jeffmhopkins/Woody/docs/research/2026-09-26-finger-spacing/README.md

# Finger-key spacing — research, 2026-09-26

> **Historical record** (CLAUDE.md §6): what was found on this date, with its
> sources. Not corrected later. The layout it fed is `layout.lh_gaps` /
> `rh_gaps` in `config/body.yaml`.

**Question:** the 11 top keys run in one straight line (LH 5 upper, RH 6
lower), played with the finger pads. The provisional pitch was 24 mm; the
owner says they need to be closer. What do real instruments and hands say?

**Answer:** pad-played instruments put adjacent holes **~20–23 mm** apart
(soprano recorder), adults play down to **16–17 mm** (sopranino), and finger
pad widths put touching fingers **~15–22 mm** apart centre to centre (P5 woman
to P95 man). 24 mm is at the wide end; **19–21 mm** within a hand is the
evidence-backed target, tighter toward ring/little, with the widest gap
between the hands.

## Instrument hole centre spacings (mm)

Recorder numbering: L1–L3 left index/middle/ring, R1–R4 right index/middle/ring/little.
Differences computed from published positions `[calc]`.

| Instrument | L1–L2 | L2–L3 | L3–R1 | R1–R2 | R2–R3 | R3–R4 | Source |
|---|---|---|---|---|---|---|---|
| Sopranino recorder, Haka | 15.7 | 16.8 | 16.7 | 16.5 | 17.0 | 16.8 | [1] |
| Soprano recorder, Wijne (Morgan drawing) | 21.0 | 22.3 | 23.6 | 20.8 | 20.1 | 18.0 | [1] |
| Soprano, Wijne copy a-415 | 21.0 | 23.0 | 22.5 | 22.0 | 20.0 | — | [1] |
| Alto recorder, Bressan "a-" | 28.8 | 34.7 | 39.8 | 31.2 | 30.0 | — | [2] |
| Tin whistle D (Gonzato) | 20 | 20 | 27 | 18 | 26 | — | [3] |
| Whistle C (Gonzato) | 22 | 26 | 24 | 19 | 26 | — | [3] |
| Alto whistle G (Gonzato) | 26 | 30 | 39 | 24 | 36 | — | [3] |
| Boehm flute RH F#–F–E | — | — | — | 28.2 | 29.9 | — | [4] |

Not found: clarinet, alto sax, bagpipe chanter tables; any EWI / Aerophone /
Sylphyo / Travel Sax key pitch (Roland's AE-20/AE-30 spacing article [8] was
403 to the tools — the one real source; open it in a browser). Overall
lengths only: EWI 5000 676 mm [5], EWI USB ~587 mm [6], AE-10 574 mm [7],
Travel Sax 2 230 mm [9].

## Finger breadth (mm), Greiner 1991 US Army [12]

P5/P95 computed as mean ± 1.645 SD `[calc]`. DIP ≈ at the pad.

| | Women P5 / P50 / P95 | Men P5 / P50 / P95 |
|---|---|---|
| Index PIP | 17.8 / 19.9 / 22.0 | 20.4 / 23.0 / 25.6 |
| Index DIP | 15.3 / 17.3 / 19.3 | 17.6 / 20.1 / 22.6 |
| Middle DIP | 15.3 / 17.1 / 18.9 | 17.5 / 19.8 / 22.1 |
| Ring DIP | 14.0 / 15.8 / 17.6 | 16.2 / 18.5 / 20.8 |
| Little DIP | 12.9 / 14.7 / 16.5 | 15.3 / 17.4 / 19.5 |

Cross-check: FAA index PIP breadth men 19/21/23, women 16/18/21 [13]; hand
breadth men 84/90/98, women 73/79/86 [14]. Touching pads, centre to centre =
(w1 + w2)/2 `[calc]`: index–middle 15.3 (P5 F) … 22.4 (P95 M); ring–little
13.5 … 20.2. **Relaxed, curved fingertip spacing is unmeasured** in anything
found (Garrett AMRL-TR-69-42 may have it; DTIC 403).

## Makers' guidance

- Yamaha: holes are "not at regular intervals… the space between holes covered by the middle finger and the ring finger is also minimized" [15].
- Von Huene ergonomic recorders add keys to reduce the first-to-last spread and the right index–middle spacing [16].
- The gap between the hands is usually the largest; the right hand's little-finger hole is usually the tightest, and makers offset little/ring holes sideways rather than stretch them — which a single straight line cannot do, so there the pitch must shrink instead.

## Sources

1. Bouterse, FoMRHI Comm. 2115 — https://www.fomrhi.org/uploads/bulletins/Fomrhi-146/Comm%202115.pdf
2. Bouterse, FoMRHI Comm. 1929 Table 3 — https://www.fomrhi.org/uploads/bulletins/Fomrhi-118/Comm%201929.pdf
3. Gonzato, The Low-Tech Whistle pp. 11–13 — https://www.flutopedia.com/refs/Gonzato_2015_LowTechWhistle.pdf
4. Boehm scale — https://www.rwdobson.com/scales/boehm.html
5. https://www.thomannmusic.com/akai_professional_ewi_5000.htm
6. https://www.manualslib.com/manual/207345/Akai-Ewi-Usb.html?page=29 (search summary only)
7. https://www.roland.com/us/products/aerophone_ae-10/specifications/
8. https://support.roland.com/hc/en-us/articles/4414507338139 (403)
9. https://odiseimusic.com/en-us/pages/travel-sax
10. https://downloads.aodyo.com/sylphyo/sylphyo-userguide-en.pdf
11. http://www.mjbauer.biz/Build_the_REMI_mk2.htm
12. Greiner 1991 — https://archive.org/details/DTIC_ADA244533
13. FAA HFDS App. B — https://hf.tc.faa.gov/hfds/download-hfds/hfds_pdfs/App_B_Tech_Ops_Anthropometrics.pdf
14. FAA HFDS Ch. 14 — https://hf.tc.faa.gov/hfds/download-hfds/hfds_pdfs/Ch14_Anthropometry_and_biomechanics_Oct2009.pdf
15. https://www.yamaha.com/en/musical_instrument_guide/recorder/mechanism/mechanism002.html
16. https://www.vonhuene.com/c-49-ergonomic-or-comfort.aspx
17. https://recorderforum.com/forum/topic/distance-between-holes-plastic-altos/

Gathered by a research agent; figures are as reported with the URL beside
them and were not re-fetched by hand.
