jeffmhopkins/Woody/hardware/cluster/key-switch-network/notes.md

# Key switch network — decision history

**Past tense only.** Every live value lives in `key-switch-network.md`,
[`../cluster-boards.md`](../cluster-boards.md) or `hardware/bom.csv`. If a
number here is still true, it is in the wrong file.

This is the circuit's superseded shelf, on the convention
[`../../module/pitch-stage/notes.md`](../../module/pitch-stage/notes.md) sets.
Nothing is deleted from it: a deleted superseded value stops warning the next
person.

---

## Why `R-KEY-PU` became 2.2 kΩ — moved from the BOM row, 2026-09-26

*Moved out of the `R-KEY-PU` notes cell under CLAUDE.md's cut line: a BOM
cell tells a builder what to do, and this is what someone used to think.*
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
