jeffmhopkins/Woody/branding/export/png/scs-mark-black.png

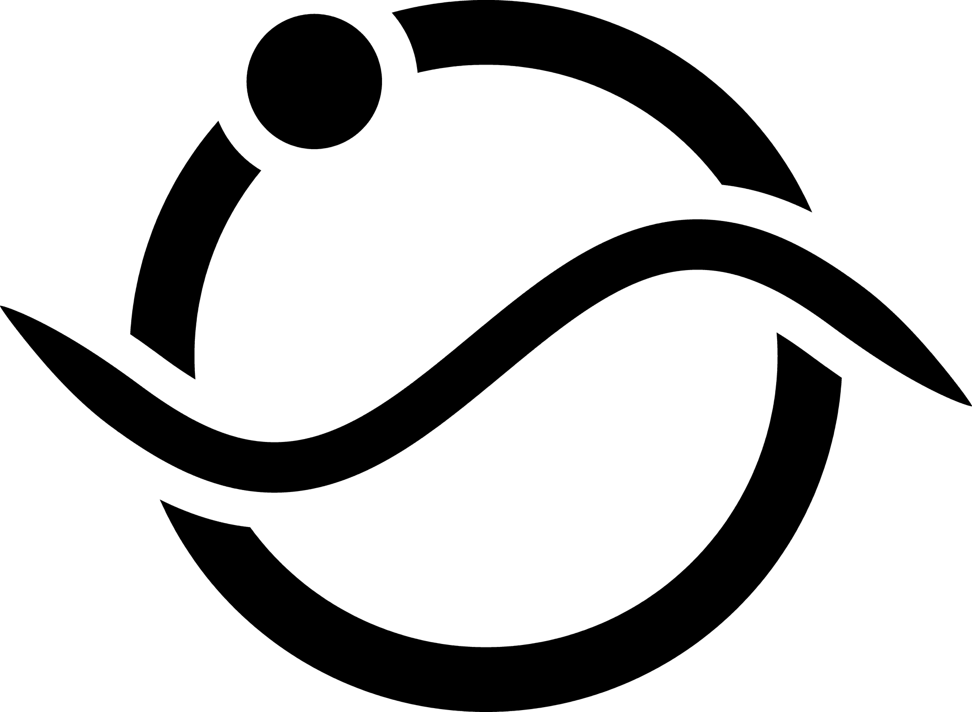
branding/export/png/scs-mark-black.png
