jeffmhopkins/Woody/branding/export/png/scs-mark-white.png

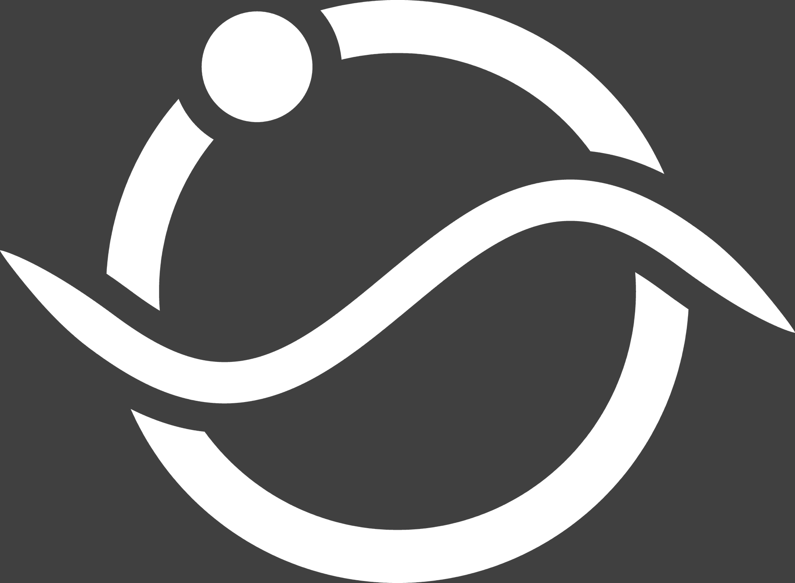
branding/export/png/scs-mark-white.png
