jeffmhopkins/Woody/branding/export/renders/scs-mark-epoxy-on-dark-oak.png

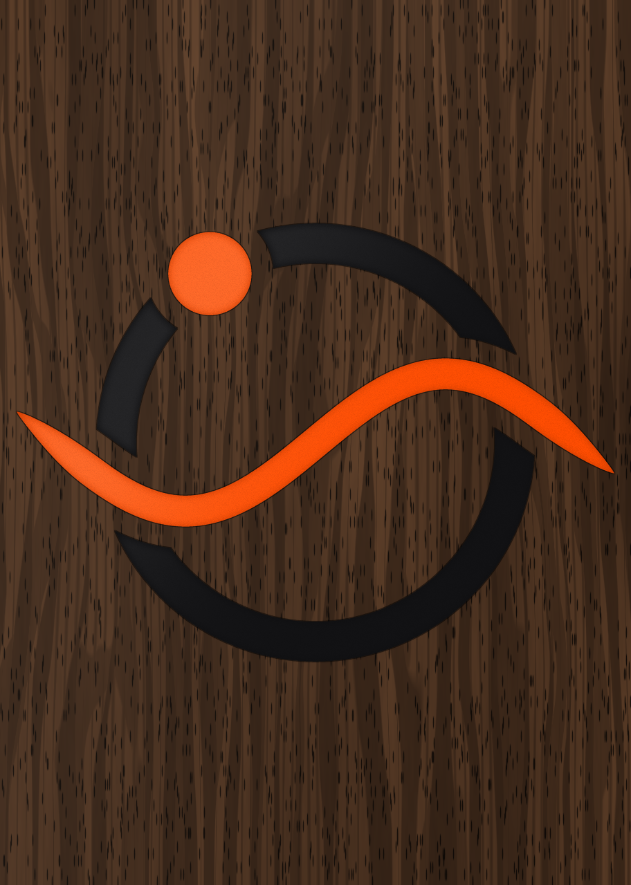
branding/export/renders/scs-mark-epoxy-on-dark-oak.png
