jeffmhopkins/Woody/branding/export/renders/scs-mark-epoxy-on-dark-walnut.png

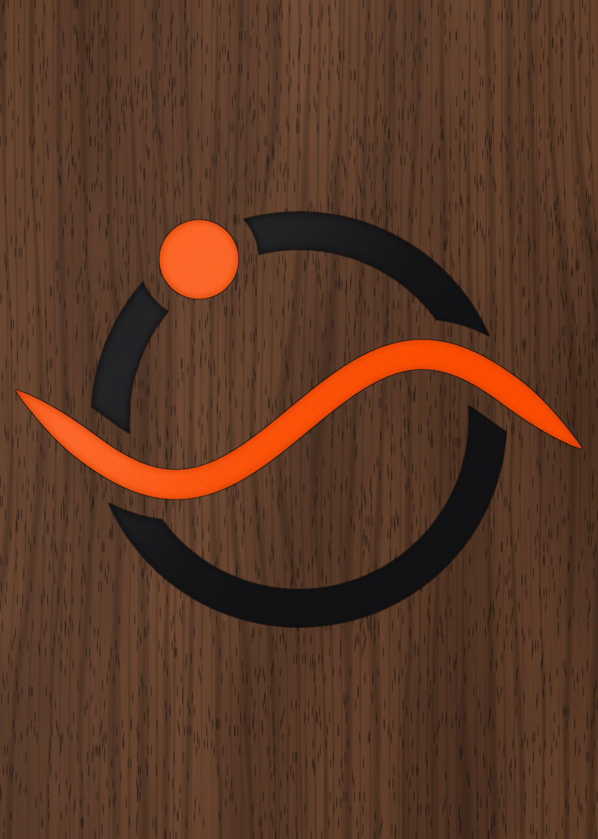
branding/export/renders/scs-mark-epoxy-on-dark-walnut.png
