jeffmhopkins/Woody/branding/export/renders/scs-mark-on-bocote.png

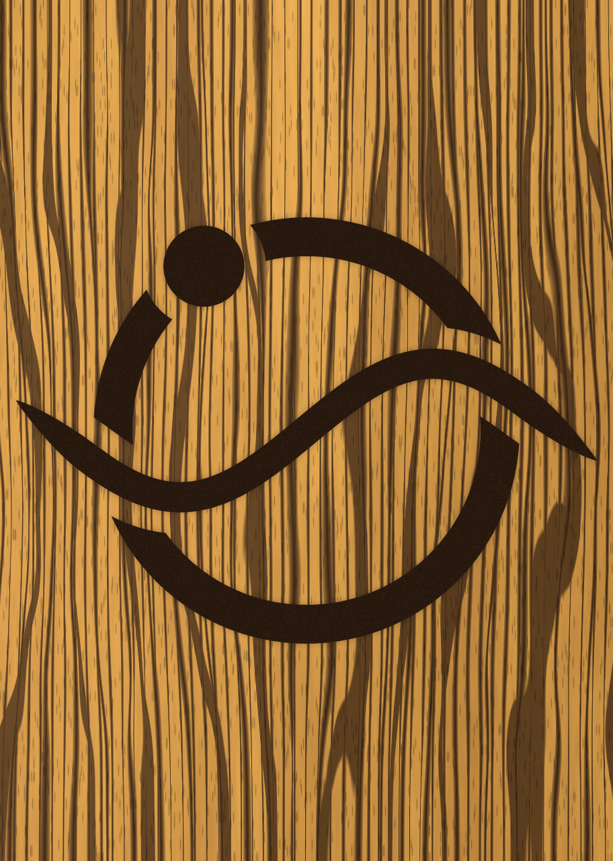
branding/export/renders/scs-mark-on-bocote.png
