jeffmhopkins/Woody/branding/export/renders/scs-mark-on-dark-walnut.png

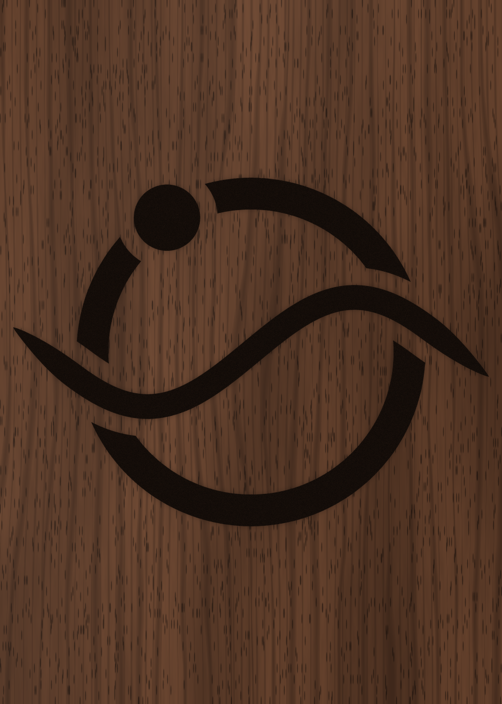
branding/export/renders/scs-mark-on-dark-walnut.png
