jeffmhopkins/Woody/datasheets/mechanical/BEEKEEB-MT165-THCS-UNDERSIDE-COMPARISON.jpg

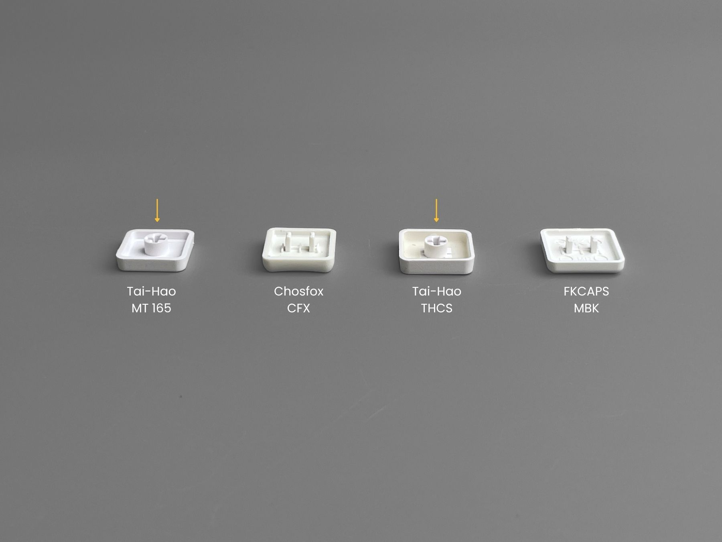
datasheets/mechanical/BEEKEEB-MT165-THCS-UNDERSIDE-COMPARISON.jpg
