jeffmhopkins/Woody/datasheets/mechanical/DOEPFER-A100-BUS-CONNECTORS-a100b_e.gif

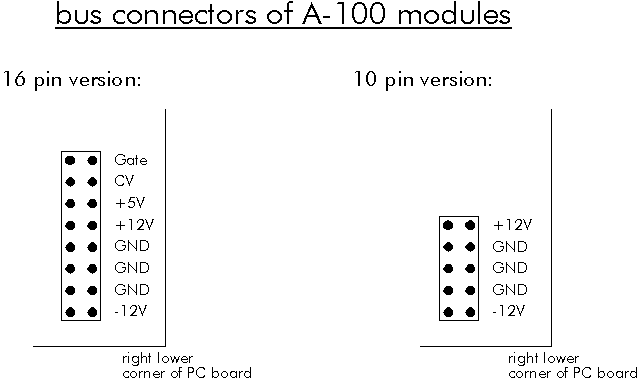
datasheets/mechanical/DOEPFER-A100-BUS-CONNECTORS-a100b_e.gif
