jeffmhopkins/Woody/datasheets/mechanical/DOEPFER-A100-FRONT-PANEL-HOLE-SKETCH-A100FP.gif

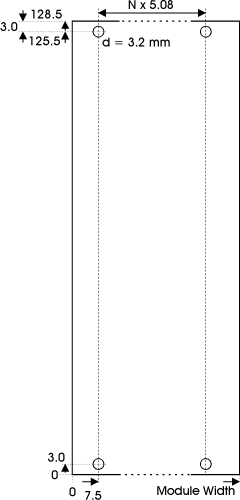
datasheets/mechanical/DOEPFER-A100-FRONT-PANEL-HOLE-SKETCH-A100FP.gif
