jeffmhopkins/Woody/datasheets/mechanical/ETTINGER-005.52.033-DRAWING.jpg

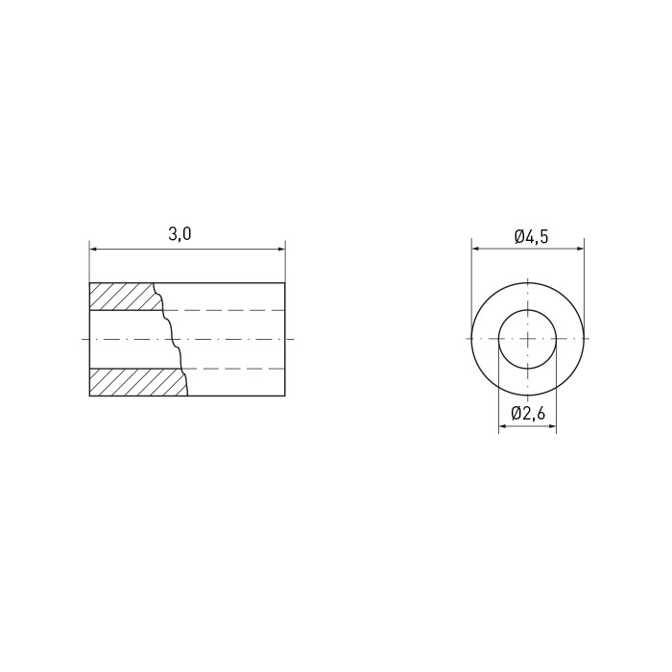
datasheets/mechanical/ETTINGER-005.52.033-DRAWING.jpg
