jeffmhopkins/Woody/datasheets/mechanical/ETTINGER-005.52.033-PHOTO-GENERIC.png

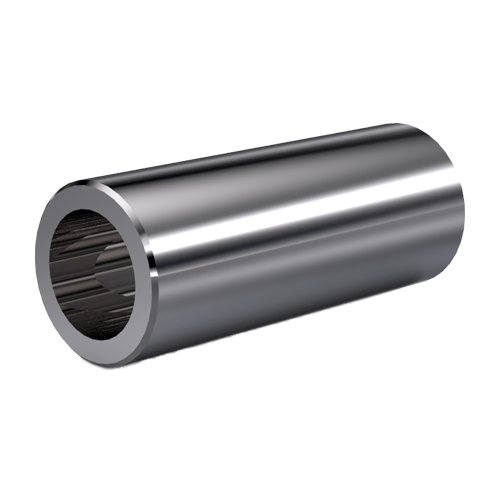
datasheets/mechanical/ETTINGER-005.52.033-PHOTO-GENERIC.png
