jeffmhopkins/Woody/datasheets/mechanical/TAIHAO-MT165-MX-STEM-SPEC-CARD.jpg

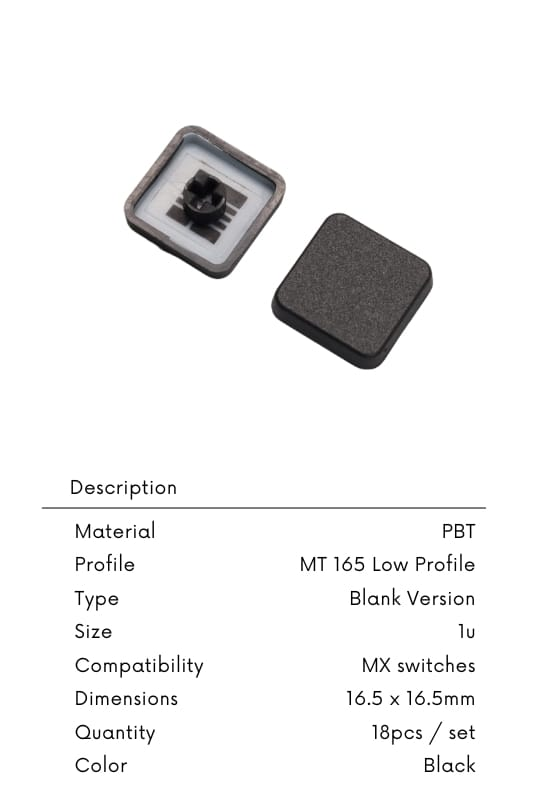
datasheets/mechanical/TAIHAO-MT165-MX-STEM-SPEC-CARD.jpg
