jeffmhopkins/Woody/datasheets/mechanical/WAVESHARE-ESP32-S3-MATRIX-dimensions.jpg

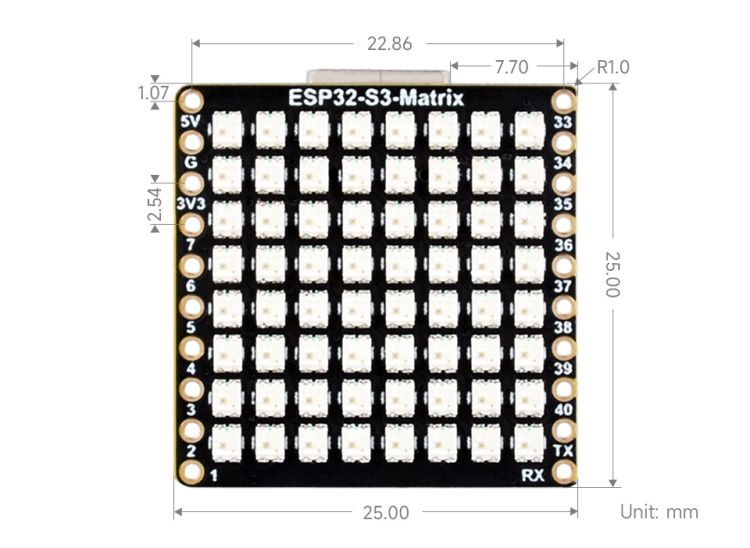
datasheets/mechanical/WAVESHARE-ESP32-S3-MATRIX-dimensions.jpg
