jeffmhopkins/Woody/datasheets/mechanical/WAVESHARE-ESP32-S3-MATRIX-function-block.png

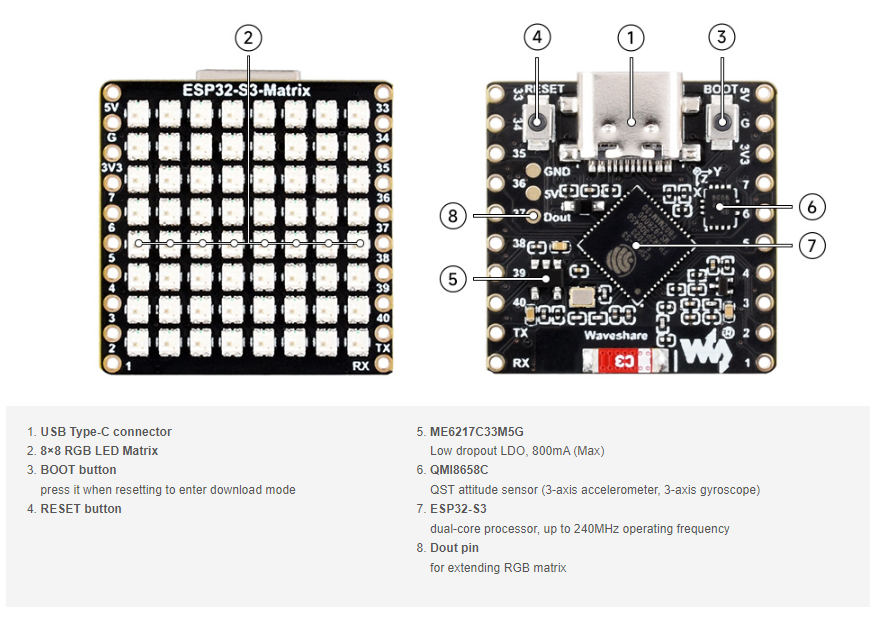
datasheets/mechanical/WAVESHARE-ESP32-S3-MATRIX-function-block.png
