jeffmhopkins/Woody/hardware/boards/key-board-lh/key-board-lh.p2.sch.png

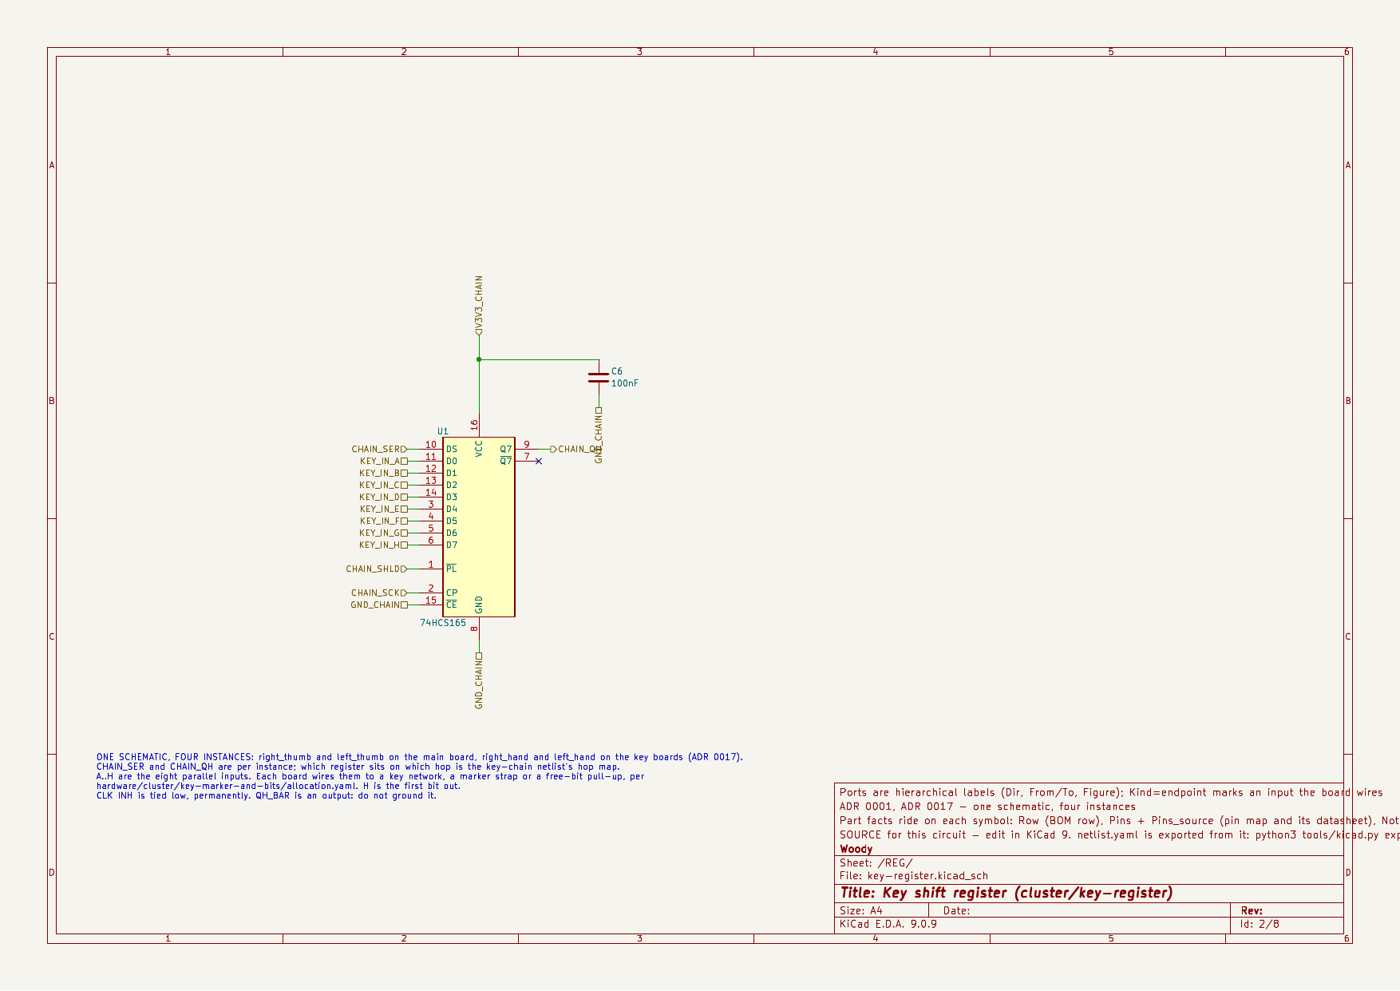
hardware/boards/key-board-lh/key-board-lh.p2.sch.png
