jeffmhopkins/Woody/hardware/boards/key-board-lh/key-board-lh.p3.sch.png

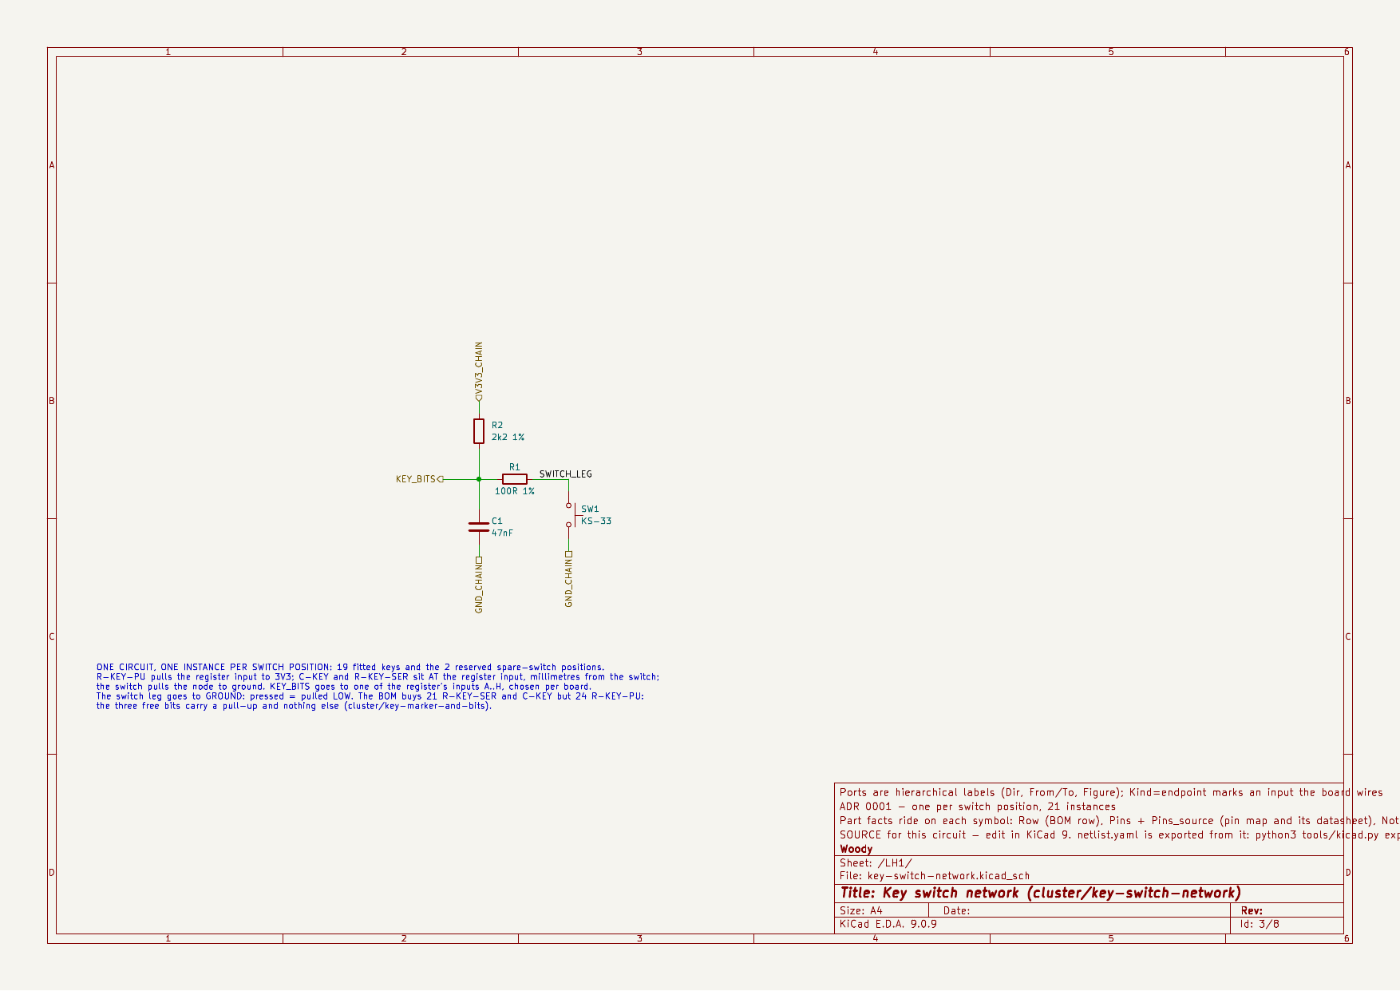
hardware/boards/key-board-lh/key-board-lh.p3.sch.png
