jeffmhopkins/Woody/hardware/boards/key-board-lh/key-board-lh.p8.sch.png

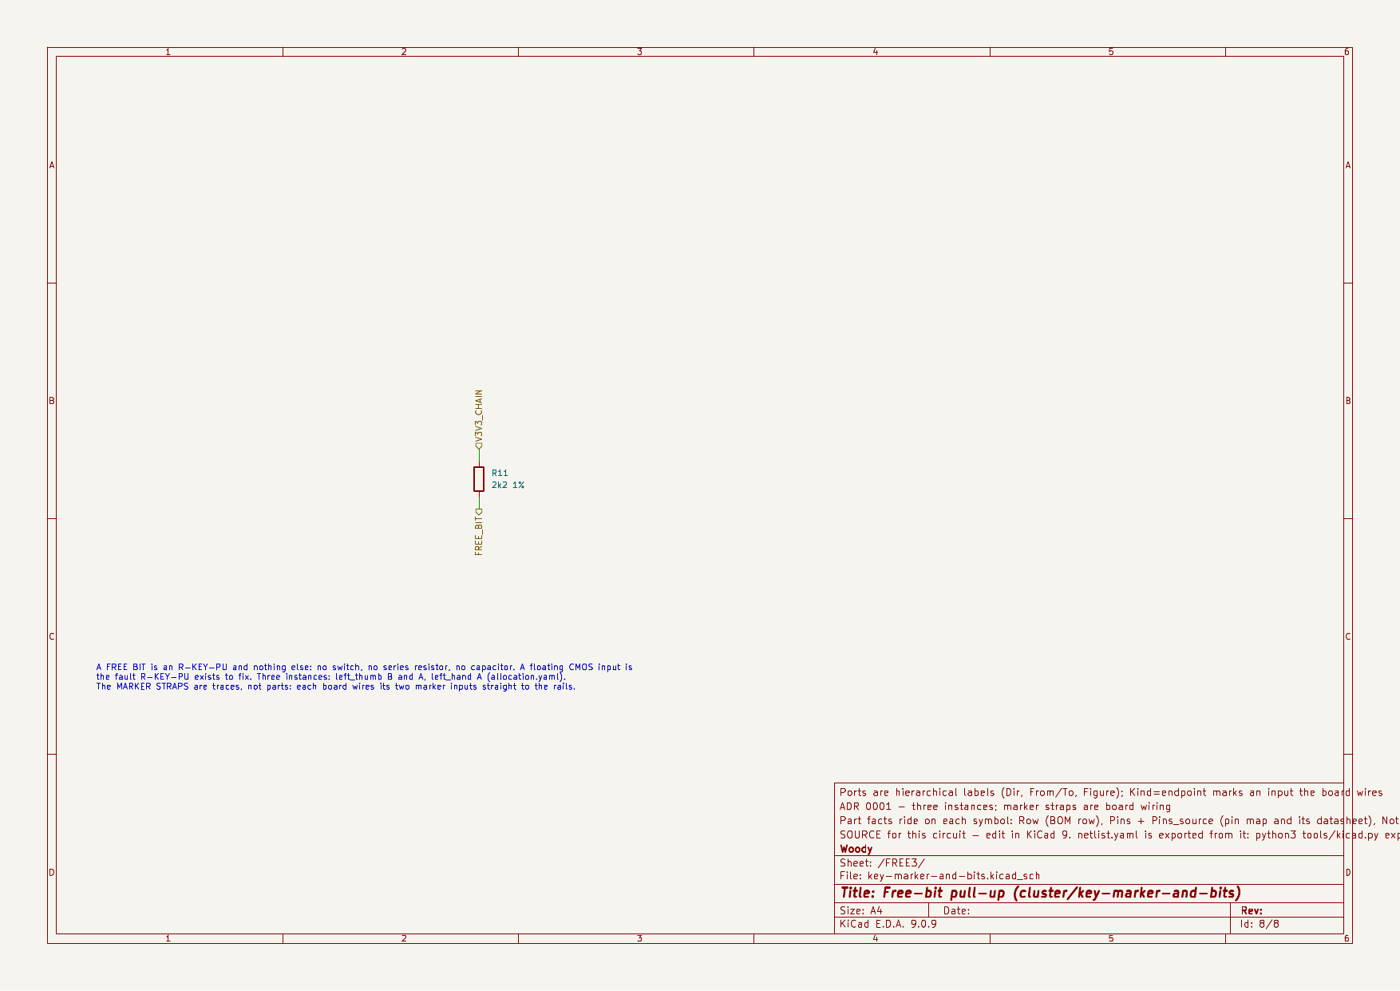
hardware/boards/key-board-lh/key-board-lh.p8.sch.png
