jeffmhopkins/Woody/hardware/boards/key-board-lh/key-board-lh.pcb-3d-bottom.png

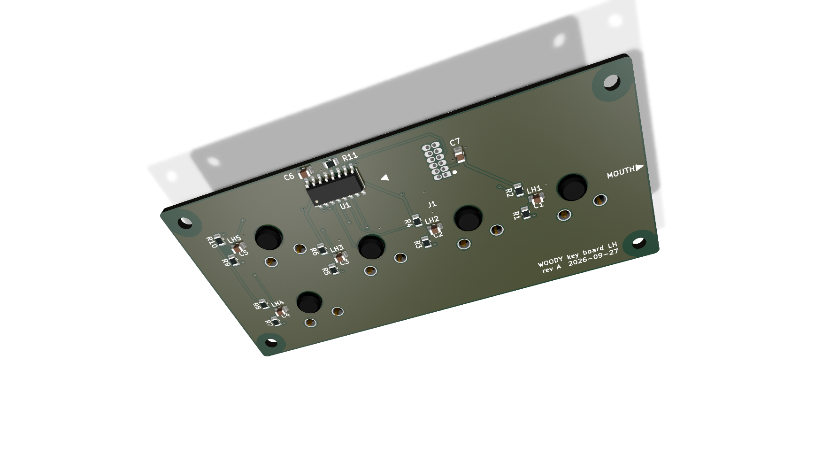
hardware/boards/key-board-lh/key-board-lh.pcb-3d-bottom.png
