jeffmhopkins/Woody/hardware/boards/key-board-lh/key-board-lh.pcb-3d-top.png

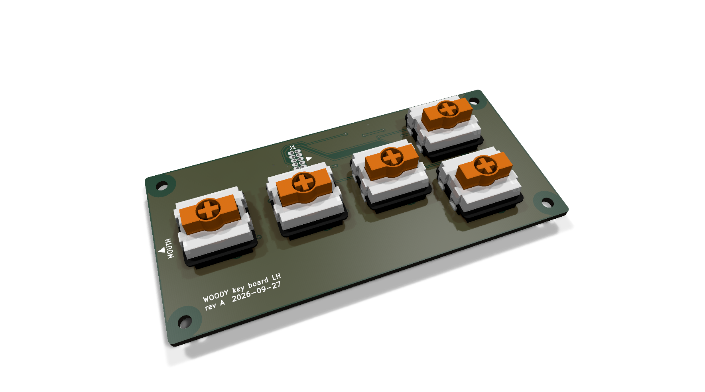
hardware/boards/key-board-lh/key-board-lh.pcb-3d-top.png
