jeffmhopkins/Woody/hardware/boards/key-board-lh/key-board-lh.pcb-copper-bottom.png

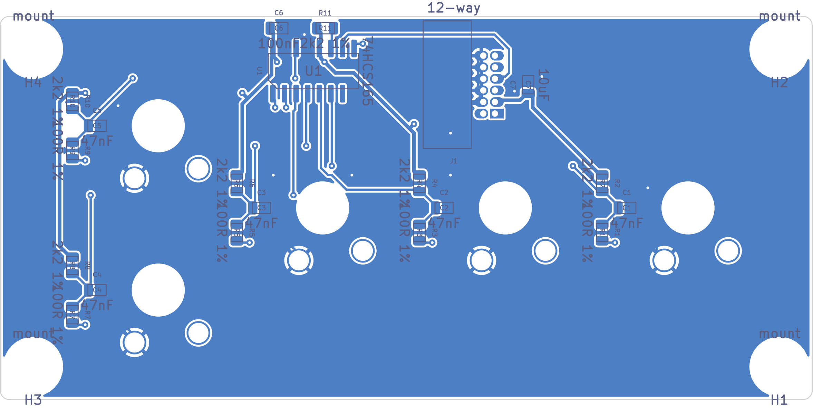
hardware/boards/key-board-lh/key-board-lh.pcb-copper-bottom.png
