jeffmhopkins/Woody/hardware/boards/key-board-lh/key-board-lh.pcb-copper-top.png

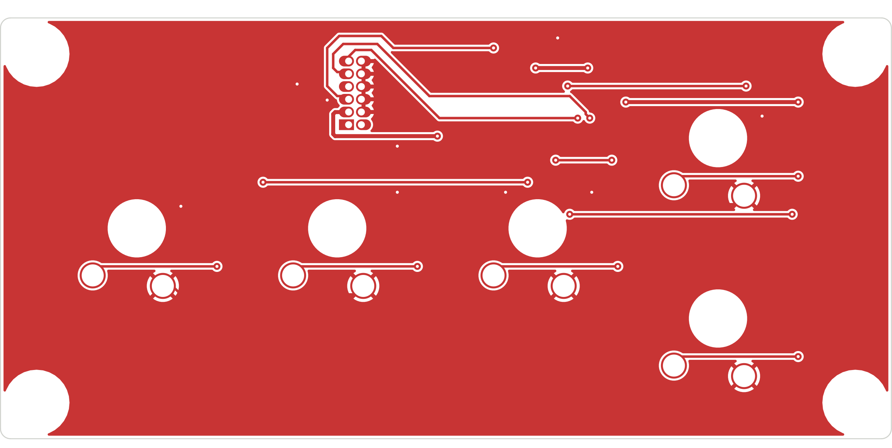
hardware/boards/key-board-lh/key-board-lh.pcb-copper-top.png
