jeffmhopkins/Woody/hardware/boards/key-board-lh/key-board-lh.pcb-plan-bottom.png

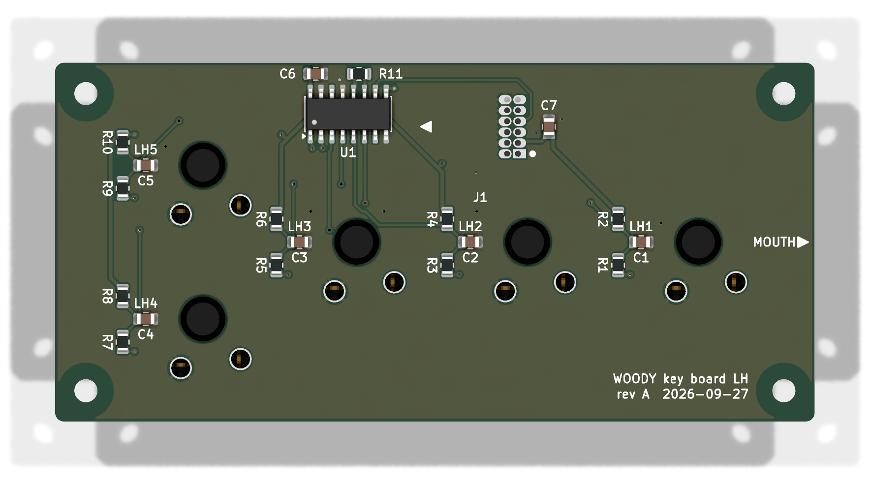
hardware/boards/key-board-lh/key-board-lh.pcb-plan-bottom.png
