jeffmhopkins/Woody/hardware/boards/key-board-lh/key-board-lh.pcb-plan-top.png

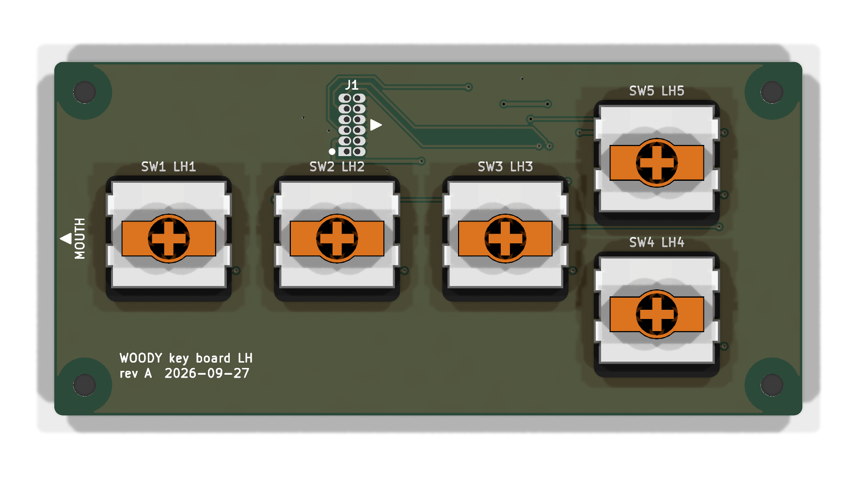
hardware/boards/key-board-lh/key-board-lh.pcb-plan-top.png
