jeffmhopkins/Woody/hardware/boards/key-board-lh/key-board-lh.sch.png

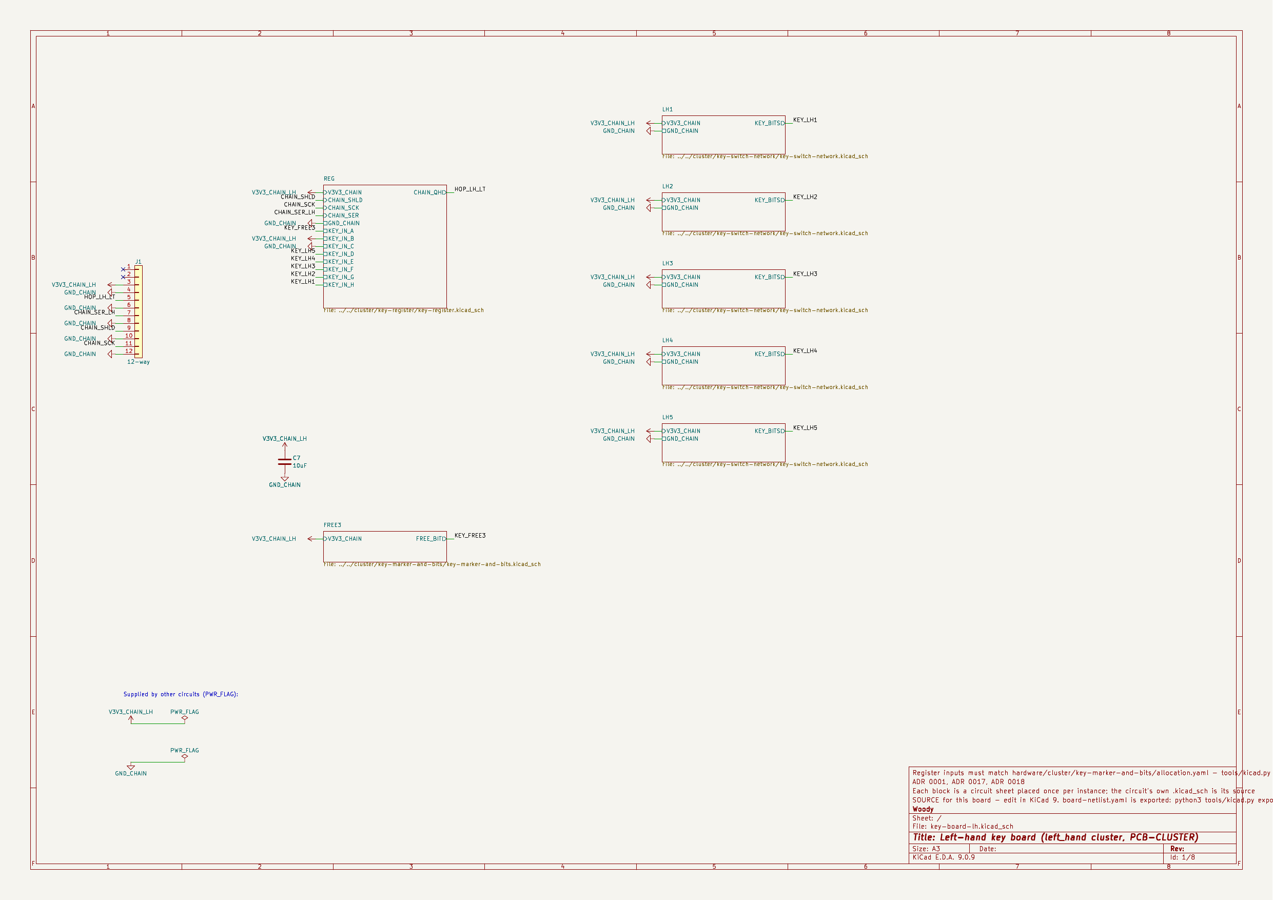
hardware/boards/key-board-lh/key-board-lh.sch.png
