jeffmhopkins/Woody/hardware/boards/key-board-rh/key-board-rh.pcb-3d-top.png

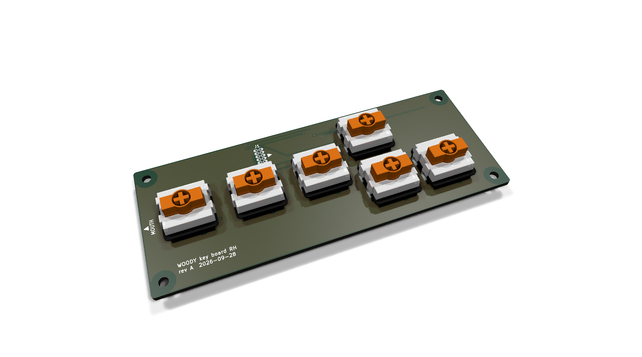
hardware/boards/key-board-rh/key-board-rh.pcb-3d-top.png
