jeffmhopkins/Woody/hardware/boards/key-board-rh/key-board-rh.pcb-copper-bottom.png

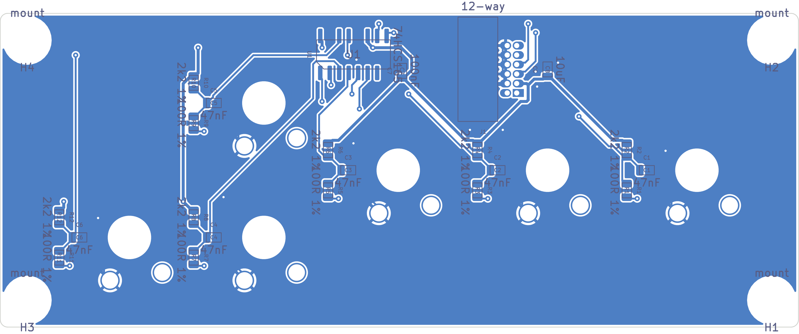
hardware/boards/key-board-rh/key-board-rh.pcb-copper-bottom.png
