jeffmhopkins/Woody/hardware/boards/key-board-rh/key-board-rh.pcb-copper-top.png

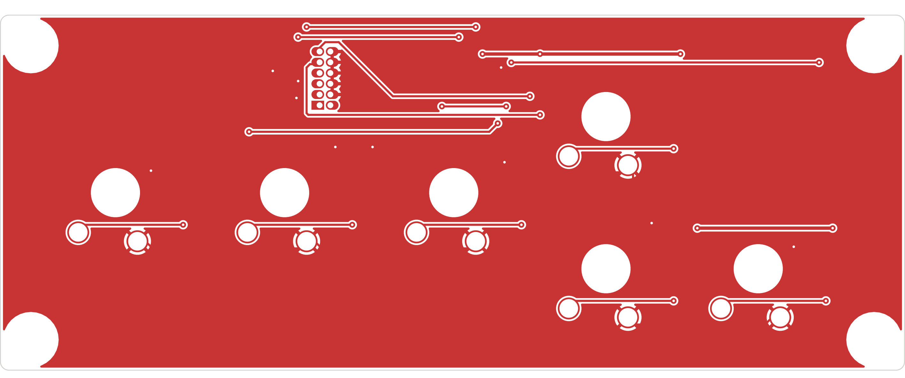
hardware/boards/key-board-rh/key-board-rh.pcb-copper-top.png
