jeffmhopkins/Woody/hardware/boards/key-board-rh/key-board-rh.pcb-plan-bottom.png

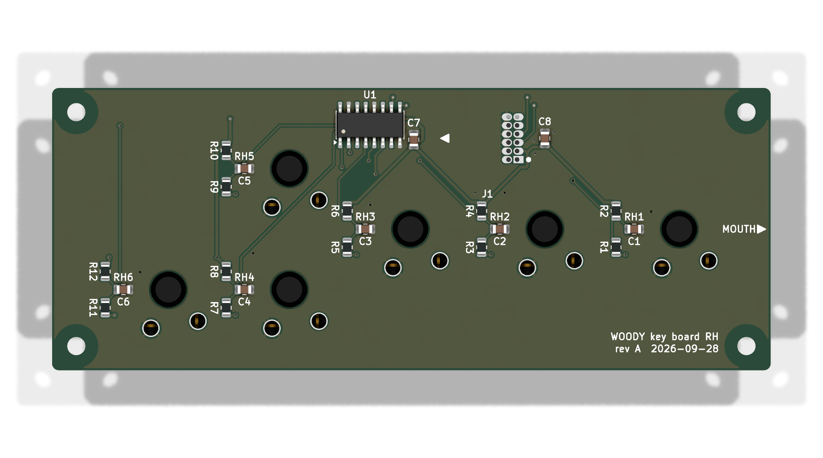
hardware/boards/key-board-rh/key-board-rh.pcb-plan-bottom.png
