jeffmhopkins/Woody/hardware/boards/key-board-rh/key-board-rh.pcb-plan-top.png

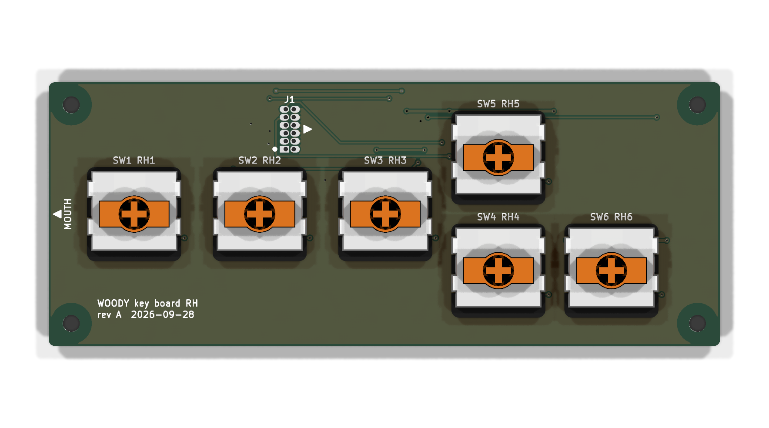
hardware/boards/key-board-rh/key-board-rh.pcb-plan-top.png
