jeffmhopkins/Woody/hardware/boards/main-board/main-board.p2.sch.png

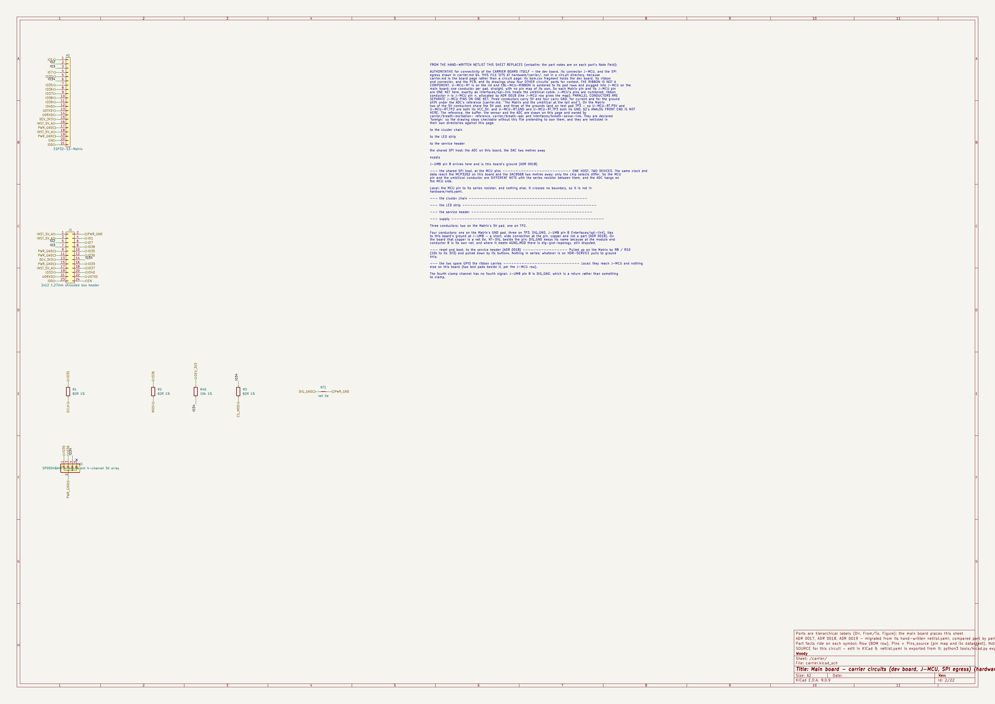
hardware/boards/main-board/main-board.p2.sch.png
