jeffmhopkins/Woody/hardware/boards/main-board/main-board.p3.sch.png

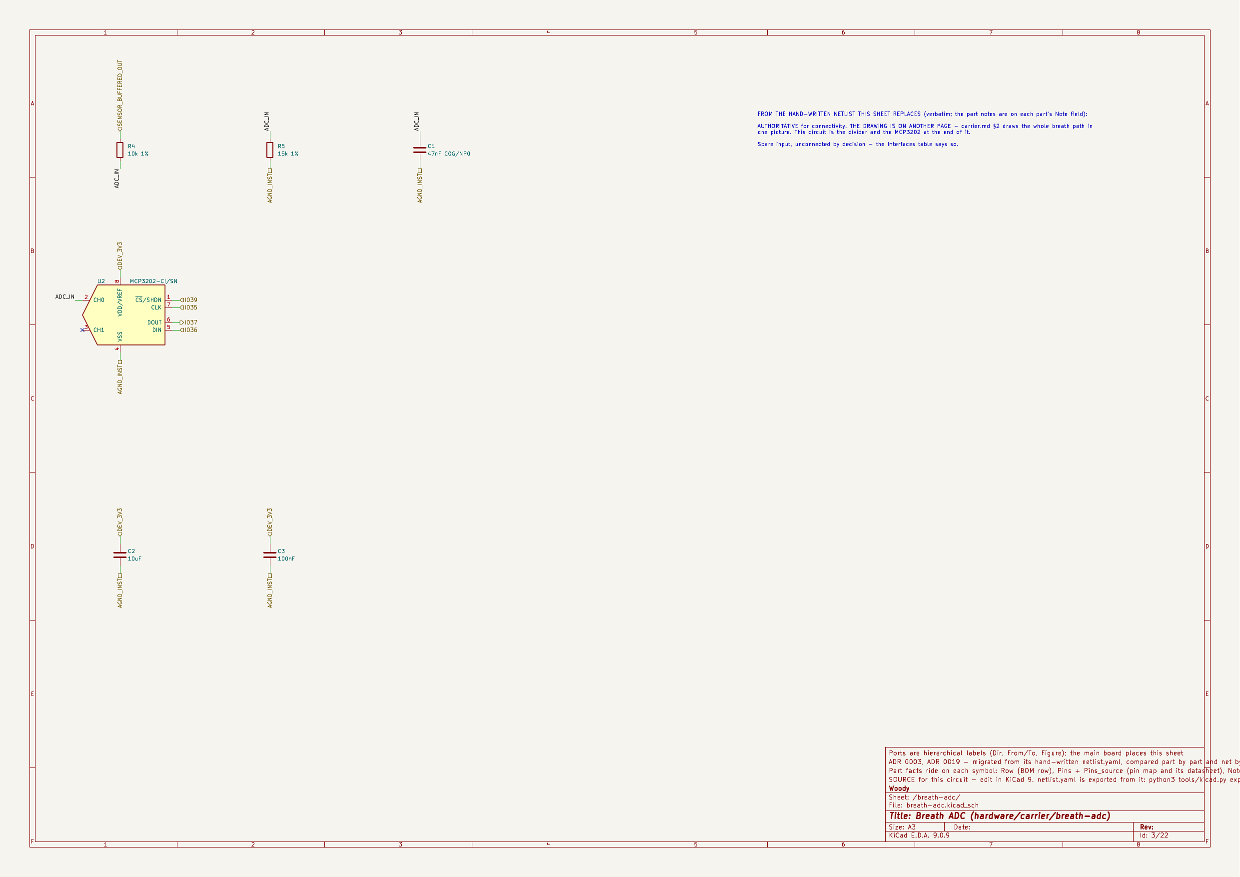
hardware/boards/main-board/main-board.p3.sch.png
