jeffmhopkins/Woody/hardware/boards/main-board/main-board.p4.sch.png

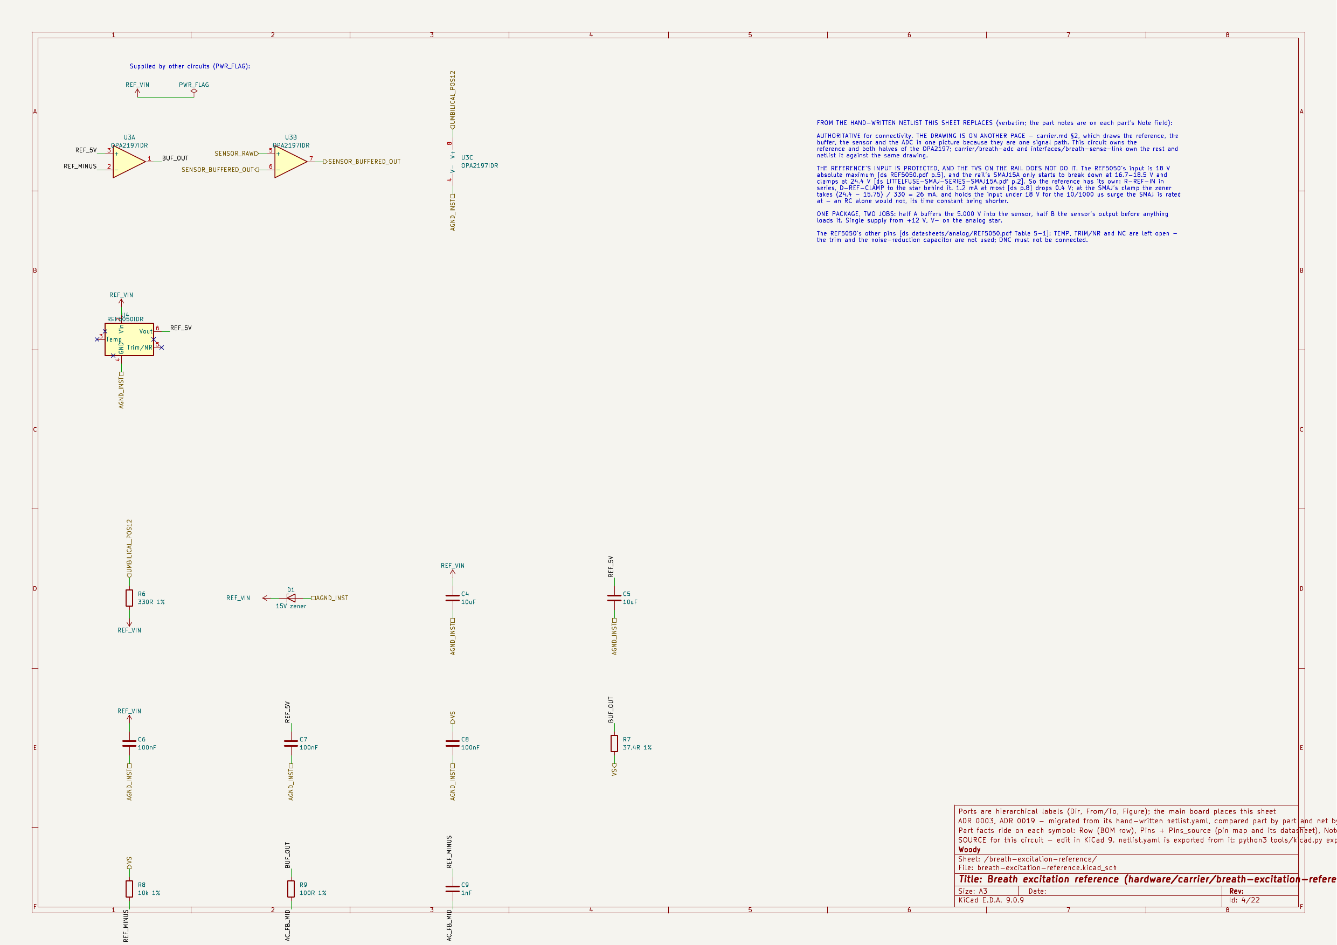
hardware/boards/main-board/main-board.p4.sch.png
