jeffmhopkins/Woody/hardware/boards/main-board/main-board.p5.sch.png

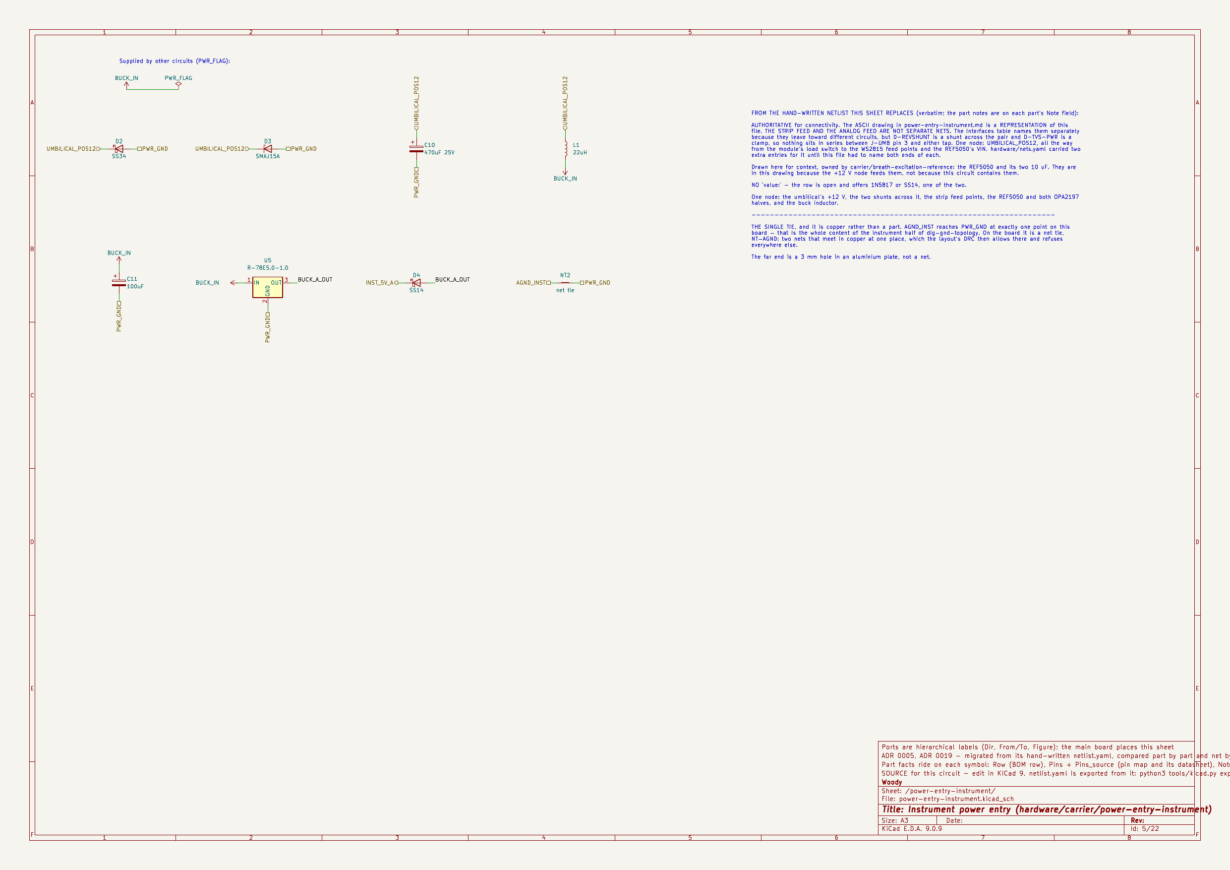
hardware/boards/main-board/main-board.p5.sch.png
