jeffmhopkins/Woody/hardware/boards/main-board/main-board.p6.sch.png

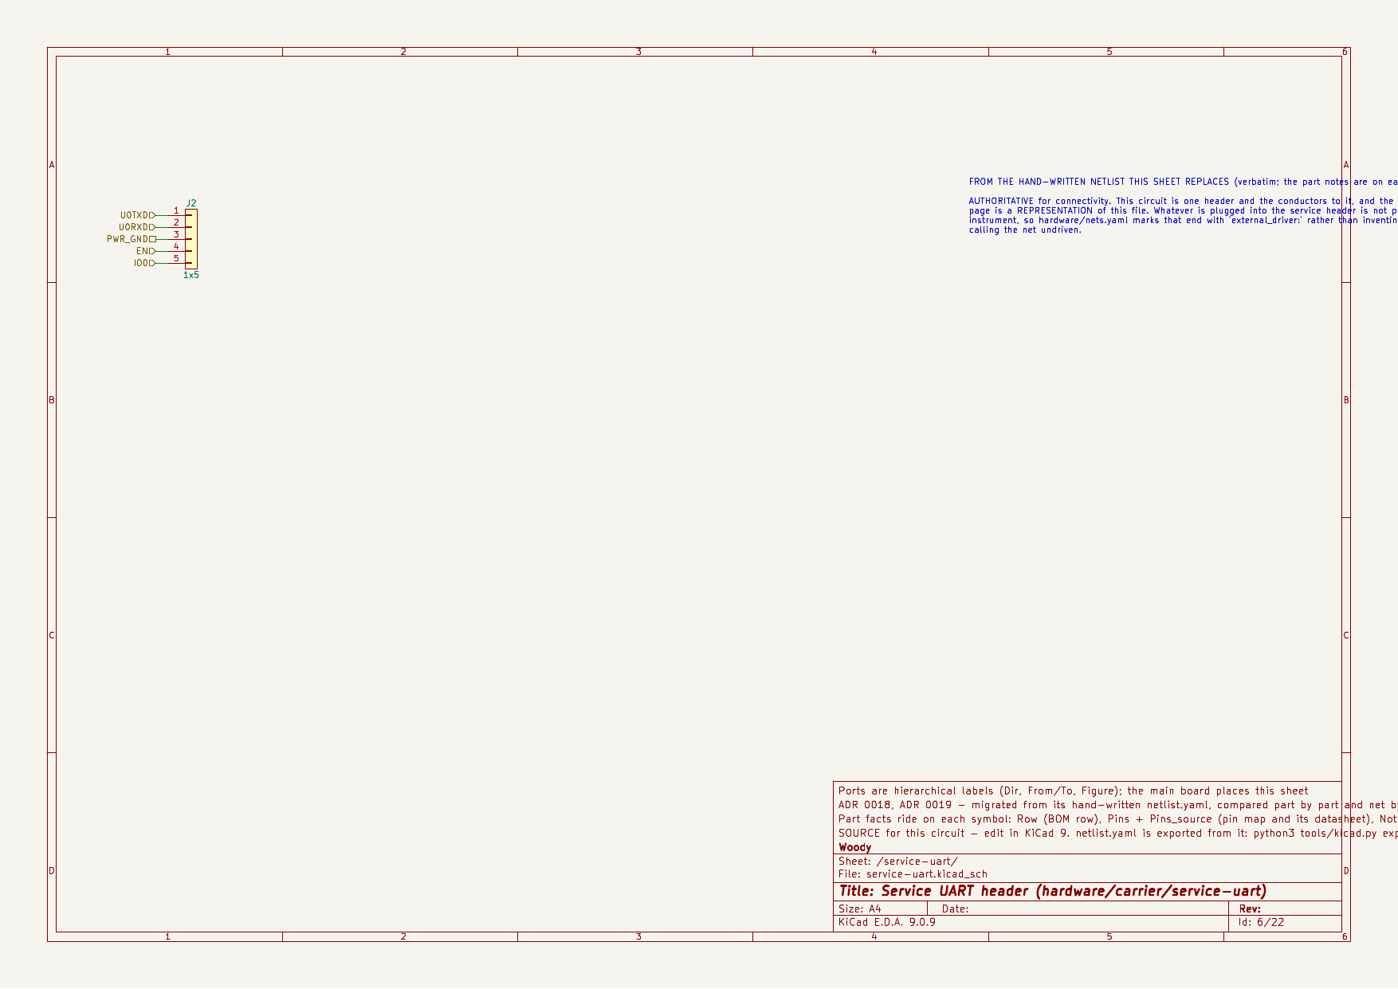
hardware/boards/main-board/main-board.p6.sch.png
