jeffmhopkins/Woody/hardware/boards/main-board/main-board.p7.sch.png

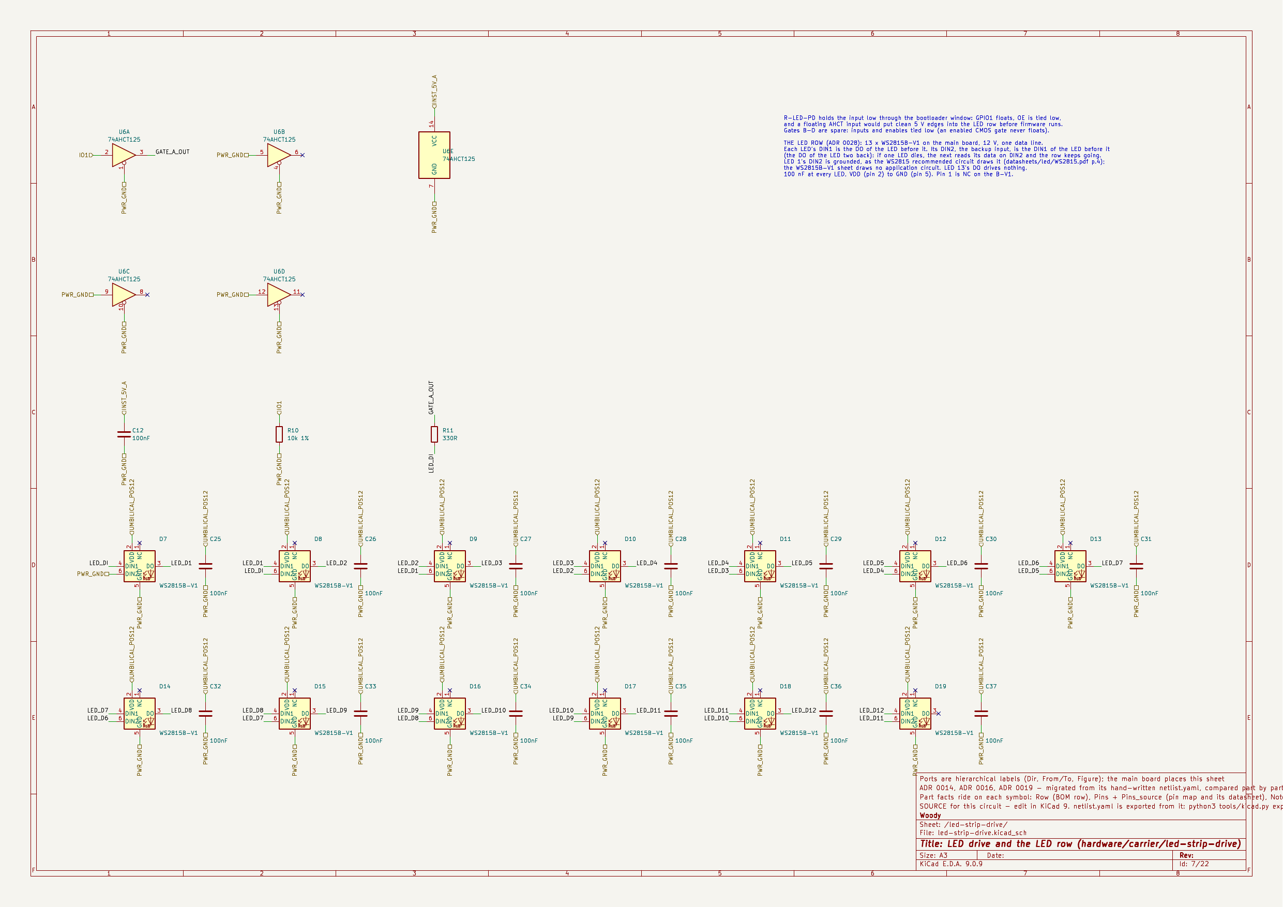
hardware/boards/main-board/main-board.p7.sch.png
