jeffmhopkins/Woody/hardware/boards/main-board/main-board.p22.sch.png

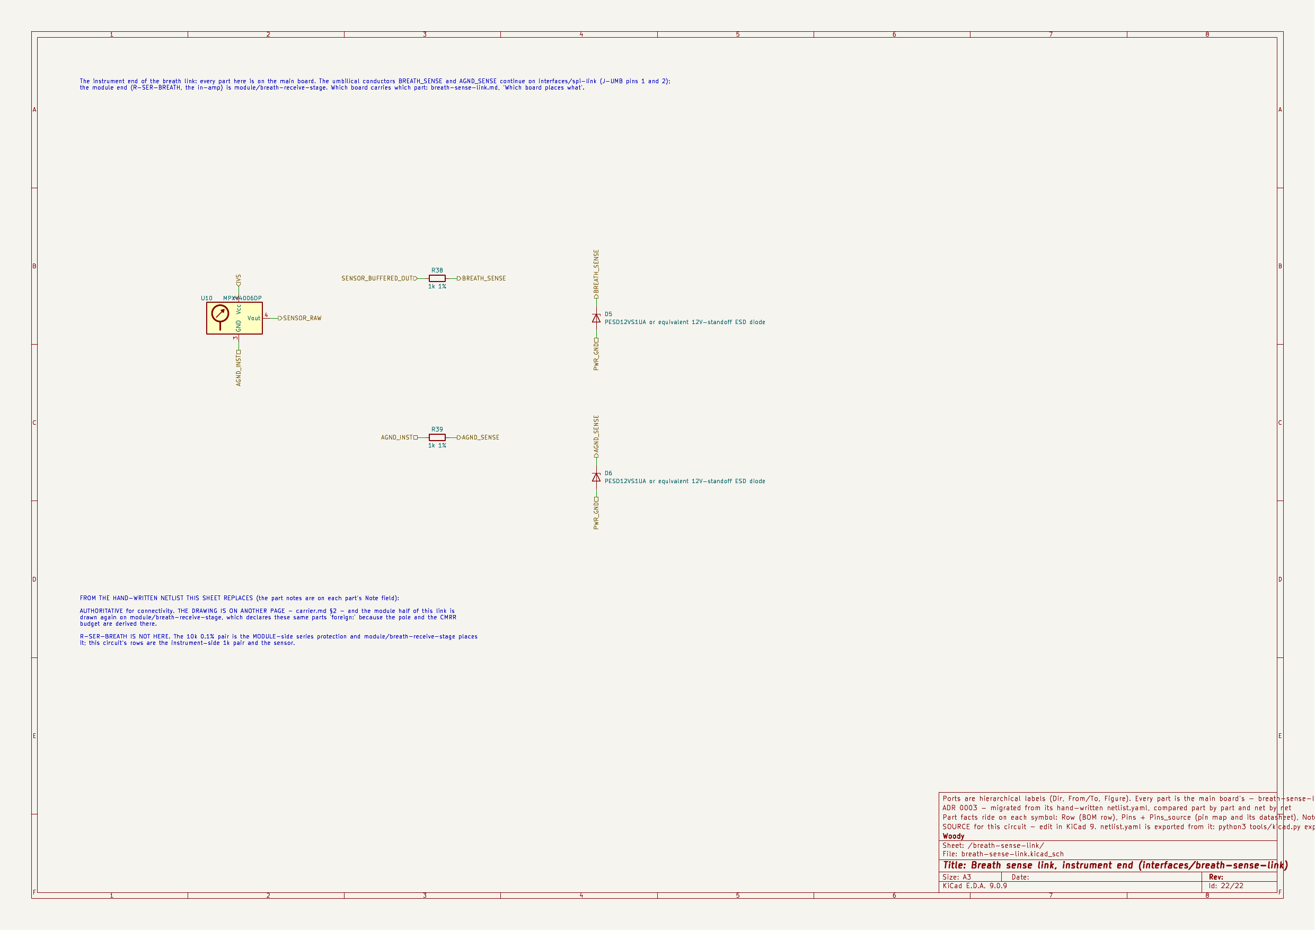
hardware/boards/main-board/main-board.p22.sch.png
