jeffmhopkins/Woody/hardware/boards/main-board/main-board.sch.png

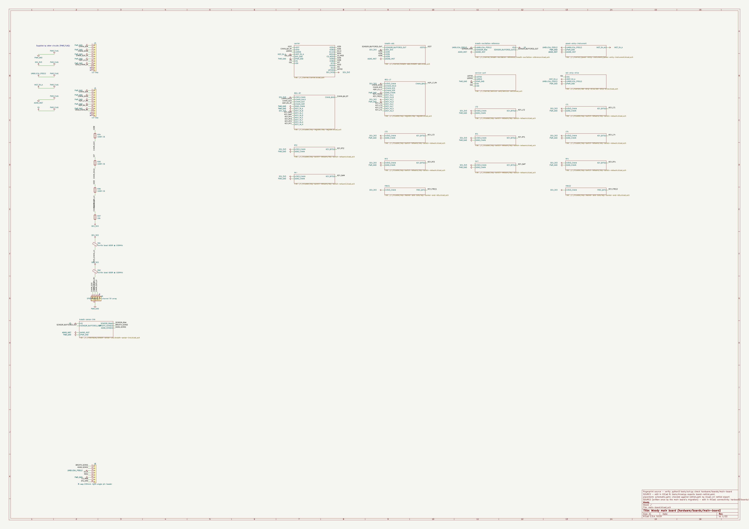
hardware/boards/main-board/main-board.sch.png
