jeffmhopkins/Woody/hardware/boards/module-jack/module-jack.p2.sch.png

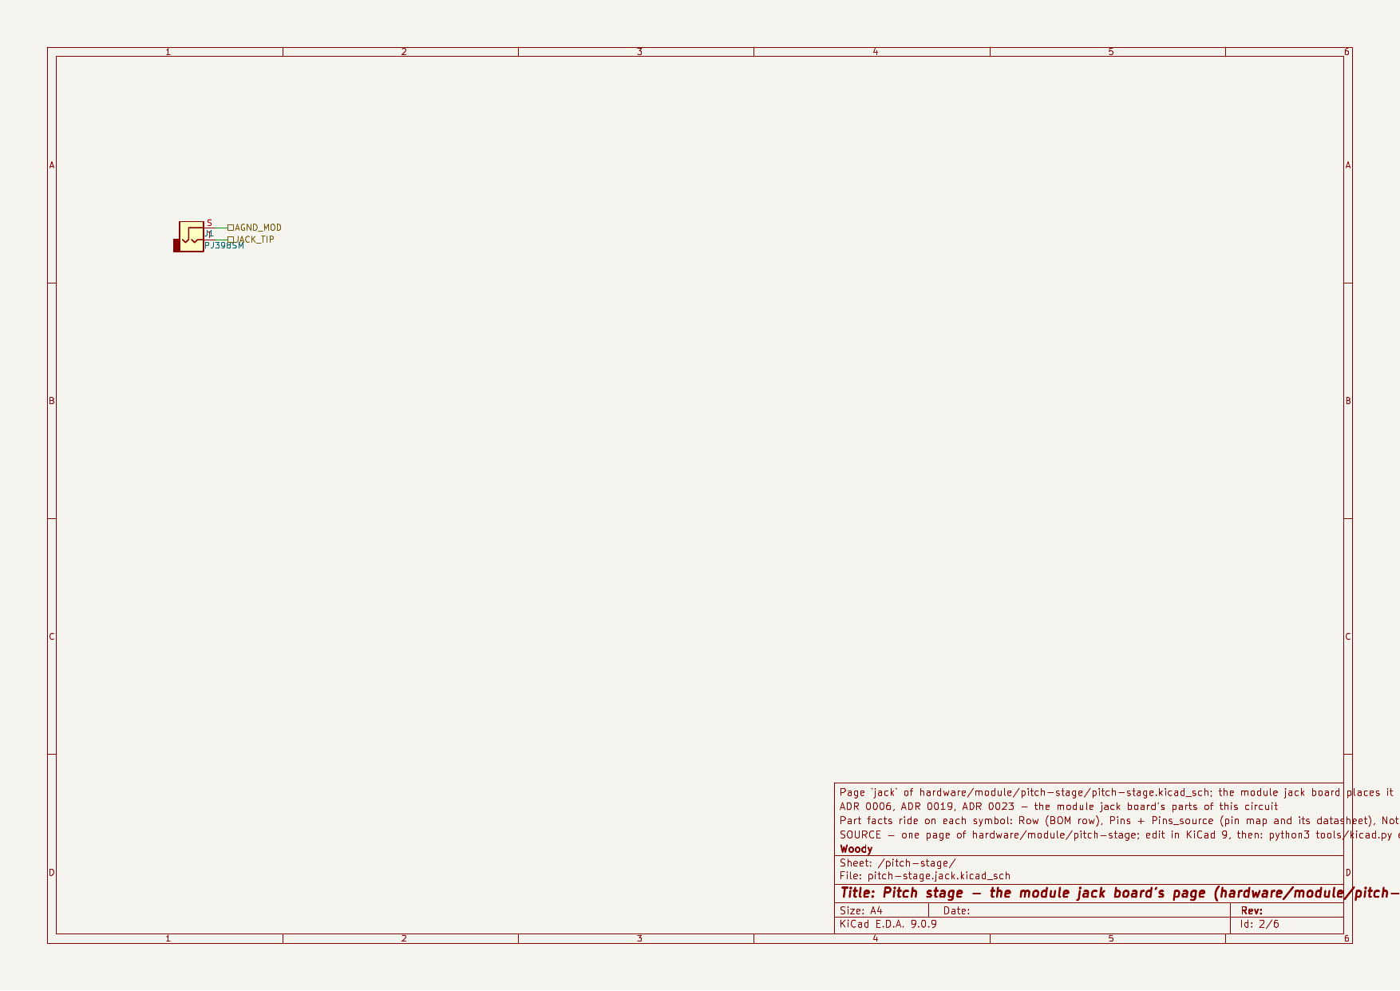
hardware/boards/module-jack/module-jack.p2.sch.png
