jeffmhopkins/Woody/hardware/boards/module-jack/module-jack.p3.sch.png

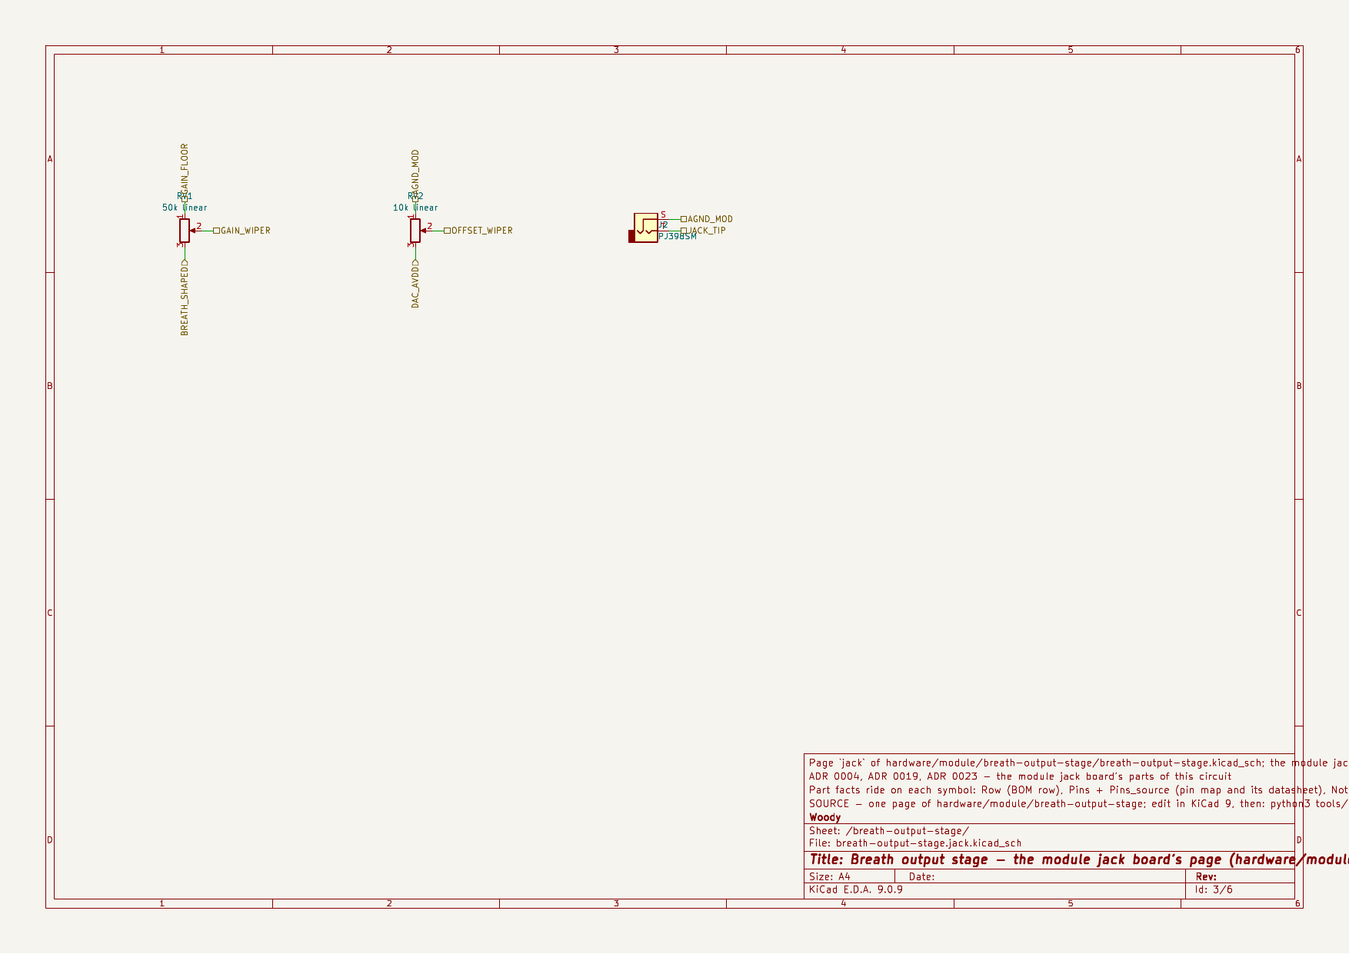
hardware/boards/module-jack/module-jack.p3.sch.png
