jeffmhopkins/Woody/hardware/boards/module-jack/module-jack.p5.sch.png

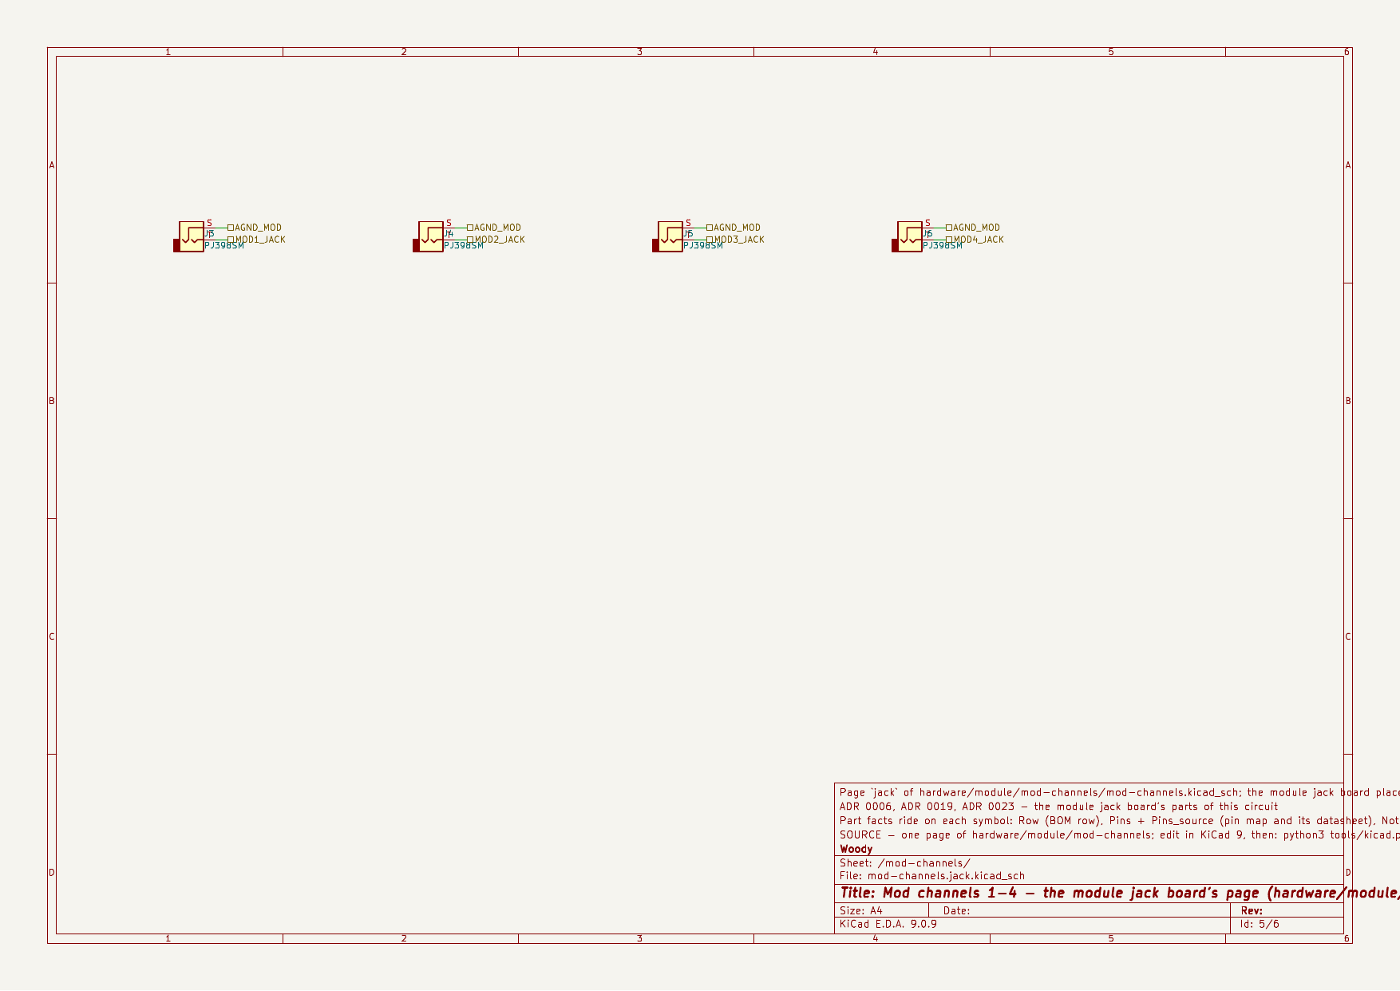
hardware/boards/module-jack/module-jack.p5.sch.png
