jeffmhopkins/Woody/hardware/boards/module-jack/module-jack.p6.sch.png

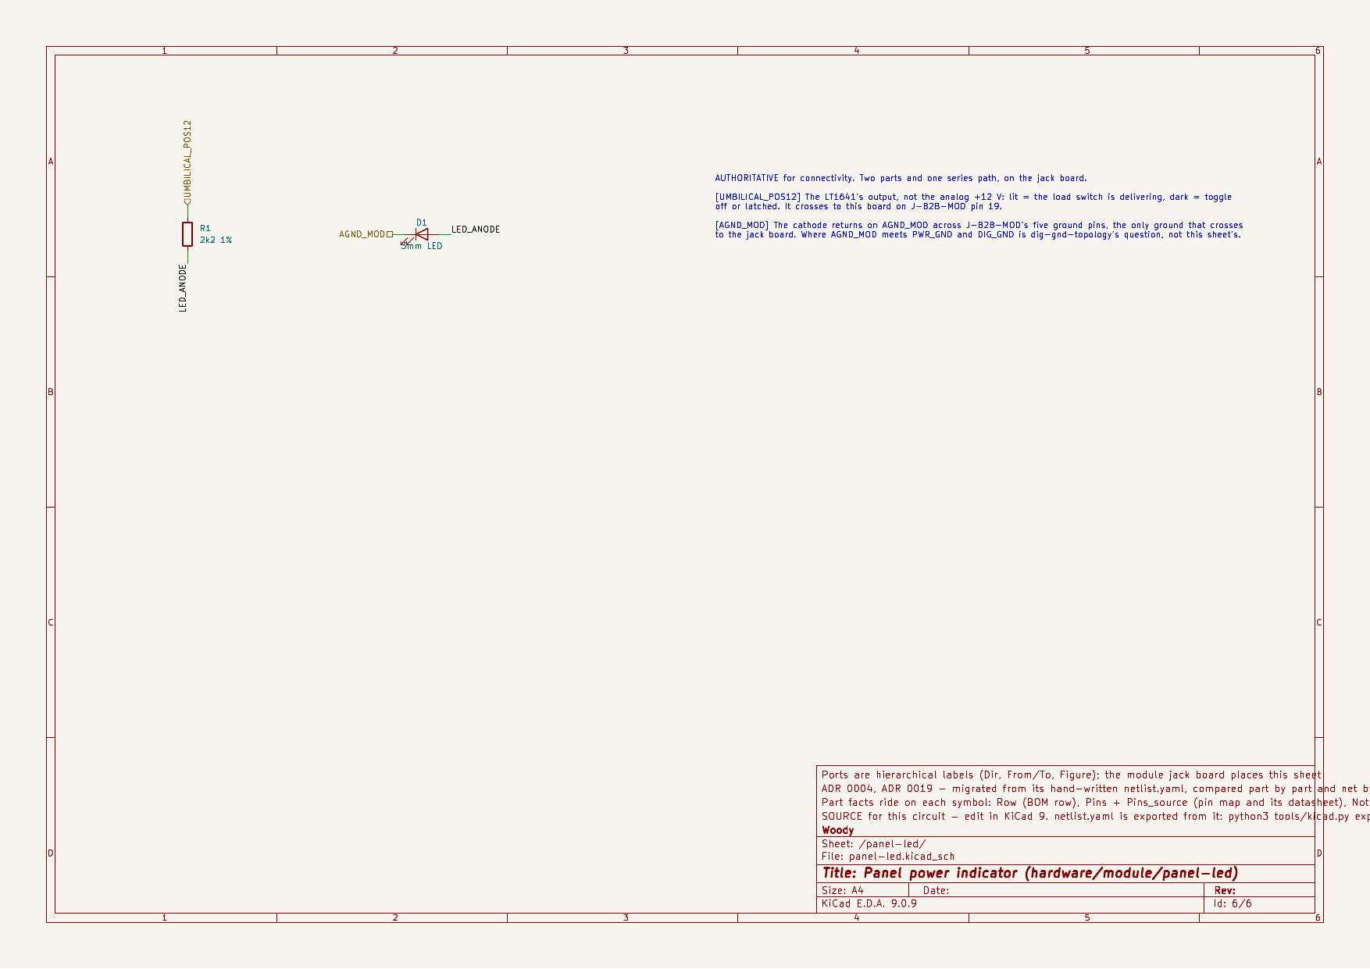
hardware/boards/module-jack/module-jack.p6.sch.png
