jeffmhopkins/Woody/hardware/boards/module-jack/module-jack.sch.png

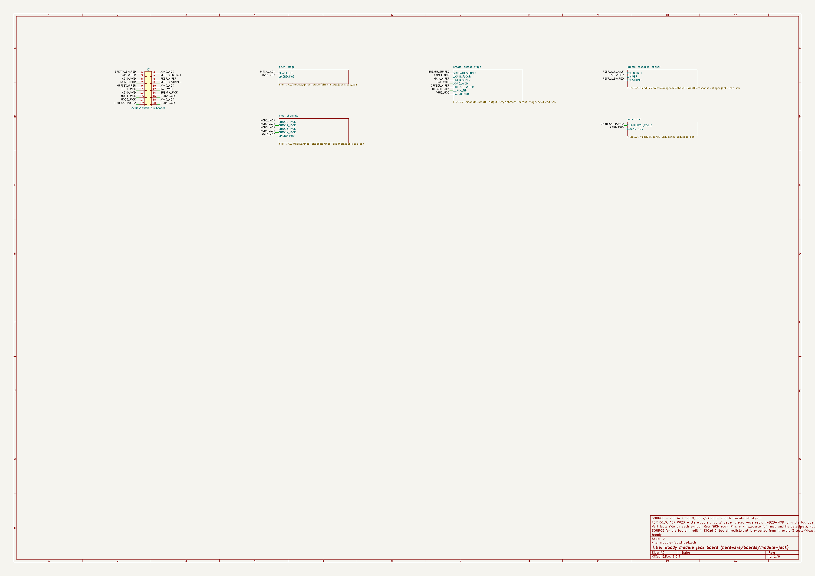
hardware/boards/module-jack/module-jack.sch.png
