jeffmhopkins/Woody/hardware/boards/module-main/module-main.p2.sch.png

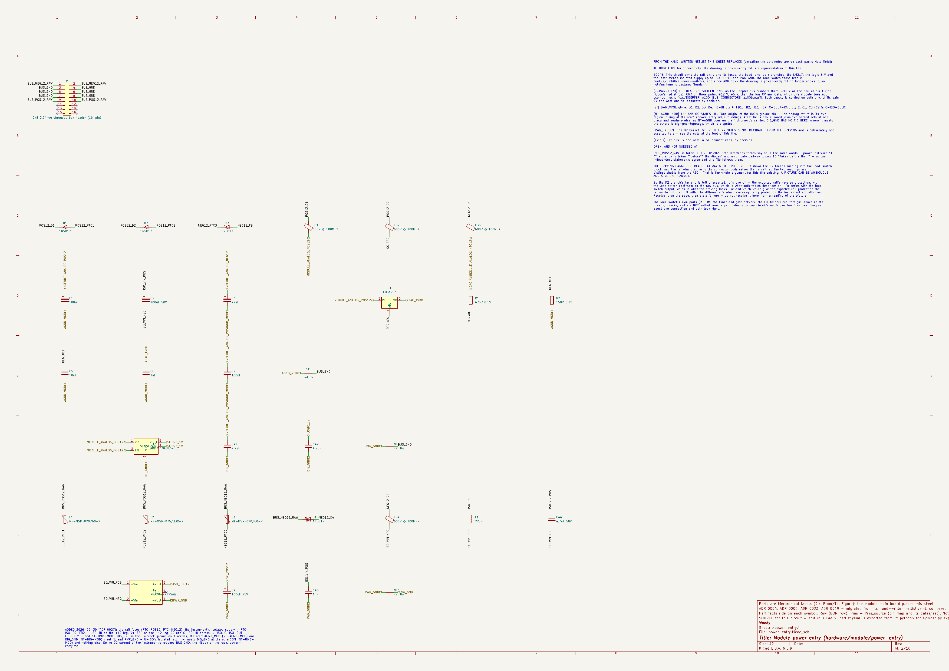
hardware/boards/module-main/module-main.p2.sch.png
