jeffmhopkins/Woody/hardware/boards/module-main/module-main.p3.sch.png

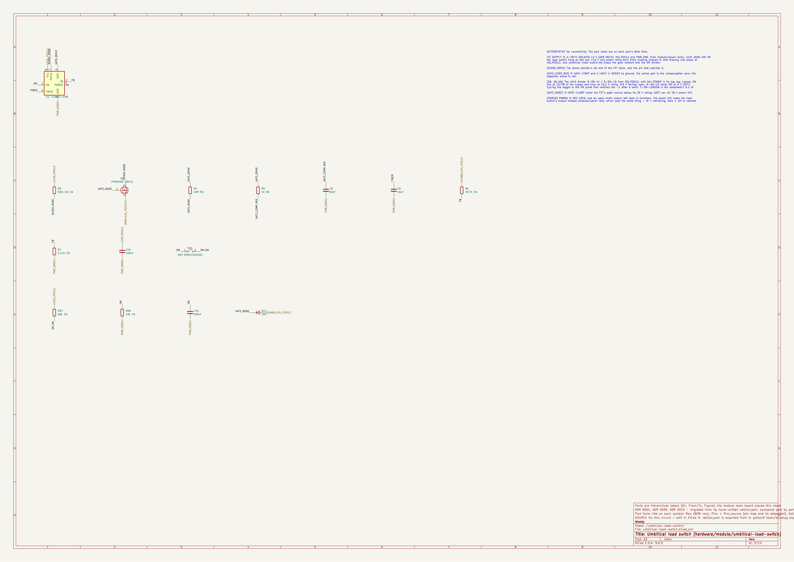
hardware/boards/module-main/module-main.p3.sch.png
