jeffmhopkins/Woody/hardware/boards/module-main/module-main.p4.sch.png

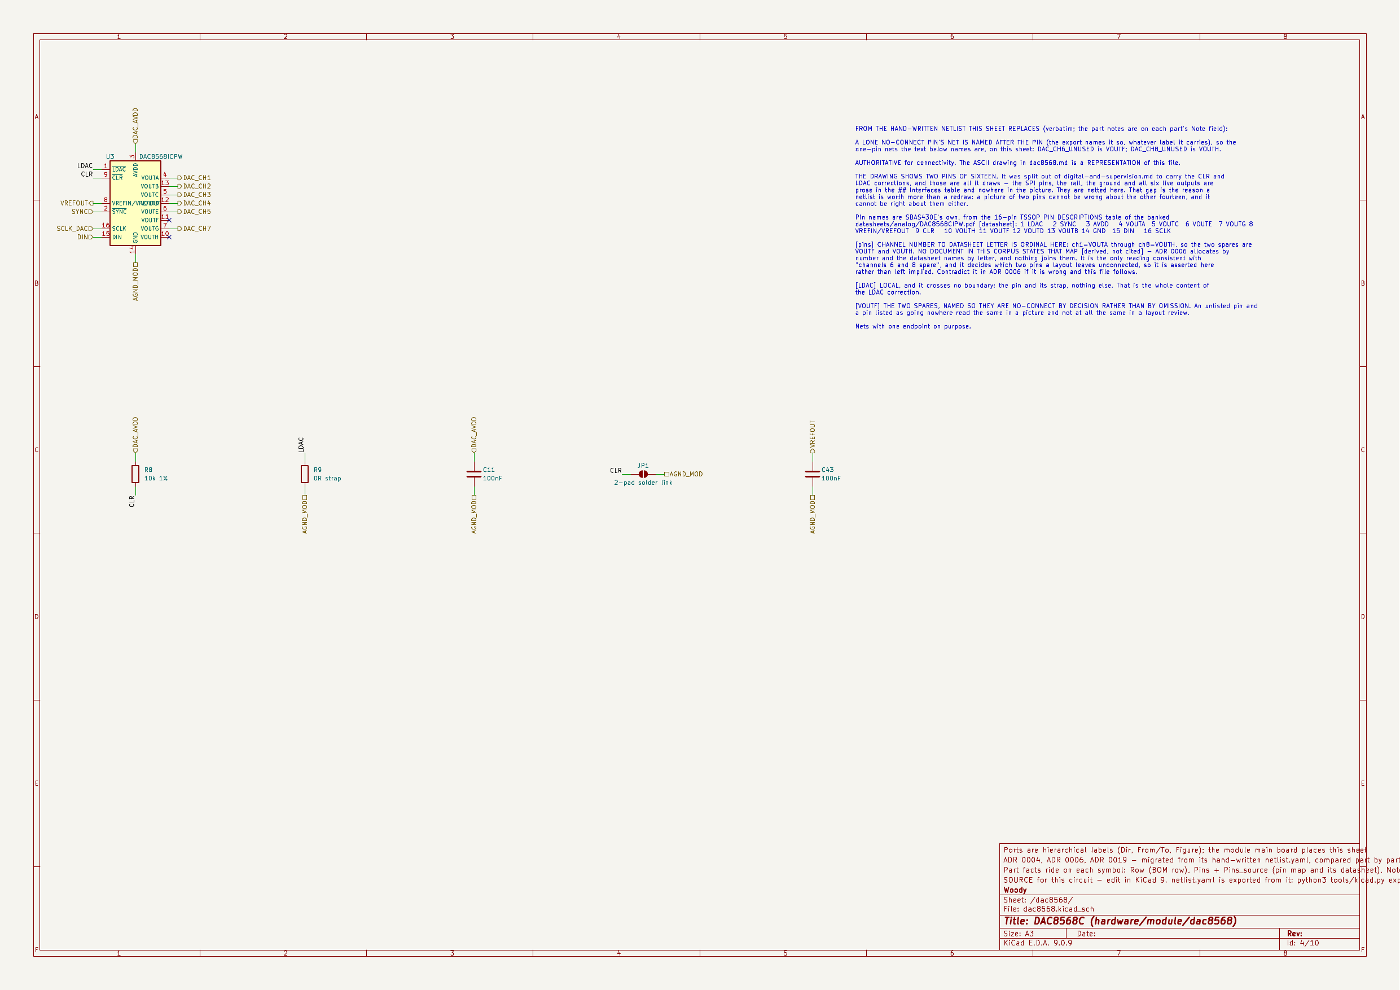
hardware/boards/module-main/module-main.p4.sch.png
