jeffmhopkins/Woody/hardware/boards/module-main/module-main.p5.sch.png

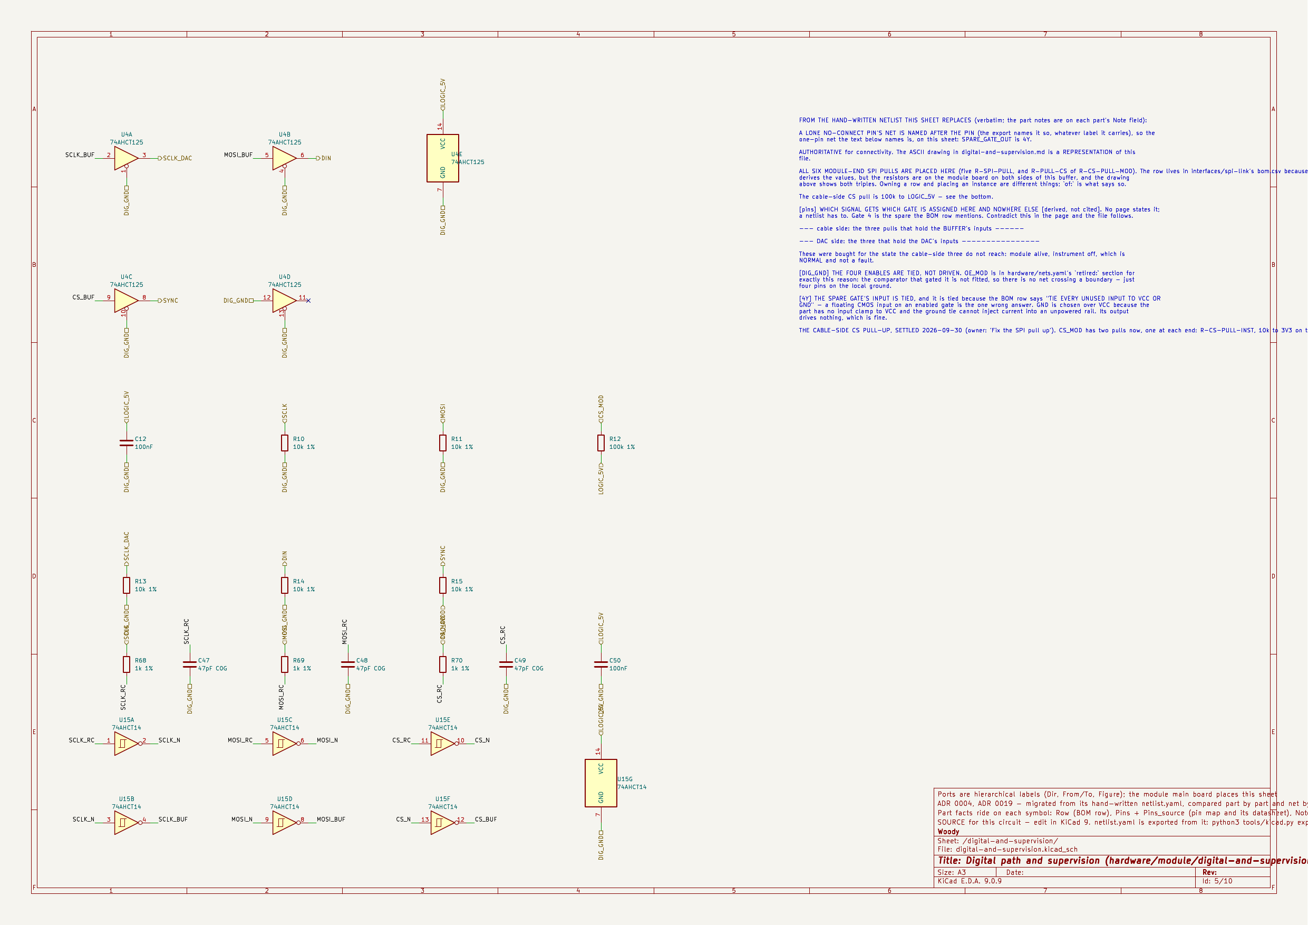
hardware/boards/module-main/module-main.p5.sch.png
