jeffmhopkins/Woody/hardware/boards/module-main/module-main.p6.sch.png

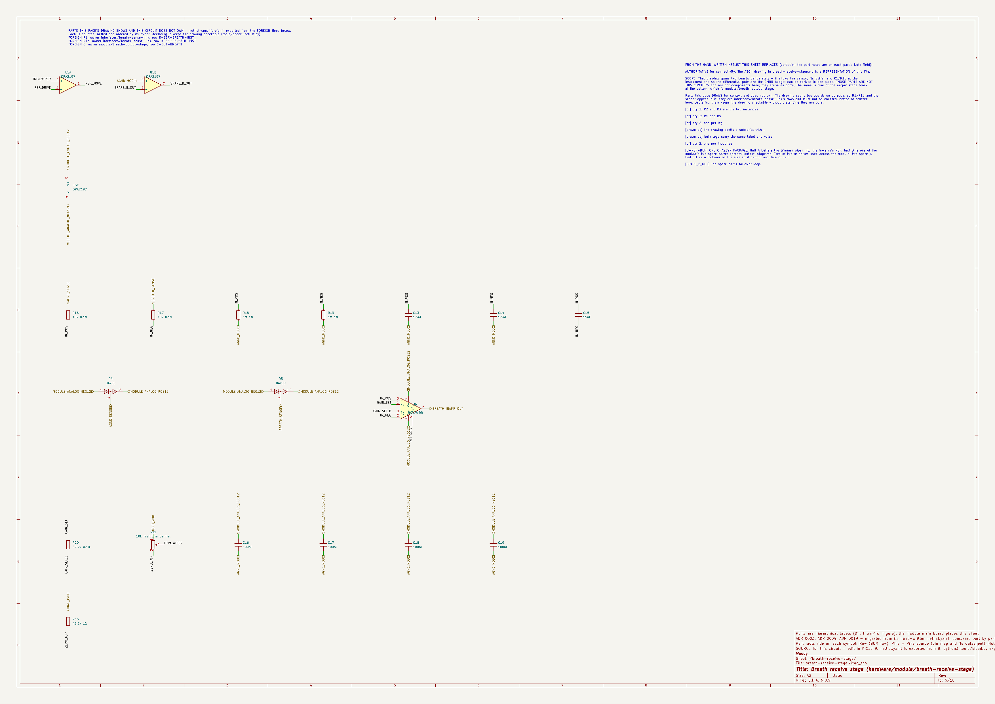
hardware/boards/module-main/module-main.p6.sch.png
