jeffmhopkins/Woody/hardware/boards/module-main/module-main.p7.sch.png

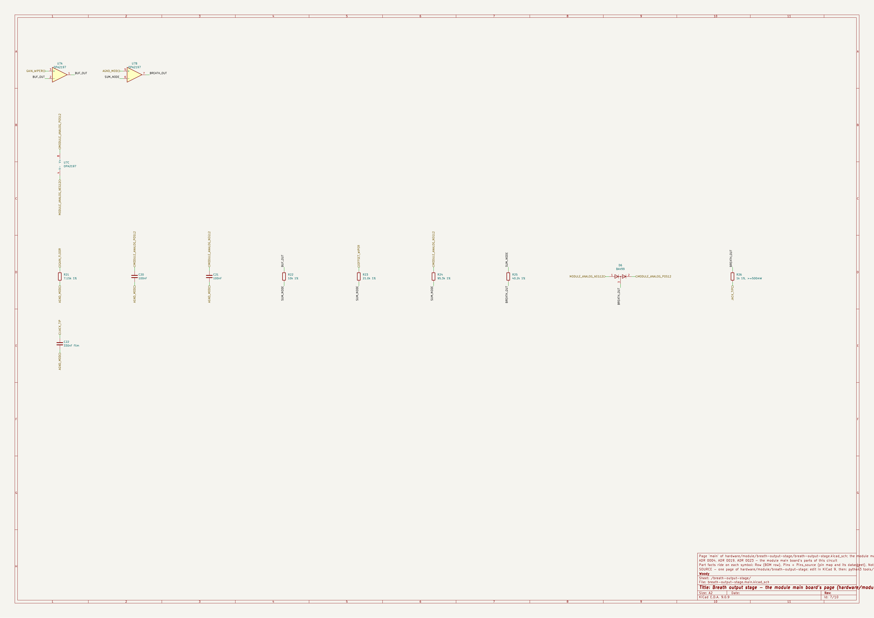
hardware/boards/module-main/module-main.p7.sch.png
