jeffmhopkins/Woody/hardware/boards/module-main/module-main.p9.sch.png

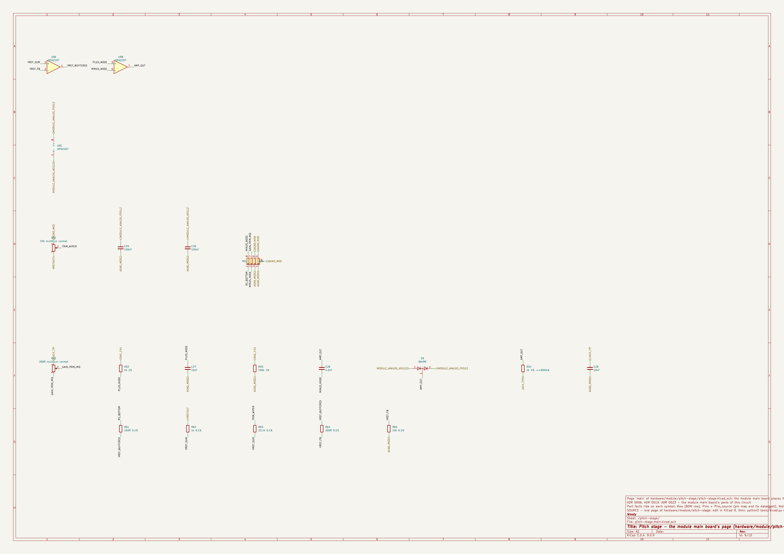
hardware/boards/module-main/module-main.p9.sch.png
