jeffmhopkins/Woody/hardware/boards/module-main/module-main.p10.sch.png

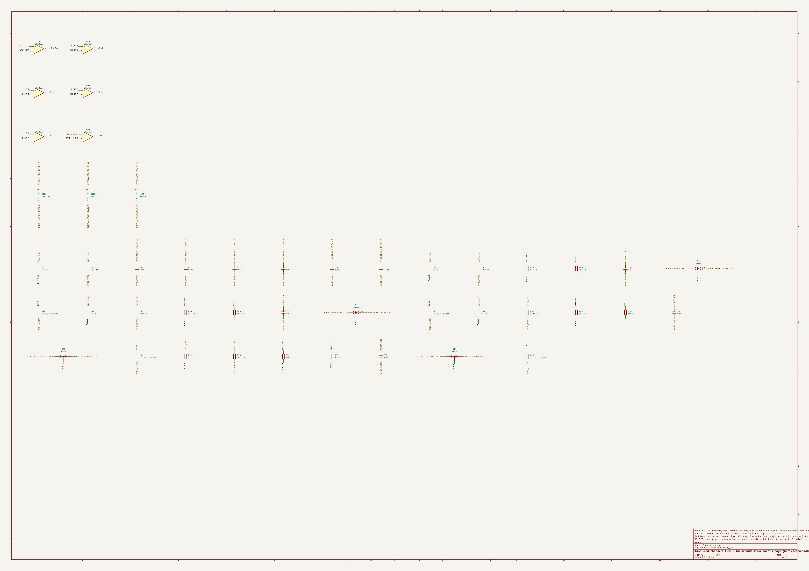
hardware/boards/module-main/module-main.p10.sch.png
