jeffmhopkins/Woody/hardware/boards/module-main/module-main.sch.png

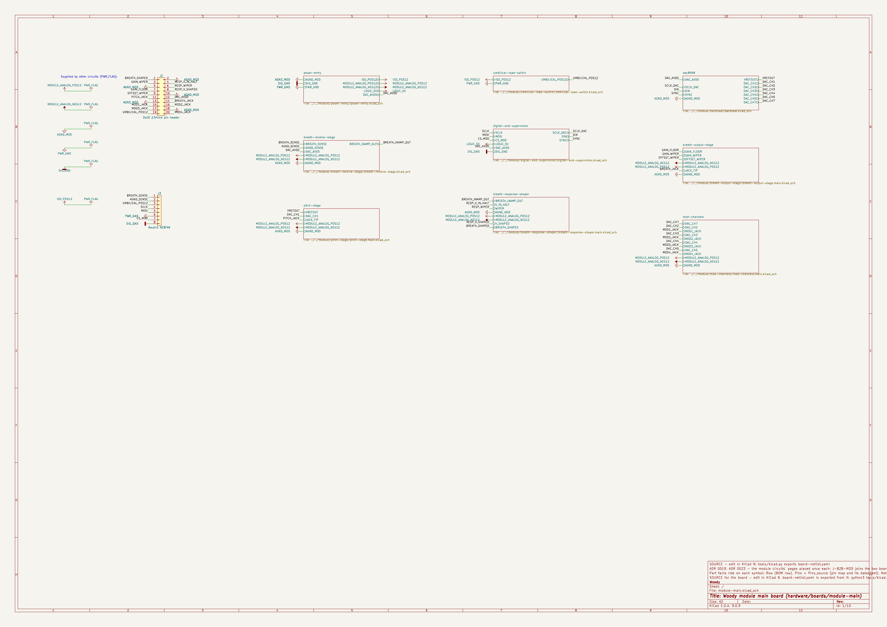
hardware/boards/module-main/module-main.sch.png
