jeffmhopkins/Woody/hardware/boards/umb-adapter/umb-adapter.sch.png

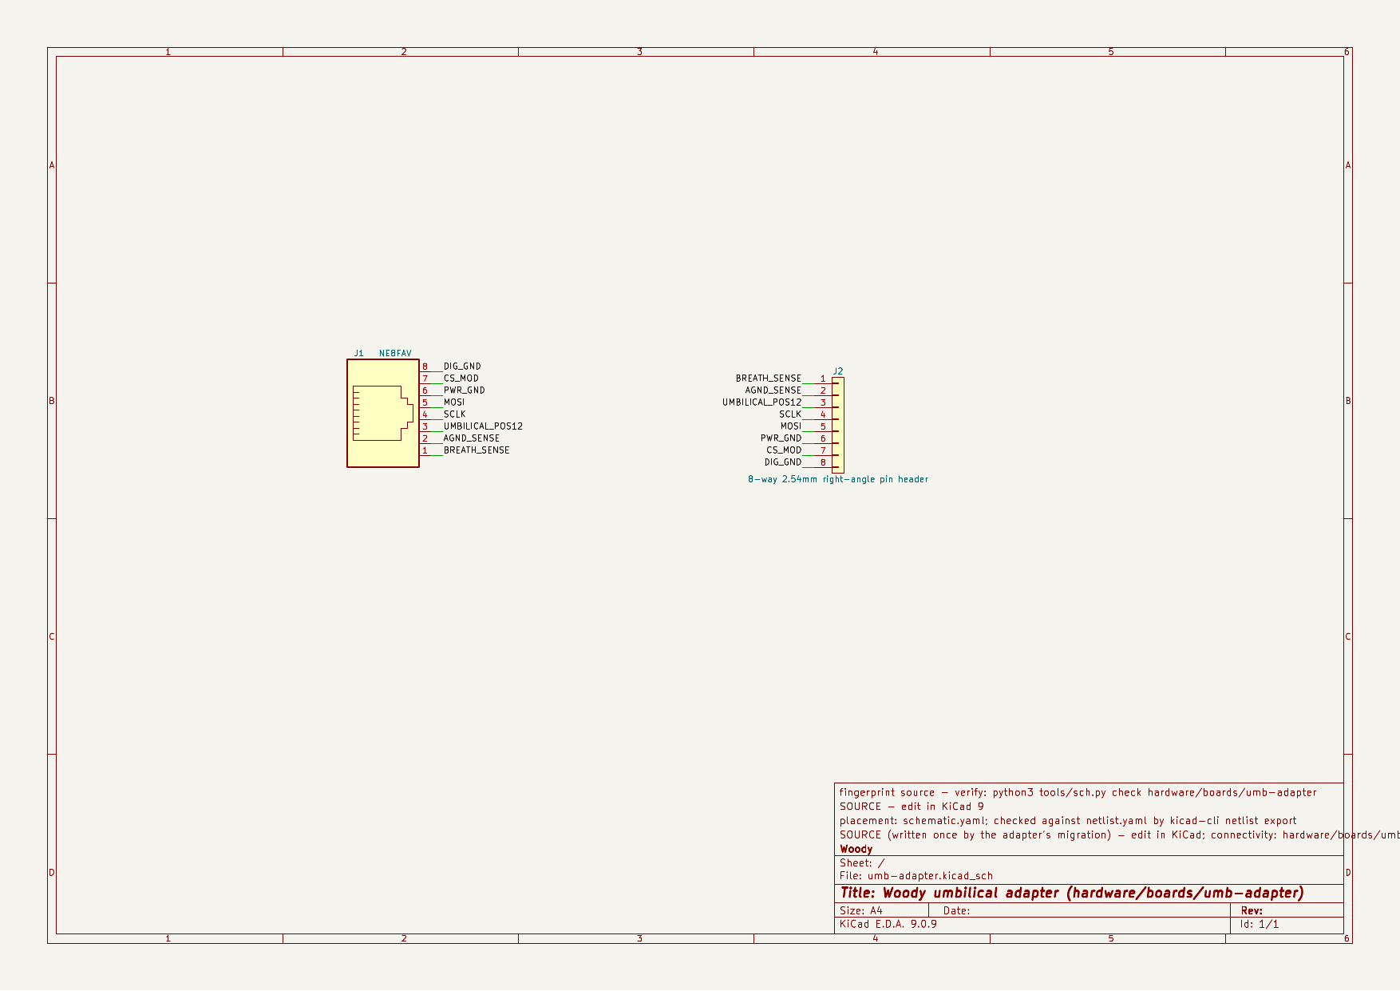
hardware/boards/umb-adapter/umb-adapter.sch.png
