jeffmhopkins/Woody/hardware/interfaces/key-chain-loom/key-chain-loom.sch.png

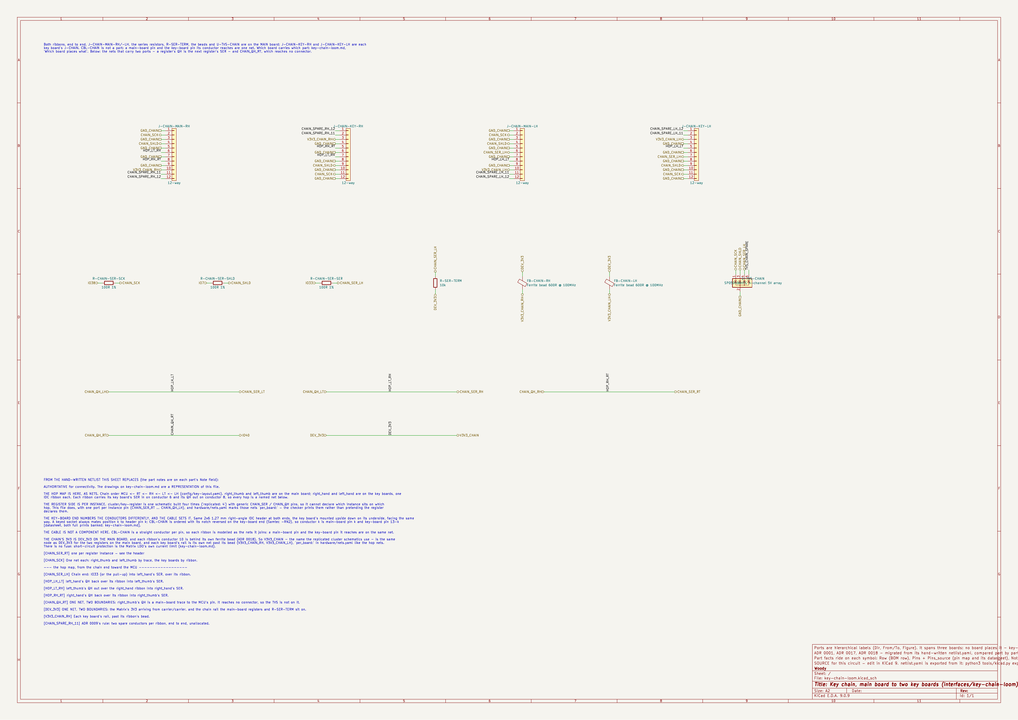
hardware/interfaces/key-chain-loom/key-chain-loom.sch.png
