jeffmhopkins/Woody/hardware/interfaces/spi-link/spi-link.sch.png

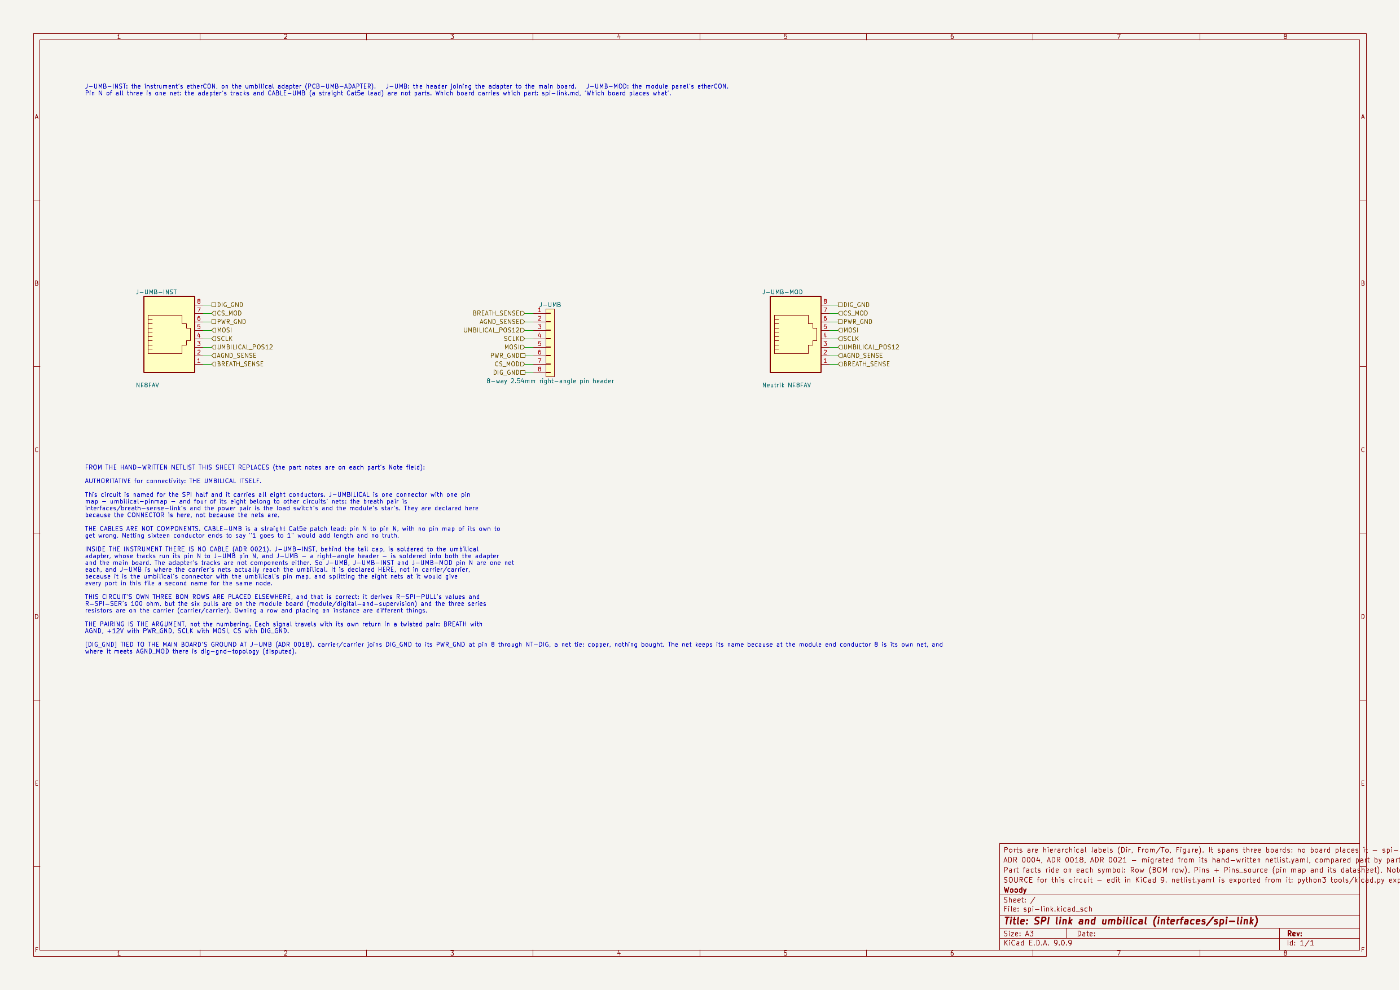
hardware/interfaces/spi-link/spi-link.sch.png
