jeffmhopkins/Woody/hardware/module/breath-output-stage/breath-output-stage.sch.png

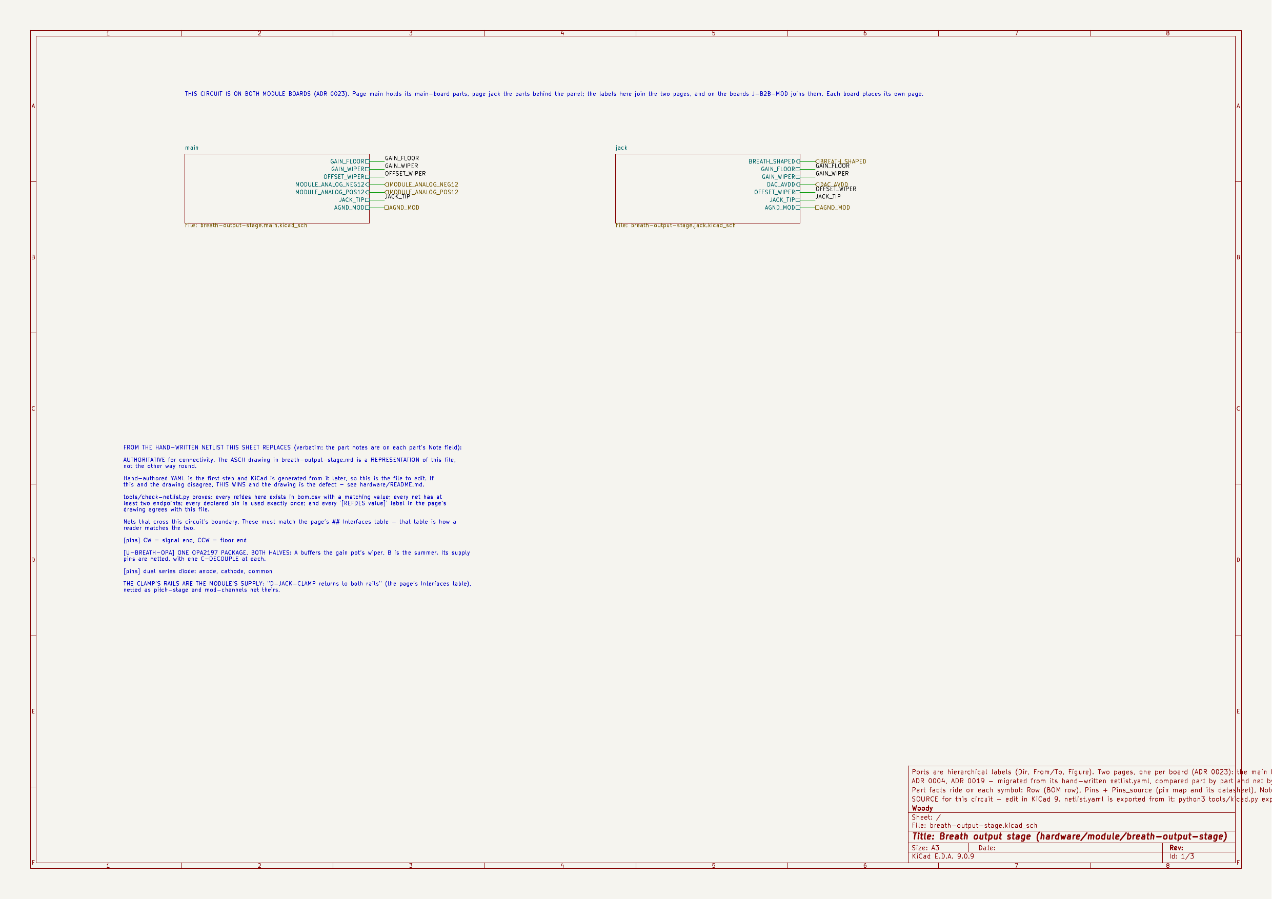
hardware/module/breath-output-stage/breath-output-stage.sch.png
