jeffmhopkins/Woody/hardware/module/breath-response-shaper/breath-response-shaper.p2.sch.png

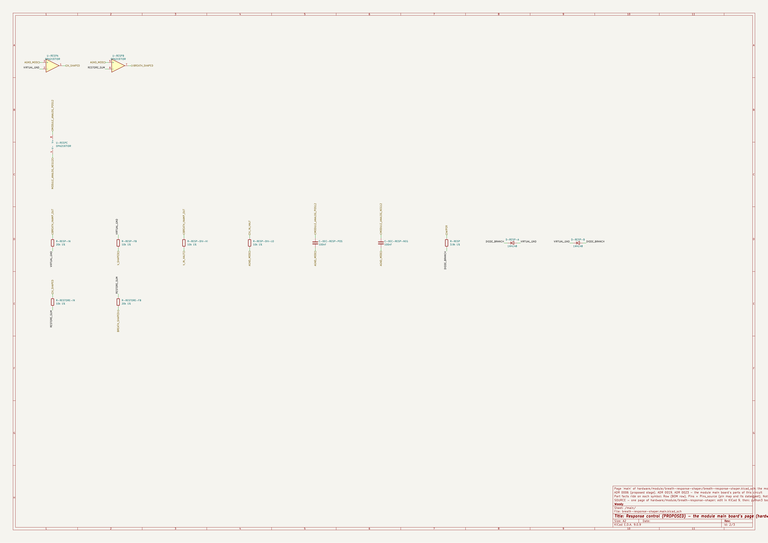
hardware/module/breath-response-shaper/breath-response-shaper.p2.sch.png
