jeffmhopkins/Woody/hardware/module/breath-response-shaper/breath-response-shaper.sch.png

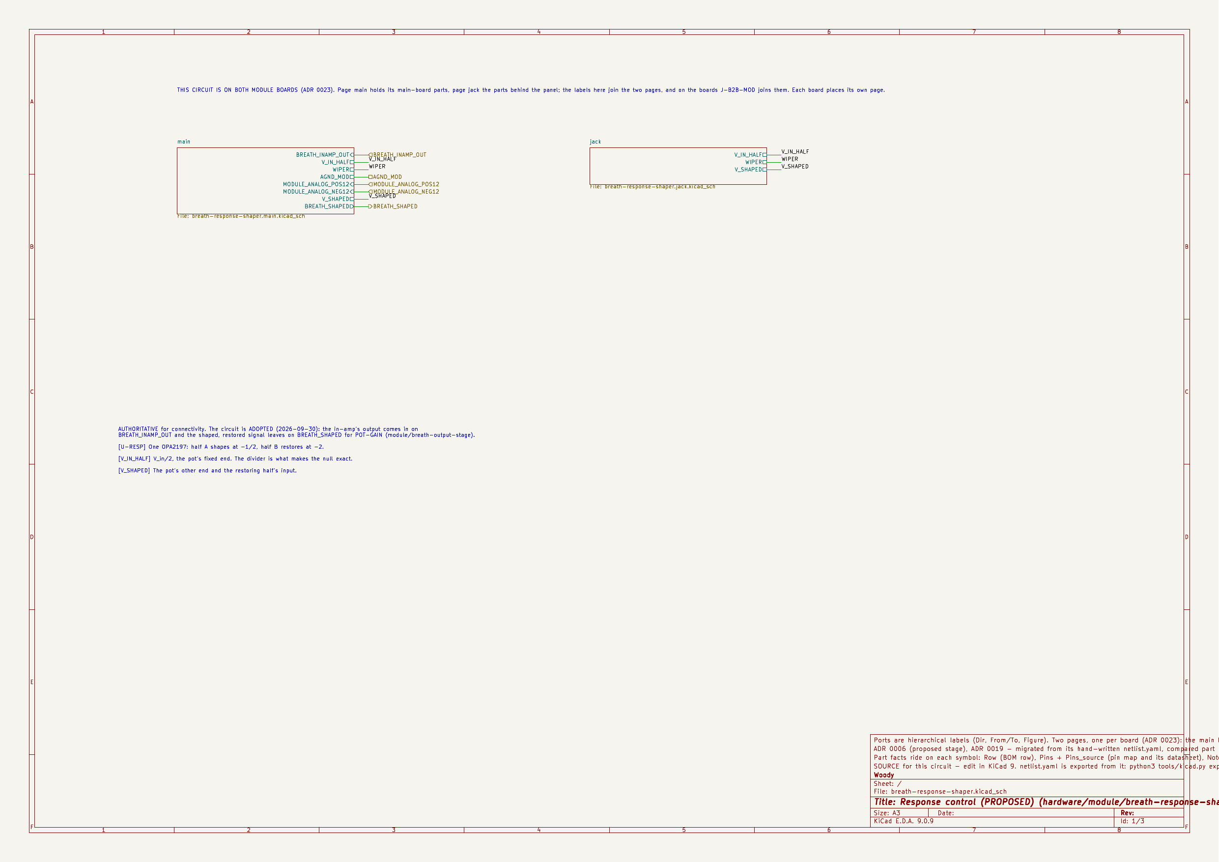
hardware/module/breath-response-shaper/breath-response-shaper.sch.png
