jeffmhopkins/Woody/hardware/module/mod-channels/mod-channels.p2.sch.png

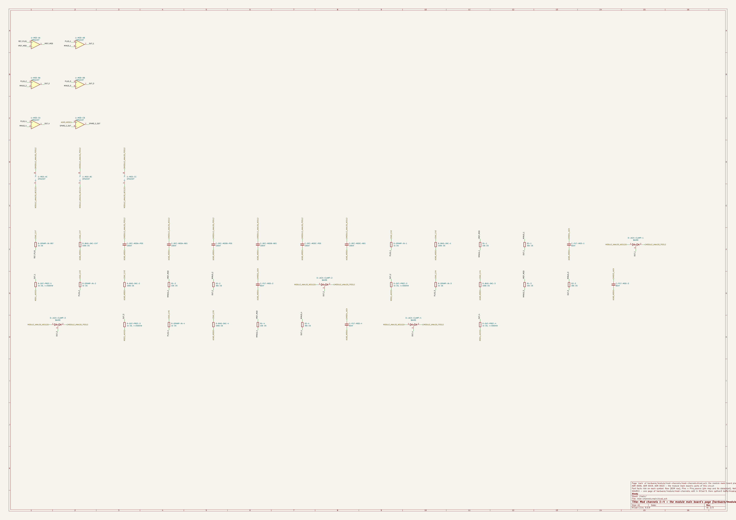
hardware/module/mod-channels/mod-channels.p2.sch.png
