jeffmhopkins/Woody/hardware/module/mod-channels/mod-channels.sch.png

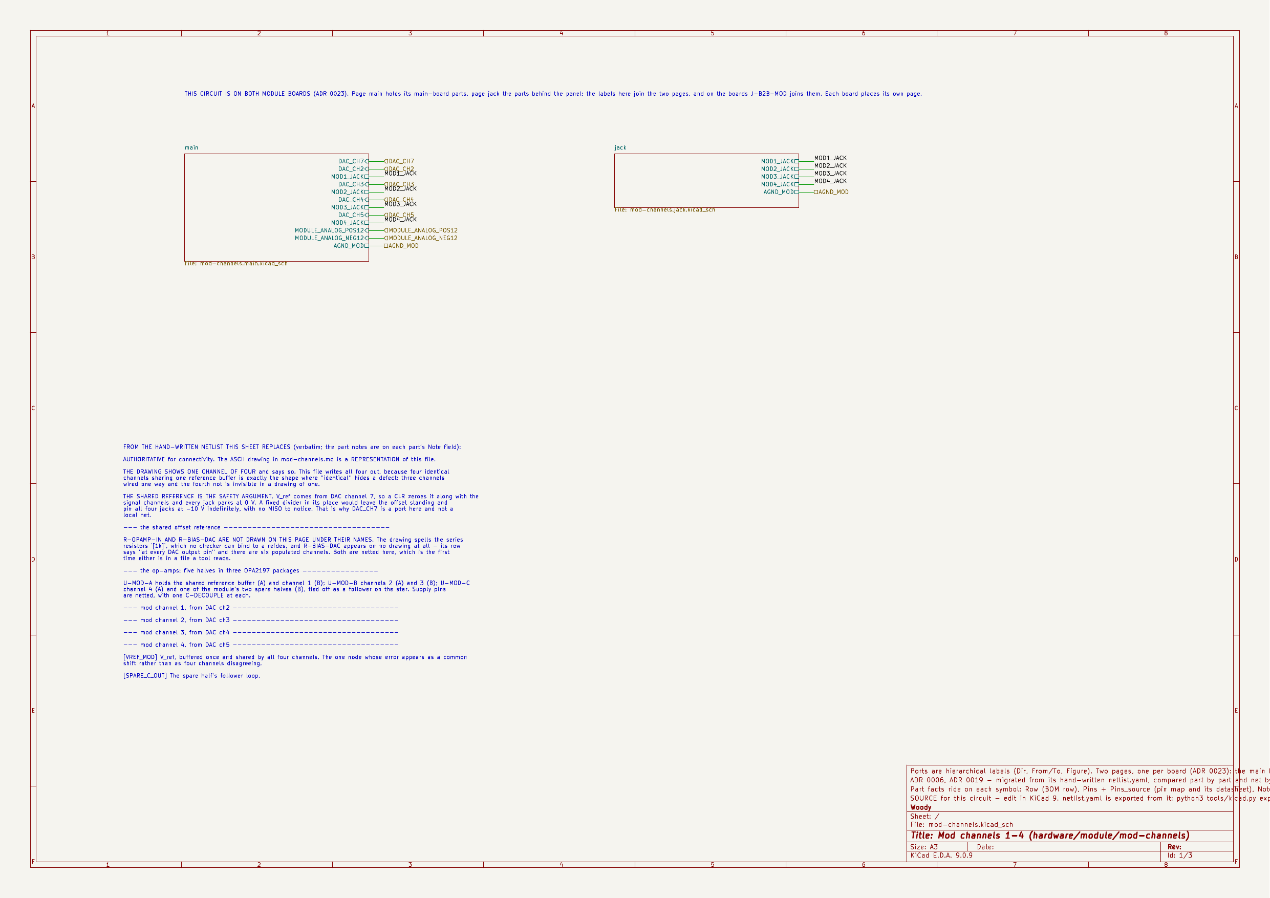
hardware/module/mod-channels/mod-channels.sch.png
