jeffmhopkins/Woody/hardware/module/power-entry/power-entry.sch.png

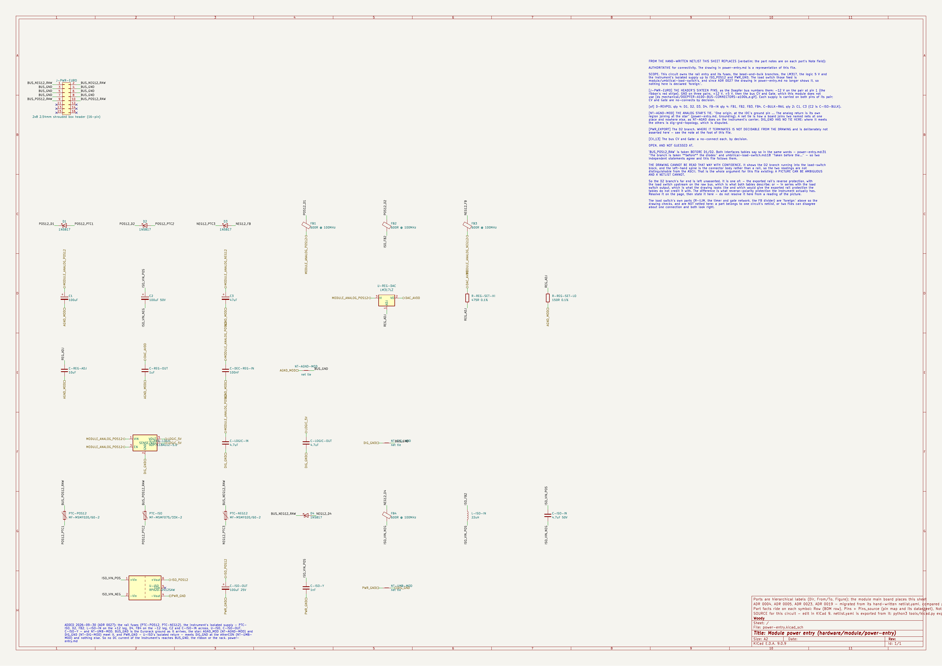
hardware/module/power-entry/power-entry.sch.png
