jeffmhopkins/Woody/hardware/module/umbilical-load-switch/umbilical-load-switch.sch.png

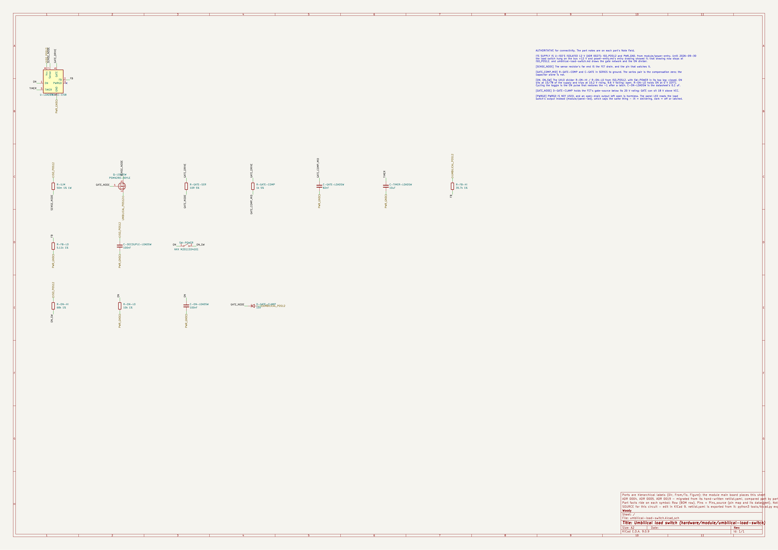
hardware/module/umbilical-load-switch/umbilical-load-switch.sch.png
