jeffmhopkins/Woody/mechanical/module/art/tex-height.png

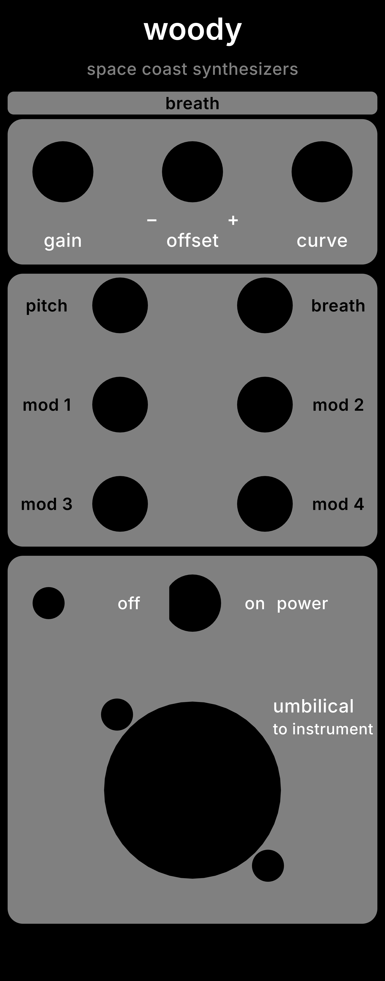
mechanical/module/art/tex-height.png
