jeffmhopkins/Woody/mechanical/module/art/tex-roughness.png

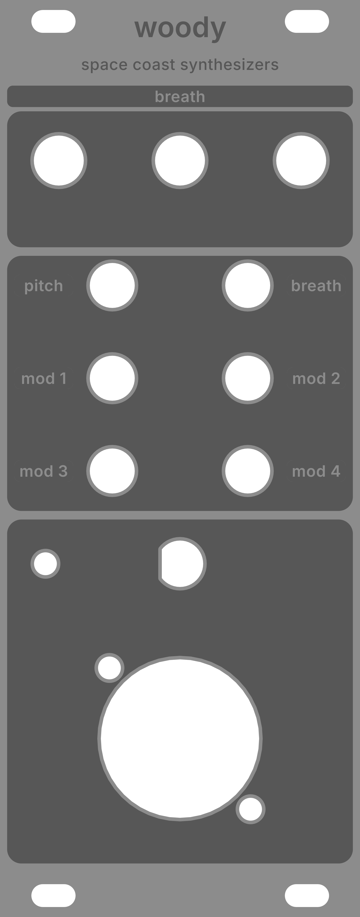
mechanical/module/art/tex-roughness.png
