jeffmhopkins/Woody/mechanical/module/export/jack-board.dxf

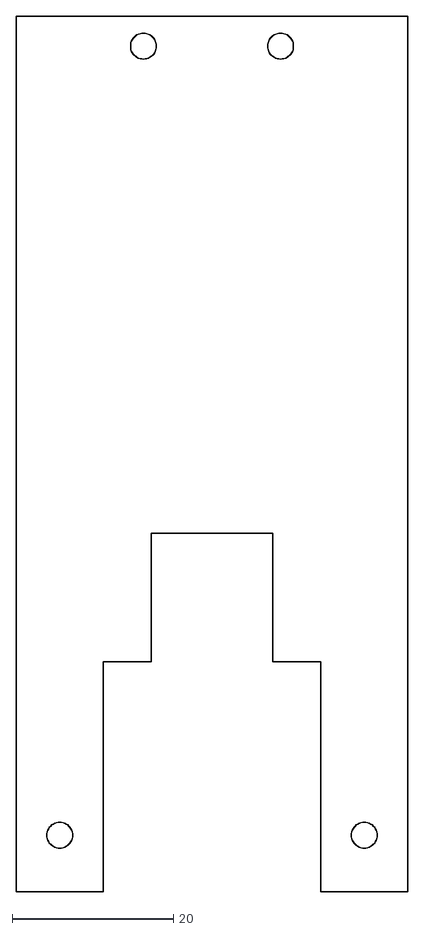
[picture p118: CAD file, 2026-09-30]
mechanical/module/export/jack-board.dxf
48.5 x 108.5
