jeffmhopkins/Woody/datasheets/analog/KICAD-TSSOP-16_4.4x5mm_P0.65mm-3D.step

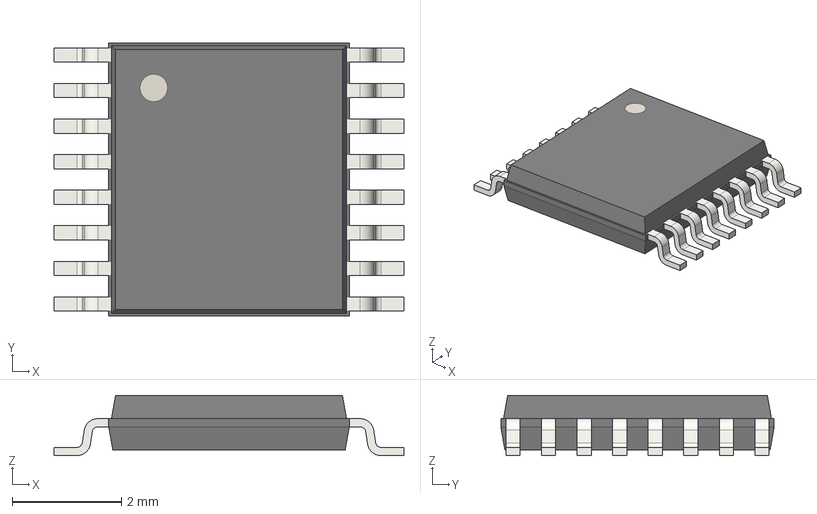
[picture p119: CAD file, 2026-09-30]
datasheets/analog/KICAD-TSSOP-16_4.4x5mm_P0.65mm-3D.step
6.40 x 5.00 x 1.10 mm
