jeffmhopkins/Woody/datasheets/connectors/SAMTEC-SHF-106-01-L-D-TH-3D.step

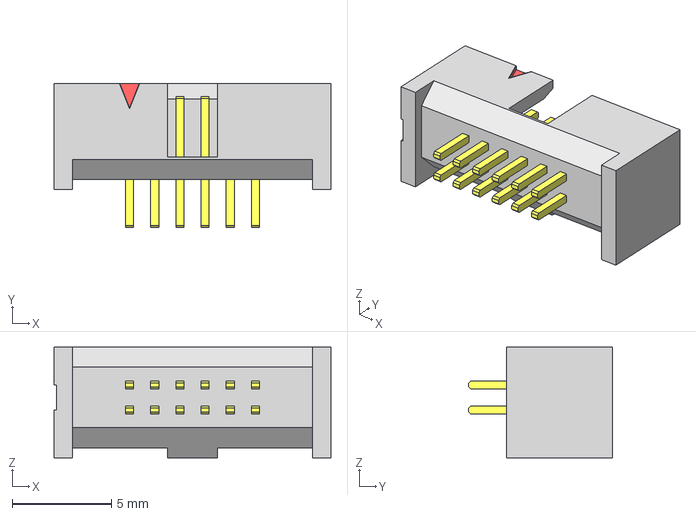
[picture p120: CAD file, 2026-09-30]
datasheets/connectors/SAMTEC-SHF-106-01-L-D-TH-3D.step
14.0 x 7.24 x 5.59 mm
