jeffmhopkins/Woody/datasheets/discrete-and-power/KICAD-L_1206_3216Metric-3D.step

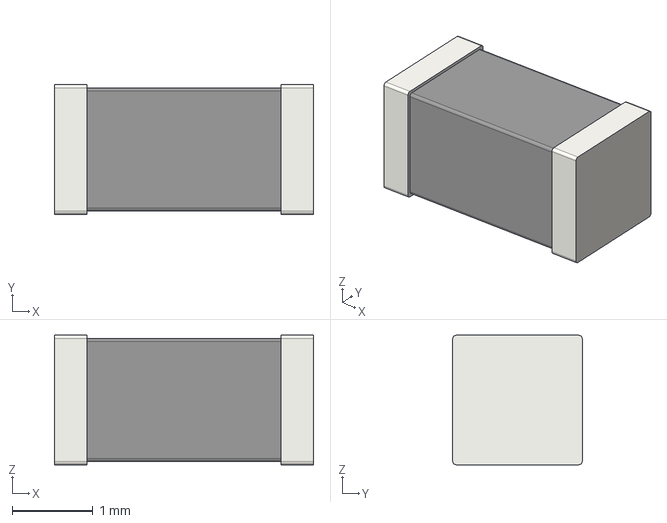
[picture p121: CAD file, 2026-09-30]
datasheets/discrete-and-power/KICAD-L_1206_3216Metric-3D.step
3.20 x 1.60 x 1.60 mm
