jeffmhopkins/Woody/datasheets/led/WS2812B-5050-PLCC4-KICAD-3D.step

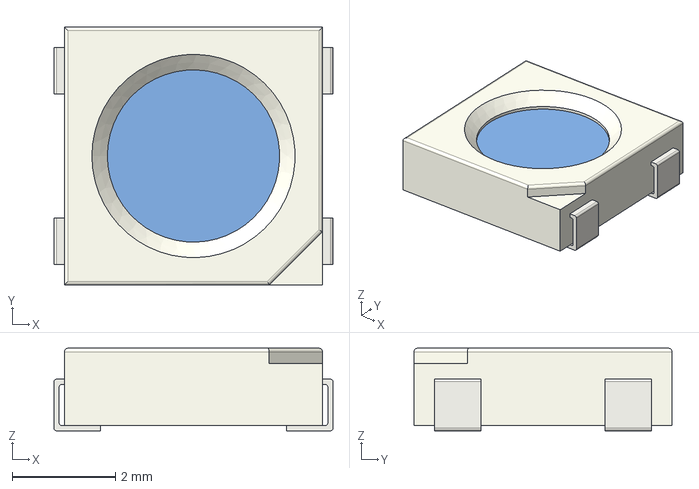
[picture p122: CAD file, 2026-09-30]
datasheets/led/WS2812B-5050-PLCC4-KICAD-3D.step
5.40 x 5.00 x 1.60 mm
