jeffmhopkins/Woody/datasheets/mechanical/WAVESHARE-ESP32-S3-MATRIX-3D.stp

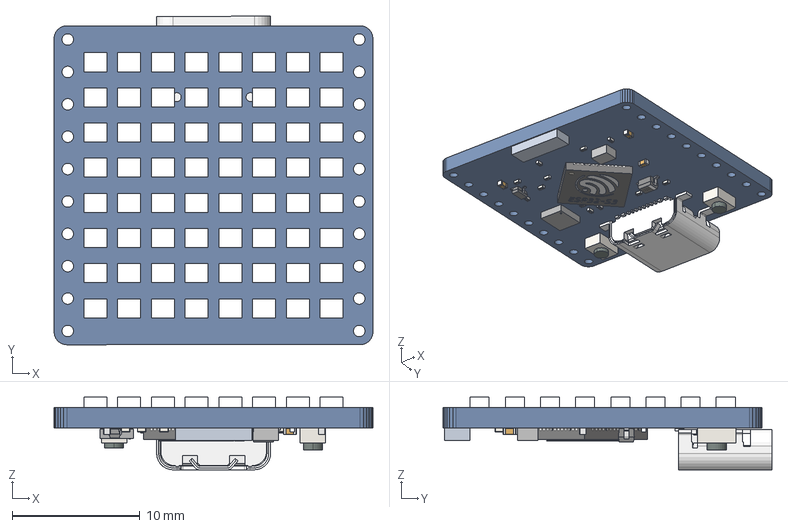
[picture p123: CAD file, 2026-09-30]
datasheets/mechanical/WAVESHARE-ESP32-S3-MATRIX-3D.stp
25.0 x 25.8 x 5.70 mm
BOARD
EXTRUDED-13553 x 64
USER_LIBRARY-RES_0603-0201_1 x 12
USER_LIBRARY-RES_0603-0201_2 x 12
USER_LIBRARY-RES_0603-0201_3 x 12
USER_LIBRARY-RES_0603-0201_4 x 12
EXTRUDED-12834 x 2
2_A x 15
3_1_A x 3
SOD323
USER_LIBRARY-SOT-523
USER_LIBRARY-ESP32-S3-SOC_1
USER_LIBRARY-ESP32-S3-SOC_2
USER_LIBRARY-ESP32-S3-SOC_3
USER_LIBRARY-ESP32-S3-SOC_4
USER_LIBRARY-ESP32-S3-SOC_5
USER_LIBRARY-ESP32-S3-SOC_6
USER_LIBRARY-ESP32-S3-SOC_7
USER_LIBRARY-ESP32-S3-SOC_8
USER_LIBRARY-ESP32-S3-SOC_9
USER_LIBRARY-ESP32-S3-SOC_10
USER_LIBRARY-ESP32-S3-SOC_11
USER_LIBRARY-ESP32-S3-SOC_12
USER_LIBRARY-ESP32-S3-SOC_13
USER_LIBRARY-ESP32-S3-SOC_14
EXTRUDED-163023
EXTRUDED-163568
TYPE-C_SMT-9X3X7_3
C3
