jeffmhopkins/Woody/mechanical/export/side.dxf

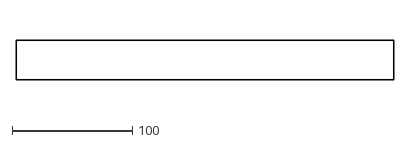
[picture p124: CAD file, 2026-09-30]
mechanical/export/side.dxf
313.8 x 33.0
