jeffmhopkins/Woody/mechanical/module/export/panel.dxf

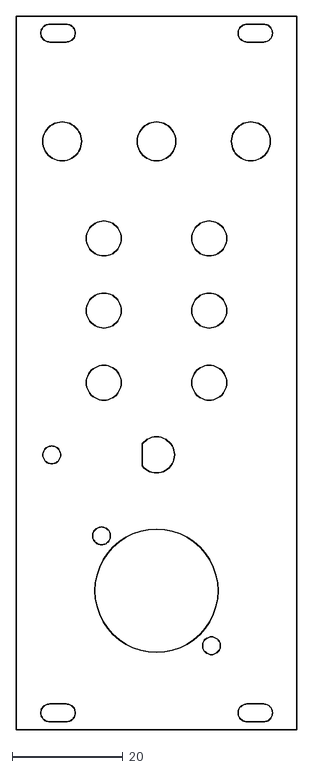
[picture p125: CAD file, 2026-09-30]
mechanical/module/export/panel.dxf
50.5 x 128.5
