jeffmhopkins/Woody/datasheets/analog/MPXV7007-CASE-1351-01-HAXO-3D.step

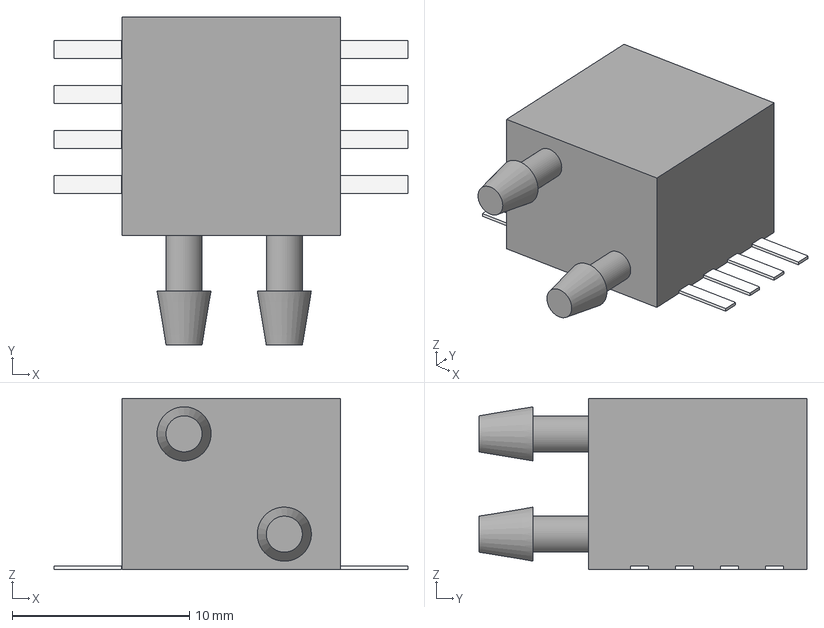
[picture p126: CAD file, 2026-09-30]
datasheets/analog/MPXV7007-CASE-1351-01-HAXO-3D.step
19.9 x 18.5 x 9.65 mm
Pads
