jeffmhopkins/Woody/datasheets/connectors/NEUTRIK-NE8FDY-C6-3D.stp

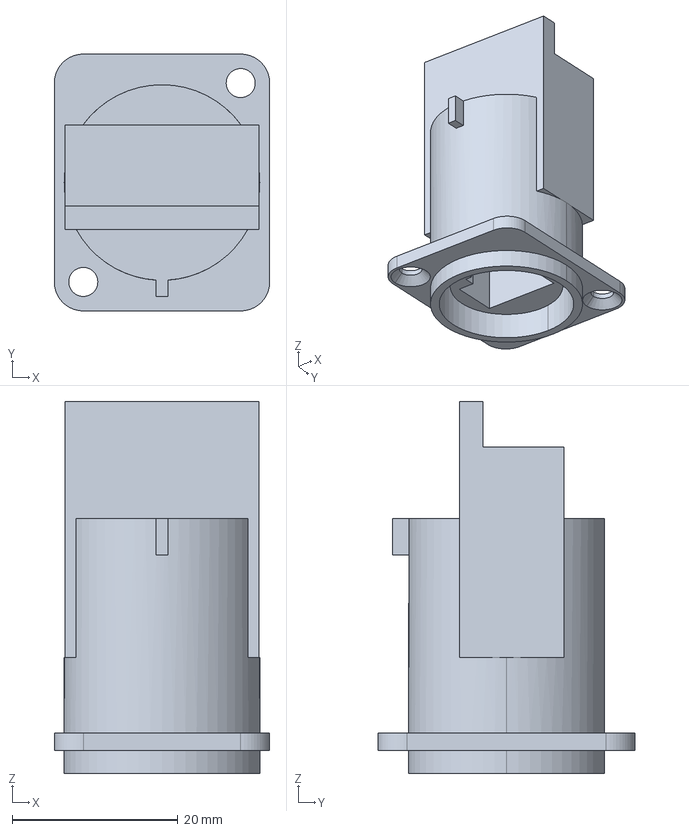
[picture p127: CAD file, 2026-09-30]
datasheets/connectors/NEUTRIK-NE8FDY-C6-3D.stp
26.0 x 31.0 x 44.9 mm
