jeffmhopkins/Woody/datasheets/discrete-and-power/KICAD-C_0805_2012Metric-3D.step

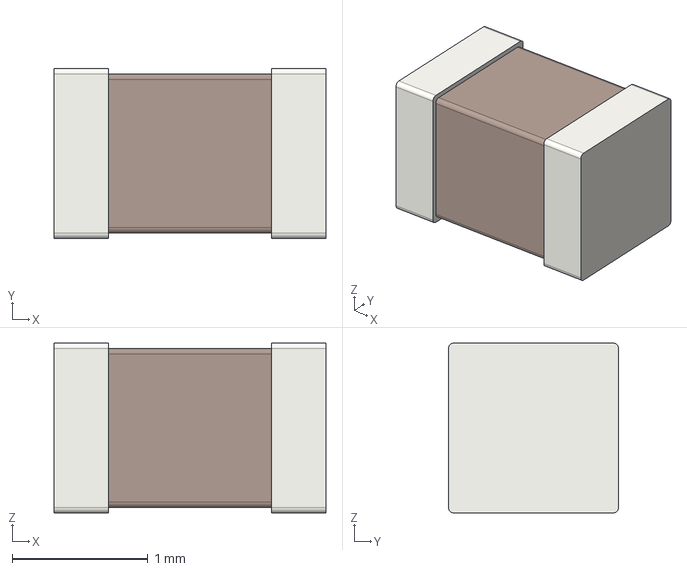
[picture p128: CAD file, 2026-09-30]
datasheets/discrete-and-power/KICAD-C_0805_2012Metric-3D.step
2.00 x 1.25 x 1.25 mm
