jeffmhopkins/Woody/mechanical/export/oak-top.dxf

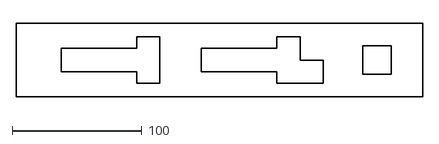
[picture p129: CAD file, 2026-09-30]
mechanical/export/oak-top.dxf
313.8 x 57.0
