jeffmhopkins/Woody/datasheets/analog/KICAD-MSOP-8-1EP_3x3mm_P0.65mm_EP1.68x1.88mm-3D.step

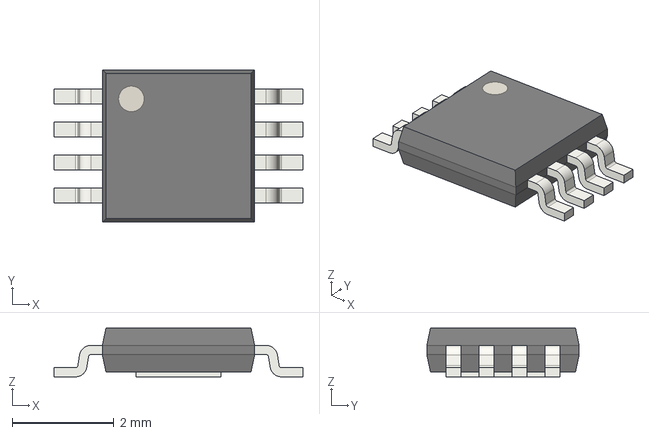
[picture p130: CAD file, 2026-09-30]
datasheets/analog/KICAD-MSOP-8-1EP_3x3mm_P0.65mm_EP1.68x1.88mm-3D.step
4.90 x 3.00 x 0.96 mm
