jeffmhopkins/Woody/datasheets/connectors/NEUTRIK-NE8FAH-3D.stp

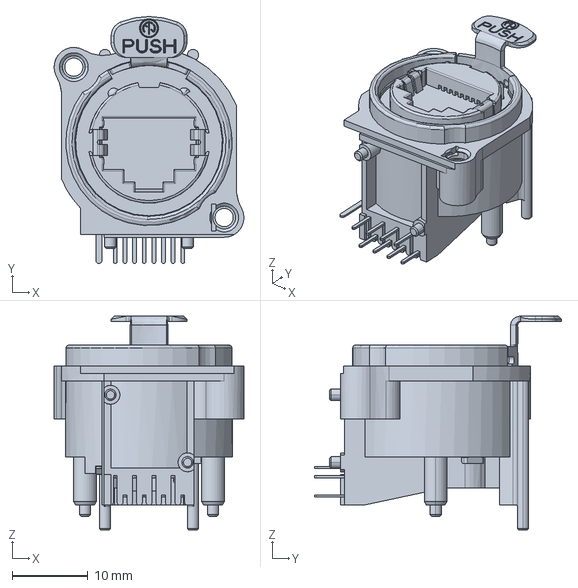
[picture p131: CAD file, 2026-09-30]
datasheets/connectors/NEUTRIK-NE8FAH-3D.stp
25.0 x 32.5 x 28.2 mm
