jeffmhopkins/Woody/datasheets/discrete-and-power/KICAD-R_1206_3216Metric-3D.step

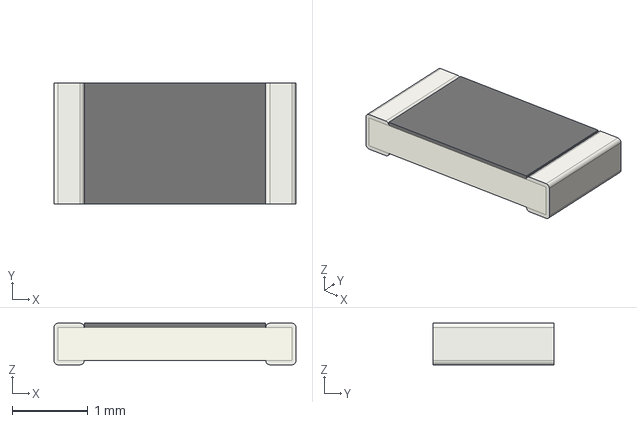
[picture p132: CAD file, 2026-09-30]
datasheets/discrete-and-power/KICAD-R_1206_3216Metric-3D.step
3.20 x 1.60 x 0.55 mm
