jeffmhopkins/Woody/datasheets/mechanical/GATERON-KS-33-3D.step

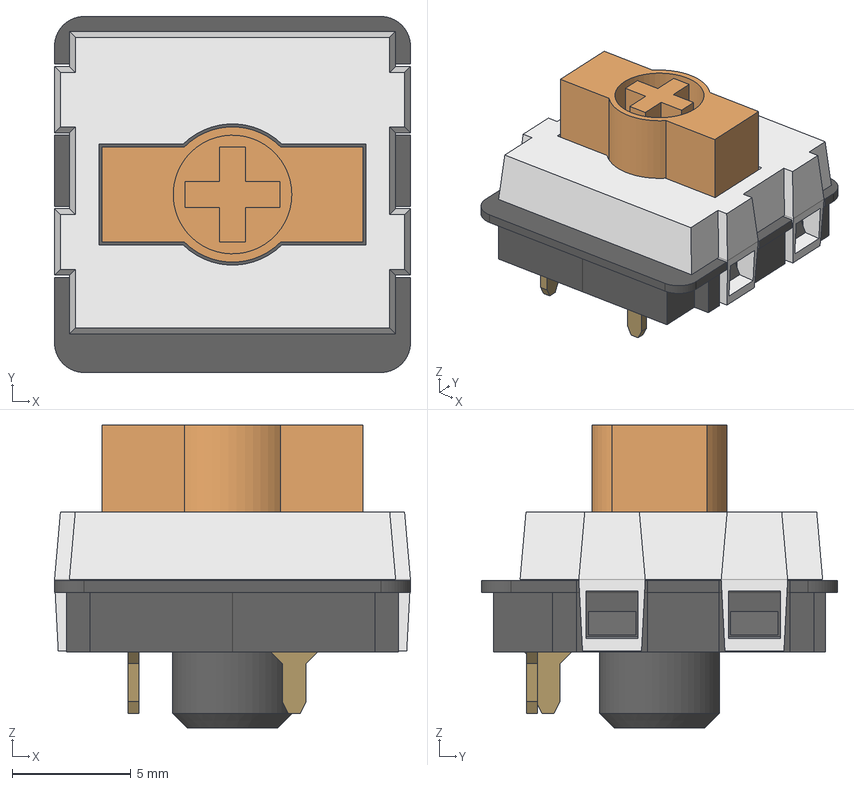
[picture p133: CAD file, 2026-09-21]
datasheets/mechanical/GATERON-KS-33-3D.step
15.0 x 15.0 x 12.8 mm
Base
Stem
Cap
PinA
PinB
