jeffmhopkins/Woody/mechanical/export/key-board-lh.dxf

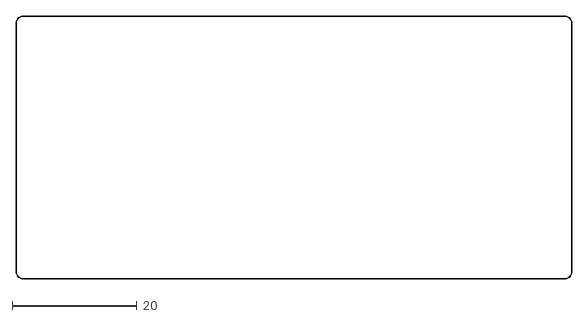
[picture p134: CAD file, 2026-09-30]
mechanical/export/key-board-lh.dxf
88.9 x 42.0
