jeffmhopkins/Woody/datasheets/connectors/NEUTRIK-NE8FDX-Y6-3D.stp

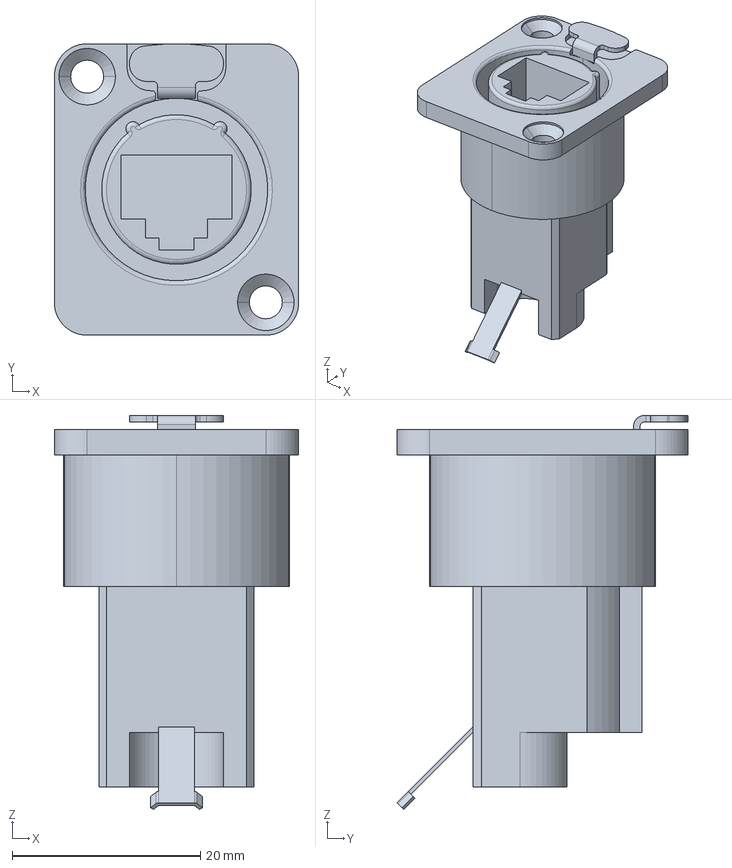
[picture p135: CAD file, 2026-09-30]
datasheets/connectors/NEUTRIK-NE8FDX-Y6-3D.stp
26.0 x 31.0 x 41.9 mm
