jeffmhopkins/Woody/datasheets/discrete-and-power/KICAD-TO-252-2-3D.step

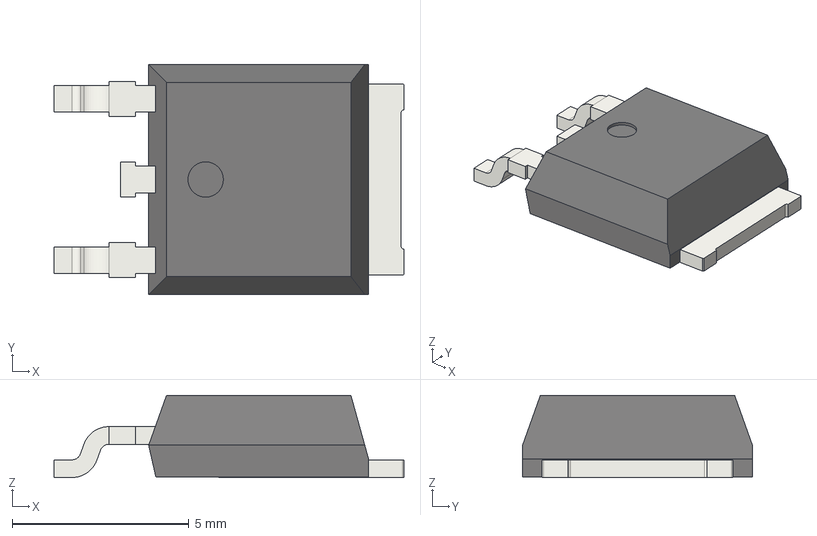
[picture p136: CAD file, 2026-09-30]
datasheets/discrete-and-power/KICAD-TO-252-2-3D.step
9.90 x 6.50 x 2.32 mm
932d09b3-9c39-11ed-93f0-dde97e994e83_part
932d09b4-9c39-11ed-93f0-dde97e994e83_part
932d09b5-9c39-11ed-93f0-dde97e994e83_part
