jeffmhopkins/Woody/datasheets/mechanical/LILYGO-T-DISPLAY-S3-AMOLED-OUTLINE.dxf

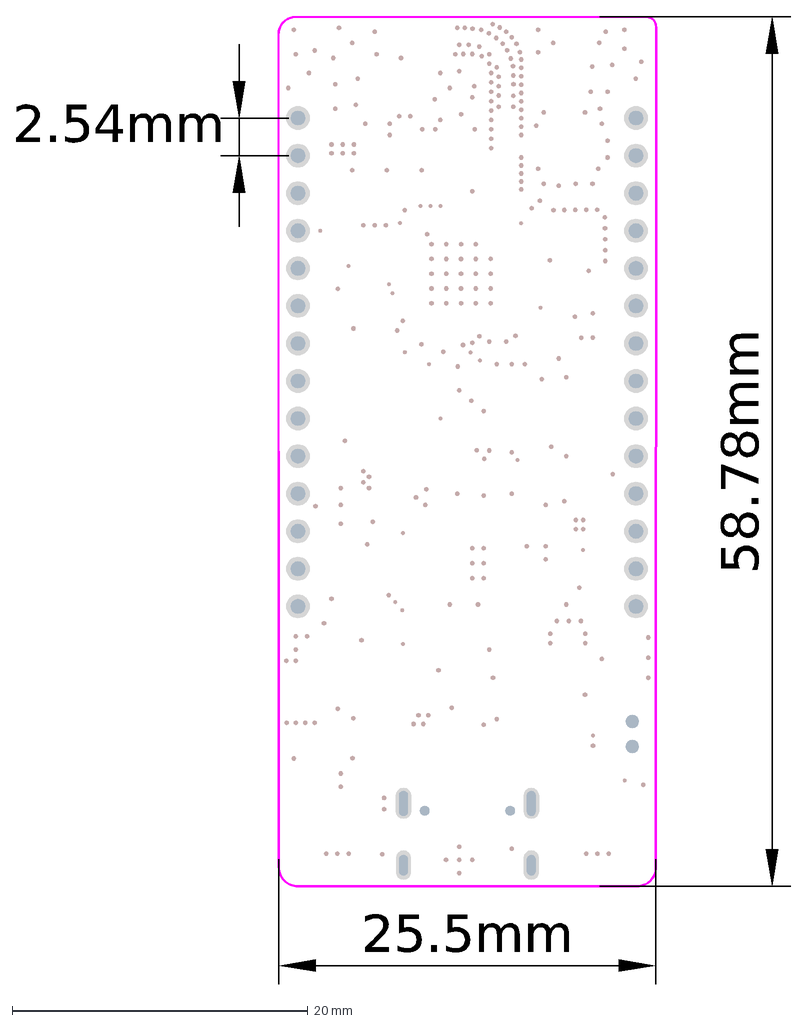
[picture p137: CAD file, 2026-09-21]
datasheets/mechanical/LILYGO-T-DISPLAY-S3-AMOLED-OUTLINE.dxf
25.5mm
58.78mm
2.54mm
