jeffmhopkins/Woody/mechanical/export/oak-pockets.dxf

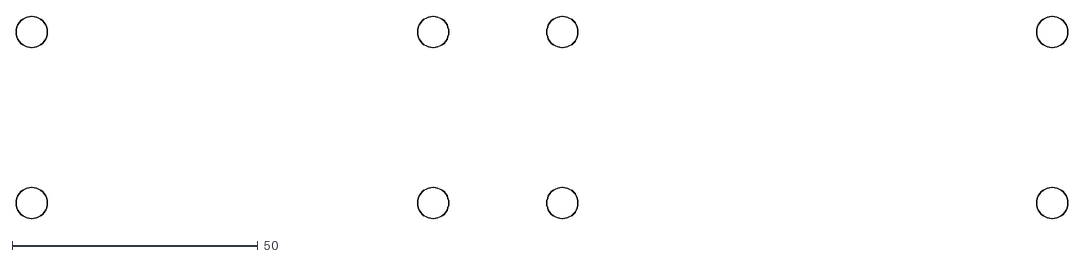
[picture p138: CAD file, 2026-09-30]
mechanical/export/oak-pockets.dxf
214.1 x 41.2
