jeffmhopkins/Woody/datasheets/connectors/KICAD-PinHeader_2x10_P2.54mm_Vertical-3D.step

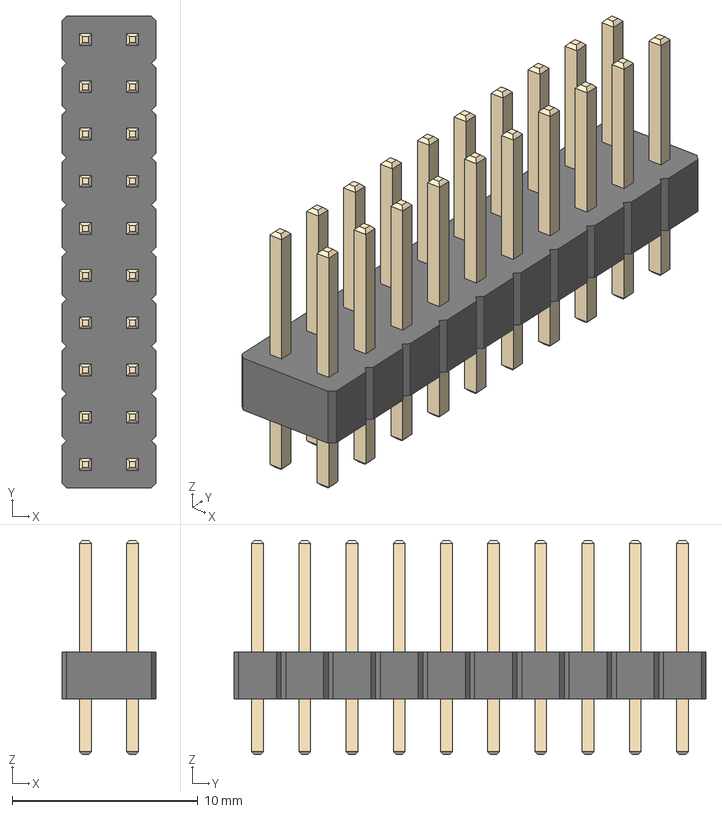
[picture p139: CAD file, 2026-09-30]
datasheets/connectors/KICAD-PinHeader_2x10_P2.54mm_Vertical-3D.step
5.08 x 25.4 x 11.5 mm
