jeffmhopkins/Woody/datasheets/discrete-and-power/KICAD-R_0805_2012Metric-3D.step

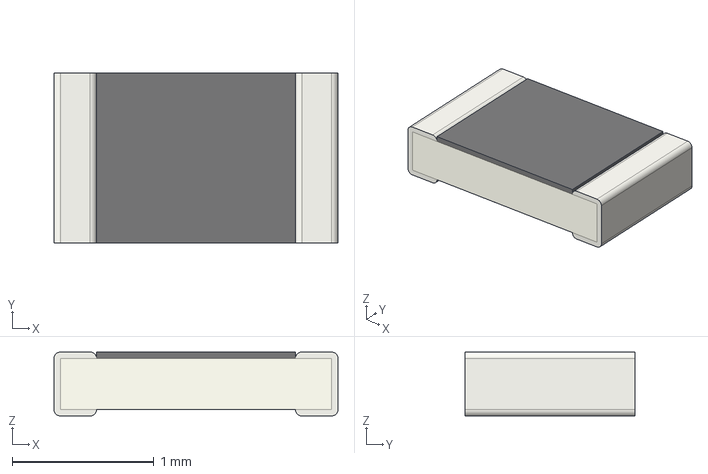
[picture p140: CAD file, 2026-09-30]
datasheets/discrete-and-power/KICAD-R_0805_2012Metric-3D.step
2.00 x 1.20 x 0.45 mm
