jeffmhopkins/Woody/datasheets/mechanical/LILYGO-T-DISPLAY-S3-AMOLED-3D.stp

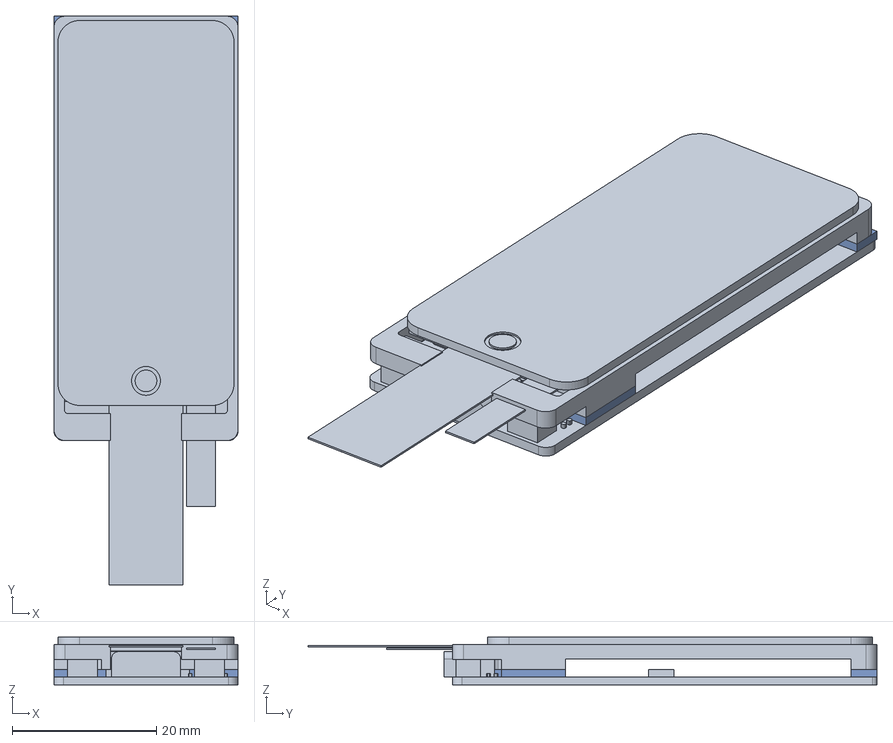
[picture p141: CAD file, 2026-09-21]
datasheets/mechanical/LILYGO-T-DISPLAY-S3-AMOLED-3D.stp
25.5 x 78.8 x 6.60 mm
0-PCB
0-TP
PRT0002
