jeffmhopkins/Woody/mechanical/export/oak-grooves.dxf

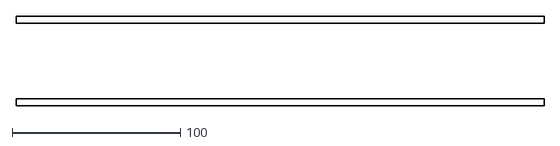
[picture p142: CAD file, 2026-09-30]
mechanical/export/oak-grooves.dxf
313.8 x 53.4
