jeffmhopkins/Woody/datasheets/connectors/HANXIA-HX-PZ2.54-1x5P-ZZ-3D.step

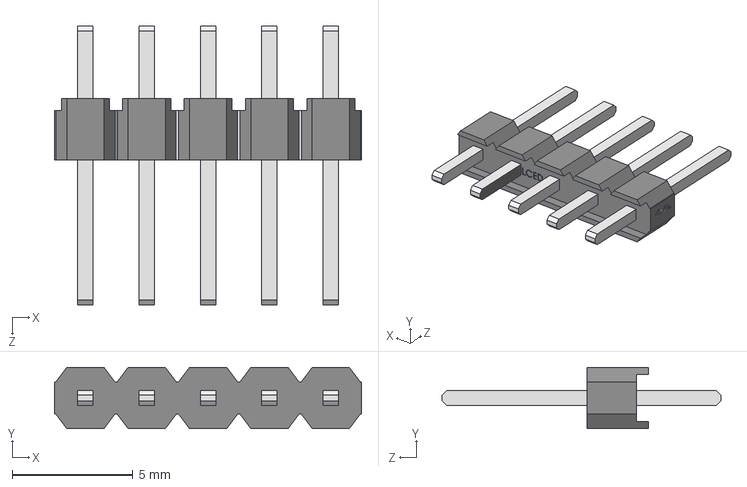
[picture p143: CAD file, 2026-09-30]
datasheets/connectors/HANXIA-HX-PZ2.54-1x5P-ZZ-3D.step
12.7 x 2.54 x 11.5 mm
