jeffmhopkins/Woody/datasheets/discrete-and-power/KICAD-C_1210_3225Metric-3D.step

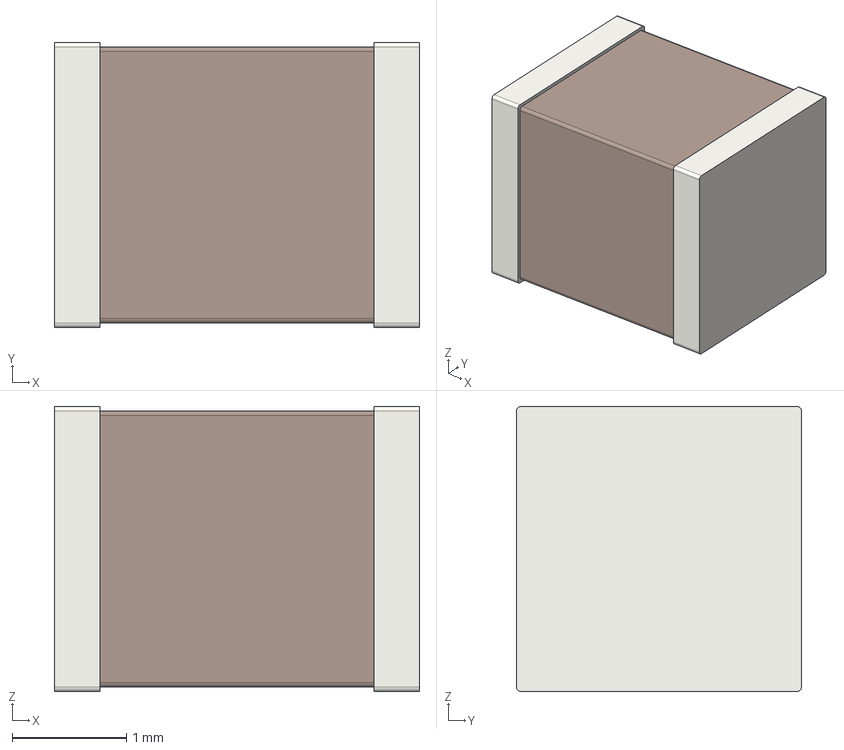
[picture p144: CAD file, 2026-09-30]
datasheets/discrete-and-power/KICAD-C_1210_3225Metric-3D.step
3.20 x 2.50 x 2.50 mm
