jeffmhopkins/Woody/mechanical/export/oak-bottom.dxf

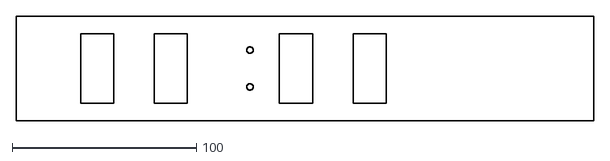
[picture p145: CAD file, 2026-09-30]
mechanical/export/oak-bottom.dxf
313.8 x 57.0
