jeffmhopkins/Woody/datasheets/connectors/NEUTRIK-NE8FDP-3D.stp

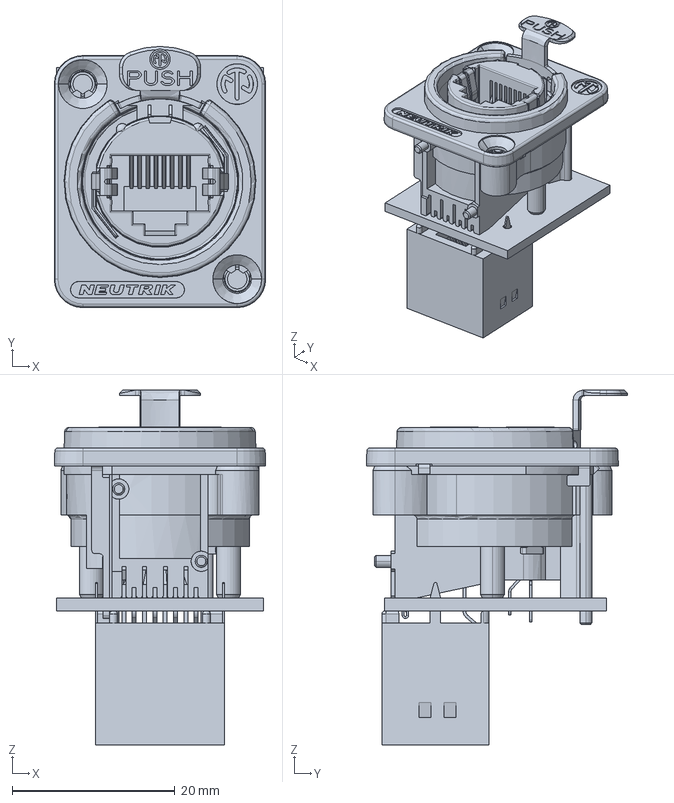
[picture p146: CAD file, 2026-09-30]
datasheets/connectors/NEUTRIK-NE8FDP-3D.stp
26.0 x 32.1 x 43.7 mm
