jeffmhopkins/Woody/datasheets/discrete-and-power/RECOM-R-78E-1.0-SIP3-3D.step

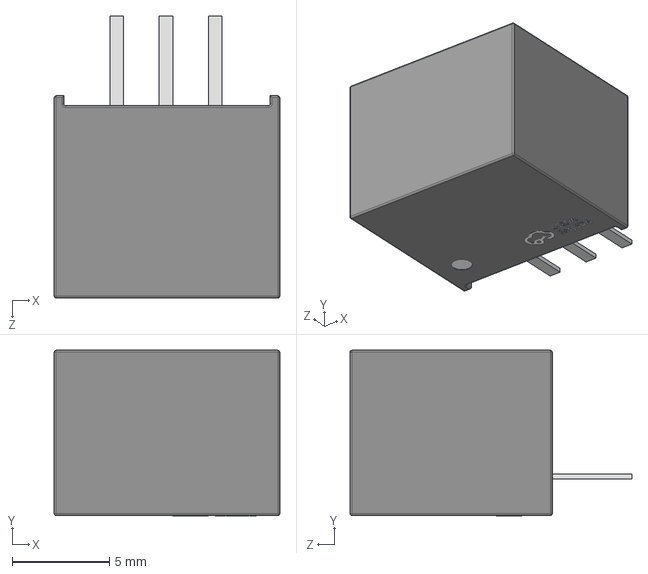
[picture p147: CAD file, 2026-09-30]
datasheets/discrete-and-power/RECOM-R-78E-1.0-SIP3-3D.step
11.6 x 8.51 x 14.5 mm
