jeffmhopkins/Woody/mechanical/export/plate-bottom.dxf

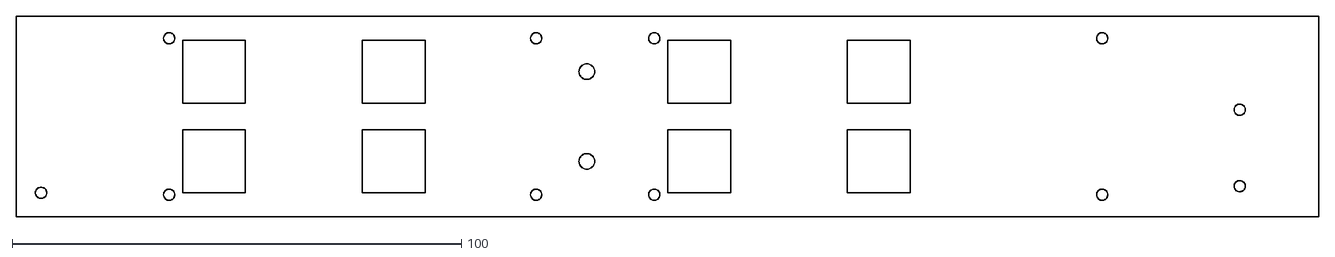
[picture p148: CAD file, 2026-09-30]
mechanical/export/plate-bottom.dxf
289.9 x 44.6
