jeffmhopkins/Woody/datasheets/connectors/NEUTRIK-NE8FAH-DRAWING.dxf

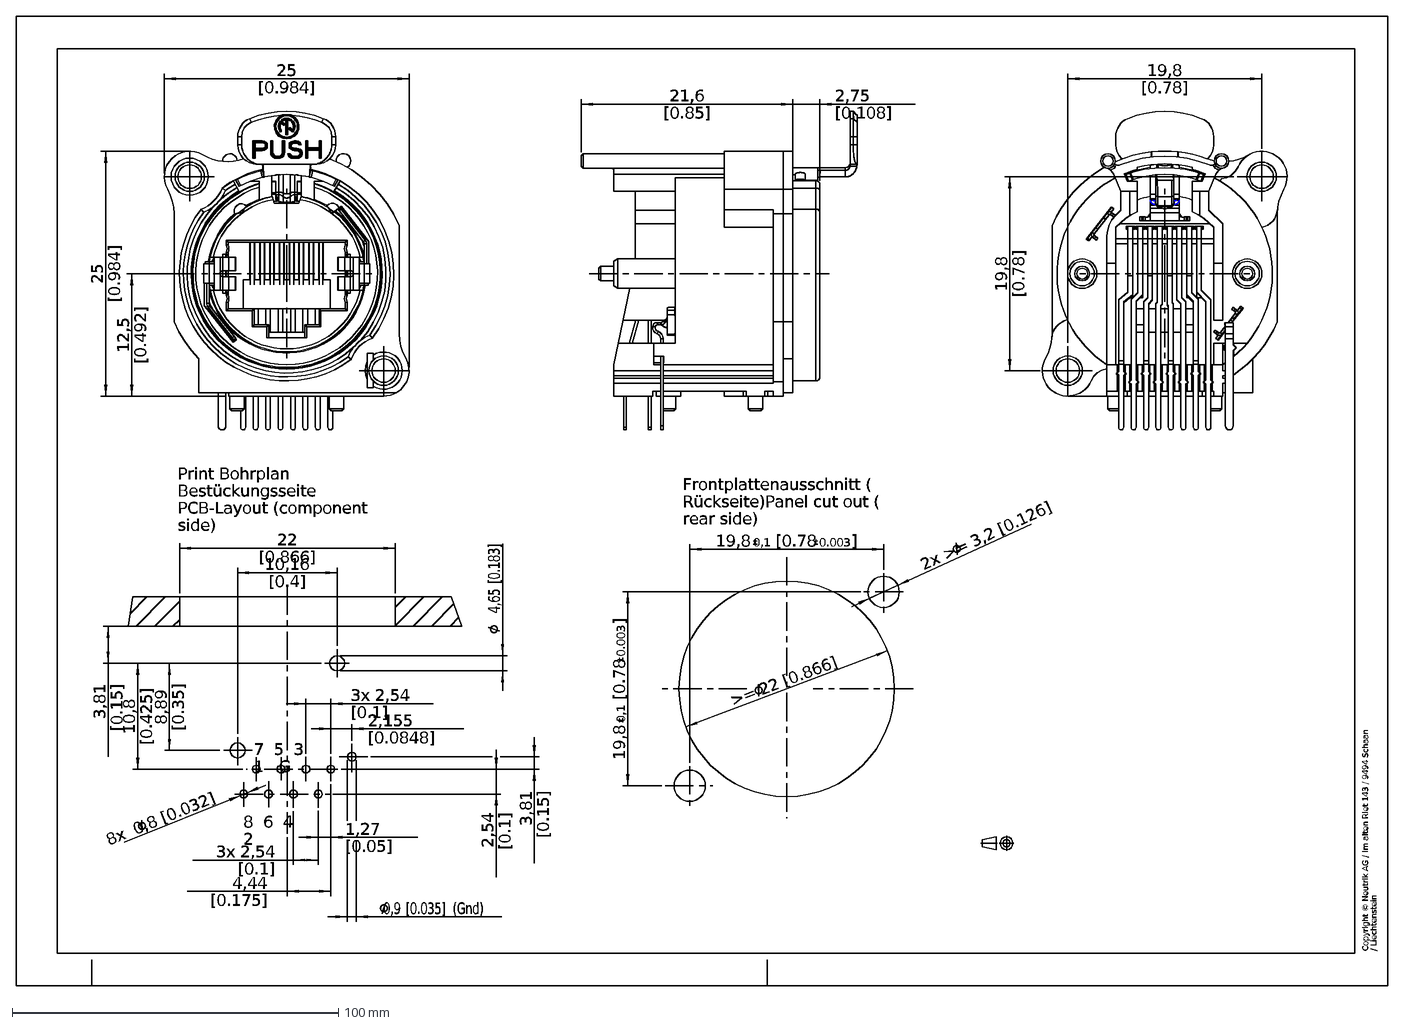
[picture p149: CAD file, 2026-09-30]
datasheets/connectors/NEUTRIK-NE8FAH-DRAWING.dxf
Copyright © Neutrik AG / Im alten Riet 143 / 9494 Schaan / Liechtenstein
12,5 [0.492]
25 [0.984]
21,6 [0.85]
2,75 [0.108]
19,8 [0.78]
3,81 [0.15]
8,89 [0.35]
10,8 [0.425]
22 [0.866]
10,16 [0.4]
2,155 [0.0848]
3x 2,54 [0.1]
8x [0.032]
4,44 [0.175]
1,27 [0.05]
2,54 [0.1]
>= [0.866]
19,8 0,1 [0.78 0.003 ]
2x >= [0.126]
Print Bohrplan Bestückungsseite PCB-Layout (component side)
Frontplattenausschnitt ( Rückseite) Panel cut out ( rear side)
7 5 3 1 G
8 6 4 2
