jeffmhopkins/Woody/datasheets/discrete-and-power/KICAD-CP_Radial_D5.0mm_P2.00mm-3D.step

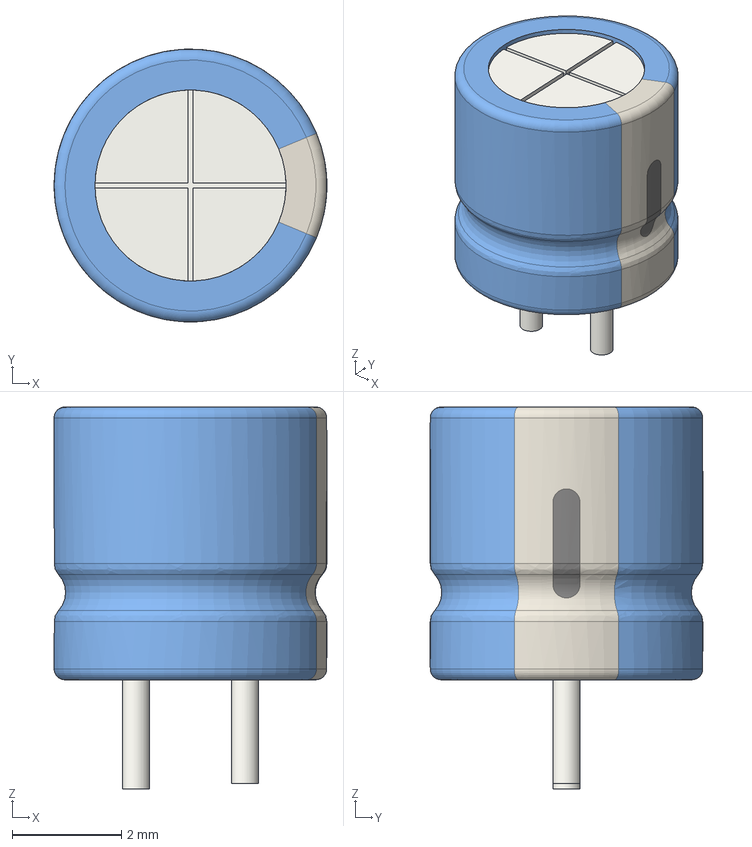
[picture p150: CAD file, 2026-09-30]
datasheets/discrete-and-power/KICAD-CP_Radial_D5.0mm_P2.00mm-3D.step
5.00 x 5.00 x 7.00 mm
