jeffmhopkins/Woody/datasheets/connectors/JST-B4B-XH-A-3D.step

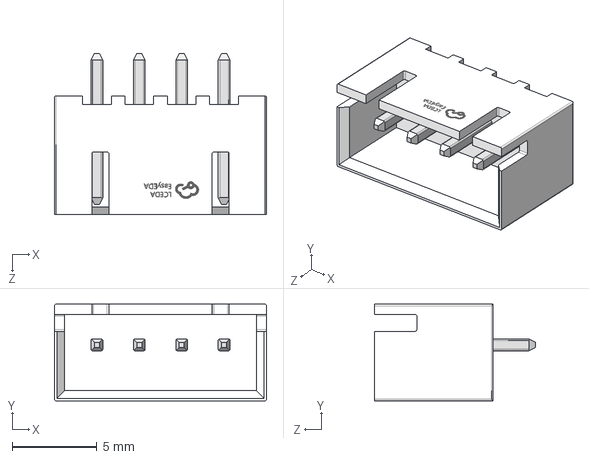
[picture p151: CAD file, 2026-09-30]
datasheets/connectors/JST-B4B-XH-A-3D.step
12.5 x 5.70 x 9.50 mm
