jeffmhopkins/Woody/datasheets/discrete-and-power/KICAD-D_SOD-323-3D.step

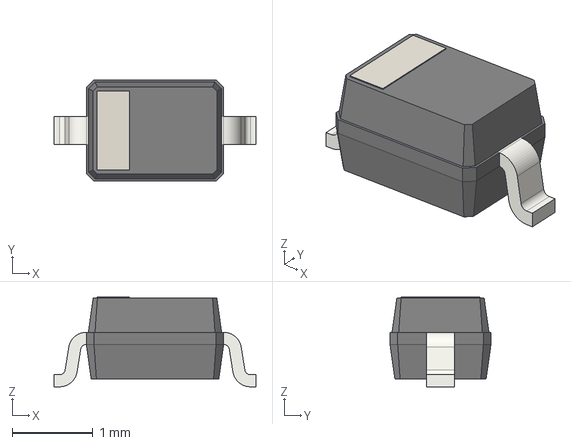
[picture p152: CAD file, 2026-09-30]
datasheets/discrete-and-power/KICAD-D_SOD-323-3D.step
2.50 x 1.25 x 1.11 mm
