jeffmhopkins/Woody/mechanical/export/oak-rebates.dxf

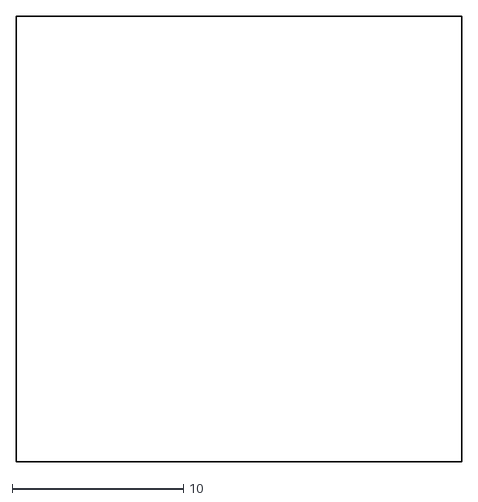
[picture p153: CAD file, 2026-09-30]
mechanical/export/oak-rebates.dxf
26.0 x 26.0
