jeffmhopkins/Woody/datasheets/connectors/NEUTRIK-NE8FAV-3D.stp

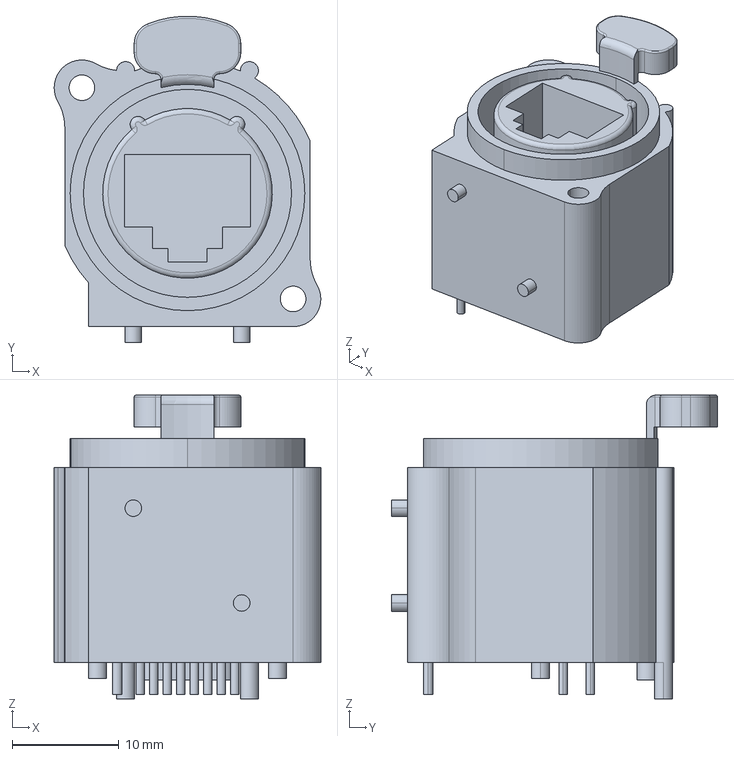
[picture p154: CAD file, 2026-09-30]
datasheets/connectors/NEUTRIK-NE8FAV-3D.stp
25.0 x 30.6 x 28.5 mm
