jeffmhopkins/Woody/datasheets/discrete-and-power/SMA-DO-214AC-GENERIC-3D.step

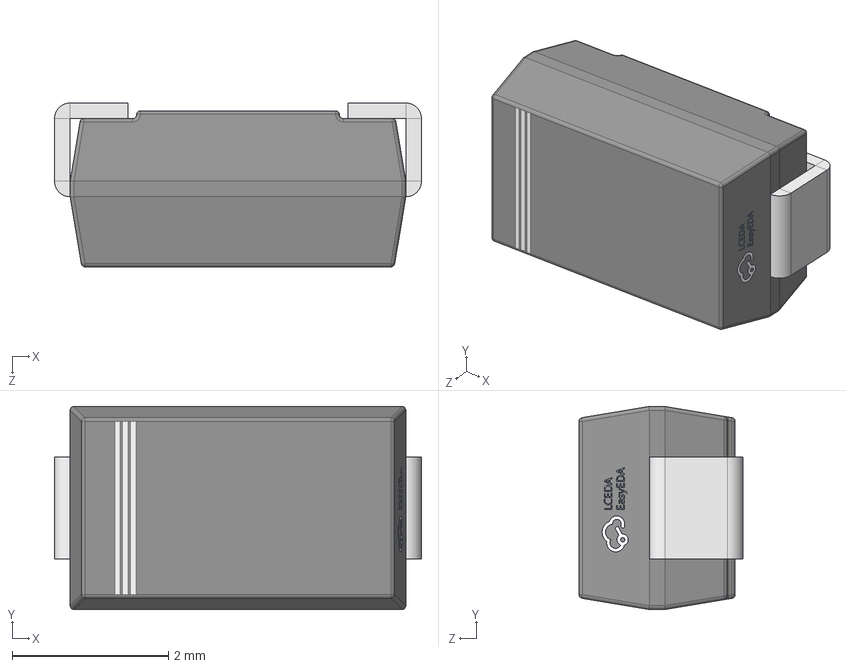
[picture p155: CAD file, 2026-09-30]
datasheets/discrete-and-power/SMA-DO-214AC-GENERIC-3D.step
4.70 x 2.60 x 2.10 mm
