jeffmhopkins/Woody/mechanical/export/plate-top.dxf

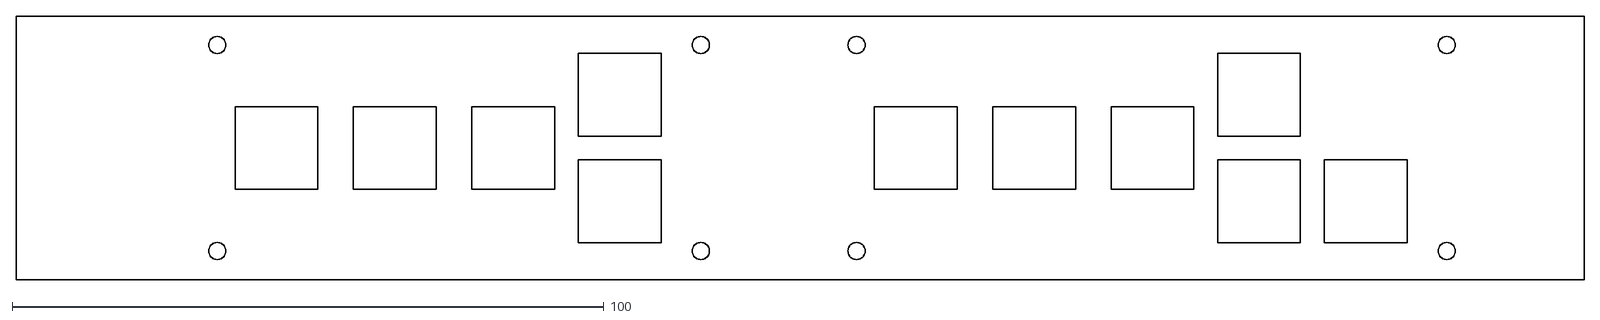
[picture p156: CAD file, 2026-09-30]
mechanical/export/plate-top.dxf
264.9 x 44.6
