jeffmhopkins/Woody/datasheets/connectors/GENERIC-RJ45-8P8C-PLUG-3D.step

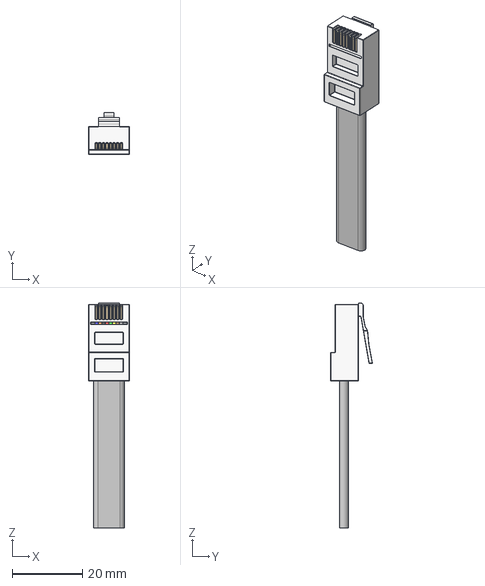
[picture p157: CAD file, 2026-09-30]
datasheets/connectors/GENERIC-RJ45-8P8C-PLUG-3D.step
11.7 x 11.9 x 64.0 mm
