jeffmhopkins/Woody/datasheets/discrete-and-power/KICAD-D_DO-41_SOD81_P10.16mm_Horizontal-3D.step

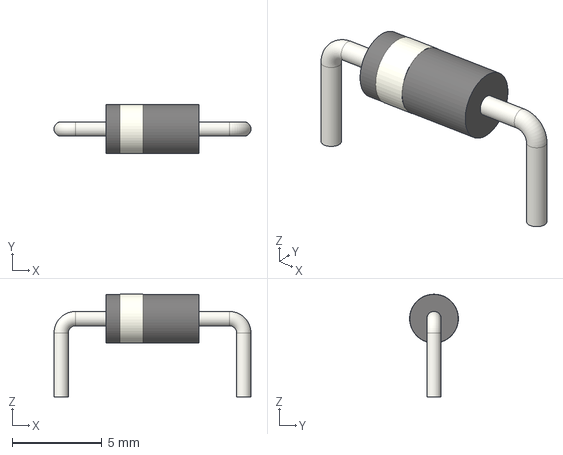
[picture p158: CAD file, 2026-09-30]
datasheets/discrete-and-power/KICAD-D_DO-41_SOD81_P10.16mm_Horizontal-3D.step
11.0 x 2.72 x 5.71 mm
