jeffmhopkins/Woody/mechanical/export/key-board-rh.dxf

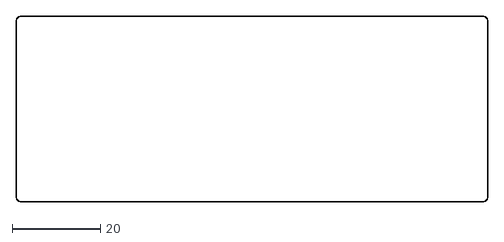
[picture p159: CAD file, 2026-09-30]
mechanical/export/key-board-rh.dxf
106.9 x 42.0
