jeffmhopkins/Woody/datasheets/connectors/KICAD-IDC-Header_2x08_P2.54mm_Vertical-3D.step

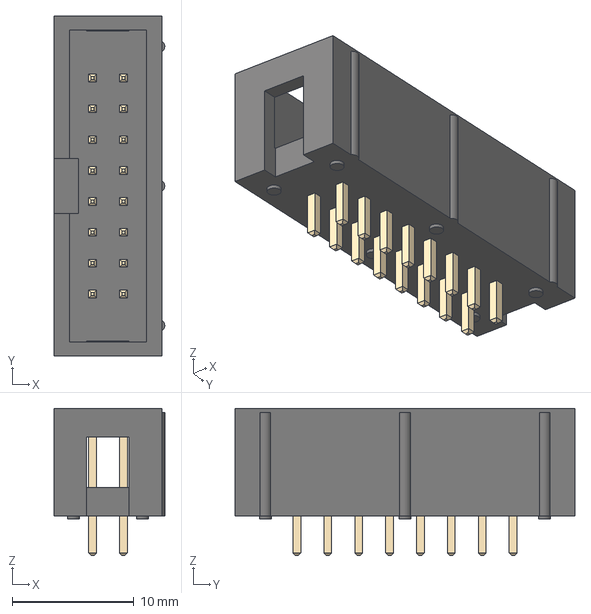
[picture p160: CAD file, 2026-09-30]
datasheets/connectors/KICAD-IDC-Header_2x08_P2.54mm_Vertical-3D.step
9.10 x 28.0 x 12.1 mm
