jeffmhopkins/Woody/mechanical/export/mouth-cap.dxf

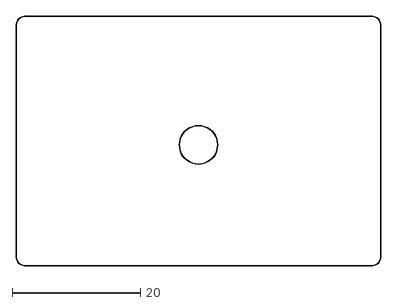
[picture p161: CAD file, 2026-09-30]
mechanical/export/mouth-cap.dxf
57.0 x 39.0
