jeffmhopkins/Woody/datasheets/connectors/HANXIA-HX-JN1.27-2x6-WZ-H4.9-3D.step

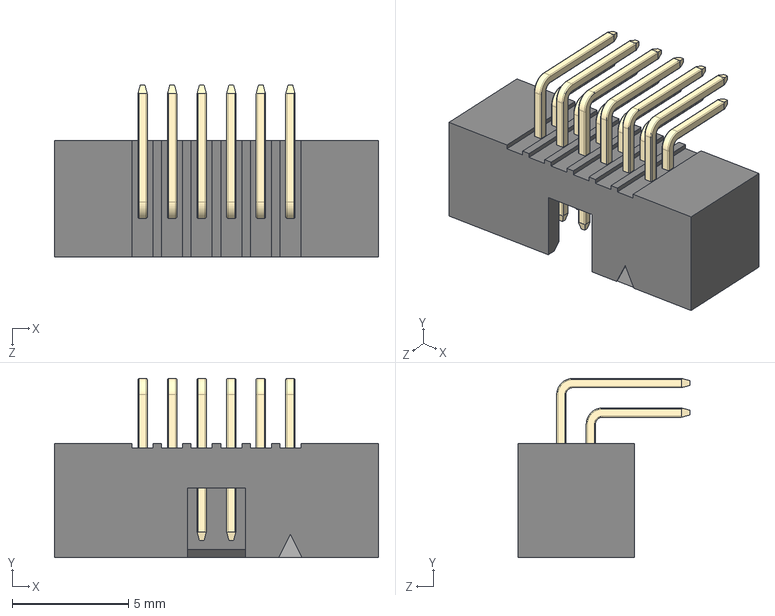
[picture p162: CAD file, 2026-09-30]
datasheets/connectors/HANXIA-HX-JN1.27-2x6-WZ-H4.9-3D.step
13.9 x 7.70 x 7.40 mm
