jeffmhopkins/Woody/datasheets/discrete-and-power/KICAD-Potentiometer_Bourns_3296W_Vertical-3D.step

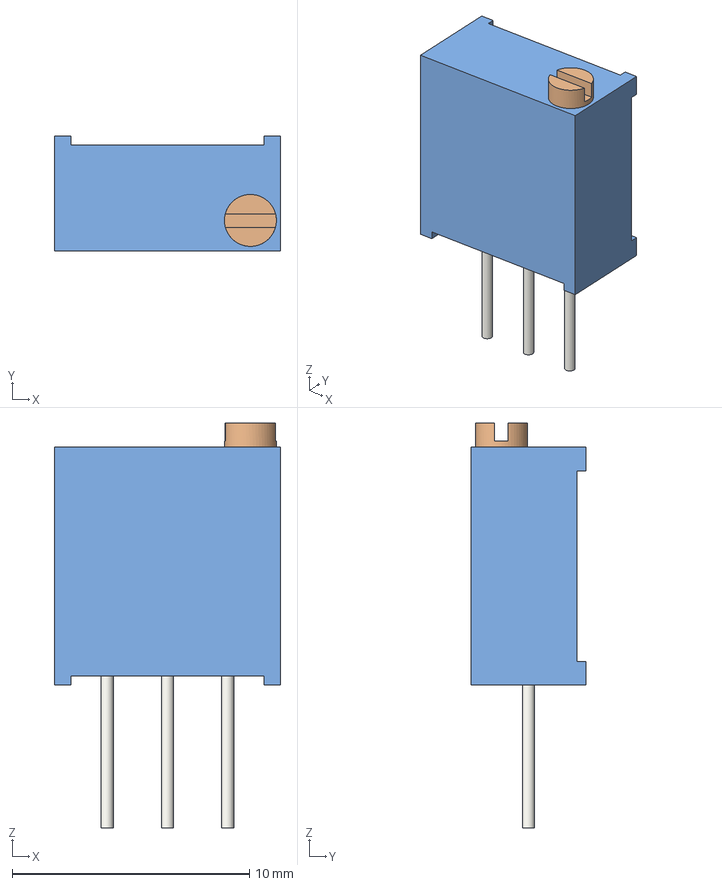
[picture p163: CAD file, 2026-09-30]
datasheets/discrete-and-power/KICAD-Potentiometer_Bourns_3296W_Vertical-3D.step
9.53 x 4.83 x 17.1 mm
