jeffmhopkins/Woody/datasheets/connectors/NEUTRIK-NE8FDX-P6-3D.stp

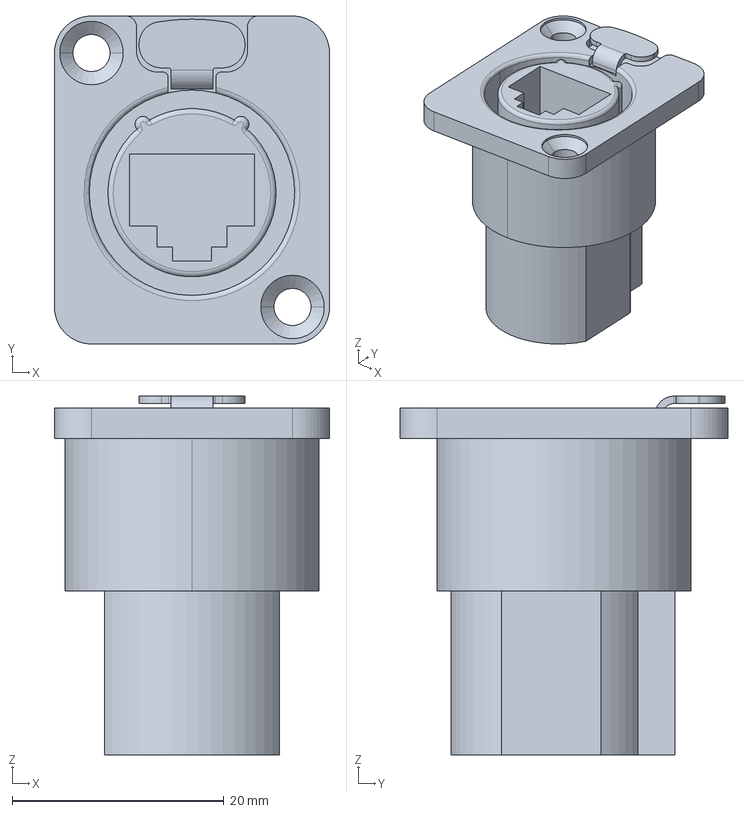
[picture p164: CAD file, 2026-09-30]
datasheets/connectors/NEUTRIK-NE8FDX-P6-3D.stp
26.0 x 31.0 x 33.9 mm
