jeffmhopkins/Woody/datasheets/discrete-and-power/KICAD-CP_Radial_D6.3mm_P2.50mm-3D.step

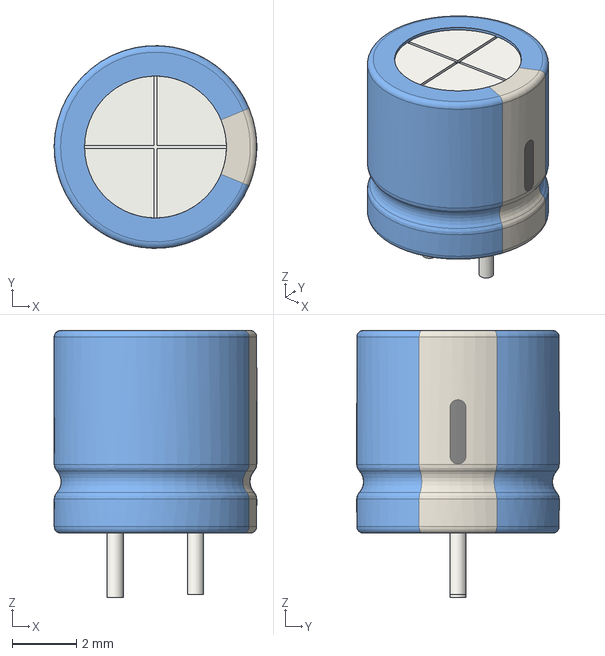
[picture p165: CAD file, 2026-09-30]
datasheets/discrete-and-power/KICAD-CP_Radial_D6.3mm_P2.50mm-3D.step
6.30 x 6.30 x 8.30 mm
