jeffmhopkins/Woody/datasheets/connectors/NEUTRIK-NE8MX6-3D.stp

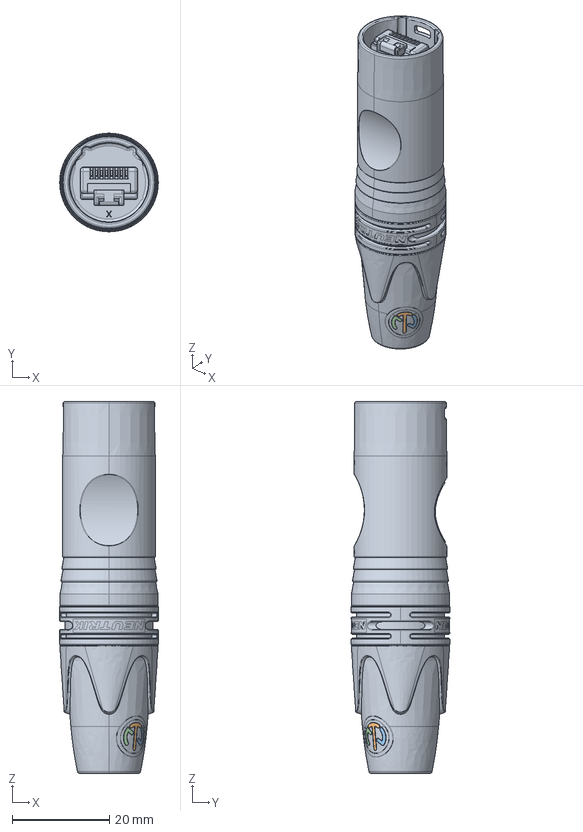
[picture p166: CAD file, 2026-09-30]
datasheets/connectors/NEUTRIK-NE8MX6-3D.stp
20.3 x 20.3 x 76.5 mm
