jeffmhopkins/Woody/datasheets/discrete-and-power/KICAD-SOT-23-3D.step

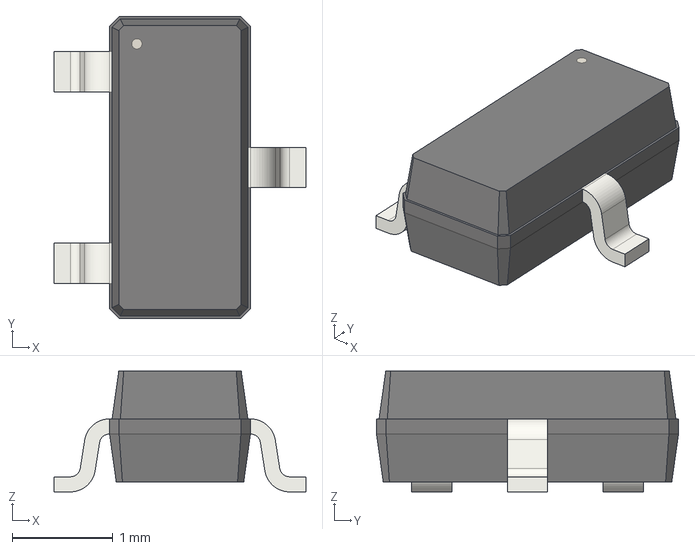
[picture p167: CAD file, 2026-09-30]
datasheets/discrete-and-power/KICAD-SOT-23-3D.step
2.50 x 3.00 x 1.20 mm
