jeffmhopkins/Woody/datasheets/connectors/XKB-X1270WR-2x12A-6TV01-3D.step

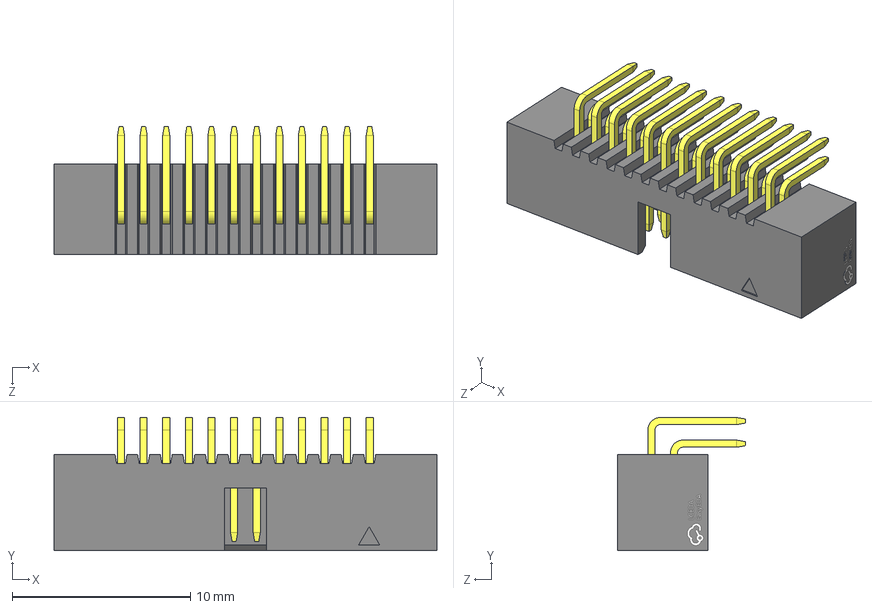
[picture p168: CAD file, 2026-09-30]
datasheets/connectors/XKB-X1270WR-2x12A-6TV01-3D.step
21.5 x 7.47 x 7.20 mm
