jeffmhopkins/Woody/datasheets/discrete-and-power/KICAD-D_SOD-123-3D.step

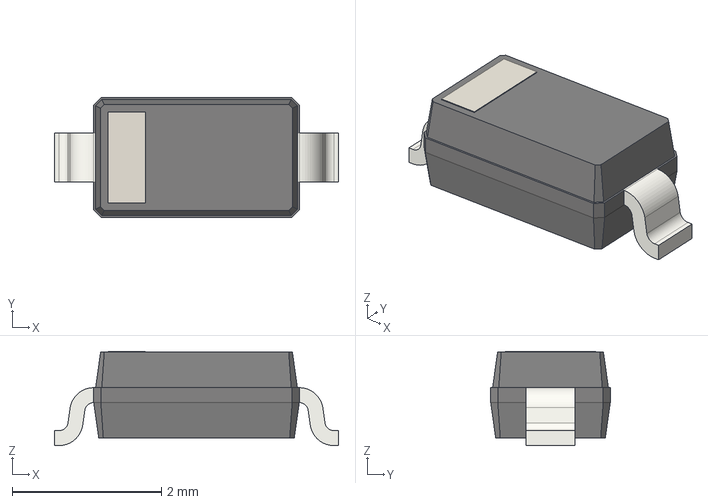
[picture p169: CAD file, 2026-09-30]
datasheets/discrete-and-power/KICAD-D_SOD-123-3D.step
3.80 x 1.60 x 1.26 mm
