jeffmhopkins/Woody/datasheets/connectors/SONGHUEI-R0904N-L25-BADPIXEL-3D.step

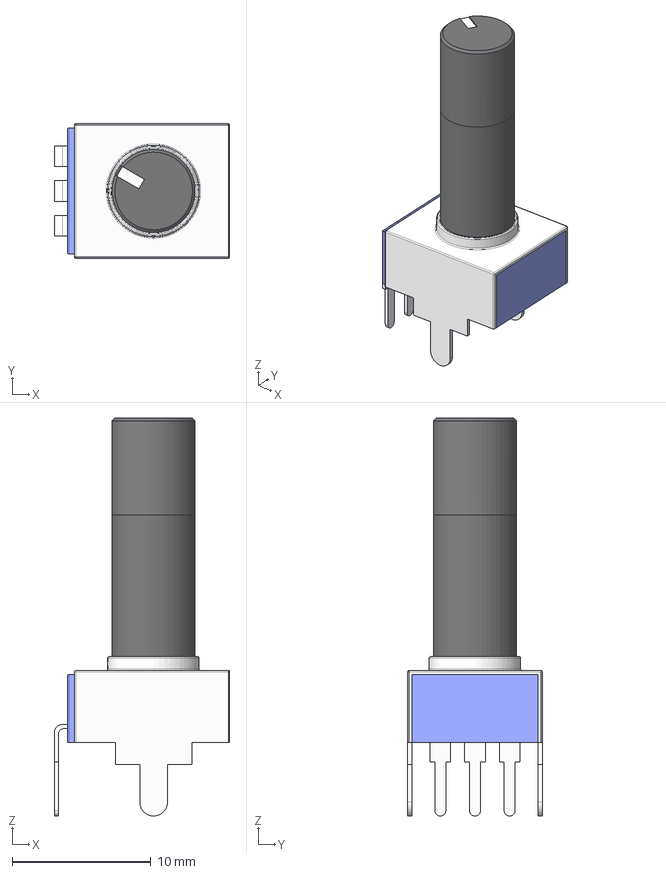
[picture p170: CAD file, 2026-09-30]
datasheets/connectors/SONGHUEI-R0904N-L25-BADPIXEL-3D.step
12.7 x 9.70 x 28.7 mm
