jeffmhopkins/Woody/datasheets/connectors/NEUTRIK-NE8FDV-3D.stp

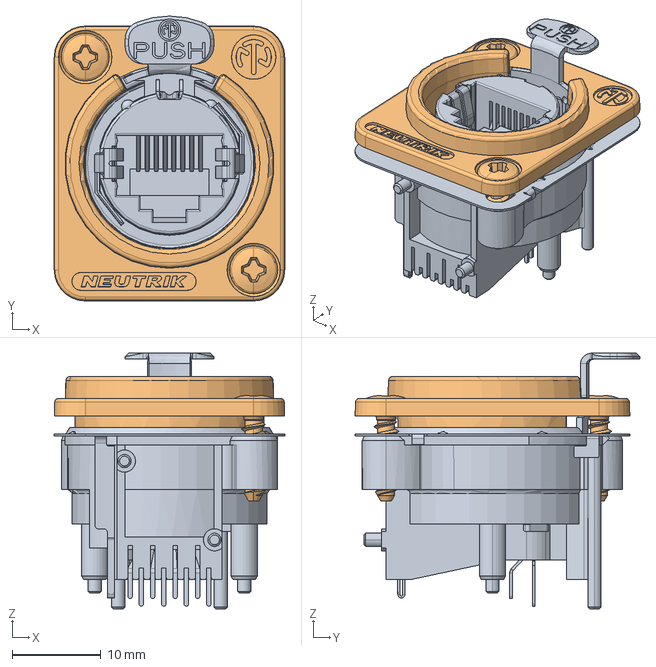
[picture p171: CAD file, 2026-09-30]
datasheets/connectors/NEUTRIK-NE8FDV-3D.stp
26.0 x 32.1 x 28.9 mm
NE8FDV
NE8FD
