jeffmhopkins/Woody/datasheets/connectors/MOLEX-PICOBLADE-53261-0871-KICAD-3D.step

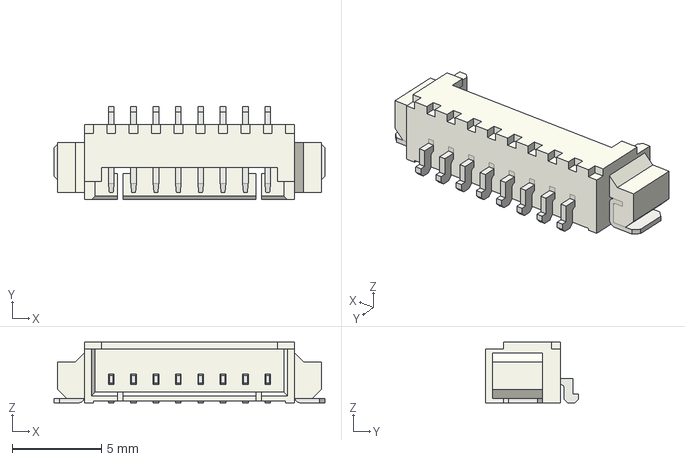
[picture p172: CAD file, 2026-09-30]
datasheets/connectors/MOLEX-PICOBLADE-53261-0871-KICAD-3D.step
15.2 x 5.20 x 3.40 mm
