jeffmhopkins/Woody/datasheets/connectors/THONKICONN-PJ398SM-BADPIXEL-3D.step

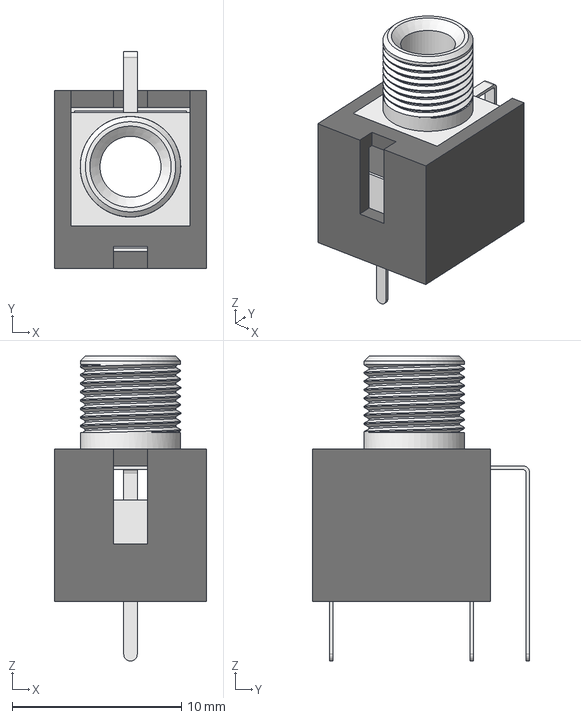
[picture p173: CAD file, 2026-09-30]
datasheets/connectors/THONKICONN-PJ398SM-BADPIXEL-3D.step
9.00 x 12.8 x 18.0 mm
