jeffmhopkins/Woody/datasheets/connectors/WCON-3131-12RG0BK00T1-3D.step

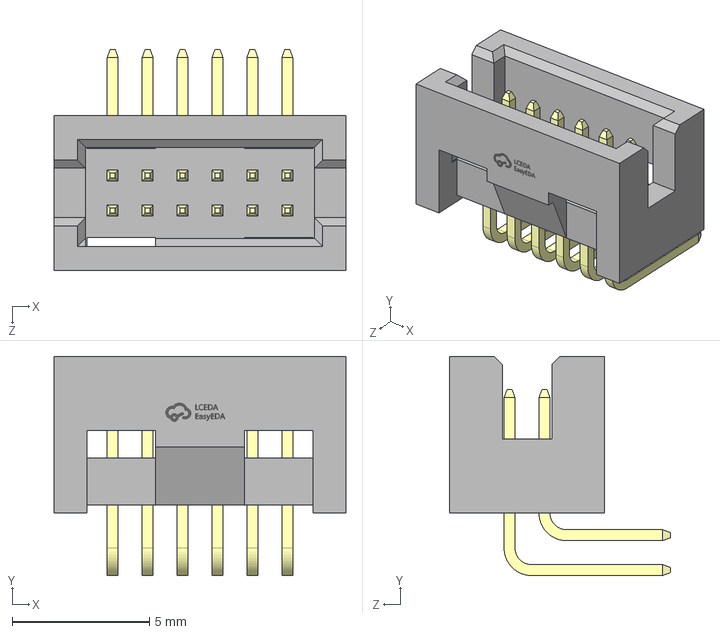
[picture p174: CAD file, 2026-09-30]
datasheets/connectors/WCON-3131-12RG0BK00T1-3D.step
10.6 x 7.97 x 8.05 mm
