jeffmhopkins/Woody/datasheets/connectors/HANXIA-HX-PZ2.54-1x8P-WZ-3D.step

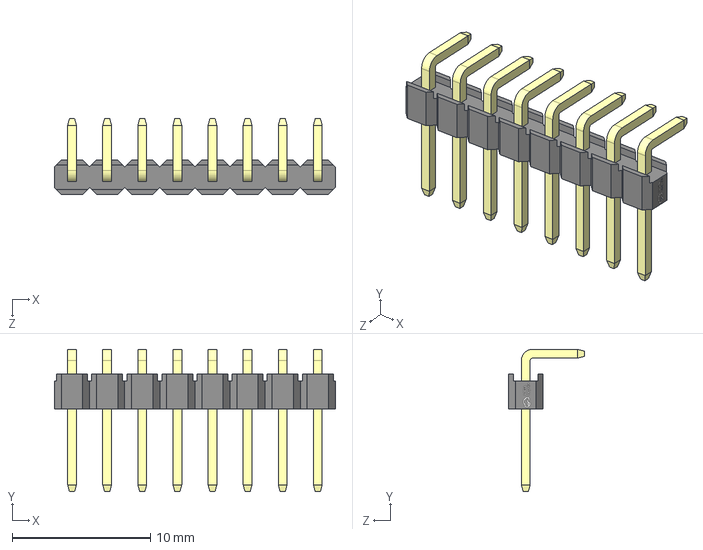
[picture p175: CAD file, 2026-09-30]
datasheets/connectors/HANXIA-HX-PZ2.54-1x8P-WZ-3D.step
20.3 x 10.3 x 5.50 mm
