jeffmhopkins/Woody/datasheets/connectors/JST-GH-SM08B-GHS-TB-KICAD-3D.step

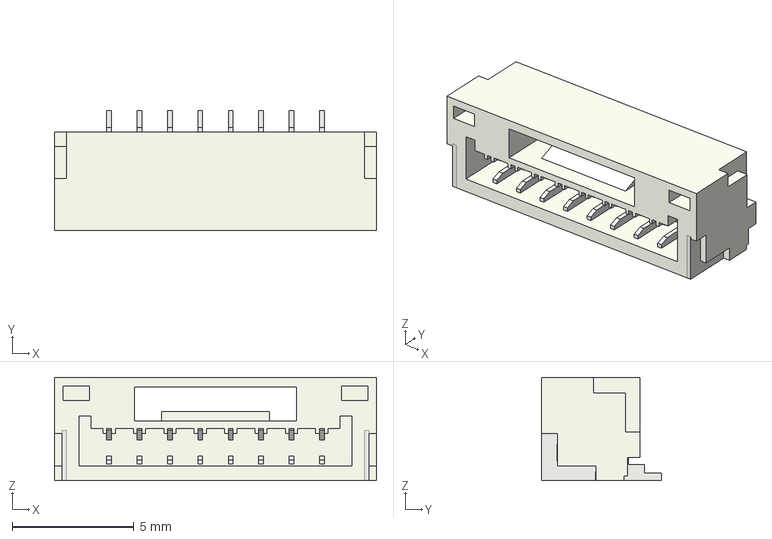
[picture p176: CAD file, 2026-09-30]
datasheets/connectors/JST-GH-SM08B-GHS-TB-KICAD-3D.step
13.2 x 4.95 x 4.25 mm
