jeffmhopkins/Woody/datasheets/connectors/GENERIC-USB-C-PLUG-OVERMOULD-3D.step

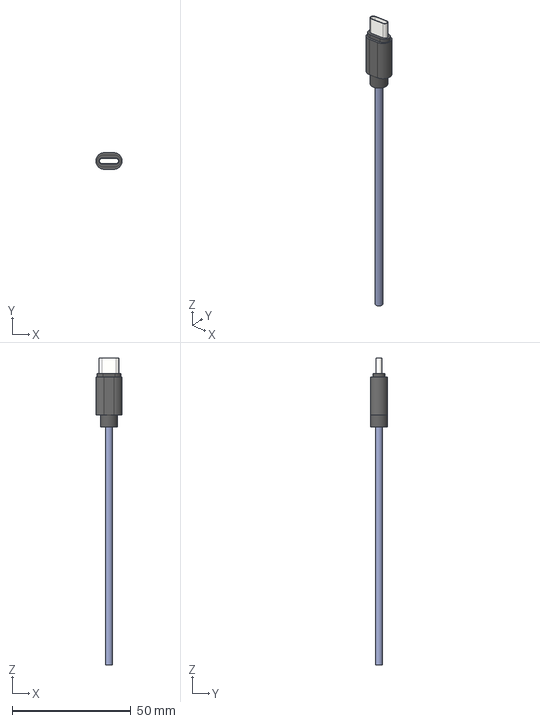
[picture p177: CAD file, 2026-09-30]
datasheets/connectors/GENERIC-USB-C-PLUG-OVERMOULD-3D.step
11.0 x 7.00 x 129.0 mm
