jeffmhopkins/Woody/datasheets/connectors/NEUTRIK-NE8FDV-DRAWING.dxf

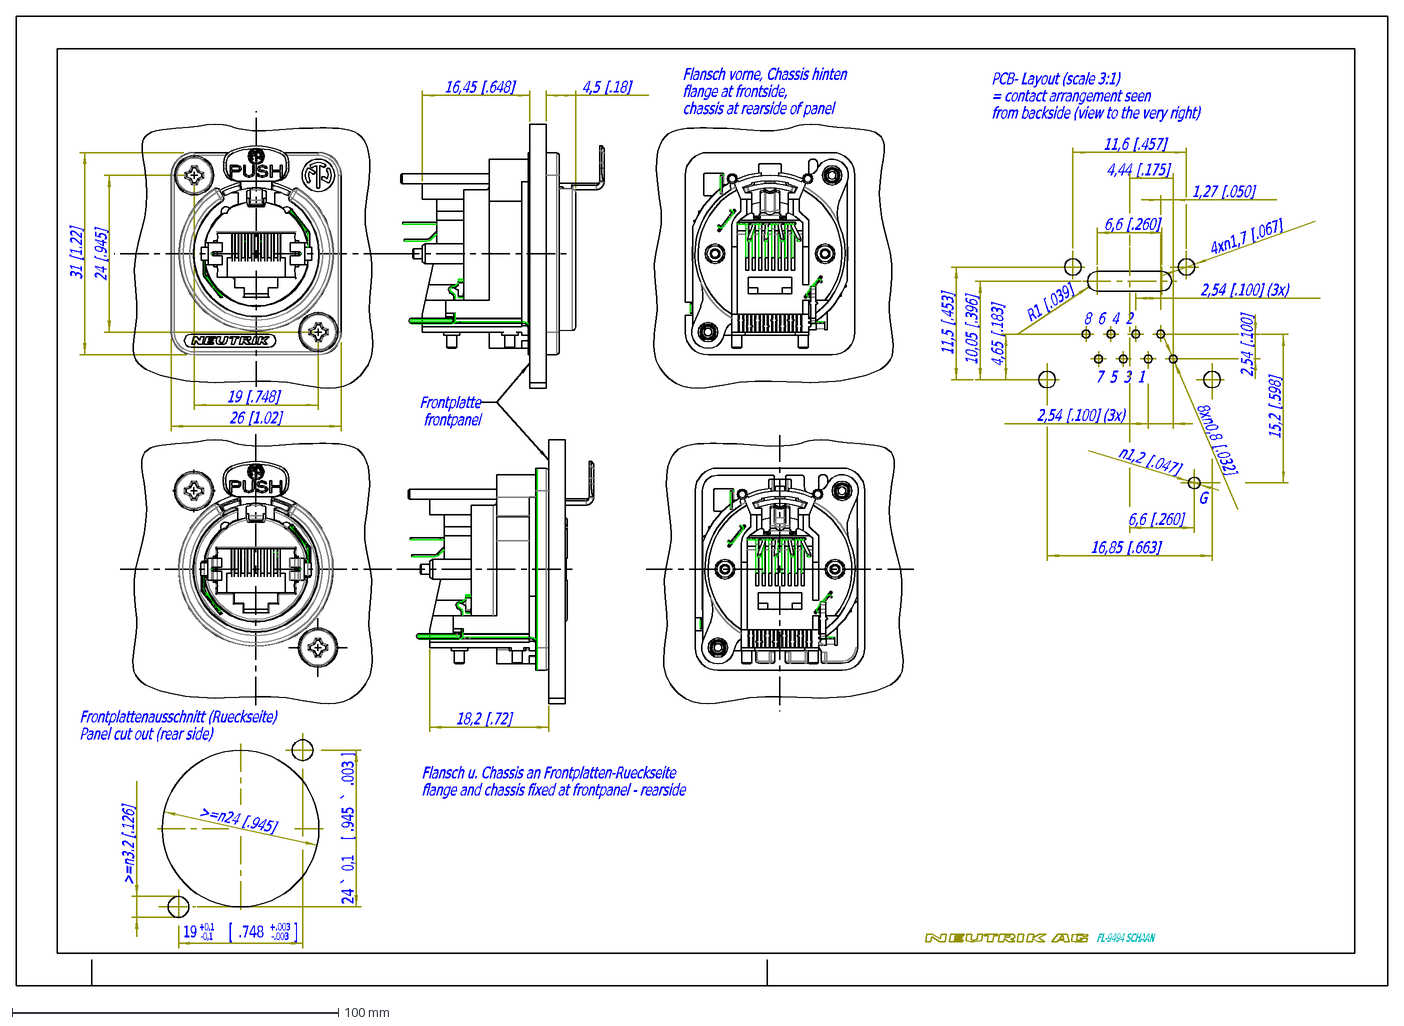
[picture p178: CAD file, 2026-09-30]
datasheets/connectors/NEUTRIK-NE8FDV-DRAWING.dxf
FL-9494 SCHAAN
24
0,1
[
.945
.003
]
+0,1
+.003
19
-0,1
.748
-.003
11,6 [.457]
4,44 [.175]
1,27 [.050]
16,85 [.663]
6,6 [.260]
2,54 [.100] (3x)
2,54 [.100]
15,2 [.598]
4,65 [.183]
11,5 [.453]
24 [.945]
19 [.748]
16,45 [.648]
10,05 [.396]
R1 [.039]
18,2 [.72]
26 [1.02]
31 [1.22]
4,5 [.18]
Frontplatte frontpanel
PCB- Layout (scale 3:1) = contact arrangement seen from backside (view to the very right)
8 6 4 2
7 5 3 1
G
Flansch vorne, Chassis hinten flange at frontside, chassis at rearside of panel
Flansch u. Chassis an Frontplatten-Rueckseite flange and chassis fixed at frontpanel - rearside
Frontplattenausschnitt (Rueckseite) Panel cut out (rear side)
