jeffmhopkins/Woody/datasheets/connectors/ADAFRUIT-4056-PANEL-MOUNT-USB-C-3D.step

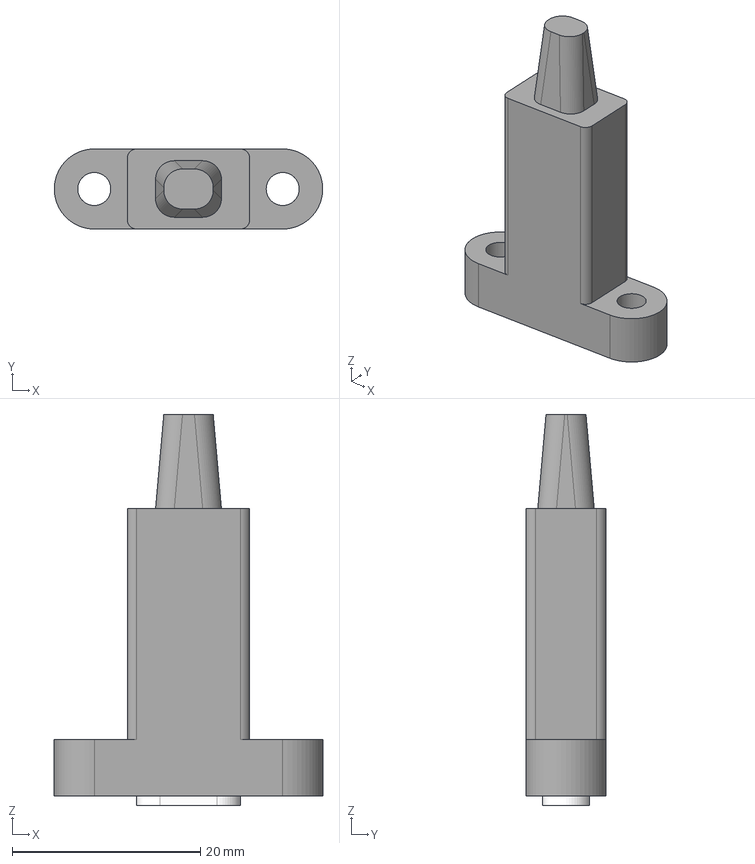
[picture p179: CAD file, 2026-09-30]
datasheets/connectors/ADAFRUIT-4056-PANEL-MOUNT-USB-C-3D.step
28.5 x 8.50 x 41.5 mm
