jeffmhopkins/Woody/datasheets/connectors/NEUTRIK-NE8MX-3D.stp

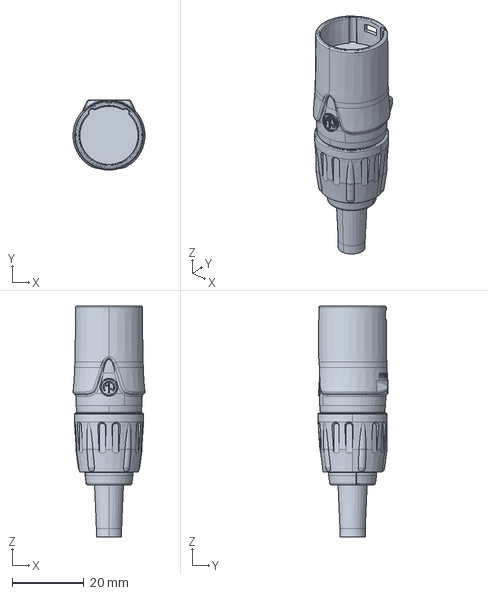
[picture p180: CAD file, 2026-09-30]
datasheets/connectors/NEUTRIK-NE8MX-3D.stp
20.1 x 19.6 x 64.5 mm
