jeffmhopkins/Woody/datasheets/connectors/NE8FDP.dxf

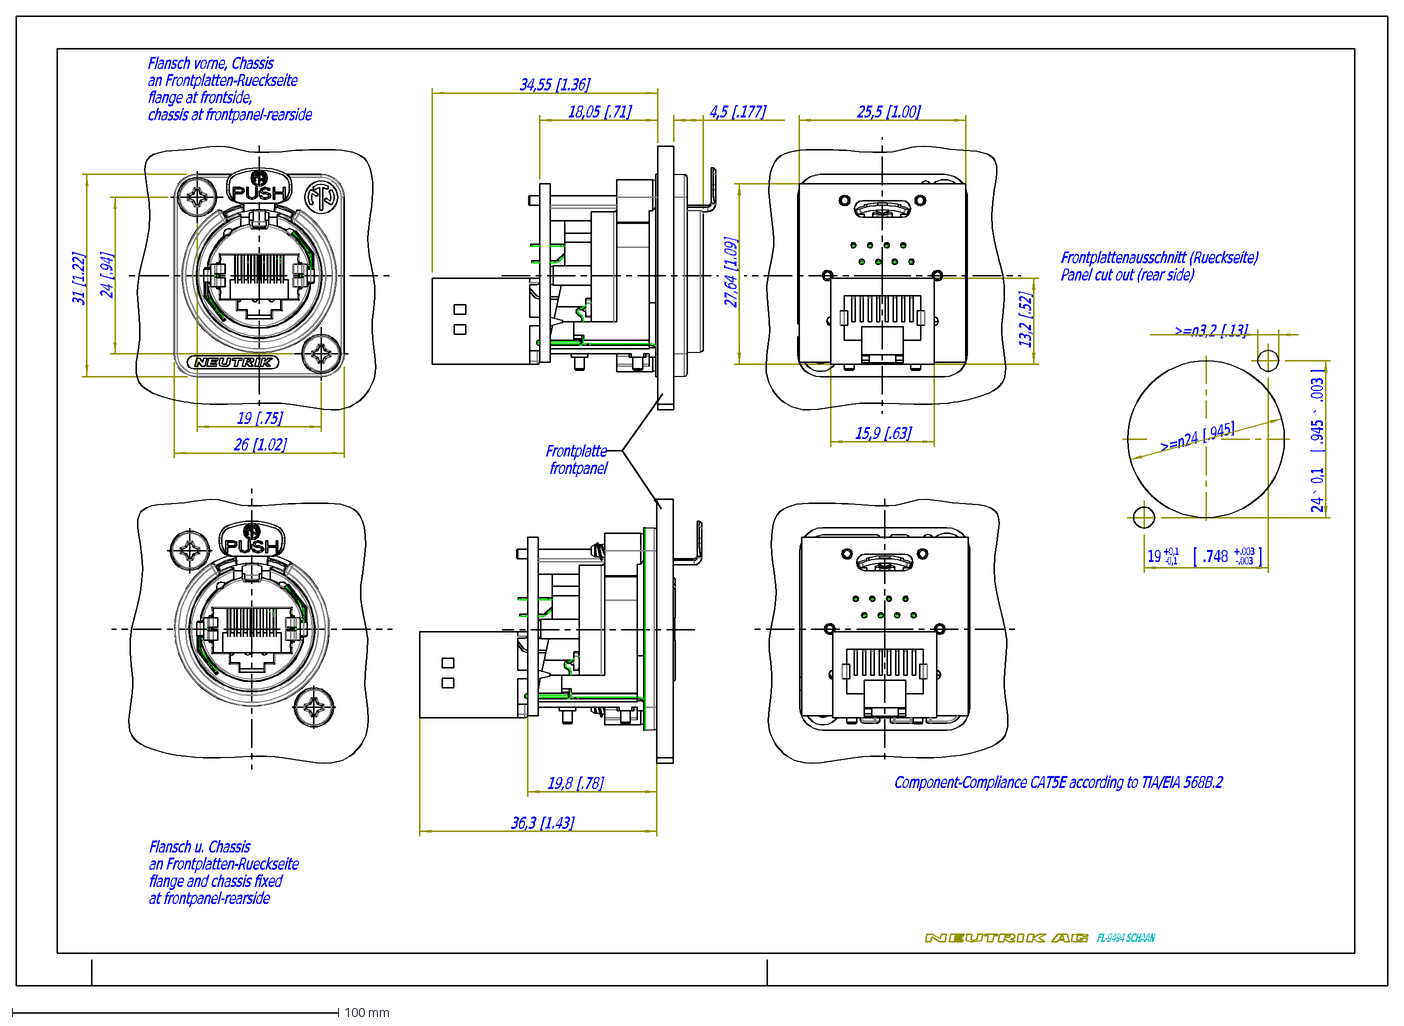
[picture p181: CAD file, 2026-09-21]
datasheets/connectors/NE8FDP.dxf
FL-9494 SCHAAN
36,3 [1.43]
19,8 [.78]
24 [.94]
19 [.75]
31 [1.22]
26 [1.02]
19
+0,1
-0,1
[
.748
+.003
-.003
]
24
0,1
.945
.003
34,55 [1.36]
18,05 [.71]
25,5 [1.00]
27,64 [1.09]
15,9 [.63]
13,2 [.52]
4,5 [.177]
Flansch u. Chassis an Frontplatten-Rueckseite flange and chassis fixed at frontpanel-rearside
Component-Compliance CAT5E according to TIA/EIA 568B.2
Flansch vorne, Chassis an Frontplatten-Rueckseite flange at frontside, chassis at frontpanel-rearside
Frontplatte frontpanel
Frontplattenausschnitt (Rueckseite) Panel cut out (rear side)
