jeffmhopkins/Woody/mechanical/cad/generated/params.scad

// GENERATED by tools/cad.py params - DO NOT EDIT.
// Sources: config/key-layout.yaml, config/body.yaml. Edit those, then run
// `python3 tools/cad.py build`; `check` fails on a hand edit here.
// Units: mm. Every value below cites its source in the YAML it came from.

// ---- config/key-layout.yaml :: meta
envelope_length = undef;
envelope_width = 57;
envelope_thickness = 39;
plate_cutout = 14.0;
plate_thickness = 1.2;  // `plate-thickness`, config/figures.yaml

// ---- config/key-layout.yaml :: keys
// [id, face, x, y, rotation, hand, cluster, role]; x/y undef = not yet placed (M2/M3)
keys = [
  ["LH1", "top", undef, undef, 0, "left", "left_hand", "note"],
  ["LH2", "top", undef, undef, 0, "left", "left_hand", "note"],
  ["LH3", "top", undef, undef, 0, "left", "left_hand", "note"],
  ["LH4", "top", undef, undef, 0, "left", "left_hand", "note"],
  ["LH5", "top", undef, undef, 0, "left", "left_hand", "note"],
  ["LT1", "bottom", undef, undef, 180, "left", "left_thumb", "note"],
  ["LT2", "bottom", undef, undef, 0, "left", "left_thumb", "note"],
  ["LT3", "bottom", undef, undef, 180, "left", "left_thumb", "note"],
  ["LT4", "bottom", undef, undef, 0, "left", "left_thumb", "note"],
  ["RH1", "top", undef, undef, 0, "right", "right_hand", "note"],
  ["RH2", "top", undef, undef, 0, "right", "right_hand", "note"],
  ["RH3", "top", undef, undef, 0, "right", "right_hand", "note"],
  ["RH4", "top", undef, undef, 0, "right", "right_hand", "note"],
  ["RH5", "top", undef, undef, 0, "right", "right_hand", "note"],
  ["RH6", "top", undef, undef, 0, "right", "right_hand", "note"],
  ["RT1", "bottom", undef, undef, 180, "right", "right_thumb", "control"],
  ["RT2", "bottom", undef, undef, 0, "right", "right_thumb", "control"],
  ["RT3", "bottom", undef, undef, 180, "right", "right_thumb", "control"],
  ["RT4", "bottom", undef, undef, 0, "right", "right_thumb", "control"]
];
keys_placed = 0;  // of 19
spare_switch_cutouts = 2;

// ---- config/body.yaml
stack_cap_clear = 0.75;  // tbd; keycap to oak-top hole, per side. Must beat oak's cross-grain movement across one hole, which ADR 0009 puts at 1-1.5 % [calc: 1.5 % of 18 mm = 0.27 mm]
stack_cap_holes = "slot";  // tbd; individual = one hole per cap in the oak top; slot = one slot per hand (and in the oak bottom one per thumb group either side of a rest), so pitch is limited by cap-to-cap clearance rather than by an oak web between holes
stack_side_t = 4.0;  // nominal; [adr] ADR 0009 mass table - 'Acrylic sides, 2 x 4 mm'. Now a single sheet standing in the oak grooves
stack_edge_r = 1.5;  // tbd; a sanded roundover [owner]; under the 2 mm lip outside each groove (side_inset), so the lip keeps a flat beside the acrylic
stack_side_inset = 2.0;  // tbd; oak lip outside each groove. Every mm here comes off the interior width twice
stack_groove_depth = 3.0;  // tbd; placeholder - half the oak panel, leaving half under the groove
stack_groove_clear = 0.2;  // tbd; per side of the acrylic, so the lid lifts off; acrylic sheet thickness varies [from memory]
ends_mouth_cap_t = 6.0;  // tbd; OAK since 2026-09-26 (owner: replace the acrylic mouth cap with the wood; ADR 0009 kept that open - 'same cut, same fixings, different sheet') - the oak top's stock, as the tail cap
ends_tail_cap_t = 6.0;  // tbd; ADR 0009 end-cap table: oak - so the oak top's stock
ends_tube_hole_d = 6.0;  // tbd; ADR 0003: tube bore and OD are settled at E2
layout_mouth_extra = 10.0;  // tbd; owner: 'a little extra near the mouth' - oak between the mouth cap's inside face and the first cap
layout_tail_clear = 3.0;  // tbd; clearance from the last key board to the etherCON body - the connector space the owner asked for is its depth plus this
layout_underside_clear = 3.0;  // tbd; clearance between the mouth cap and the first thumb recess, and from the last thumb recess to the tail cap
layout_lh_gaps = [20.0, 20.0, 18.0, 0.0];  // nominal; [research] soprano recorder L1-L2-L3 21.0/22.3, D whistle 20/20; pad widths put touching fingers 15-22 apart (P5 F - P95 M). 18 to the little-finger keys (soprano R3-R4 18.0; 1.5 mm between MT165 caps). The final 0 is the side-by-side pair LH4 / LH5 (owner, 2026-09-26)
layout_lh_offsets = [0.0, 0.0, 0.0, -9.0, 9.0];  // tbd; LH1-3 on the centreline; LH4 / LH5 the little finger's side-by-side pair, one cap pitch apart across the body, centred so both switch bodies stay inside the plate
layout_rh_offsets = [0.0, 0.0, 0.0, -9.0, 9.0, -9.0];  // tbd; RH1-3 on the centreline; RH4 / RH5 the little finger's side-by-side pair, centred as LH4 / LH5; RH6 the single key below it, IN LINE with RH4 - the pair key on the player's right, the recorder's direction (owner, 2026-09-26)
layout_equal_bands = true;  // settled; owner, 2026-09-26: 'copy the same space above the left keys to between the hands and at the bottom'. Since the matrix was centred (same day) it equalizes the mouth end and the space between the hands only; the tail is sized by its own contents
layout_gap_matches_matrix = true;  // settled; owner, 2026-09-26: the gap between the key groups is the same as the gap from the last keys to the LED matrix - clear space, cap edge to cap edge and cap edge to window edge. Overrides equal_bands for the gap; equal_bands then only sets the mouth end, and gap stays a minimum
layout_matrix_centred = true;  // settled; owner, 2026-09-26: centre the LED matrix in the space after the keys, and let only the tail grow for it
layout_gap = 50.0;  // nominal; [adr] ADR 0009 length table - the U-bolt band. A MINIMUM while equal_bands is on
layout_rh_gaps = [20.0, 20.0, 18.0, 0.0, 18.0];  // nominal; [research] as lh_gaps; soprano R1-R2-R3 20.8/20.1, R3-R4 18.0. A 0 GAP IS A SIDE-BY-SIDE PAIR: RH4 / RH5 share the first little-finger position, RH6 is the single key one step further down (owner, 2026-09-26)
layout_lt_rest_under = "LH2";  // tbd; the left thumb rest is directly under the middle-finger key (owner, 2026-09-26); LH2 is the middle finger on the index-middle-ring order key-layout.yaml assumes until M2 assigns fingers
layout_lt_rest = 40.0;  // tbd; the LT1/LT2 row to the LT3/LT4 row, centre to centre, across the thumb rest: about a thumb pad clear between the cap holes. Each row's two keys are at the top keys' pitch (owner, 2026-09-26)
layout_rt_rest_under = "RH2";  // tbd; the right thumb rest is directly under the middle-finger key (owner, 2026-09-26); RH2 on the same assumption as lt_rest_under
layout_rt_rest = 40.0;  // tbd; the RT1/RT2 row to the RT3/RT4 row, centre to centre, across the thumb rest - the same as the left thumb's. Each row's two keys are at the top keys' pitch (owner, 2026-09-26)
switch_stem_top_above_seat = 6.4;  // nominal; the MX cross stem's top at rest, above the seat: 6.38 in the front elevation and 6.38 in the side one (3.35 to the housing top, the stem ~3.03 over it), SCALED off Gateron KS-33H10B050NN-Y24 sheet 6 - both views to scale within 0.03 on their dimensioned 13.75, 14.00 and 5.85 [scaled, datasheets/mechanical/GATERON-KS-33-VENDOR-SPEC-DRAWING.pdf, 2026-09-28]. The third-party STEP's is higher (docs/reference/ks33-geometry.md); the vendor wins
switch_cover_w = 13.75;  // settled; [ds] Gateron KS-33H10B050NN-Y24 sheet 6, front elevation: the switch's widest part above the collar, tapering upward. The 14.70 latch span is BELOW the collar, in the plate slot - the third-party STEP draws its latches above it, so the model trims the switch's mesh to this above the collar
switch_cover_straight_h = 1.5;  // nominal; how far above the seat the cover stays switch.cover_w wide before it tapers [scaled, Gateron KS-33H10B050NN-Y24 sheet 6 front elevation rendered at 400 dpi, 40 px/mm on its 13.75, 2026-09-28]
switch_cover_top_w = 12.8;  // nominal; the cover's width at its top (switch.housing_top_above_seat), where it steps in to the 11.0 actuator [scaled, as switch.cover_straight_h]
switch_collar_t = 0.45;  // settled; [ds] Gateron KS-33H10B050NN-Y24 sheet 6, side elevation: the 15.0 x 15.0 collar's thickness, from the seat
switch_housing_top_above_seat = 3.35;  // settled; [ds] Gateron KS-33H10B050NN-Y24 sheet 6, side elevation: the housing's top face above the seat; only the stem and its actuator stand above it
switch_pole_tip_below_seat = 5.75;  // settled; [ds] Gateron KS-33H10B050NN-Y24 sheet 6, 5.75 +/-0.05 (the STEP says 5.70; the vendor wins)
switch_thumb_pcb_below_seat = 2.5;  // nominal; the main board's face nearest the thumb switches' seat, below it: against the thumb switches' housing bottom, as the key boards are (ADR 0022, ADR 0020 Amendment 6), held there by its mount on the bottom plate (ADR 0025) - the plate + hardware.kb_spacer_l [calc: 1.2 + 1.3], inside switch.pcb_below_seat_window; drc.echo 'main board mount sets its depth'
switch_pcb_below_seat = 2.5;  // nominal; THE KEY BOARDS' (the thumb switches' main board is switch.thumb_pcb_below_seat): the board top is pressed against the switches' housing bottom (owner, 2026-09-29; ADR 0020 Amendment 6), 2.50 +/-0.05 below the seat [ds GATERON-KS-33-VENDOR-SPEC-DRAWING.pdf sheet 6]. The mount holds it there: the stud's head is flush in the plate's top face and the spacer bears on its underside, so the board top sits the plate + hardware.kb_spacer_l below the seat [calc: 1.2 + 1.3]; drc.echo 'key-board mount sets the board depth' fails if this and the hardware disagree. Inside switch.pcb_below_seat_window
switch_keycap_top_above_seat = 9.0;  // tbd; the cap's top above the seat = switch.stem_top_above_seat + switch.keycap_boss_below_top - how deep the stem enters the socket, which nothing published gives; the vendor's height (switch.keycap_h) bounds only the cap itself. A guess inside that bracket
switch_total_travel = 3.0;  // settled; [ds] Gateron KS-33H10B050NN-Y24 sheet 6 - total travel 3.0 +/-0.2 mm
switch_keycap = 16.5;  // settled; [adr] ADR 0002 - MT165 16.5 x 16.5
switch_keycap_h = 3.5;  // nominal; MT165: 3.50 mm, skirt bottom to top - Tai-Hao's own dimension guide [datasheets/mechanical/TAIHAO-MT165-THCS-THT-DIMENSION-GUIDE.jpg]
switch_keycap_top_w = 15.4;  // tbd; the top face's width: the MT165's sides are drafted about 0.55 mm a side [scaled off datasheets/mechanical/TAIHAO-MT165-THCS-THT-DIMENSION-GUIDE.jpg, 2026-09-28]
switch_keycap_wall = 1.3;  // tbd; the skirt's wall at its bottom edge: 1.1-1.5 mm scaled off a reseller's underside photo [datasheets/mechanical/BEEKEEB-MT165-THCS-UNDERSIDE-COMPARISON.jpg; inferred, UNVERIFIED]. It sets the inner cavity the switch's housing and clips must fit in when the key is pressed
switch_keycap_top_t = 1.2;  // tbd; the top's thickness [from memory: no source]
switch_keycap_boss_below_top = 4.8;  // tbd; how far the MX cross socket's boss reaches below the cap's top: about 4.8 mm, so about 1.3 mm below the skirt [reseller copy, shop.talpkeyboard.com/products/mt165-mx-blank-1u-black and shop.beekeeb.jp/products/tai-hao-mt-165, 2026-09-28; method not stated, UNVERIFIED]. The boss rides on the stem and moves with it
switch_keycap_socket_d = 4.4;  // tbd; the socket boss's outside diameter: about 4.2-4.5 mm in a reseller's photo [shop.talpkeyboard.com, 2026-09-28; inferred, low confidence]
switch_cluster_pcb_w = 22.0;  // tbd; hardware/cluster/cluster-boards.md: outlines are undrawable until M3
switch_pcb_t = 1.6;  // nominal; the MAIN board's thickness (PCB-CARRIER), as the key boards' (boards.key_board_t): a standard 1.6 mm board, its top against the thumb switches' housing bottom, shows 5.10 - 2.50 - 1.60 = 1.0 mm of pin to solder [calc, docs/reference/ks33-geometry.md]; ADR 0022, ADR 0020 Amendment 6
switch_pcb_below_seat_window = [2.45, 2.55];  // settled; [ds] GATERON-KS-33-VENDOR-SPEC-DRAWING.pdf sheet 6: the housing bottom, 2.50 +/-0.05 below the seat, which the board top is pressed against (owner, 2026-09-29; ADR 0020 Amendment 6). Higher is impossible (the housing is there); lower leaves a gap the key press would close. The pins flare to about 2 mm wide just under the housing [3D, mechanical/cad/vendor/ks33.stl, sectioned 2026-09-29], so the switch footprint's holes are sized to pass the flare (hardware/lib/README.md). Checked by drc.echo 'key-board depth inside the switch pins' window'
boards_matrix_board = 25.0;  // settled; [ds] datasheets/mechanical/WAVESHARE-ESP32-S3-MATRIX-dimensions.jpg - 25.00 x 25.00, R1.0
boards_matrix_emitters = 20.8;  // nominal; ADR 0014 / carrier.md - 8 x 2.6 mm pitch [from memory there]
boards_smt_h = 2.3;  // nominal; tallest SMT part on the main board: SMA/SMC diodes 2.29-2.62 [ds SMAJ15A p.3, SS34 p.3]; SOIC 1.75
boards_cluster_smt_h = 1.8;  // nominal; the key boards' tallest underside part: the register's SOIC-16 (U-KEYS, SN74HCS165D), max 1.75 - the JEDEC MS-012 outline as drawn for SOT109-1 [datasheets/logic/74HCS165-nexperia.pdf Fig. 18]; TI's SCLS828A as banked has no D-package outline (pp.25-34 are BQB, DYY and PW only) and its D is MS-012 [from memory] - and 0805 passives
boards_tall_l = 15.0;  // tbd; ONE regulator block, the long side across the body - an R-78E5.0 SIP-3 (11.6 x 8.5 x 10.4 [ds R-78E5.0-1.0 p.4]), its C-BUCK-IN 6.3 x 11 and a C-STRIP-BULK 8-10 x 12.5-20 [from memory]; one block, on the main board (ADR 0017)
boards_tall_w = 10.0;  // tbd; the regulator block's other side: an R-78E5.0 SIP-3 (11.6 x 8.5 on the board), capacitors beside it [ds R-78E5.0-1.0 p.4; caps from memory]
boards_tall_h = 12.5;  // tbd; the shortest the bulk electrolytics come, upright [from memory]; lay them down or use SMD polymer where drc.echo says they do not fit
boards_sensor_body = 12.3;  // settled; [ds] MPXV4006DP p.7, case 1351-01 - body 11.81-12.32 square. SURFACE MOUNT (p.1 ordering table), not THT
boards_sensor_h = 9.9;  // settled; [ds] MPXV4006DP p.20 case 1351-01 table, dim A - overall height 9.39-9.91
boards_sensor_leads = 17.8;  // settled; [ds] MPXV4006DP p.7 - across the lead tips 17.27-17.78
boards_sensor_port_l = 6.6;  // settled; [ds] MPXV4006DP p.7 - ports protrude 6.10-6.60 from one face
boards_sensor_port_d = 3.3;  // settled; [ds] MPXV4006DP p.7 - barb OD 2.79-3.30
boards_sensor_port_z = [8.5, 1.4];  // nominal; port centres above the seating plane, upper (P1, marked side - p.6 Table 3) and lower; scaled off the p.7 drawing
boards_sensor_port_offset = 2.1;  // tbd; [ds] MPXV4006DP p.7 end view, case 1351-01 dim N (p.20 table) 4.06-4.57 - the two ports' centres are offset across the body by N, so each sits N/2 = 2.03-2.29 either side of the body's centre [calc]; 2.1 is a pick inside that range
boards_sensor_lead_row = 10.2;  // tbd; length along the body of the block standing in for the leads. NOT a datasheet dimension: the p.20 table gives e 2.54 BSC and b 0.96-1.07, so 4 leads per side span 3 x 2.54 + 1.07 = 8.69 max [calc]; 10.2 is a modelling envelope over that [from memory]
boards_sensor_lead_h = 1.2;  // tbd; height of the block standing in for the lead forms. NOT a datasheet dimension: the p.20 table gives only A1 0.05-0.25 (standoff) and L 1.02-1.52 (foot length); the lead's rise to the body is drawn (p.7 Detail G) but not dimensioned [from memory]
boards_sensor_land_w = 18.8;  // settled; across the land pattern's two pad rows, outer end to outer end: rows 16.00 centre to centre plus one 2.80 pad [repo hardware/lib/woody.pretty/NXP_Case1351-01_SOP-8_P2.54mm.kicad_mod; calc 16.00 + 2.80 = 18.80]. Wider than the lead tips (sensor_leads), so it is what sets the sensor's inset from the main board's edge: the copper, not the part, must keep off the edge
boards_chain_hdr_l = 13.97;  // nominal; SHF header length = positions per row x 1.27 + 6.35 REF, 6 per row [datasheets/connectors/SAMTEC-SHF-1XX-01-X-D-XX-PRINT.pdf, sheet 1]
boards_chain_hdr_h = 5.59;  // nominal; the right-angle header's height off the board, .220 REF, standing on 0.51 ribs [datasheets/connectors/SAMTEC-SHF-1XX-01-X-D-XX-PRINT.pdf, sheet 1 fig 1]
boards_chain_hdr_d = 5.33;  // nominal; the right-angle shroud's depth, mouth to back, .210 REF [datasheets/connectors/SAMTEC-SHF-1XX-01-X-D-XX-PRINT.pdf, sheet 1]
boards_chain_hdr_pin_back = 7.86;  // nominal; from the mouth back to the far (odd) pin row: the depth 5.33 plus the odd row's bend 1.26 + 1.27 behind the back face, measured at the bend (note 7) [datasheets/connectors/SAMTEC-SHF-1XX-01-X-D-XX-PRINT.pdf, sheet 2 section C-C; calc]
boards_chain_plug_proud = 1.4;  // tbd; how far the FFSD socket stands out of the header's mouth - NOT given by either print, which also say DO NOT SCALE; estimated as the socket's 5.08 height less a mouth-to-floor depth of about 3.67 that is not dimensioned. It sets where the cable leaves the socket and whether it clears the shroud. An estimate until a mated pair is measured [datasheets/connectors/SAMTEC-FFSD-XX-X-XX.XX-01-PRINT.pdf sheet 1 and datasheets/connectors/SAMTEC-SHF-1XX-01-X-D-XX-PRINT.pdf sheet 2]
boards_chain_hdr_tail = 2.15;  // nominal; the header's tails below its seating plane, .085 REF [datasheets/connectors/SAMTEC-SHF-1XX-01-X-D-XX-PRINT.pdf, sheet 2 section C-C]
boards_chain_hdr_mouth_z = 3.05;  // nominal; the mouth's centre above the board: the 0.51 ribs plus half the 5.08 body [calc, datasheets/connectors/SAMTEC-SHF-1XX-01-X-D-XX-PRINT.pdf sheet 1 fig 1]
boards_chain_plug_h = 5.08;  // nominal; the FFSD socket's height along its insertion, 5.08 +0.15/-0.08 [datasheets/connectors/SAMTEC-FFSD-XX-X-XX.XX-01-PRINT.pdf, sheet 1 fig 1]
boards_chain_plug_t = 3.05;  // nominal; the FFSD socket's thickness, .120 REF [datasheets/connectors/SAMTEC-FFSD-XX-X-XX.XX-01-PRINT.pdf, sheet 1]
boards_chain_plug_l = 11.81;  // nominal; the FFSD socket's length, positions per row x 1.27 + 4.19, 6 per row [datasheets/connectors/SAMTEC-FFSD-XX-X-XX.XX-01-PRINT.pdf, sheet 1]
boards_mcu_conn_l = 21.54;  // settled; J-MCU, the XKB X1270WR-2x12A-9TV01 box header, side entry, across the body: dimension C for 2x12 [ds XKB-X1270WR-2x12A-9TV01.pdf] (ADR 0018)
boards_mcu_conn_w = 7.8;  // settled; the same header along the body with its tail pads: 5.40 body [ds XKB-X1270WR-2x12A-9TV01.pdf], its far tail row 1.87 behind the body's back plus the pad [calc from the same drawing]
boards_mcu_conn_h = 5.1;  // settled; the same header's height above the board [ds XKB-X1270WR-2x12A-9TV01.pdf]
boards_umb_adapter_t = 1.6;  // tbd; the adapter board's thickness, a standard 2-layer board [from memory]; the NE8FAV's pin tails reach through it
boards_umb_joint_d = 2.5;  // settled; J-UMB's insulator along the body, behind the adapter: the hanxia HX PZ2.54-1x8P WZ's 2.50 mm square insulator [ds HANXIA-HX-PZ2.54-1x8P-WZ.pdf]
boards_umb_joint_h = 2.5;  // settled; the same insulator's height on the main board [ds HANXIA-HX-PZ2.54-1x8P-WZ.pdf]
boards_umb_joint_row_h = 1.25;  // settled; the header's pin row above the main board, at the middle of its 2.50 insulator [ds HANXIA-HX-PZ2.54-1x8P-WZ.pdf]; where the row meets the adapter
boards_umb_parts_d = 14;  // tbd; the depth along the body, in front of J-UMB's insulator, kept for J-UMB's own footprint and the parts that must sit at the connector (U-TVS-SPI, NT-DIG, D-TVS-BREATH x2, R-SER-BREATH-INST x2, D-REVSHUNT): the pin row 1.5 in front of the insulator plus its courtyard 1.77 [repo: KiCad PinHeader_1x08_P2.54mm_Horizontal as placed], a column of the SOD-323 / SOT-23-5 / net-tie parts 3.6, and a column of the 1206s and the SMC shunt 6.7 [calc: 3.27 + 3.6 + 6.7 = 13.57, rounded up]. The tongue's end mounts stand behind it; D-TVS-PWR goes between them
boards_key_board_t = 1.6;  // nominal; [calc] docs/reference/ks33-geometry.md: the pins end 5.10 below the seat and the board top is against the housing bottom at switch.pcb_below_seat, so a standard 1.6 mm board shows 1.0 mm of pin to solder. 1.6 mm is every board house's standard thickness
boards_pcb_t_tol = [-0.16, 0.16];  // settled; a finished 1.6 mm board's thickness tolerance, key boards and main board: +/-10 % at 1.0 mm and over [datasheets/fab/JLCPCB-PCB-CAPABILITIES.pdf, 'Thickness Tolerance']. A board's top face is set by its spacer, so this moves only its other face - and so the gap the column standoff fills (drc.echo 'cassette height at the hardware's tolerance limits')
boards_kb_end_margin = 6.6;  // tbd; a key board's MOUTH end past its first switch cutout, along the body. The mouth corners' columns stand over the first thumb row, and a column cannot lean (ADR 0025), so the key board's mount must be where its stud in the bottom plate keeps hardware.stud_edge, and its spacer 0.5, from a thumb switch's cutout: 0.6 more than the 6.0 the key board alone needed (drc.echo 'columns vertical: the main board's mounts under the key boards'', 'bottom-plate studs clear of the plate's edges and cutouts', 'bottom-plate spacers clear of the thumb switch cutouts')
boards_kb_tail_margin = 10.3;  // nominal; a key board's TAIL end past its last switch cutout, longer than the mouth end: the last keys (LH4/LH5, RH6) reach the board's corners across the body, and each tail corner's screw pocket in the oak top must keep hardware.col_pocket_wall from that key's cap slot [calc: half the slot 9.0 + half the pocket 3.175 + the wall 1.5 + the inset 3.6 - half the cutout 7.0 = 10.275, rounded up]. drc.echo 'key-board tail margin, least' prints how short it may be
boards_board_clear = 1.5;  // tbd; clearance between a board and the parts on the board facing it, and between parts: board flex, solder fillets and height tolerance, hand assembly [drawing convention]. 0.5 was a drawing clearance and the owner rejected it (2026-09-26: 'once components are installed you'd have issues')
boards_main_neck_min = 8.0;  // tbd; [calc] ~20 nets cross the station (the key chain's 12 conductors, the breath sensor's lines, the LED row's data and backup lines, power) at 0.25 track / 0.25 gap is 10 mm on one layer, 5 mm on two; plus 0.5 mm copper keep-out from each cut edge is 6; 8 leaves room for a ground return beside them
boards_matrix_t = 1.6;  // settled; [ds 3D] datasheets/mechanical/WAVESHARE-ESP32-S3-MATRIX-3D.stp - the board spans z -0.8 to 0.8
boards_matrix_harness_h = 2.5;  // tbd; below the Matrix: the ribbon soldered straight to its pads, wires bent flat [from memory]. Crimp housings on a pin header stood ~16.5 and put a row across the patch plug
boards_matrix_under_h = 3.2;  // tbd; the Matrix's back-side parts (ESP32-S3, USB-C, IMU) below its board [from memory]
boards_matrix_led_h = 1.0;  // tbd; WS2812B-0807 package height above the board [from memory]
openings_matrix_window = 22.0;  // nominal; [adr] ADR 0009 - 'Roughly 22 mm square'; the clear opening through the plate and the oak LIP under the acrylic window
openings_matrix_lip = 2.0;  // tbd; oak lip the acrylic rests on, per side - the rebate is the opening plus twice this
openings_matrix_acrylic_t = 3.0;  // tbd; frosted acrylic window thickness [from memory: common sheet]; must leave an oak lip under it
openings_usb_slot_w = 12.5;  // tbd; panel cutout for a panel-mount USB-C extension receptacle [from memory]
openings_usb_slot_h = 7.0;  // tbd; as usb_slot_w [from memory]
openings_usb_slot_portrait = true;  // tbd; [calc] portrait takes usb_slot_h across instead of usb_slot_w, and usb_slot_w tall in the cavity's height; drc.echo gives the lane and the webs either way
openings_usb_plug_l = 15.0;  // tbd; RIGHT-ANGLE USB-C plug on the extension (2026-09-26): the Matrix's edge to the far side of the moulding, where the lead turns across the body [from memory]. A straight plug is 25-30 and, doubled by the centred Matrix, added ~24 mm of body
openings_matrix_usb_to_tail = false;  // tbd; false = the Matrix's USB-C edge faces the MOUTH, so its plug runs under the key boards instead of into the connector's housing; datasheets/mechanical/WAVESHARE-ESP32-S3-MATRIX-dimensions.jpg shows the port overhanging one edge
openings_usb_ext_depth = 20.0;  // tbd; the extension receptacle's body behind the panel [from memory]
openings_usb_overmold = [15.0, 9.0];  // tbd; the plug's overmould, [wide, thick], plus clearance: common USB-C cables are ~12-14.5 x 6.5-8.5 [from memory]. Stood on end the thick side is across the body, and the lane beside the etherCON flange takes up to 10 with a 2 mm web (drc 'tail cap web between the USB-C cutout and the etherCON flange') - a cable fatter than that does not fit this face
openings_usb_panel_t = 1.5;  // tbd; oak left under the overmould pocket, the panel the receptacle clamps to [from memory: panel-mount USB-C is made for ~1-2 mm panels]
openings_usb_nose_l = 2.0;  // tbd; how far the receptacle's shell stands proud of its clamping shoulder, i.e. the thickest panel it can sit flush in [from memory]
openings_usb_mount = "earless";  // tbd; earless | ears. 'ears' is checked against usb_ear_pitch and fails at this cavity height; see the note above
openings_usb_ear_pitch = 29.0;  // tbd; screw-ear pitch of a typical panel-mount USB-C extension, ~28-30 [from memory]; used only to show why the ears do not fit on end
ethercon_bore_d = 22.0;  // settled; [ds] ST-NE8FAV - panel cut out (rear side), bore 22 min
ethercon_flange_w = 25.0;  // settled; [ds] ST-NE8FAV front view - flange 25 x 25
ethercon_flange_h = 25.0;  // settled; [ds] ST-NE8FAV side view - 25, the axis at 12.5 from its lower edge
ethercon_hole_dx = 19.8;  // settled; [ds] ST-NE8FAV panel cut out - two diagonal 3.2 min holes at 19.8 +/-0.1 x 19.8 +/-0.1, upper left and lower right seen from the front
ethercon_hole_dy = 19.8;  // settled; [ds] ST-NE8FAV
ethercon_hole_d = 3.2;  // settled; [ds] ST-NE8FAV
ethercon_panel_max = 3.0;  // settled; [ds] NEUTRIK-NE8FAV-DATASHEET.pdf - 'Panel thickness max. 3 mm'. The oak tail cap is thicker, so a recess from outside leaves this much oak where the connector mounts
ethercon_pcb_setback = 18.3;  // settled; [ds] ST-NE8FAV side view - flange front face to the PCB's front face
ethercon_nose_l = 2.7;  // settled; [ds] ST-NE8FAV side view - 21 from the PCB face to the nose's front, less the 18.3 to the flange face [calc]; it stays inside a 3 mm panel's bore
ethercon_tab_w = 10.0;  // settled; [ds 3D] NEUTRIK-NE8FAV-3D.stp - the tab spans +/-5.0 across [calc, read 2026-09-29]
ethercon_tab_top = 16.6;  // settled; [ds 3D] NEUTRIK-NE8FAV-3D.stp - 16.61 above the axis; the drawing's front view shows it above the flange's 12.5
ethercon_tab_front = 6.8;  // settled; [ds 3D] NEUTRIK-NE8FAV-3D.stp - 6.8 in front of the flange face; the drawing's 24.3 overall is to the same tab, from the rear latch
ethercon_pin_rows = [2.11, 4.65];  // settled; [ds] ST-NE8FAV PCB layout - the two contact rows, 2.54 apart, the upper at 4.65 above the peg line through the axis
ethercon_g_below = 10.55;  // settled; [ds] ST-NE8FAV PCB layout - G (d1.2) 15.2 below the upper row [calc: 15.2 - 4.65]
ethercon_peg_below = 1.5;  // settled; [ds 3D] NEUTRIK-NE8FAV-3D.stp - two d1.5 locating pegs stand 1.5 below the flange's lower edge (the drawing's front view shows them). Standing on the floor, latch up, they point into the oak bottom, so they are CUT OFF FLUSH at assembly (ADR 0021): drilling the floor for them would locate the connector twice, by the cap and by the floor
ethercon_recess_margin = 1.0;  // tbd; the tail cap's outside recess round the flange's outline and the PUSH tab [placeholder]
ethercon_rotated = false;  // settled; [adr] ADR 0021 - the NE8FAV's flange is square, so ADR 0009's reason to turn the NE8FDP is gone; latch up, the PUSH tab on top
ethercon_offset_y = -7.0;  // tbd; placeholder - off-centre so the USB-C slot fits beside it
hardware_stud_hole = 2.5;  // settled; the bottom plate's hole for a PEM FHL-M2.5 stud, 2.50 +0.08, punched or drilled, NOT deburred [datasheets/mechanical/PEM-FHL-M2.5-10ZI-SALES-DRAWING.pdf; installation, datasheets/mechanical/PEM-FH-SELF-CLINCHING-STUDS.pdf p.FH-18]
hardware_stud_head_d = 3.15;  // settled; the FHL-M2.5 stud's head, 3.15 +/-0.40, flush in the bottom plate's underside, so the plate still lies flat on the oak [datasheets/mechanical/PEM-FHL-M2.5-10ZI-SALES-DRAWING.pdf]
hardware_stud_edge = 2.8;  // settled; the FHL-M2.5 stud's least distance from its hole's centre to an edge of the sheet [datasheets/mechanical/PEM-FHL-M2.5-10ZI-SALES-DRAWING.pdf, 'min centerline-to-edge']. A thumb switch's cutout, a U-bolt leg's hole and the plate's outline are all edges (drc.echo 'bottom-plate studs clear of the plate's edges and cutouts')
hardware_stud_s = 2.1;  // settled; the FHL-M2.5 stud's unthreaded length, max, from the head's face [datasheets/mechanical/PEM-FHL-M2.5-10ZI-SALES-DRAWING.pdf]. Below a 1.2 plate it ends inside the spacer, so the main board and the standoff meet thread (drc.echo 'bottom-plate studs: unthreaded shank ends inside the spacer')
hardware_stud_attached_hole = 2.9;  // settled; the largest hole PEM allows in the part that bears on the sheet round an FHL-M2.5 stud - here the spacer's bore [datasheets/mechanical/PEM-FH-SELF-CLINCHING-STUDS.pdf p.FH-7]
hardware_stud_l = 10;  // nominal; the FHL-M2.5 stud's length code L, from the head's face (stocked 6, 8, 10, 12, 15, 18 [datasheets/mechanical/PEM-FH-SELF-CLINCHING-STUDS.pdf p.FH-7]): the bottom plate + spacer + main board, and thread_engage_min diameters into the column standoff, at the stud's shortest [calc: 1.2 + 1.3 + 1.6 + 1.5 x 2.5 + 0.4 = 8.25, so 10; 8 gives 3.5 of the 3.75 wanted]. One length for every mount: at an end mount it leaves thread past the nut. drc.echo 'column: stud thread in the standoff', 'end mounts: stud thread past the nut'. The part is datasheets/mechanical/PEM-FHL-M2.5-10ZI-SALES-DRAWING.pdf
hardware_stud_l_tol = [-0.4, 0.4];  // settled; the FHL stud's length tolerance, 10.00 +/-0.40 [datasheets/mechanical/PEM-FHL-M2.5-10ZI-SALES-DRAWING.pdf]
hardware_m25_pitch = 0.45;  // settled; M2.5 coarse thread pitch [datasheets/mechanical/PEM-FHL-M2.5-10ZI-SALES-DRAWING.pdf, 'M2.5 x 0.45']
hardware_stud_torque = 0.32;  // settled; the most torque to put on a nut, or on a standoff threaded onto it, on an FHL-M2.5 stud in 1.2 mm aluminium, N.m; PEM tested push-out 285 N, torque-out 0.55 N.m in that sheet (HRB 33) [datasheets/mechanical/PEM-FH-SELF-CLINCHING-STUDS.pdf p.FH-31, metric table]. FHL is rated for aluminium to HRB 80 / HB 150 [p.FH-7], which takes 5052 and 6061 alike
hardware_thread_engage_min = 1.5;  // tbd; the least thread engagement in the column standoff, in diameters of the M2.5 thread, for the stud from below and the screw from above [from memory: 1.5 x d, the owner's brief of 2026-09-29 gives it as a reasonable minimum] (drc.echo 'column: stud thread in the standoff', 'column: screw thread in the standoff')
hardware_kb_plate_t_tol = [-0.05, 0.05];  // nominal; a plate's thickness tolerance, key plate and bottom plate: the switch's own plate-slot tolerance (`plate-thickness`, config/figures.yaml), which a plate bought to that register must meet. It enters each board's depth because the spacer bears on the plate's inside face while the switch seats on its outside one
hardware_kb_board_hole = 2.7;  // nominal; M2.5 clearance through the key boards and the main board, ISO 273 fine [from memory]: each board locates on its columns and studs, so the fine fit
hardware_kb_spacer_l = 1.3;  // tbd; a plain metal spacer for M2.5, flat both ends, and the only thing between a plate and its board at a mount: the switches' housing below the plate, which the board is pressed against [calc: 2.50 - 1.20]. The switches hold the gap only where they are; at a mount there is no switch, and without the spacer the clamp would pull the board up into the plate (owner, 2026-09-29). The same part, faced alike, stands under the key plate on every column (MECH-KB-SPACER) and on the bottom plate under the main board at every mount (MECH-MB-SPACER); its bore, at most stud_attached_hole, matters on the bottom plate, where it bears on the stud's sheet. NOT STOCKED at 1.3: face Ettinger 5.52.015 (M2.5, 1.5 long, bore 2.6 [datasheets/mechanical/ETTINGER-CATALOG-2024-P79-DISTANZHUELSEN-MESSING.html]) down to 1.3 +/-0.05, in metal, not printed, which would creep under the clamp
hardware_kb_spacer_l_tol = [-0.05, 0.05];  // tbd; the faced spacer's length tolerance, to be held when it is faced (kb_spacer_l)
hardware_kb_spacer_od = 4.5;  // nominal; the Ettinger 5.52 spacer's outside diameter, 4.5; its bore is 2.6, inside stud_attached_hole [datasheets/mechanical/ETTINGER-CATALOG-2024-P79-DISTANZHUELSEN-MESSING.html]. On a key board it bears on the board's top copper, which keeps copper out from under it; on the main board it bears on a PWR_GND pad on the underside, which grounds the bottom plate (ADR 0022 point 6, ADR 0025)
hardware_col_standoff_af = 5.0;  // tbd; an M2.5 female-female hex standoff across its flats [from memory: 5 mm is the common M2.5 hex, the same as the ISO 4032 nut, mb_nut_e]. Its across-corners, af / cos 30, stands on the main board's top face and under the key board, and both boards keep copper and parts out from under it
hardware_col_standoff_stock_l = 20;  // tbd; the stocked M2.5 female-female length it is faced down from: the next one above the gap (drc.echo 'column standoff length (derived)') [from memory: the common series step 15, 18, 20]. drc.echo 'column standoff faced from its stock length'
hardware_col_standoff_l_tol = [-0.05, 0.05];  // tbd; the faced standoff's length tolerance, held as the spacers' is (kb_spacer_l_tol) [drawing convention]
hardware_col_screw_head_d = 4.5;  // tbd; an M2.5 low-head cap screw's head, DIN 7984 [from memory; ISO 7380 is 4.7]. It bears on the key plate's top face round col_plate_hole and sits in col_pocket_d
hardware_col_screw_head_h = 1.5;  // tbd; the same head's height [from memory: DIN 7984 M2.5, 1.5]. It sets the pocket's depth in the oak top (drc.echo 'column screw pockets leave wood over them')
hardware_col_screw_l = 10;  // nominal; the column screw's length under its head: the key plate + spacer + key board, and thread_engage_min diameters into the standoff, at the screw's shortest [calc: 1.2 + 1.3 + 1.6 + 1.5 x 2.5 + 0.3 = 8.15, so 10; 8 gives 3.6 of the 3.75 wanted]. drc.echo 'column: screw thread in the standoff', and 'column: stud and screw ends apart in the standoff'
hardware_col_screw_l_tol = [-0.3, 0.3];  // tbd; a 10 mm screw's length tolerance, js15 [from memory: ISO 4759-1, +/-0.29 over 6-10 mm]
hardware_col_plate_hole = 2.9;  // nominal; M2.5 clearance through the key plate, ISO 273 medium [from memory]: the key plate and the key boards are one part once the switches are soldered, and each board locates on its columns by the fine hole (kb_board_hole), so the plate takes the medium one; the screw's head (col_screw_head_d) bears on the plate round it
hardware_col_pocket_d = 6.35;  // nominal; the blind pocket in the oak top's underside over each column screw's head: 1/4 in, a stock Forstner size, which leaves a flat floor (the size ADR 0020 Amendment 3 chose for the same job). Clears the head (col_screw_head_d) with room to spare; the pocket only houses the head, which bears on the plate
hardware_col_pocket_clear = 0.5;  // nominal; the pocket's depth past the screw head's top [drawing convention]
hardware_col_pocket_skin = 2.0;  // tbd; the least wood left over a pocket, between its floor and the playing face: enough not to telegraph or crack through in hardwood [from memory - no banked figure] (drc.echo 'column screw pockets leave wood over them')
hardware_col_pocket_wall = 1.5;  // tbd; the least wood left between a pocket and a cap slot, a side groove or the window's rebate [from memory - no banked figure] (drc.echo 'column screw pockets clear of the wood top's cuts'; the tail corners set boards.kb_tail_margin, 'key-board tail margin, least')
hardware_mb_nut_e = 5.77;  // nominal; ISO 4032 M2.5 hex nut across its corners, at its largest: s max 5.0 / cos 30 = 5.77 [calc from datasheets/mechanical/ASPEN-ISO4032-DIN934-HEX-NUT-DIMENSION-TABLE.pdf, whose e is the minimum, 5.5]. On the main board's end mounts; it bears on a PWR_GND pad on the top face (ADR 0022 point 6)
hardware_mb_nut_m = 2.0;  // nominal; the same nut's height, m max 2.0 [datasheets/mechanical/ASPEN-ISO4032-DIN934-HEX-NUT-DIMENSION-TABLE.pdf]
hardware_kb_mount_float = 0.2;  // nominal; how far a spacer or a standoff can sit off its axis: (the bore - the thread) / 2 - the spacer's 2.6 (+0.1) on an M2.5 gives at most 0.1 [calc from the catalogue under kb_spacer_od]; held at 0.2, and every PCB keep-out grows by it on every side
hardware_end_mount_merge_d = 12;  // settled; an end mount is dropped when a column's mount stands within this distance of it: the column already holds the board there, and two studs side by side add a part and a hole for no support (owner, 2026-09-30: "there's one spot where we have double standoffs right next to each other ... Good to reduce it to the one standoff there"). The mouth end mount at (32.5, 45.5) stood 7.5 from the column at (40, 45.9); the nearest any other end mount comes to a column is 28.5 [calc from mechanical/export/pcb-geometry.echo at 064c49f: hypot(40 - 32.5, 45.9 - 45.5) = 7.51; hypot(40 - 11.5, 11.1 - 11.5) = 28.50]. 12 is about two mount keep-outs (mb_keep_d, 6.57 [calc: 6.17 + 2 x 0.2]) and sits well between the two; drc.echo reports each end mount dropped
hardware_kb_mount_inset = 3.6;  // tbd; a column's centre in from both edges of its key board: the standoff across its corners (col_standoff_af / cos 30) and kb_mount_float, with 0.5 of board outside the keep-out [calc: 5.77 / 2 + 0.2 + 0.5 = 3.585]
hardware_ubolt_rod_d = 3.0;  // tbd; M3 [calc above]; ADR 0009 gives no U-bolt size. No longer bounded by the lights (ADR 0028); M4 or M5 must still leave the neck ('main board neck at the U-bolt station') and clear the thumb recesses
hardware_ubolt_hole_clear = 0.5;  // tbd; clearance on the leg's diameter, in the oak bottom and the bottom plate
hardware_ubolt_span = 20.0;  // tbd; leg centre to leg centre, legs across the body. Narrower pulls the nuts toward the centreline and shrinks the neck between the legs; wider takes the legs toward the thumb recesses (drc 'U-bolt legs clear of the thumb recesses') and the main board's edge
hardware_ubolt_drop = 18.0;  // tbd; placeholder - how far the loop stands below the bottom face
hardware_ubolt_nut_af = 5.5;  // tbd; hex nut across flats for the U-bolt legs - an M3 nut is 5.5 mm [from memory, ISO 4032]; follows ubolt_rod_d
hardware_ubolt_nut_h = 4.0;  // tbd; M3 nyloc (DIN 985) height, ~4.0 [from memory] - hardware/unplaced.csv MECH-UBOLT orders nylocs; a plain ISO 4032 nut is 2.4
hardware_ubolt_spacer_od = 6.0;  // nominal; the spacer on each U-bolt leg between the bottom plate and the main board's underside: Ettinger 5.53.015, brass for M3, outside 6.0, bore 3.2, 1.5 long [datasheets/mechanical/ETTINGER-CATALOG-2024-P79-DISTANZHUELSEN-MESSING.html], faced to kb_spacer_l like every other spacer on the plates, so the board is not pulled down by the nyloc (drc 'main board in the U-bolt's clamp')
hardware_ubolt_washer_t = 0.5;  // tbd; DIN 433 M3 washer, 0.5 thick [from memory], one per leg between the main board's top face and the nyloc
hardware_ubolt_washer_od = 6.0;  // tbd; DIN 433 M3 washer, outside diameter 6.0 [from memory] - the small-OD series, so it bears on the board inside the nut's keep-out
hardware_ubolt_board_hole_clear = 1.0;  // tbd; clearance on the rod's diameter in the main board's hole. The board is located by its own mounts and the legs by the oak's and the bottom plate's holes, so the hole takes both tolerances; the washer above and the spacer below cover it (bore 3.2, outside 6.0)
routing_tube_od = 5.0;  // tbd; breath tube outside diameter; ADR 0003 assumes a 3 mm bore, the wall is a guess [from memory]
routing_trap_d = 10.0;  // tbd; dead-volume trap diameter; ADR 0003 caps the trap at 1 mL
routing_trap_l = 12.0;  // tbd; trap length: 10 mm bore x 12 mm = 0.94 mL, inside ADR 0003's 1 mL [calc]
routing_tube_lane = "left";  // tbd; which side the tube and trap run on inside the mouth band (ADR 0017: sensor on the far side from the tube); there are no looms since ADR 0017
routing_mcu_ribbon_w = 15.24;  // tbd; 24-way 0.635 mm ribbon for a 1.27 mm dual-row header [calc: 24 x 0.635]: allocation in hardware/carrier/bom.csv CBL-MCU-RIBBON (ADR 0018)
routing_mcu_ribbon_t = 0.8;  // tbd; fine-pitch ribbon thickness [from memory]
routing_chain_ribbon_w = 7.62;  // nominal; [calc] 12 conductors at 0.635 mm, the FFSD cable's 1.27 mm IDC pitch over two rows
routing_chain_ribbon_t = 0.8;  // tbd; 30 AWG flat cable's thickness [from memory]
routing_chain_bend_r = 1.0;  // tbd; the tightest turn the flat cable takes where it leaves a socket and turns along the body, and the least the fold may be (drc.echo 'key-chain ribbon fold no tighter than its bend radius') [drawing convention; 30 AWG PVC flat cable folds flatter than this]
routing_chain_service = "raised";  // nominal; owner, 2026-09-27: long enough 'to have the top off and still connect the ribbon before tightening down'. With the cassette (ADR 0025), 'tightening down' is screwing the key plate onto its columns, on the bench or, in service, with the oak top cut off. The key plate, with both key boards on it, is held raised straight up off the columns by routing.chain_raise while the main board's sockets are plugged or unplugged, then lowered and screwed down; the ribbon folds itself into the hairpin. A ribbon long enough to lay the plate beside the body would close into a hairpin that reaches the left-hand board's tail column (drc.echo 'key-chain ribbon hairpin clear of the columns')
routing_chain_raise = 30.0;  // tbd; how far the key plate is held above its columns for a hand to reach the main board's sockets under the key boards and plug or unplug them [drawing convention: two fingers and an IDC socket]. With routing.chain_slack it sets the ribbon's length (drc.echo 'key-chain ribbon length (derived)')
routing_chain_slack = 10.0;  // tbd; length added to the service path for the turns at the sockets and the hand [drawing convention]
routing_chain_fold = [1, 1];  // nominal; which way each ribbon's spare length folds closed, along the body (+1 toward the tail), for left_hand and right_hand: the left hand's mouth side has the breath tube's crossing; on the right hand, chain_clear keeps the tail side off the regulator block, and each hairpin must stop short of its board's columns (drc.echo 'key-chain ribbon hairpin clear of the columns', clash.txt)
routing_ribbon_t = 1.0;  // nominal; flat ribbon thickness, 1.27 mm pitch PVC ribbon [from memory]
lighting_led_count = 13;  // settled; owner, 2026-09-30 (ADR 0028): thirteen LEDs, the count the 60/m strip gave over the same run
lighting_led_pitch = 16.67;  // tbd; centre to centre along the body: the strip's 60/m [calc: 1000 / 60 = 16.67], which ADR 0014 chose for how it diffuses
lighting_led_body = [5.4, 5.0];  // settled; the WS2815B-V1's body along the body and across it, 5.40 +/-0.05 x 5.00 +/-0.05 [ds datasheets/led/WS2815B-V1.pdf p.2]
lighting_led_h = 1.65;  // settled; the WS2815B-V1's height above the board, 1.65 +/-0.05 [ds datasheets/led/WS2815B-V1.pdf p.2]
lighting_led_court = [6.9, 5.5];  // settled; the footprint's courtyard, woody:LED_WS2815B-V1_PLCC6_5.4x5.0mm_P1.6mm [repo hardware/lib/woody.pretty]: the pads' 6.4 across and the body's 5.0, each with KiCad's 0.25 margin a side

// Every value above with status tbd - a placeholder, not a number any
// document gives. The DRC report lists these so no result hides one.
tbd_params = ["stack_cap_clear", "stack_cap_holes", "stack_edge_r", "stack_side_inset", "stack_groove_depth", "stack_groove_clear", "ends_mouth_cap_t", "ends_tail_cap_t", "ends_tube_hole_d", "layout_mouth_extra", "layout_tail_clear", "layout_underside_clear", "layout_lh_offsets", "layout_rh_offsets", "layout_lt_rest_under", "layout_lt_rest", "layout_rt_rest_under", "layout_rt_rest", "switch_keycap_top_above_seat", "switch_keycap_top_w", "switch_keycap_wall", "switch_keycap_top_t", "switch_keycap_boss_below_top", "switch_keycap_socket_d", "switch_cluster_pcb_w", "boards_tall_l", "boards_tall_w", "boards_tall_h", "boards_sensor_port_offset", "boards_sensor_lead_row", "boards_sensor_lead_h", "boards_chain_plug_proud", "boards_umb_adapter_t", "boards_umb_parts_d", "boards_kb_end_margin", "boards_board_clear", "boards_main_neck_min", "boards_matrix_harness_h", "boards_matrix_under_h", "boards_matrix_led_h", "openings_matrix_lip", "openings_matrix_acrylic_t", "openings_usb_slot_w", "openings_usb_slot_h", "openings_usb_slot_portrait", "openings_usb_plug_l", "openings_matrix_usb_to_tail", "openings_usb_ext_depth", "openings_usb_overmold", "openings_usb_panel_t", "openings_usb_nose_l", "openings_usb_mount", "openings_usb_ear_pitch", "ethercon_recess_margin", "ethercon_offset_y", "hardware_thread_engage_min", "hardware_kb_spacer_l", "hardware_kb_spacer_l_tol", "hardware_col_standoff_af", "hardware_col_standoff_stock_l", "hardware_col_standoff_l_tol", "hardware_col_screw_head_d", "hardware_col_screw_head_h", "hardware_col_screw_l_tol", "hardware_col_pocket_skin", "hardware_col_pocket_wall", "hardware_kb_mount_inset", "hardware_ubolt_rod_d", "hardware_ubolt_hole_clear", "hardware_ubolt_span", "hardware_ubolt_drop", "hardware_ubolt_nut_af", "hardware_ubolt_nut_h", "hardware_ubolt_washer_t", "hardware_ubolt_washer_od", "hardware_ubolt_board_hole_clear", "routing_tube_od", "routing_trap_d", "routing_trap_l", "routing_tube_lane", "routing_mcu_ribbon_w", "routing_mcu_ribbon_t", "routing_chain_ribbon_t", "routing_chain_bend_r", "routing_chain_raise", "routing_chain_slack", "lighting_led_pitch"];
