jeffmhopkins/Woody/mechanical/cad/woody_body.scad

// =====================================================================
// WOODY - INSTRUMENT BODY
// A laminated stack of flat parts, every layer a 2D through-cut (ADR 0009).
//
// DO NOT PUT NUMBERS HERE. Dimensions come from generated/params.scad, which
// tools/cad.py writes from config/key-layout.yaml and config/body.yaml - each
// value there carries its source and a status (settled / nominal / tbd).
// This file holds GEOMETRY: how those numbers become parts. The few literal
// numbers below are drawing conventions (clearances for pictures, colours)
// and are named as such.
//
//   part = "assembly"            the instrument, 3D (default)
//   part = "<layer>"             one flat part, 2D, as it is cut - see LAYERS
//   part = "drc"                 the design-rule report, echo only
//
// Coordinates: X along the body from the mouthpiece end, Y across, Z up from
// the bottom face. The key plate's frame maps as X = x0 + y, Y = y0 + x.
//
// Render with `python3 tools/cad.py build`, never by hand into renders/:
// the build fingerprints every image against this file and its inputs.
// =====================================================================

include <generated/params.scad>

part = "assembly";
explode = 0;          // mm between layers in the exploded view
show_lid = true;
show_u = true;
show_caps = true;
show_keys = true;
show_boards = true;
show_hardware = true;
show_leds = true;
highlight = [];   // solid ids to draw bright yellow, the rest faded (fig_centre.scad)
show_routing = true;
ghost_shell = false;  // draw the shell translucent to see inside
// Sections. "y" / "x" clip every part with a half-space (keep Y < cut, or
// a slab X > cut) and stay 3D. "y2d" / "x2d" are true section DRAWINGS: each
// part cut by the plane with projection(cut = true), coloured per part, laid
// flat - "y2d" as (X, Z), "x2d" as (Y, Z) looking toward the tail. Use the
// 2D ones for anything dimensioned; OpenCSG loses part colours on 3D cuts.
cut = "none";
cut_at = 0;
cut_key = "";         // or name a key (or "matrix", or "ribbon" for the left key board's, or "kb_mount" for its tail column): the cut goes through its centre
cut_depth = 1000;     // "x" keeps a slab this deep beyond the cut
figure = false;       // set true by a figure that includes this file
// Where X = 0 sits in the rendered picture: "mouth" (the model's own frame),
// "centre" or "tail". Cameras aim at the origin, so a render stays framed
// when the derived length changes.
origin = "mouth";

LAYERS = ["plate_top", "oak_top", "oak_bottom", "oak_grooves", "plate_bottom", "side",
          "mouth_cap", "tail_cap", "matrix_window", "oak_rebates", "oak_pockets"];

$fn = 40;
EPS = 0.01;           // drawing convention: coplanar-face nudge

// ---------------------------------------------------------------- frame ----
// L, THE OVERALL LENGTH, IS DERIVED (owner, 2026-09-26: "minimize total
// length"). It is computed below the key layout, from the keys, the
// underside and the connector - see "length" - not read from a register.
W = envelope_width;
T = envelope_thickness;

// KEYS ARE FLUSH AT FULL TRAVEL (decided 2026-09-26): a pressed cap's top is
// level with the top face. So the plate sits UNDER the oak top, and the oak
// is exactly as thick as the cap stands above the seat at the bottom of its
// stroke. At rest each cap stands proud by the travel.
oak_top_t = switch_keycap_top_above_seat - switch_total_travel;
// Thumb keys too (same date): the bottom plate is on the oak bottom's inside
// face, so the same rule sets the oak bottom from below.
oak_bottom_t = switch_keycap_top_above_seat - switch_total_travel;
z_oak_top_bot = T - oak_top_t;                  // underside of the oak = plate top face
z_plate_top = z_oak_top_bot;                    // the switch seat
z_plate_bot = z_plate_top - plate_thickness;
z_lid_bot = z_plate_bot;                        // the lid's underside is the plate's
z_floor = oak_bottom_t;                   // inside face of the oak bottom
z_bplate_top = z_floor + plate_thickness;       // the bottom plate, on the inside face
cavity_h = z_lid_bot - z_floor;

lid_t = T - z_lid_bot;
// The sides stand BETWEEN the oak panels, in grooves (decided 2026-09-26):
// oak top and bottom are full width, each side is set in by an oak lip.
side_y = [stack_side_inset, W - stack_side_inset - stack_side_t];   // outer face of each side
groove_w = stack_side_t + 2 * stack_groove_clear;
u_y0 = stack_side_inset + stack_side_t;         // inside face of the left side
u_w = W - 2 * u_y0;                             // the interior, between the sides
z_side0 = z_floor - stack_groove_depth;         // side's bottom edge, in the bottom groove
z_side1 = z_oak_top_bot + stack_groove_depth;   // side's top edge, in the top groove
x_in0 = ends_mouth_cap_t;                       // between the end caps

// The key plate's origin (config/key-layout.yaml: "top-left of key plate").
plate_x0 = x_in0;
plate_y0 = u_y0;                                // the plate sits between the sides

// ------------------------------------------------------- length budget ----
function sum(v, i = 0) = i >= len(v) ? 0 : v[i] + sum(v, i + 1);
function cum(v, i) = i <= 0 ? 0 : sum([for (j = [0 : i - 1]) v[j]]);
lh_run = sum(layout_lh_gaps);
rh_run = sum(layout_rh_gaps);
// THE THUMB KEYS ARE SPACED AND CUT LIKE THE TOP (owner, 2026-09-26: "spacing
// between keys need to be right like the top"): the top's pitch between
// adjacent keys, the top's cap-to-oak clearance, and - when the top uses one
// slot per hand - one slot per group of thumb keys either side of a rest.
thumb_recess_clear = stack_cap_clear;
rc = switch_keycap + 2 * thumb_recess_clear;    // a thumb recess, square
thumb_pitch = layout_lh_gaps[0];                 // the top's index-to-middle pitch
cluster_margin = boards_kb_end_margin;   // a key board's MOUTH end past its first switch cutout (the board itself: kb_rect)
tail_margin = boards_kb_tail_margin;     // and its TAIL end past its last: longer, for the tail corners' column pockets beside the last keys' cap slots

// The MOUTH END. There is no display (owner, 2026-09-26: "remove the upper
// display ... we can do all this with the matrix led"; ADR 0015), so the
// keys start where the first top cap clears the mouth cap, the first thumb
// recess clears it too, and the breath trap fits across the mouth band
// before the first key board and thumb row. Everything is measured from x_in0,
// the inside face of the mouth cap.
// The left-thumb cluster's extent relative to LH1 (x_lh0 = 0), recesses included.
// A straight line: a pair, the thumb rest, a pair (owner, 2026-09-26).
// THE THUMB RESTS ARE DIRECTLY UNDER THE MIDDLE-FINGER KEYS (owner,
// 2026-09-26): layout.lt_rest_under / rt_rest_under name the key. Measured
// along its hand's provisional gaps, so it is known before the hands are
// placed; when key-layout.yaml gets real x/y this wants the key's own x.
function run_rel(id) = cum(id[0] == "L" ? layout_lh_gaps : layout_rh_gaps, ord(id[2]) - 49);
lt_rest_rel = run_rel(layout_lt_rest_under);
// TWO ROWS ACROSS THE BODY, the rest between them (owner, 2026-09-26: "left
// thumb with dual horizontal rows too, with gap still in the middle"): LT1 /
// LT2 side by side toward the mouth, LT3 / LT4 side by side toward the tail.
lt_rel = [for (i = [0 : 3]) lt_rest_rel + (i < 2 ? -1 : 1) * layout_lt_rest / 2];
lt_dy = [for (i = [0 : 3]) (i % 2 == 0 ? -1 : 1) * thumb_pitch / 2];   // across, from the centreline
// The breath trap sits mid-height, above the main board's parts, so it has
// to clear the first KEY board: clash.txt checks it against the main board.
// The breath sensor is at the mouth end too (ADR 0017), and its leads must
// stop short of the first thumb row's pins.
ks33_stub = 2.6;   // half-width of the KS-33's pole and pins where they stand proud of a board [clash.txt, off the vendor STEP]
board_lead = plate_cutout / 2 + cluster_margin;   // first key board edge before LH1
trap_band = boards_board_clear + routing_trap_l + boards_board_clear;
mouth_names = ["the first top key", "the first thumb recess", "the breath trap before the first boards",
               "the breath sensor before the first thumb row"];
mouth_claims = [x_in0 + layout_mouth_extra + switch_keycap / 2 + stack_cap_clear,
                x_in0 + layout_underside_clear - (min(lt_rel) - rc / 2),
                x_in0 + trap_band + board_lead,
                x_in0 + boards_board_clear + 0.5 + boards_sensor_body / 2 + boards_sensor_lead_row / 2 + ks33_stub + 0.5 - min(lt_rel)];
mouth_req = max(mouth_claims);

// The TAIL's needs, measured from the last top key's centre. Everything at
// the tail hangs off the right hand, so it can be worked out in the right
// hand's own frame (x_rh0 = 0) before the right hand is placed.
rt_rest_rel = [run_rel(layout_rt_rest_under), W / 2];
// Like the left thumb (owner, 2026-09-26: "four keys right thumb too"):
// RT1 / RT2 side by side a half rest toward the mouth, RT3 / RT4 a half rest
// toward the tail.
function rt_rel(i) = rt_rest_rel + [(i < 2 ? -1 : 1) * layout_rt_rest / 2, (i % 2 == 0 ? -1 : 1) * thumb_pitch / 2];
top_last_rel = max([for (i = [0 : len(layout_rh_gaps)]) cum(layout_rh_gaps, i)]);
rt_last_rel = max([for (i = [0 : count("right_thumb") - 1]) rt_rel(i)[0]]);
// BEHIND THE MATRIX, IN ORDER: the USB-C extension's plug off the Matrix's
// tail edge (if that edge faces the tail), a clearance, then the etherCON
// (ADR 0021): its adapter board, the connector's body to the flange, and the
// tail cap. The adapter stands the connector's full height, so it queues
// behind the Matrix; J-UMB, low on the main board, passes under it.
usb_behind = openings_matrix_usb_to_tail ? openings_usb_plug_l : 0;
ec_stack_d = boards_umb_adapter_t + ethercon_pcb_setback;   // the adapter's rear face to the flange's front face
behind_matrix = usb_behind + layout_tail_clear + ec_stack_d + ends_tail_cap_t;
// IN FRONT OF IT: the USB-C plug off the mouth edge (if that edge faces the
// mouth) reaches forward, and must clear the right-hand key board. Measured
// from the last key centre to where the equipment starts. (A pair of lid
// screws stood here until the module, ADR 0025.)
usb_front = openings_matrix_usb_to_tail ? 0 : openings_usb_plug_l;
equip_start_rel = plate_cutout / 2 + tail_margin + layout_tail_clear;
tail_claims_rel = [
    top_last_rel + equip_start_rel + boards_umb_joint_d + ec_stack_d + ends_tail_cap_t,
    top_last_rel + plate_cutout / 2 + tail_margin + layout_tail_clear + boards_matrix_board + behind_matrix,
    rt_last_rel + rc / 2 + layout_underside_clear + ends_tail_cap_t];
// The LED matrix CENTRED in the space after the keys (owner, 2026-09-26):
// midway between the last cap's slot edge and the tail face. The connector
// still has to fit behind it, so the tail grows to whatever that takes:
// centre = (edge + tail) / 2, and centre + half board + clearance + depth
// <= tail, so tail >= edge + 2 x (half board + clearance + depth).
cap_edge_rel = switch_keycap / 2 + stack_cap_clear;
matrix_centred_req = max(cap_edge_rel + 2 * (boards_matrix_board / 2 + behind_matrix),
                         2 * (equip_start_rel + usb_front + boards_matrix_board / 2) - cap_edge_rel);
tail_req = max(max(tail_claims_rel) - top_last_rel, layout_matrix_centred ? matrix_centred_req : 0);

// EQUAL BANDS (owner, 2026-09-26): the space before the left hand, between
// the hands and after the right hand are the same - the largest any of them
// needs. Measured as the plan drawing labels them: body end to the first
// key centre, last left key to the first right key, last key to the tail.
// The tail is sized by its own contents (above) and is NOT one of the equal
// bands since the matrix was centred in it (owner, 2026-09-26).
band = layout_equal_bands ? max(mouth_req, layout_gap) : undef;
// THE GAP BETWEEN THE HANDS MATCHES THE KEYS-TO-MATRIX GAP (owner, same
// day): the clear space from the last left cap to the first right cap equals
// the clear space from the last cap to the matrix window's near edge. The
// matrix is centred in the tail, so that space is known before the right
// hand is placed: (cap slot edge + tail) / 2 - half window - half cap.
matrix_clear = (cap_edge_rel + tail_req) / 2 - openings_matrix_window / 2 - switch_keycap / 2;
gap_c2c = layout_gap_matches_matrix ? max(layout_gap, matrix_clear + switch_keycap)
        : layout_equal_bands ? band : layout_gap;
x_lh0 = layout_equal_bands ? band : mouth_req;
x_gap0 = x_lh0 + lh_run;
x_rh0 = x_gap0 + gap_c2c;
x_tail0 = x_rh0 + rh_run;
// -------------------------------------------------------------- keys ------
function key_id(k) = k[0];
function key_face(k) = k[1];
function key_n(k) = ord(k[0][2]) - 48;
function count(cl) = len([for (k = keys) if (k[6] == cl) 1]);
function lerp(a, b, t) = a + (b - a) * t;

// Provisional positions, used only while a key's x/y is null.
function prov_xy(k) =
    let(cl = k[6], i = key_n(k) - 1, n = count(cl), c = W / 2)
    cl == "left_hand"  ? [x_lh0 + cum(layout_lh_gaps, i), c + layout_lh_offsets[i]] :
    cl == "right_hand" ? [x_rh0 + cum(layout_rh_gaps, i), c + layout_rh_offsets[i]] :
    cl == "left_thumb" ? [x_lh0 + lt_rel[i], c + lt_dy[i]] :
    cl == "right_thumb" ? rt_xy(i) : [0, 0];

// The thumb rest: the gap in the middle of the left-thumb line.
lt_rest_xy = [x_lh0 + (lt_rel[1] + lt_rel[2]) / 2, W / 2];
rt_rest = [x_rh0, 0] + rt_rest_rel;
// The thumb keys either side of each rest, as groups: one oak slot each
// when stack.cap_holes is "slot", as the top has one per hand.
function thumb_slots() = [for (cl = ["left_thumb", "right_thumb"])
    let(r = cl == "left_thumb" ? lt_rest_xy[0] : rt_rest[0], ks = cluster_keys(cl))
    for (before = [true, false]) let(g = [for (k = ks) if ((key_xy(k)[0] < r) == before) k]) if (len(g) > 0) g];
// Right-thumb control switches, either side of the rest (ADR 0010).
function rt_xy(i) = [x_rh0, 0] + rt_rel(i);
// NO SPARE-SWITCH CUTOUTS (owner, 2026-09-26: the right thumb is "only the
// three", the left thumb the four in a line). ADR 0010 reserved three; the
// chain bits stay reserved (config/key-layout.yaml), the cutouts do not.
spare_xy = [];

// THE TAIL END, and so the length. Past the last top key: its cluster board's
// overhang, a clearance, and the etherCON's depth behind the tail face - the
// connector cannot sit under the key boards (drc.echo, etherCON height). The
// underside's right-thumb cluster must also be inside.
top_last = max([for (k = keys) if (k[1] == "top") key_xy(k)[0]]);
rt_last = max([for (k = keys) if (k[1] == "bottom") key_xy(k)[0]]);
// THE LED MATRIX IS ON THE TOP FACE, after the last key (owner, 2026-09-26):
// the Matrix board face up under the plate, past the last key board.
matrix_near_x = top_last + plate_cutout / 2 + tail_margin + layout_tail_clear + boards_matrix_board / 2;
function matrix_x(l) = layout_matrix_centred ? (top_last + cap_edge_rel + l) / 2 : matrix_near_x;

L = top_last + tail_req;
x_in1 = L - ends_tail_cap_t;
matrix_xy = [matrix_x(L), W / 2];
// Where an X section cuts: a number, a key id, or "matrix" for its centre.
// A Y cut through a named key goes through its Y (its row along the body).
function cut_pos() = cut_key == "" ? cut_at : cut_key == "matrix" ? matrix_xy[0] :
        cut_key == "kb_mount" ? kb_mounts("left_hand")[2][cut == "y" || cut == "y2d" ? 1 : 0] : cut_key == "ribbon" ? (cut == "y" || cut == "y2d" ? chain_y : chain_x("left_hand"))
        : key_xy(key_by_id(cut_key))[cut == "y" || cut == "y2d" ? 1 : 0];

function placed(k) = !is_undef(k[2]) && !is_undef(k[3]);
function key_xy(k) = placed(k) ? [plate_x0 + k[3], plate_y0 + k[2]] : prov_xy(k);
function key_rot(k) = k[4];
top_keys = [for (k = keys) if (key_face(k) == "top") k];
bottom_keys = [for (k = keys) if (key_face(k) == "bottom") k];
function cluster_keys(cl) = [for (k = keys) if (k[6] == cl) k];
function xs(list) = [for (k = list) key_xy(k)[0]];
function key_by_id(id) = [for (k = keys) if (k[0] == id) k][0];

// ----------------------------------------------------------- colours ------
C_OAK = [0.71, 0.53, 0.33];
C_OAK_DARK = [0.60, 0.43, 0.26];
C_ACRYLIC = [0.88, 0.93, 0.98, 0.55];
C_ALU = [0.78, 0.80, 0.83];
C_PCB = [0.16, 0.42, 0.24];
C_SWITCH = [0.18, 0.18, 0.20];
C_CAP = [0.93, 0.91, 0.86];
C_SPARE = [0.85, 0.20, 0.60];
C_STEEL = [0.55, 0.57, 0.60];
C_BRASS = [0.78, 0.62, 0.33];
// A PARTS ENVELOPE is not a part: it is the volume a board's components may
// fill, which clash.txt checks against everything else. Translucent amber, so
// no render shows it as a second board.
C_ENVELOPE = [0.95, 0.72, 0.25, 0.35];
C_CONN = [0.25, 0.25, 0.27];
C_LED = [1.0, 0.75, 0.30];
C_FROSTED = [0.94, 0.95, 0.97, 0.85];

// ----------------------------------------------------------- clipping -----
module clip_space() {
    big = 4 * L;
    if (cut == "y") translate([-big / 2, cut_pos() - big, -big / 2]) cube(big);
    else if (cut == "x") translate([cut_pos(), -big / 2, -big / 2]) cube([cut_depth, big, big]);
}
// Every solid goes through P() WITH A NAME, so colour survives a section cut
// and the clash check can pull any one solid out on its own:
//   only = "<id>"      draw just that solid (tools/cad.py clash)
//   list_solids = true  echo every solid's id (the clash check's inventory)
only = "";
list_solids = false;
function id_match(h, id) = h == id || (h[len(h) - 1] == "*" && len(id) >= len(h) - 1
    && (len(h) == 1 || [for (i = [0 : len(h) - 2]) id[i]] == [for (i = [0 : len(h) - 2]) h[i]]));
module P(c, shell = false, id = "") {
    assert(id != "", "every solid needs an id - the clash check cannot see an unnamed one");
    if (list_solids) echo("SOLID", id);
    // highlight: solids named in it are drawn bright yellow and the rest
    // faded, so one assembly can be picked out of the body in a render. An
    // entry ending in "*" matches every id that starts with the rest of it.
    hl = len(highlight) > 0;
    cc = hl && len([for (h = highlight) if (id_match(h, id)) 1]) > 0 ? [1.0, 0.85, 0.0]
       : hl ? [c[0], c[1], c[2], 0.18]
       : (shell && ghost_shell) ? [c[0], c[1], c[2], 0.25] : c;
    if (only == "" || only == id) color(cc)
        if (cut == "none") children();
        else if (cut == "y2d")
            mirror([0, 1]) section_2d() rotate([90, 0, 0]) translate([0, -cut_pos(), 0]) children();
        else if (cut == "x2d")
            rotate(-90) section_2d() rotate([0, -90, 0]) translate([-cut_pos(), 0, 0]) children();
        else intersection() { children(); clip_space(); }
}

// The part's section in the plane z = 0. projection(cut = true) warns
// "Projection() failed" on a part that never reaches the plane (a side
// lamina, on the centreline), and a build that tolerated that warning would
// tolerate a real failure too. A 0.02 mm slab first makes a miss an empty
// result, not an error.
module section_2d() {
    projection() intersection() {
        children();
        translate([-1e4, -1e4, -0.01]) cube([2e4, 2e4, 0.02]);
    }
}

// ================================================================ 2D ======
// Each flat part in its OWN sheet frame, as it goes to the cutter. The
// assembly places these; the DXF exports are exactly these.

module rrect(x, y, r = 0.5) {
    offset(r) offset(-r) square([x, y]);
}
// SANDED EDGES (stack.edge_r). A panel's long edges: its (y, z) section
// with every corner rounded, run the panel's length. A cap's outer face:
// rounded all round, the inner face square where it meets the body.
module sanded_panel(len, t) {
    rotate([90, 0, 90]) linear_extrude(len) rrect(W, t, stack_edge_r);
}
module sanded_cap(t) {
    hull() {
        linear_extrude(t - stack_edge_r) rrect(W, T, stack_edge_r);
        translate([0, 0, t - stack_edge_r]) minkowski() {
            linear_extrude(EPS) offset(-stack_edge_r) square([W, T]);
            sphere(stack_edge_r, $fn = 16);
        }
    }
}
module cutout_at(xy, rot, s) {
    translate(xy) rotate(rot) square([s, s], center = true);
}

// Key plate: the cassette's top, in the plate's own frame = model XY minus
// origin. A clearance hole at each column, for the screw that ties the plate
// to its standoff (ADR 0025).
module plate_top_2d() {
    difference() {
        translate([0, stack_groove_clear]) square([plate_x1 - x_in0, u_w - 2 * stack_groove_clear]);
        translate([-plate_x0, -plate_y0]) {
            for (k = top_keys) cutout_at(key_xy(k), key_rot(k), plate_cutout);
            for (m = columns()) translate(m) circle(d = hardware_col_plate_hole);
        }
    }
}

// Oak top: the wood ON TOP of the key plate, full width. One hole per key
// (or one slot per hand), which the cap travels in. Nothing else goes
// through it: the column screws' heads sit in blind pockets in its underside
// (ADR 0025), so the playing face is unbroken. The side grooves and the
// pockets are NOT in this outline: they are a saw cut and a drilled blind
// pocket, not through-cuts, and export separately (oak_grooves_2d,
// oak_pockets_2d). Frame: model XY minus [x_in0, 0].
module oak_top_2d() {
    difference() {
        square([x_in1 - x_in0, W]);
        translate([-x_in0, 0])
            if (stack_cap_holes == "slot")
                for (cl = ["left_hand", "right_hand"]) keys_2d(cluster_keys(cl), switch_keycap + 2 * stack_cap_clear);
            else
                for (k = top_keys) translate(key_xy(k)) rotate(key_rot(k))
                    square(switch_keycap + 2 * stack_cap_clear, center = true);
        translate([-x_in0, 0]) translate(matrix_xy) square(openings_matrix_window, center = true);
    }
}

// The U's floor. Thumb recesses are the through-cuts (ADR 0009: "oak
// thickness sets the inset depth"), plus the U-bolt's leg holes. Full width;
// grooves as for the oak top. Frame: model XY minus [x_in0, 0].
module oak_bottom_2d() {
    difference() {
        square([x_in1 - x_in0, W]);
        translate([-x_in0, 0]) {
            if (stack_cap_holes == "slot")
                for (g = thumb_slots()) keys_2d(g, rc);
            else
                for (k = bottom_keys) translate(key_xy(k)) rotate(key_rot(k)) square(rc, center = true);
            for (s = spare_xy) translate(s) square(switch_keycap + 2 * thumb_recess_clear, center = true);
            for (u = ubolt_legs()) translate(u) circle(d = ubolt_hole_d);
        }
    }
}

// Where a thumb cluster's switches are.
function thumb_pts(cl) = [for (k = cluster_keys(cl)) key_xy(k)];
// THE BOTTOM PLATE (owner, 2026-09-29; ADR 0025): one aluminium plate the
// length of the main board, on the oak bottom's inside face, where the two
// thumb plates were - the cassette's floor. It carries the thumb switches'
// cutouts, the U-bolt's leg holes and a stud at every one of the main
// board's mounts, pressed in from its underside. Across, as the key plate;
// along, from the mouth cap to short of J-UMB at the tongue's end: J-UMB's
// through-hole tails stand below the tongue, and behind it the etherCON's
// adapter stands on the oak (the connector stands on the floor, ec_clear
// above it). Frame: as the key plate's, model XY minus [x_in0, u_y0].
// Its extent, bplate_x1 and bplate_y, is set below the etherCON's placement.
module plate_bottom_2d() {
    difference() {
        translate([0, stack_groove_clear]) square([bplate_x1 - x_in0, u_w - 2 * stack_groove_clear]);
        translate([-plate_x0, -plate_y0]) {
            for (k = bottom_keys) cutout_at(key_xy(k), key_rot(k), plate_cutout);
            for (u = ubolt_legs()) translate(u) circle(d = ubolt_hole_d);
            // the main board's studs, pressed in from the plate's underside
            for (c = cb_standoffs) translate(c) circle(d = hardware_stud_hole);
        }
    }
}

// The acrylic side: one sheet, standing in a groove in each oak panel.
// Frame: X along, Y = model Z from the side's bottom edge.
module side_2d() { square([x_in1 - x_in0, z_side1 - z_side0]); }

// The grooves, for the shop: one line pair per side, groove_depth deep, cut
// along each oak panel's inner face. A saw or router pass - the ONE operation
// in the stack that is not a through-cut, and deliberately so: it is what
// holds the sides between the oak. Frame: as the oak panels.
module oak_grooves_2d() { for (y = side_y) translate([0, y - stack_groove_clear]) square([x_in1 - x_in0, groove_w]); }

// End caps, full cross-section. Frame: X = model Y, Y = model Z.
module mouth_cap_2d() {
    difference() {
        rrect(W, T, stack_edge_r);
        translate(tube_yz) circle(d = ends_tube_hole_d);
    }
}
tube_yz = [W / 2, z_floor + cavity_h / 2];

// The NE8FAV (ADR 0021), rear-mounted: flange and body behind the tail cap,
// soldered to the umbilical adapter, which stands parallel to the cap. Its
// flange is square, so ethercon.rotated turns only the latch: false puts the
// PUSH tab on top, the contact rows above the axis and G below it.
ec_rot = ethercon_rotated ? 90 : 0;
ec_fl = ethercon_rotated ? [ethercon_flange_h, ethercon_flange_w] : [ethercon_flange_w, ethercon_flange_h];   // [across Y, height Z]
ec_clear = 0.3;    // drawing convention: connector envelope to the floor
// THE CONNECTOR STANDS ON THE FLOOR (owner, 2026-09-26: raise the body's
// thickness rather than pocket the oak bottom): the flange's lower edge
// ec_clear above the oak bottom, the axis half a flange above that.
ec_c = [W / 2 + ethercon_offset_y, z_floor + ec_clear + ec_fl[1] / 2];    // etherCON centre on the tail face
ec_panel_x = L - ends_tail_cap_t;                  // the flange's front face, on the tail cap's inside face
ec_pcb_x1 = ec_panel_x - ethercon_pcb_setback;     // the adapter's front face
ua_x0 = ec_pcb_x1 - boards_umb_adapter_t;          // the adapter's rear face
// The bottom plate's end, short of J-UMB, and its width, as the key plate's.
bplate_x1 = ua_x0 - boards_umb_joint_d - boards_board_clear;
bplate_y = [u_y0 + stack_groove_clear, W - u_y0 - stack_groove_clear];
// The panel holes, upper left and lower right seen from the front ([ds]);
// from the front, +Y is on the right. (Y, Z) on the tail face.
ec_holes = [for (s = [-1, 1]) ec_c + s * [ethercon_hole_dx, -ethercon_hole_dy] / 2];
// A point given (across, up) from the axis in the connector's own frame, on the tail face.
function ec_pt(p) = ec_c + (ethercon_rotated ? [p[1], -p[0]] : p);
// THE TAIL CAP'S RECESS: the NE8FAV takes a panel of ethercon.panel_max at
// most, and the cap is thicker, so a pocket from outside leaves that much
// oak where the flange clamps. It takes the flange's outline, the PUSH tab
// (which stands in it, in front of the panel), and a margin for the cable
// connector's shell and a thumb. A router pass, like the USB-C overmould
// pocket: the DXF carries the through-cuts only.
ec_panel_t = min(ethercon_panel_max, ends_tail_cap_t);
function ethercon_fl_top() = ethercon_flange_h / 2;   // the flange's edge above the axis, in the connector's frame
ec_recess_d = ends_tail_cap_t - ec_panel_t;
module ec_recess_2d() {
    offset(r = ethercon_recess_margin) hull() {
        translate(ec_c) square(ec_fl, center = true);
        for (s = [-1, 1]) translate(ec_pt([s * ethercon_tab_w / 2, ethercon_tab_top])) circle(d = EPS * 10);
    }
}
// The USB-C extension's receptacle (owner, 2026-09-26): beside the
// etherCON, inside the sides, at the cavity's mid height. Stood on end
// (openings.usb_slot_portrait) it fits the lane between the etherCON's
// flange and the side, and sits centred in it, so the oak web to the flange
// and the room to the side share what the lane has spare.
usb_web_min = 2;   // drawing convention: oak between two tail-face cutouts
usb_sz = openings_usb_slot_portrait ? [openings_usb_slot_h, openings_usb_slot_w] : [openings_usb_slot_w, openings_usb_slot_h];   // [across Y, height Z]
usb_lane = [ec_c[0] + ec_fl[0] / 2, W - u_y0];   // flange edge to the side's inside face
usb_c = [(usb_lane[0] + usb_lane[1]) / 2, z_floor + cavity_h / 2];
// THE OVERMOULD POCKET (openings.usb_overmold): from the tail face down to a
// thin panel, so the plug's overmould reaches the receptacle, whose nose
// passes the panel's slot with its face level with the pocket floor. A
// router pass, like the counterbores: the DXF carries the through-cut slot.
usb_om = openings_usb_slot_portrait ? [openings_usb_overmold[1], openings_usb_overmold[0]] : openings_usb_overmold;   // [across Y, height Z]
usb_pocket_d = ends_tail_cap_t - openings_usb_panel_t;
usb_cut_y = max(usb_sz[0], usb_om[0]);   // the widest USB-C cutout on the tail face, across

module tail_cap_2d() {
    difference() {
        rrect(W, T, stack_edge_r);
        translate(ec_c) circle(d = ethercon_bore_d);
        for (h = ec_holes) translate(h) circle(d = ethercon_hole_d);
        translate(usb_c) square(usb_sz, center = true);
    }
}
// The matrix window: frosted acrylic, flush with the oak top, on an oak lip
// (owner, 2026-09-26). The acrylic is the rebate's size less a fit clearance.
matrix_rebate = openings_matrix_window + 2 * openings_matrix_lip;
module matrix_window_2d() { translate(matrix_xy) offset(r = 0.5) offset(delta = -0.6) square(matrix_rebate, center = true); }
// Rebates in the oak top's upper face - a router pass, like the grooves, so
// exported on their own. Frame: as the oak panels.
module oak_rebates_2d() { translate([-x_in0, 0]) translate(matrix_xy) square(matrix_rebate, center = true); }
// THE COLUMN SCREWS' POCKETS (ADR 0025): blind, drilled up into the oak top's
// underside over each column screw's head, which bears on the key plate. A
// drill, not a through-cut, so exported on their own, like the grooves and
// the rebates; their depth is the head's and a clearance
// (drc.echo "column screw pockets leave wood over them"). Frame: as the oak panels.
col_pocket_depth = hardware_col_screw_head_h + hardware_col_pocket_clear;
module oak_pockets_2d() { translate([-x_in0, 0]) for (m = columns()) translate(m) circle(d = hardware_col_pocket_d); }

// --------------------------------------------------------- features ------
// Each key's square, unioned, then CLOSED (grow, shrink) so squares closer
// than 2 x close merge into one outline that follows the keys round an
// offset or a side-by-side pair. Hulling key to key instead left diagonal
// wedges wherever the order zig-zags across a pair.
module keys_2d(ks, s, close = 1.5) {
    offset(delta = -close) offset(delta = close)
        for (k = ks) translate(key_xy(k)) rotate(key_rot(k)) square(s, center = true);
}
   // drawing convention: board edge past the outermost switch body
// A top cluster board: the switch footprints, chained, grown to the board
// width over a single line (switch.cluster_pcb_w). Outline is an M3 output.
module cluster_window_2d(ks) {
    offset(delta = (switch_cluster_pcb_w - plate_cutout) / 2) keys_2d(ks, plate_cutout, close = 3);
}

// Tail equipment: the Matrix, the etherCON and the USB-C extension.
// TIGHT TO THE WINDOW (owner, 2026-09-26: "led matrix tighter to the
// acrylic"). The key plate stops short of the Matrix, so the board's top
// face sits against the oak top's underside and its LEDs stand up into the
// window opening through the oak lip, under the acrylic.
matrix_board_z = z_oak_top_bot - boards_matrix_t;
matrix_top_z = z_oak_top_bot + boards_matrix_led_h;              // LED tops
// The key plate ends before the Matrix, so past it the lid is the oak alone.
plate_x1 = matrix_xy[0] - boards_matrix_board / 2 - 1;
// The USB-C extension's plug, in the Matrix's mouth or tail edge.
usb_plug_x0 = openings_matrix_usb_to_tail ? matrix_xy[0] + boards_matrix_board / 2 : matrix_xy[0] - boards_matrix_board / 2 - openings_usb_plug_l;
// The tail equipment starts at the first of that plug and J-UMB, behind the
// etherCON's adapter.
tail_equip_x = min(usb_plug_x0, ua_x0 - boards_umb_joint_d);

// U-bolt in the inter-hand gap on the bottom face (ADR 0009); legs ACROSS the
// body, since the shortened gap has no room along it beside the left thumb line.
// Its legs pass the oak bottom and the bottom plate, which spreads its pull
// over the oak (ADR 0025).
ubolt_c = [(x_gap0 + x_rh0) / 2, W / 2];
function ubolt_legs() = [for (s = [-1, 1]) ubolt_c + [0, s * hardware_ubolt_span / 2]];
ubolt_hole_d = hardware_ubolt_rod_d + hardware_ubolt_hole_clear;   // the legs' clearance hole in the oak and the bottom plate

// ================================================================ 3D ======

// The etherCON housing's bottom below the floor, if the connector is low.

module lam(z, t, c, shell = true, id = "") {
    P(c, shell, id) translate([0, 0, z]) linear_extrude(t) children();
}

module lid(dz = 0) {
    translate([0, 0, dz]) {
        P(C_OAK, true, "oak top") translate([x_in0, 0, z_oak_top_bot + explode]) intersection() { sanded_panel(x_in1 - x_in0, oak_top_t); difference() {
            linear_extrude(oak_top_t) oak_top_2d();
            translate([0, 0, -EPS]) linear_extrude(stack_groove_depth + EPS) oak_grooves_2d();
            translate([0, 0, -EPS]) linear_extrude(col_pocket_depth + EPS) oak_pockets_2d();
            translate([0, 0, oak_top_t - openings_matrix_acrylic_t]) linear_extrude(openings_matrix_acrylic_t + EPS) oak_rebates_2d();
        } }
        lam(z_plate_bot + explode / 2, plate_thickness, C_ALU, false, "key plate")
            translate([plate_x0, plate_y0]) plate_top_2d();
    }
}

module u_channel() {
    P(C_OAK, true, "oak bottom") translate([x_in0, 0, -explode]) intersection() { sanded_panel(x_in1 - x_in0, oak_bottom_t); difference() {
        linear_extrude(oak_bottom_t) oak_bottom_2d();
        translate([0, 0, oak_bottom_t - stack_groove_depth]) linear_extrude(stack_groove_depth + EPS) oak_grooves_2d();
    } }
    // Each side: one sheet, bottom edge in the bottom groove, top edge in the top.
    // Exploded, the sides move out and down so the boards between them show.
    for (i = [0, 1])
        P(C_ACRYLIC, true, str("side ", i == 0 ? "left" : "right")) translate([x_in0, side_y[i] + stack_side_t + (i == 0 ? -1 : 1) * explode * 1.5, z_side0 - explode * 0.6]) rotate([90, 0, 0])
            linear_extrude(stack_side_t) side_2d();
}

// render(): the preview renderer (OpenCSG) drops the cut-outs of an
// intersection() it has to draw as CSG, so without it the tail face showed
// neither the USB-C slot nor the flange screw holes.
module caps() {
    P(C_OAK_DARK, true, "mouth cap") translate([ends_mouth_cap_t - explode / 3, 0, 0]) rotate([90, 0, 90]) mirror([0, 0, 1])
        render() intersection() { linear_extrude(ends_mouth_cap_t) mouth_cap_2d(); sanded_cap(ends_mouth_cap_t); }
    P(C_OAK_DARK, true, "tail cap") translate([x_in1 + explode / 3, 0, 0]) rotate([90, 0, 90])
        render() difference() {
            intersection() { linear_extrude(ends_tail_cap_t) tail_cap_2d(); sanded_cap(ends_tail_cap_t); }
            translate([usb_c[0] - usb_om[0] / 2, usb_c[1] - usb_om[1] / 2, openings_usb_panel_t]) cube([usb_om[0], usb_om[1], usb_pocket_d + EPS]);
            if (ec_recess_d > 0) translate([0, 0, ec_panel_t]) linear_extrude(ec_recess_d + EPS) ec_recess_2d();
        }
}

module switch_at(xy, rot, top, name, spare = false) {
    // Seat (collar underside) on the plate's key face.
    tf = top ? [xy[0], xy[1], z_plate_top + explode / 2] : [xy[0], xy[1], z_floor - explode];
    // P() OUTSIDE the placement: a section cuts in world coordinates, and a
    // P() inside translate() cut every switch in its own frame instead.
    // Trimmed above the collar to Gateron's drawn cover (switch.cover_*): the
    // third-party mesh draws its latches up there, where the vendor has none.
    P(C_SWITCH, false, str("switch ", name)) translate(tf) rotate([top ? 0 : 180, 0, rot]) intersection() {
        import("vendor/ks33.stl");
        union() {
            translate([-10, -10, -10]) cube([20, 20, 10 + switch_collar_t]);
            hull() {
                translate([-switch_cover_w / 2, -switch_cover_w / 2, 0]) cube([switch_cover_w, switch_cover_w, switch_cover_straight_h]);
                translate([-switch_cover_top_w / 2, -switch_cover_top_w / 2, 0]) cube([switch_cover_top_w, switch_cover_top_w, switch_housing_top_above_seat]);
            }
            translate([-switch_cover_top_w / 2, -switch_cover_top_w / 2, 0]) cube([switch_cover_top_w, switch_cover_top_w, 20]);
        }
    }
    // THE CAP (MT165-MX, ADR 0002): a hollow shell, and the MX cross socket the
    // stem enters, as separate solids so the clash check lets only the SOCKET meet
    // the switch; the shell must clear it at rest and all the way down.
    P(spare ? C_SPARE : C_CAP, false, str("cap ", name)) translate(tf) rotate([top ? 0 : 180, 0, rot]) cap_shell(0);
    P(spare ? C_SPARE : C_CAP, false, str("cap socket ", name)) translate(tf) rotate([top ? 0 : 180, 0, rot]) cap_socket(0);
    // The cap's TRAVEL: the space its shell sweeps when pressed (it includes where
    // the cap sits at rest: clash-allow.yaml says why). Only for the clash check - drawn nowhere else - so a skirt that would
    // land on the switch, the plate or the oak at the bottom of its stroke is caught.
    if (only == str("travel ", name) || list_solids)
        P(C_CAP, false, str("travel ", name)) translate(tf) rotate([top ? 0 : 180, 0, rot])
            difference() {
                union() {
                    cap_shell(switch_total_travel);
                    translate([0, 0, cap_sk - switch_total_travel]) linear_extrude(switch_total_travel)
                        difference() { square(switch_keycap, center = true); square(switch_keycap - 2 * switch_keycap_wall, center = true); }
                }
                // The stem and actuator move WITH the cap: measured off the mesh,
                // 11.0 x 5.6 above the housing top. Leaving it out of the sweep keeps
                // the pressed cap from meeting the switch's (static) stem.
                translate([0, 0, -1]) linear_extrude(switch_keycap_top_above_seat + 2) square([11.4, 6.0], center = true);
            }
}
// The cap in the switch's frame (seat at z = 0), pressed by dz: its skirt's
// bottom is cap_sk above the seat at rest.
cap_sk = switch_keycap_top_above_seat - switch_keycap_h;
cap_ceiling = switch_keycap_top_above_seat - switch_keycap_top_t;     // the inside of its top
function cap_w_at(z) = switch_keycap + (switch_keycap_top_w - switch_keycap) * z / switch_keycap_h;   // outer, z above the skirt
module cap_shell(dz) {
    hi = switch_keycap_h - switch_keycap_top_t;
    translate([0, 0, cap_sk - dz]) difference() {
        linear_extrude(switch_keycap_h, scale = switch_keycap_top_w / switch_keycap) square(switch_keycap, center = true);
        translate([0, 0, -EPS]) linear_extrude(hi + EPS, scale = (cap_w_at(hi) - 2 * switch_keycap_wall) / (switch_keycap - 2 * switch_keycap_wall))
            square(switch_keycap - 2 * switch_keycap_wall, center = true);
    }
}
module cap_socket(dz) {
    translate([0, 0, switch_keycap_top_above_seat - switch_keycap_boss_below_top - dz]) cylinder(d = switch_keycap_socket_d, h = switch_keycap_boss_below_top - switch_keycap_top_t + EPS);
}

module keys_3d() {
    for (k = keys) switch_at(key_xy(k), key_rot(k), key_face(k) == "top", k[0]);
    for (i = [0 : 1 : len(spare_xy) - 1]) switch_at(spare_xy[i], 0, false, str("spare ", i + 1), true);
}

module bottom_plate_3d() {
    lam(z_floor - explode * 0.5, plate_thickness, C_ALU, false, "bottom plate")
        translate([plate_x0, plate_y0]) plate_bottom_2d();
}

// A KEY BOARD IS A RECTANGLE ACROSS THE CAVITY (owner, 2026-09-27, ADR 0020
// amended: "increase that size a little bit so that we could fit the
// standoffs... anchor it in each corner"): from the side walls less the board
// clearance, and along the body past its outermost cutouts by kb_end_margin at
// the mouth end and kb_tail_margin at the tail. A column stands at each
// corner (ADR 0025).
// Corners rounded by a drawing convention. The PCB's Edge.Cuts come from this.
kb_corner_r = 1;        // drawing convention: board corner radius
function kb_rect(cl) = let(x = xs(cluster_keys(cl)))
    [min(x) - plate_cutout / 2 - cluster_margin, u_y0 + boards_board_clear,
     max(x) + plate_cutout / 2 + tail_margin, W - u_y0 - boards_board_clear];
module key_board_2d(cl) {
    r = kb_rect(cl);
    offset(r = kb_corner_r) offset(delta = -kb_corner_r) translate([r[0], r[1]]) square([r[2] - r[0], r[3] - r[1]]);
}

// THE COLUMNS (owner, 2026-09-29; ADR 0025): at each corner of each key board
// one column ties the key plate to the bottom plate through both boards. From
// the bottom: a PEM FHL-M2.5 stud pressed into the bottom plate, head flush in
// its underside; a spacer; the main board; an M2.5 female-female hex standoff
// threaded onto the stud, clamping the main board, as long as the gap up to the
// key board; the key board; a spacer; the key plate; an M2.5 low-head screw down
// through the plate into the standoff, its head in a pocket in the oak top.
// The spacers set both boards' depths; the standoff's length is the gap. The
// DRC below checks the thread at both ends of the standoff, the studs' edge
// distance in the bottom plate and the screws' heads on the key plate.
function rect_gap(p, c, sz, r) = let(d = [cos(-r) * (p[0] - c[0]) - sin(-r) * (p[1] - c[1]), sin(-r) * (p[0] - c[0]) + cos(-r) * (p[1] - c[1])],
                                   e = [max(abs(d[0]) - sz[0] / 2, 0), max(abs(d[1]) - sz[1] / 2, 0)]) norm(e);
function cutout_gap(p) = min([for (k = top_keys) rect_gap(p, key_xy(k), [plate_cutout, plate_cutout], key_rot(k))]);
// from a point to the nearest cap hole or slot in the wood top (a slot is the
// union of its keys' holes; the 1.5 mm closing between them is ignored, which
// errs toward a larger gap only where two holes' corners nearly meet)
function cap_gap(p) = min([for (k = top_keys) rect_gap(p, key_xy(k), [1, 1] * (switch_keycap + 2 * stack_cap_clear), key_rot(k))]);
function kb_mounts(cl) = let(r = kb_rect(cl), e = hardware_kb_mount_inset)
    [[r[0] + e, r[1] + e], [r[0] + e, r[3] - e], [r[2] - e, r[1] + e], [r[2] - e, r[3] - e]];
kb_gap = hardware_kb_spacer_l;                               // plate underside to board top: what the mount stacks there
kb_top = z_plate_top - switch_pcb_below_seat;                 // the key boards' top face
function columns() = [for (cl = ["left_hand", "right_hand"], m = kb_mounts(cl)) m];
col_standoff_e = hardware_col_standoff_af / cos(30);          // the standoff's hex across its corners
col_keep_r = col_standoff_e / 2 + hardware_kb_mount_float;    // what a board keeps clear round a column's hex, off its axis
// Where the ribbon runs under a key board, from its connector's mouth to the
// board's far edge: no parts there - the model's parts envelope leaves it out.
// The key board's chain header with its plug, as a rectangle [x0, y0, x1, y1]:
// no other part there; its pin tails stop short of the plate (drc.echo
// "J-CHAIN pin tails clear of the key plate").
function kb_chain_rect(cl) = let(sp = chain_span(chain_x(cl), chain_dir(cl)))
    [sp[0], chain_y - boards_chain_hdr_l / 2, sp[1], chain_y + boards_chain_hdr_l / 2];
// Where the key board's chain header's pin tails come up through the board:
// outside every switch body (chain_clear), and short of the plate (drc.echo
// "J-CHAIN pin tails clear of the key plate").
function chain_tail_rect_at(x, d) = let(a = x - d * boards_chain_hdr_pin_back, b = x - d * (boards_chain_hdr_pin_back - 1.27))
    [min(a, b) - 1, chain_y - 6.35 / 2 - 1, max(a, b) + 1, chain_y + 6.35 / 2 + 1];
function chain_tail_rect(cl) = chain_tail_rect_at(chain_x(cl), chain_dir(cl));

module cluster_boards() {
    for (cl = ["left_hand", "right_hand"]) {
        P(C_PCB, false, str("board ", cl)) translate([0, 0, kb_top - boards_key_board_t + explode * 0.25])
            linear_extrude(boards_key_board_t) difference() {
                key_board_2d(cl);
                for (m = kb_mounts(cl)) translate(m) circle(d = hardware_kb_board_hole);
            }
        // each P() places its own solid, so a section cut sees it where it is.
        // The top of each column: the spacer under the key plate and the screw
        // down through it; the standoff and the stud are the main board's.
        for (i = [0 : len(kb_mounts(cl)) - 1]) let(m = kb_mounts(cl)[i], n = str(cl, " ", i + 1)) {
            P(C_STEEL, false, str("key-board spacer ", n)) translate([m[0], m[1], z_plate_bot - hardware_kb_spacer_l + explode * 0.2])
                difference() { cylinder(d = hardware_kb_spacer_od, h = hardware_kb_spacer_l); translate([0, 0, -1]) cylinder(d = hardware_stud_attached_hole, h = hardware_kb_spacer_l + 2); }
            // the screw: its head on the key plate's top face, in the oak top's
            // pocket; its shank down through the plate, spacer and board into the standoff
            P(C_STEEL, false, str("column screw ", n)) translate([m[0], m[1], explode * 0.8]) {
                translate([0, 0, z_plate_top]) cylinder(d = hardware_col_screw_head_d, h = hardware_col_screw_head_h);
                translate([0, 0, z_plate_top - hardware_col_screw_l]) cylinder(d = 2.5, h = hardware_col_screw_l + EPS);
            }
        }
    }
}

// WHAT A KEY BOARD'S PCB IS PLACED FROM (tools/pcb.py). Body coordinates, mm:
// x along the body from the mouth, y across it, seen from above. The PCB tool
// maps these onto the board, so the switches land in the plate's cutouts and
// the ribbon connector where the ribbon's C needs it.
module pcb_geometry() {
    for (cl = ["left_hand", "right_hand"]) {
        for (k = cluster_keys(cl)) echo("PCB", cl, "switch", k[0], key_xy(k)[0], key_xy(k)[1], key_rot(k));
        echo("PCB", cl, "chain", "J-CHAIN", chain_x(cl), chain_y, chain_dir(cl), boards_chain_hdr_l, boards_chain_hdr_pin_back);
        // the hole, then what bears on the board's underside (the column's
        // standoff, across its corners) and on its top copper (the spacer),
        // each grown by how far it can sit off the column's axis
        for (m = kb_mounts(cl)) echo("PCB", cl, "standoff", "M2.5", m[0], m[1], hardware_kb_board_hole,
                                     col_standoff_e + 2 * hardware_kb_mount_float,
                                     hardware_kb_spacer_od + 2 * hardware_kb_mount_float);
        echo("PCB", cl, "board", "thickness", boards_key_board_t, "smt_height_max", boards_cluster_smt_h,
             "side", "switches on top, parts and ribbon connector underneath");
    }
    // THE MAIN BOARD (ADR 0017, 0021, 0022), cluster "main". Parts face UP; the
    // thumb switches come in from BELOW (their seat is on the bottom plate),
    // so their footprints go on the board's underside. Body coordinates, mm;
    // its outline is export/main-board.dxf (the U-bolt holes, the sensor slot
    // and the mounts' holes are in it; there are no edge notches).
    for (k = bottom_keys) echo("PCB", "main", "switch", k[0], key_xy(k)[0], key_xy(k)[1], key_rot(k));
    // Each ribbon's header, standing on the top face, its mouth facing along
    // the body: mouth x, centre y, which way the mouth faces (+1 the tail),
    // length, mouth to far pin row - as a key board's "chain".
    for (cl = chain_ribbon_cls) echo("PCB", "main", "chain", str("J-CHAIN-", cl == "left_hand" ? "LH" : "RH"),
                                     chain_x(cl), chain_y, chain_dir(cl), boards_chain_hdr_l, boards_chain_hdr_pin_back);
    // The Matrix's header: its insulator's extent along x, centre y, length
    // across, and the mouth's direction (+1 the tail) - the ribbon comes in
    // over the tongue.
    echo("PCB", "main", "connector", "J-MCU", jm_x0, jm_x1, jm_y, jm_sz[1], 1);
    // J-UMB: the right-angle header whose tails go down through the
    // tongue and whose posts go through the adapter; its insulator's extent along x (it stands against the
    // adapter's rear face), centre y, pin count, pitch, and its row's
    // height above the top face, where it meets the adapter.
    echo("PCB", "main", "connector", "J-UMB", ua_x0 - boards_umb_joint_d, ua_x0, ec_c[0], 8, 2.54, boards_umb_joint_row_h);
    // The breath sensor: its centre, the ports toward +x (the tail), its
    // body and lead span; the slot in front of its lower port is in the DXF.
    echo("PCB", "main", "part", "U-BREATH", sensor_c[0], sensor_c[1], 0, boards_sensor_body, boards_sensor_leads);
    // The regulator block's envelope: centre, along x, across y, height.
    echo("PCB", "main", "part", "REGULATOR-BLOCK", tall_c[0][0], tall_c[0][1], 0, tall_sz[0], tall_sz[1], boards_tall_h);
    // THE LED ROW (ADR 0028), one record per LED, numbered along the data
    // line from the tail: centre, rotation (180 = its data inputs toward the
    // tail, where the data comes from), courtyard along and across, height.
    for (n = [1 : lighting_led_count]) let(c = led_xy(n))
        echo("PCB", "main", "led", str("LED", n), c[0], c[1], 180, lighting_led_court[0], lighting_led_court[1], lighting_led_h);
    // Each mount (ADR 0022, ADR 0025), all on the bottom plate: centre, hole,
    // what bears on the top face (a column's standoff or an end mount's nut,
    // across its corners, with float), what bears on the underside (the
    // spacer, with float), and which kind.
    for (i = [0 : len(cb_standoffs) - 1]) let(c = cb_standoffs[i])
        echo("PCB", "main", "standoff", "M2.5", c[0], c[1], hardware_kb_board_hole,
             (i < n_cols ? col_standoff_e : hardware_mb_nut_e) + 2 * hardware_kb_mount_float,
             hardware_kb_spacer_od + 2 * hardware_kb_mount_float, i < n_cols ? "column" : "end");
    // Each U-bolt leg (ADR 0022 point 7, ADR 0025): centre, the board's hole,
    // and what bears on the top face (the washer and the nut, across its
    // corners) and the underside (the spacer), which the board keeps copper
    // and parts off.
    for (u = ubolt_legs()) echo("PCB", "main", "ubolt", "M3", u[0], u[1], 2 * ubolt_board_hole_r,
                                max(hardware_ubolt_nut_af / cos(30), hardware_ubolt_washer_od), hardware_ubolt_spacer_od);
    // How tall parts may stand: under each key board, and where none is
    // overhead; and nothing under the chain headers' plugs and hairpins, or
    // under the Matrix ribbon's level run into J-MCU.
    for (cl = ["left_hand", "right_hand"]) let(r = kb_rect(cl))
        echo("PCB", "main", "keepout", str("under key board ", cl), r[0], r[1], r[2], r[3], cb_room);
    echo("PCB", "main", "keepout", "elsewhere", cb_x[0], cb_y[0], ua_x0, cb_y[1], gap_room);
    for (cl = chain_ribbon_cls) let(sp = chain_span(chain_x(cl), chain_dir(cl)))
        echo("PCB", "main", "keepout", str("ribbon ", cl), sp[0], chain_y - boards_chain_hdr_l / 2, sp[1], chain_y + boards_chain_hdr_l / 2, 0);
    echo("PCB", "main", "keepout", "Matrix ribbon", jm_x1, jm_y - routing_mcu_ribbon_w / 2, mcu_x, jm_y + routing_mcu_ribbon_w / 2,
         jm_z + e_mb - routing_mcu_ribbon_t / 2 - cb_top);
    echo("PCB", "main", "board", "thickness", switch_pcb_t, "smt_height_max", boards_smt_h,
         "side", "parts on top; the thumb switches from below, their footprints on the underside");
}

module tail_equipment() {
    // The Matrix, face up under the top window.
    P([0.10, 0.10, 0.12], false, "Matrix board") translate([matrix_xy[0] - boards_matrix_board / 2, matrix_xy[1] - boards_matrix_board / 2, matrix_board_z])
        cube([boards_matrix_board, boards_matrix_board, boards_matrix_t]);
    P(C_LED, false, "Matrix LEDs") translate([matrix_xy[0] - boards_matrix_emitters / 2, matrix_xy[1] - boards_matrix_emitters / 2, matrix_board_z + boards_matrix_t])
        cube([boards_matrix_emitters, boards_matrix_emitters, boards_matrix_led_h]);
    // The Matrix's ribbon where it leaves the two pad rows, below the board;
    // it runs on to J-MCU (drawn with the tail wiring).
    for (i = [0, 1]) P([0.15, 0.15, 0.15], false, str("Matrix harness ", i + 1))
        translate([matrix_xy[0] - 12.7, matrix_xy[1] + (i == 0 ? -1 : 1) * 11.43 - 1.27, matrix_board_z - boards_matrix_harness_h])
            cube([25.4, 2.54, boards_matrix_harness_h]);   // rows 22.86 apart [ds]
    P(C_FROSTED, false, "matrix window") translate([0, 0, T - openings_matrix_acrylic_t + explode]) linear_extrude(openings_matrix_acrylic_t) matrix_window_2d();
    // The etherCON, an NE8FAV (ADR 0021): flange and body behind the tail
    // cap, the nose into the cap's bore, the PUSH tab in front of the flange
    // in the cap's recess. Soldered to the umbilical adapter behind it.
    P(C_CONN, false, "etherCON") union() {
        translate([ec_pcb_x1, ec_c[0] - ec_fl[0] / 2, ec_c[1] - ec_fl[1] / 2]) cube([ethercon_pcb_setback, ec_fl[0], ec_fl[1]]);
        translate([ec_panel_x - EPS, ec_c[0], ec_c[1]]) rotate([0, 90, 0]) cylinder(d = ethercon_bore_d - 0.2, h = ethercon_nose_l + EPS);
        let(t = ec_pt([0, (ethercon_fl_top() + ethercon_tab_top) / 2]), tsz = ethercon_rotated ? [ethercon_tab_top - ethercon_fl_top(), ethercon_tab_w] : [ethercon_tab_w, ethercon_tab_top - ethercon_fl_top()])
            translate([ec_panel_x + ethercon_tab_front - 3, t[0] - tsz[0] / 2, t[1] - tsz[1] / 2]) cube([3, tsz[0], tsz[1]]);
    }
    // The umbilical adapter: the flange's outline, parallel to the tail cap.
    P(C_PCB, false, "umbilical adapter") translate([ua_x0, ec_c[0] - ec_fl[0] / 2, ec_c[1] - ec_fl[1] / 2]) cube([boards_umb_adapter_t, ec_fl[0], ec_fl[1]]);
    // The USB-C extension's plug in the Matrix's tail edge, under the board.
    P([0.35, 0.35, 0.38], false, "USB-C plug") translate([usb_plug_x0, matrix_xy[1] - openings_usb_slot_w / 2, matrix_board_z - openings_usb_slot_h])
        cube([openings_usb_plug_l, openings_usb_slot_w, openings_usb_slot_h]);
    // The USB-C extension: receptacle body behind the tail cap, and a cable
    // run to the Matrix board's edge (drawn straight; it is a flexible lead).
    // Its nose passes the panel under the overmould pocket, face level with
    // the pocket floor; an earless body, clamped from behind (openings.usb_mount).
    P(C_CONN, false, "USB-C receptacle") translate([x_in1 - openings_usb_ext_depth, usb_c[0] - usb_sz[0] / 2, usb_c[1] - usb_sz[1] / 2])
        cube([openings_usb_ext_depth + openings_usb_panel_t, usb_sz[0], usb_sz[1]]);
    // Routed beside the etherCON, on the receptacle's side.
    usb_from = [openings_matrix_usb_to_tail ? matrix_xy[0] + boards_matrix_board / 2 + usb_behind : usb_plug_x0,
                matrix_xy[1], matrix_board_z - openings_usb_slot_h / 2];
    P([0.15, 0.15, 0.15], false, "USB-C lead") run([usb_from, [usb_from[0] + 4, usb_c[0], usb_from[2]],
        [x_in1 - openings_usb_ext_depth - 4, usb_c[0], usb_c[1]], [x_in1 - openings_usb_ext_depth, usb_c[0], usb_c[1]]], 4);
}

// THE LED ROW (ADR 0028): thirteen WS2815B-V1 on the main board's top face,
// down the centreline between the thumb switches' two rows of pins, LEDs up,
// lighting both acrylic sides through the cavity (ADR 0016's light path).
// Placed with the main board below.
module led_row() {
    P(C_LED, false, "LED row") for (n = [1 : lighting_led_count]) let(c = led_xy(n))
        translate([c[0] - lighting_led_body[0] / 2, c[1] - lighting_led_body[1] / 2, cb_top]) cube([lighting_led_body[0], lighting_led_body[1], lighting_led_h]);
}

// ------------------------------------------------------------ routing -----
// The breath tube runs from the mouth cap to the trap and the sensor inside
// the mouth band, against one side (routing_tube_lane); there are no looms
// since ADR 0017 - the key boards are on 1.27 mm IDC ribbons and the Matrix
// on a ribbon, both drawn below. The lane is a model choice (config/body.yaml
// routing): the clash check reports what is in it.
// Inboard of the main board's mouth-end mounts, whose studs and nuts stand
// up into the cavity beside the sides: the mount's edge band, its keep-out
// and a board clearance.
function lane_y(side, d) = let(e = (cb_y[0] - u_y0) + end_mount_in + mb_keep_d / 2 + boards_board_clear + d / 2)
    side == "left" ? u_y0 + e : W - u_y0 - e;
// A FLAT RIBBON through points: each segment is swept with the ribbon's
// cross-section turned to suit its direction - lying FLAT along and across
// the body, on edge only where it drops to a socket. Stood on edge along the
// body, a 15 mm ribbon does not fit the 12-13 mm between the thumb boards'
// (now the main board's)
// parts and the key boards' parts (found by the clash check, 2026-09-26).
module ribbon(pts, w, t = routing_ribbon_t) {
    for (i = [0 : len(pts) - 2]) let(a = pts[i], b = pts[i + 1], dv = [abs(b[0] - a[0]), abs(b[1] - a[1]), abs(b[2] - a[2])],
                                   ax = dv[0] >= dv[1] && dv[0] >= dv[2] ? 0 : dv[1] >= dv[2] ? 1 : 2,
                                   sec = ax == 0 ? [0.01, w, t] : ax == 1 ? [w, 0.01, t] : [w, t, 0.01])
        hull() { translate(a) cube(sec, center = true); translate(b) cube(sec, center = true); }
}
// A run through points, as a chain of hulled spheres.
module run(pts, d) {
    for (i = [0 : len(pts) - 2]) hull() { translate(pts[i]) sphere(d = d, $fn = 16); translate(pts[i + 1]) sphere(d = d, $fn = 16); }
}
top_z = z_plate_top - switch_pcb_below_seat - boards_key_board_t;     // top cluster boards' underside
thumb_z = z_floor + switch_thumb_pcb_below_seat + switch_pcb_t;       // the main board's top face, where the thumb switches solder
function mid_x(cl) = (min(xs(cluster_keys(cl))) + max(xs(cluster_keys(cl)))) / 2;
function sgn(side) = side == "right" ? 1 : -1;
function xspan(cl) = [min(xs(cluster_keys(cl))), max(xs(cluster_keys(cl)))];

// THE MAIN BOARD (owner, 2026-09-26: "instead of individual bottom boards,
// and the center board, maybe we can do one big long board" - ADR 0017).
// ONE flat board at the thumb boards' level carries the thumb switches, both
// thumb registers and everything the carrier did, from the mouth cap to the
// end of the right hand. Its parts face up, under the key boards; the key
// boards connect to it by ribbons. At this level it has more room
// than the centre board had: drc.echo prints it. The cb_ names
// are kept from the centre board it replaced.
function tspan(cl) = let(p = [for (q = thumb_pts(cl)) q[0]]) [min(p) - (switch_keycap + 4) / 2, max(p) + (switch_keycap + 4) / 2];
function kspan(cl) = [kb_rect(cl)[0], kb_rect(cl)[2]];   // the key board itself
tube_side = sgn(routing_tube_lane);
// Across: the full width inside the sides; the tube runs above it.
cb_y = [u_y0 + boards_board_clear, W - u_y0 - boards_board_clear];
cb_x = [x_in0 + boards_board_clear, max(kspan("right_hand")[1], tspan("right_thumb")[1])];
cb_z = thumb_z - switch_pcb_t;          // underside: where the thumb boards were
cb_top = thumb_z;
cb_room = top_z - boards_cluster_smt_h - boards_board_clear - cb_top;   // parts height under the key boards
gap_x = [kspan("left_hand")[1] + boards_board_clear, kspan("right_hand")[0] - boards_board_clear];   // nothing overhead
gap_room = z_lid_bot - boards_board_clear - cb_top;
chain = ["right_thumb", "right_hand", "left_thumb", "left_hand"];
function is_top(cl) = cl == "left_hand" || cl == "right_hand";
// Where the thumb switches' pins stand through the board's top face.
function pins_at(p, r) = len([for (k = bottom_keys) if (max(abs(key_xy(k)[0] - p[0]), abs(key_xy(k)[1] - p[1])) < ks33_stub + r) 1]) > 0;

// THE BREATH SENSOR: MPXV4006DP case 1351-01, SURFACE MOUNT (datasheet p.2),
// AT THE MOUTH END (owner, 2026-09-26, with the main board): on the far side
// from the tube, ports towards the tail, beside the breath trap - the
// shortest tube this body can have. The lower barb reaches the board's
// surface (p.7), so the board has a slot in front of it.
// Across: in from the board's edge by the wider of the lead tips and the land
// pattern's pads, + 0.5 - the pads, not the leads, must keep off the edge.
sensor_c = [cb_x[0] + 0.5 + boards_sensor_body / 2, cb_y[tube_side < 0 ? 1 : 0] + tube_side * (max(boards_sensor_leads, boards_sensor_land_w) / 2 + 0.5)];
sensor_face_x = sensor_c[0] + boards_sensor_body / 2;
p2_y = sensor_c[1] + boards_sensor_port_offset;
// The slot in the main board in front of the lower port: 1 clear of the barb all round.
port_slot_sz = [boards_sensor_port_l + 2, boards_sensor_port_d + 2];
port_slot_c = [sensor_face_x + port_slot_sz[0] / 2, p2_y];
p1_tip = [sensor_face_x + boards_sensor_port_l, sensor_c[1] - boards_sensor_port_offset, cb_top + boards_sensor_port_z[0]];
module sensor_3d() {
    P([0.20, 0.20, 0.22], false, "breath sensor") union() {
        translate([sensor_c[0] - boards_sensor_body / 2, sensor_c[1] - boards_sensor_body / 2, cb_top])
            cube([boards_sensor_body, boards_sensor_body, boards_sensor_h]);
        translate([sensor_c[0] - boards_sensor_lead_row / 2, sensor_c[1] - boards_sensor_leads / 2, cb_top]) cube([boards_sensor_lead_row, boards_sensor_leads, boards_sensor_lead_h]);
        for (i = [0, 1]) translate([sensor_face_x - EPS, sensor_c[1] + (i == 0 ? -1 : 1) * boards_sensor_port_offset, cb_top + boards_sensor_port_z[i]])
            rotate([0, 90, 0]) cylinder(d = boards_sensor_port_d, h = boards_sensor_port_l);
    }
}
sensor_room = under_keys(sensor_c, [boards_sensor_body, boards_sensor_leads]) ? cb_room : gap_room;
jm_x1 = cb_x[1] - 1;                               // J-MCU's mouth, at the main board's tail edge
jm_x0 = jm_x1 - boards_mcu_conn_w;
// THE LED ROW (ADR 0028): on the centreline, between the thumb switches' two
// rows of pins, from past the sensor to short of J-MCU. led_span is where the
// LEDs' centres may go. The row at lighting.led_pitch is centred in it, then
// shifted to the nearest place where the U-bolt station falls midway between
// two LEDs, so no LED stands between the legs; if no such place fits the
// span, it stays centred and drc.echo 'LED row off the U-bolt station' fails.
led_y = W / 2;
led_span = [sensor_c[0] + boards_sensor_lead_row / 2 + boards_board_clear + lighting_led_court[0] / 2,
            min(cb_x[1], jm_x0 - boards_board_clear) - lighting_led_court[0] / 2];
led_run = (lighting_led_count - 1) * lighting_led_pitch;
led_centred = (led_span[0] + led_span[1] - led_run) / 2;
led_fits = [for (j = [0 : lighting_led_count - 2]) let(x0 = ubolt_c[0] - (j + 0.5) * lighting_led_pitch)
            if (x0 >= led_span[0] - 1e-6 && x0 + led_run <= led_span[1] + 1e-6) x0];
led_x0 = len(led_fits) == 0 ? led_centred
       : [for (x = led_fits) if (abs(x - led_centred) == min([for (y = led_fits) abs(y - led_centred)])) x][0];
// LED n, numbered along the data line: LED 1 at the tail end, where the data
// arrives from U-LVLSHIFT; LED led_count nearest the mouth.
function led_xy(n) = [led_x0 + (lighting_led_count - n) * lighting_led_pitch, led_y];
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
