jeffmhopkins/Woody/datasheets/mechanical/TAIHAO-MT165-THCS-THT-DIMENSION-GUIDE.jpg

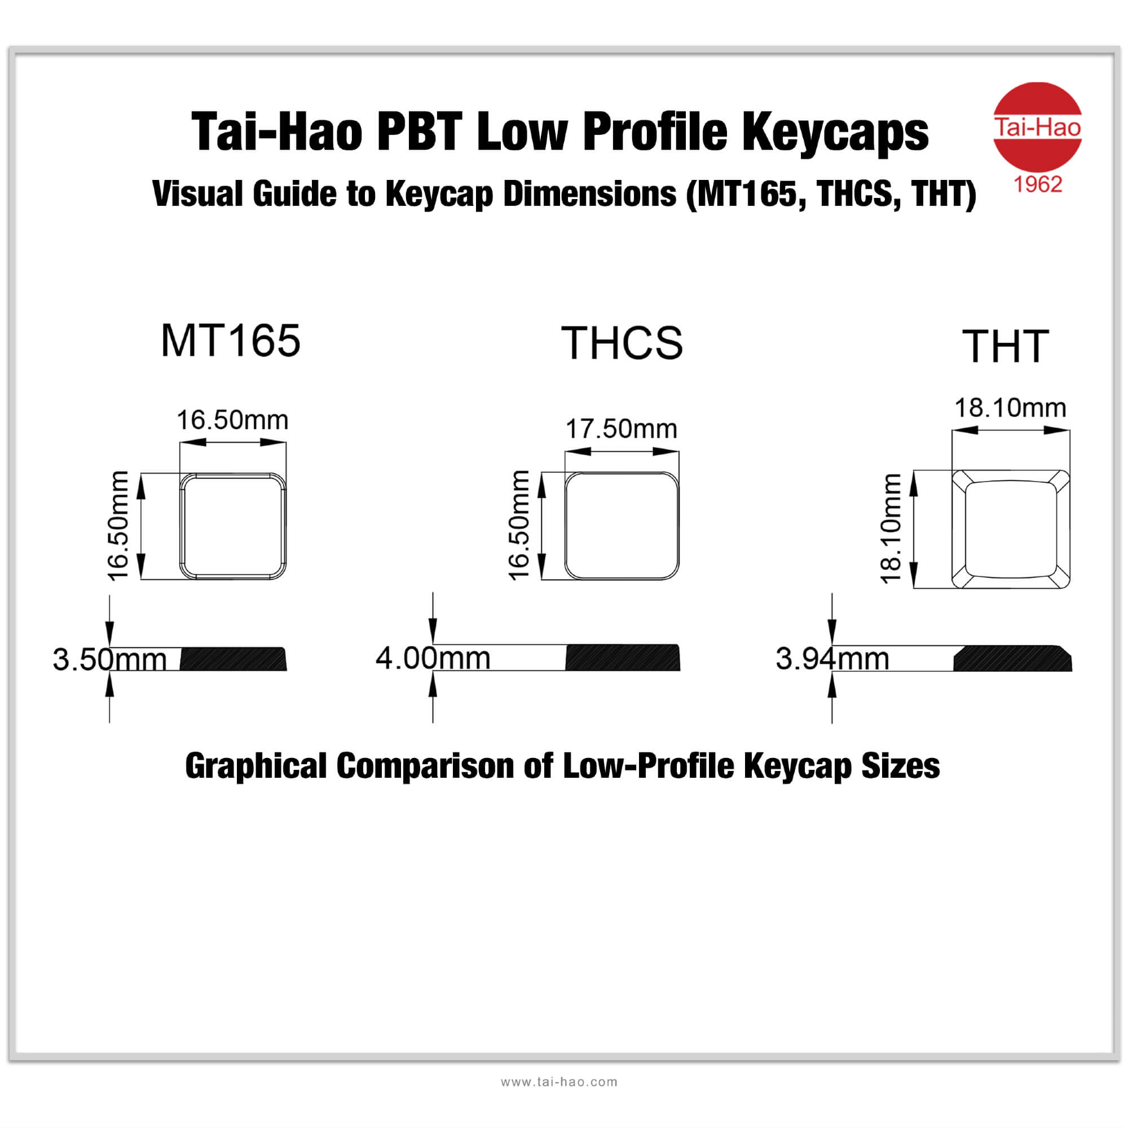
datasheets/mechanical/TAIHAO-MT165-THCS-THT-DIMENSION-GUIDE.jpg
