jeffmhopkins/Woody/docs/review/2026-09-21-pre-merge-review/VERIFIED.md

# Verified by hand — pre-merge wave

A finding is a claim. This file records what was checked against the corpus
and where an agent was right or wrong. Checked as reports land; the wave is
still running.

## A3 — mod channels

| Claim | Check | Verdict |
|---|---|---|
| **M5** — "DAC channel 7" is never mapped to the DAC8568's address field, leaving it ambiguous by one channel (DAC-G `0110` vs DAC-H `0111`) on the node that sets the intercept of four jacks | `grep -rn "DAC-G\|DAC-H\|A3..A0\|0110\|0111"` across `hardware/`, `docs/decisions/`, `firmware/`, `config/` | **Confirmed. Zero hits.** The corpus names a channel by an ordinal that the datasheet does not use, with no `MISO` to catch a wrong write |

Not yet checked: M1 (the drawing's column positions), M2 (the buffer-load
model and the missing sink case), M3 (the `CLR` grade attribution), M4, M6,
M7, M8, S1–S3.

## A8 — grounding

| Claim | Check | Verdict |
|---|---|---|
| **Incidental** — `ROADMAP.md:53` carries a live `8HP`, and none of `panel-width`'s five forbidden patterns matches the spelling `at 8HP rather than` | Read the line; compared against the five patterns | **Confirmed.** The line reads "good practice **at 8HP** rather than the structural necessity it was at 6HP", describing a panel width that was superseded by 10HP. The five patterns are `panel is 40.34 mm`, `The panel is 8HP`, `inside 8HP`, `at 8HP this`, `Comfortable at 8HP` — **`at 8HP rather than` matches none**, and the checker reports PASS. **The fifth recorded escape of this exact class**, and it is in the file a builder follows at E12 |
| **F4-3** — all three line citations in `dig-gnd-topology`'s `candidates` are stale | Opened each cited line | **Confirmed, all three.** `0004:627` is mid-sentence about cents of error; the claim it cites is at **:637**. `digital-and-supervision.md:53` is a row of an ASCII drawing about `OE`; the claim is at **:60**. A line number is a path with different syntax, and nothing checks these |

Not yet checked: F1 (the jack sleeve and panel as an unassigned second
ground — needs a real part), F4-1/4-2 (ADR 0004 vs `power-entry.md`, and
`ROADMAP.md` as an undeclared fourth document), F5/F2, F6, F6-1/6-3, F9,
F-AGND-2, F3-1.

### Note on F4-3's significance

The `dig-gnd-topology` entry's own `note` field says *"power-entry.md states
that ADR 0004 was corrected on this point. IT WAS NOT — line 627 still says
the opposite."* That note is right about the substance and wrong about the
line, which is the failure mode one level up: **the record of the defect has
itself gone stale.**

## A1 — breath chain

| Claim | Check | Verdict |
|---|---|---|
| `U-DIFFRX`'s BOM row carries a live `-9.6V`, a **forbidden** value of `inamp-full-scale`, escaping because the list spells it with a space | Read the row; compared to the four patterns | **Confirmed, and worse than reported.** The row says *"Output is 0V at rest to **-9.6V** at full"*. The forbidden patterns are `-9.6 V`, `−9.6 V`, `-10.05 V`, `−10.05 V` — all four carry a space before the `V`. **The corpus spells it without one.** The register's own note says −9.6 V "is derived from nothing and matches no configuration", and it is live on the in-amp's own row while `check-staleness.py` reports PASS |

**This is the sixth recorded escape of this class, and the second found
today.** The mechanism is identical every time and is written down in two
places in this repository: a forbidden pattern is a case-sensitive literal,
and the corpus spells its numbers more ways than the person writing the list
imagines. Today the spelling was one absent space.

## B5 — firmware contract

| Claim | Check | Verdict |
|---|---|---|
| `firmware/README.md` contradicts itself about where the display runs, inside the list it calls "not negotiable" | Read both bullets | **Confirmed.** Bullet 2: "Display renders on the other core, on its own SPI host." Bullet 5, three lines later: "WiFi and the display are on the other MCU." Both are in the same non-negotiable list |

Not yet checked: the twelve absent obligations, the SPI-host exhaustion
claim, the IMU I2C arithmetic, and the four further staleness escapes B5
reports.

## Cross-cutting, from four reports that could not see each other

Three agents independently report the same structural cause: **BOM rows were
assigned by matching reference-designator strings, so parts the drawings
label differently fell into `unplaced.csv`** — `U-DIFFRX`, `R-GAIN-INAMP`,
`C-FILT-BREATH` and others are *drawn* and filed as undrawn. A1 adds the
consequence that matters: **every staleness escape it found is in a file the
chain's own pages do not reach.** The misfiling did not create the stale
values, but it put them where no reader of the breath chain would look.

That assignment rule is mine, from this session.

## B4 — ADRs vs drawn reality

| Claim | Check | Verdict |
|---|---|---|
| **B4-01** — ADR 0004 withdraws the frame watchdog at `:484` and then reasons from it as live at `:523` | Read both lines; tested whether `:516-524` sit inside the withdrawal blockquote | **Confirmed, and the structure is the point.** `:484` opens `> **Withdrawn 2026-09-21.**`. Lines 516–524 are **plain prose, not quoted** — outside the withdrawal — and `:523` reads "the MCU dies, SPI stops, `CLR` fires, and breath keeps working." With no watchdog, `CLR` does not fire. **This is the exact class `CLAUDE.md` §5 names as the one no grep can find**, and it is the same watchdog, in a different document, still live |
| **B4-14** — `key-pullup-qty`'s forbidden pattern `"Twenty-one sets"` matches a **true** sentence, and is masked only by an accident of line wrapping | Read the pattern and `0001:217` | **Confirmed.** The line reads "…rather than 265 mm of loom. Twenty-one sets across the". The statement is correct — 21 networks and 24 pull-ups are different quantities — and the only reason the hook is silent is that `rather than` happens to share the line and counts as refutation wording. **Reflow that paragraph and the checker starts failing on a correct statement**, whose cheapest "fix" is to make it wrong |

## A2 — pitch chain

| Claim | Check | Verdict |
|---|---|---|
| **P2** — there is no decoupling capacitor on `VREFOUT` anywhere in the BOM, on the node where 1 mV is 1.2 cents | `grep -i vrefout hardware/bom.csv` | **Confirmed on the corpus side.** The only rows naming `VREFOUT` are the op-amp, the offset trimmer and a series resistor. No capacitor. **The datasheet half I could not verify myself** — `pypdf` fails in this container with a `_cffi_backend` error, so I could not re-read the cited pages. A2's datasheet citations for P1 and P2 stand as its claims, not as my verification |

Not yet checked: P1 (the 3-stated `VREFOUT` at power-on, which refutes three
separate statements about what the pitch jack does), P3 (the LT5400 outside
the clamp), P4, P6–P14.

### A note on the tooling, for whoever picks this up

`pypdf` is broken in this container. `docs/reference/repo-maintenance.md` §3
records `python3 -c "import pypdf"` as the working extraction route "used for
every extraction in this session" — **that is no longer true here**, and any
agent told to verify a datasheet claim will hit it. `pdftotext` was already
recorded as not installed in every session. Whoever re-verifies B3's slice
needs a working reader first.

## B1 / A4 — the seventh spelling of the refuted sensor transfer function

Two agents that could not see each other filed this independently.

| Claim | Check | Verdict |
|---|---|---|
| `docs/decisions/0005-power-architecture.md:74` carries the **refuted** `0.2–4.7 V` sensor output as live fact, in a spelling no `forbidden` pattern matches | Extracted the literal from the line; compared byte for byte against all 27 patterns on `sensor-full-scale` | **Confirmed.** The line holds `0.2–4.7 V` — U+2013, **no spaces**. The register has `0.2-4.7 V` (ASCII hyphen), `0.2 – 4.7 V` (en dash *with* spaces) and `0.2–4.80 V` (tight en dash, but the 4.80 value). The tight-en-dash `4.7` form is the one nobody wrote. Zero hits; checker PASS |

`CLAUDE.md` names `sensor-full-scale` as the worst recorded case of this
class and says the corpus spelled one number **seven** ways. This is the
eighth, in the same figure, found after three review waves and a restructure.

## A10 / B1 — two more single-character escapes

| Claim | Check | Verdict |
|---|---|---|
| `ROADMAP.md:203` says **"Six conductors per hop"**; `chain-conductors` is **12** | Read the line; compared against all five patterns | **Confirmed.** The list holds `six conductors per hop`, `SIX conductors per hop`, `6 conductors per hop` — and, in Title case, `Six conductors leave`. So Title case *was* considered, for the other spelling. The miss is one letter. The row is the one that asks "does the chained key loom fit the side channel?" and gates it "before the plate DXF is cut" |
| `hardware/bom.csv:62` and `hardware/module/panel-led/bom.csv:2` carry the **retired** four-row panel budget | Read both rows; compared against `panel-height-budget`'s nine patterns | **Confirmed, four values, four misses, each by one removed space.** The rows spell `~115mm against ~110mm usable`, `107mm of ~110mm`, `= 97mm, 13mm spare`; every pattern spells `NN mm`. And this is the generated master plus its fragment, so the same stale text is in the repository twice |

## A7 / A4 — the DAC threshold is read off the wrong datasheet row

| Claim | Check | Verdict |
|---|---|---|
| `0004:209` justifies the level shifter with "the DAC's **0.7 × AVDD** input threshold — **3.65 V** at AVDD = 5.21 V"; SBAS430E splits that parameter and the module is in the other half | Re-read the banked `datasheets/analog/DAC8568CIPW.pdf` p.4 directly | **Confirmed.** p.4 gives `VINH` as **two rows**: `2.7V≤AVDD<4.5V → 0.7×AVDD` and `4.5V≤AVDD≤5.5V → 0.625×AVDD`. The LM317 rail is 5.21 V, so the binding figure is **0.625 × 5.21 = 3.26 V**, not 3.65 V. p.53's own revision history records TI splitting it into two rows. **The conclusion survives** — 3.3 V CMOS still cannot drive it — but the number that carries the argument is wrong by 0.39 V, on the ADR that owns the link |

## B2 — the DAC order code does not exist

| Claim | Check | Verdict |
|---|---|---|
| `U-DAC`'s part number `DAC8568CIPW` is not an orderable device | Searched the banked datasheet's own Package Option Addendum | **Confirmed. Zero occurrences of `DAC8568CIPW` in the whole document.** p.54–57 enumerate `DAC8568IAPW / IBPW / **ICPW** / IDPW` and their `R` reel variants. The `I` and the grade letter are transposed; the C grade orders as **`DAC8568ICPW`**, which appears nowhere in this corpus |

This one propagated further than a value normally does: it is in
`hardware/bom.csv`, in `0006:176` and `:179`, in `datasheets/MANIFEST.csv`,
and **in the banked file's own name** — so the datasheet is filed under a part
number that does not exist. The manifest row beside it says the grade table
was "verified verbatim", which it was. Nobody checked the line above it.

## A9 — the strips' per-LED current, and a refutation that stopped 284 lines short

| Claim | Check | Verdict |
|---|---|---|
| The strip power figures rest on a per-LED current that no banked document supports | Read `datasheets/led/WS2815.pdf` p.3 directly; recomputed from `0014:132` | **Confirmed.** `0014:132` gives `60/m (50 LEDs) | 1.01 A` — **20.2 mA/LED** `[calc]`. The banked WS2815 datasheet p.3 states **`RGB Channel Constant Current 15 mA`**, i.e. **45 mA/LED** at full white — **2.23× higher**. The same page's `Quiescent Current 2.1 mA` reproduces ADR 0005's 123 mA exactly, so the two numbers in the corpus have different sources and only one of them is the datasheet |
| The corpus already knows this class of error | Read `0014:416` | **Confirmed, and this is the finding.** At `:416` the corpus says of the *matrix* figure: "**this is the wrong part's figure and it is at least 2.4× too low**". That refutation is 284 lines below the strip table at `:153`, which still reads `Both strips full white at 60/m | 12.1 W | ~36 K` with no flag. At 45 mA/LED the same row is **≈27 W and ≈81 K** `[calc]` |

`~36 K` is the number the ~3 W lighting clamp was sized to avoid, so the
strip row is not decorative — it is the load case the clamp exists for.
**The fix landed where the editing was happening and not where the reader
looks**, in the ADR that owns lighting.

## A6 — the path map is itself stale, in 22 of 287 rows

| Claim | Check | Verdict |
|---|---|---|
| `docs/reference/path-map-2026-09-21.csv` calls the `74HC165` datasheets "unmoved" when they moved | Resolved every `datasheets/…` path cited anywhere in the design corpus | **Confirmed, and it is broader than the three rows filed.** Of 88 distinct `datasheets/` paths cited in the corpus, **22 resolve to nothing — and all 22 are in the path map**, every one with `kind=unmoved` and `old == new`. The files were re-filed by function (`datasheets/logic/`, `/led/`, `/analog/`) and the map was not updated. Two rows are wrong about the filename as well, not just the directory: the map names `74HC165-toshiba.pdf` and `74HC165.pdf`; the bank holds `74HC165-toshiba-1986-excerpt.pdf` and `74HC165-ti-scls116e.pdf` |

This is mine, and it is a new shape. `CLAUDE.md` §6 says paths in the
historical records "are not to be corrected — resolve them through
`repo-maintenance.md` §7", and §7 points at this map. **The documented
mechanism for resolving stale paths is itself stale**, and silently: an
`unmoved` row has `old == new`, so `rewrite-paths.py --verify` has nothing to
look for, and `check_links` only reads markdown links, not CSV cells. Every
check passes.

It is also the same failure as the ones above, one level up: not a value that
went stale, but **the table that exists to resolve stale values**.

## A2 — a correction to this file

The note at the end of the A2 section says `pypdf` is broken in this
container. **That is wrong, and it mattered** — it would have told the next
reader that B3's whole slice was unverifiable.

`pypdf` works. What fails is the system `cryptography` package's Rust
binding, which `pypdf` imports eagerly and only needs for *encrypted* PDFs.
Stubbing the module out before the import makes extraction work on every
banked document:

```python
import sys, types
for m in ('cryptography', 'cryptography.hazmat', 'cryptography.exceptions',
          'cryptography.hazmat.primitives',
          'cryptography.hazmat.primitives.ciphers',
          'cryptography.hazmat.primitives.padding',
          'cryptography.hazmat.backends'):
    sys.modules[m] = types.ModuleType(m)
import pypdf
```

Four of the verifications above were done this way. `repo-maintenance.md` §3
needs this rider, and that edit is **held pending the merge decision** rather
than taken now, because the corpus is under a content freeze and making an
exception for my own convenience is how freezes stop meaning anything.

## A5 / A4 / C3 — the umbilical branch: three cold agents, one topology contradiction

The strongest convergence in this wave. Three agents on three different
slices, none able to see the others, filed the same defect from three sides.

| Claim | Check | Verdict |
|---|---|---|
| Both Interfaces tables say the umbilical branch is taken **before** the entry diodes; the drawing, the part counts and a **settled** tracked figure all require it **after** `D2` | Read both rows, the `D-REVPOL` and `FB-IN` BOM rows, and `ferrite-bias-impedance`'s derivation | **Confirmed, and one side of it is settled.** `power-entry.md:28` and `umbilical-load-switch.md:15` both say "taken **before** the diodes, which is the point of the split". Against that: `D-REVPOL` is **qty 3**; `FB-IN` is qty 4 and its note enumerates "One per branch: +12V analog, **+12V umbilical**, −12V, +5V"; and `ferrite-bias-impedance` — **status settled** — derives FB2's 280–310 Ω from "**FB2 carries `umbilical-current` (359 mA)**", distinct from the module's own 392 mA. If the tables are right, FB2 carries nothing and a settled figure is wrong |

Why it is the wave's most consequential finding rather than one more stale
sentence:

- **The two halves agree with each other**, because the same sentence was
  copied into both pages during the split. Cross-checking the two ends —
  the thing the `## Interfaces` tables exist for — returns agreement.
- **It is a layout instruction.** Followed at layout it deletes reverse
  protection on the 359 mA branch and leaves `D2`/`FB2` as dead copper.
- A5 computed the consequence the other way: with `D2` + `FB2` in the path,
  the load switch's `FB`-divider worst-case margin falls from the **0.4 V**
  it was chosen to have to **0.05–0.11 V**.
- **Both parts are in `unplaced.csv` as well** — `D-REVPOL` and `FB-IN` are
  in the file that counts "parts nobody has drawn", while being the parts the
  power-entry drawing is mostly made of.

Nothing here says which topology is correct. It needs a decision, not an edit.

## C4 — two netlist shorts in the tables written to prevent netlist shorts

| Claim | Check | Verdict |
|---|---|---|
| **F5** — `module/dac8568`'s `SCLK`/`DIN`/`SYNC` has two declared drivers | Compared the two rows | **Confirmed, and they are byte-identical.** `spi-link.md:42` and `digital-and-supervision.md:27` both read "`SCLK`, `DIN`, `SYNC` … out … `module/dac8568` … Buffer outputs. The DAC-side three of the six `R-SPI-PULL` sit on these". The buffer is physically on `digital-and-supervision` — **`spi-link.md:43` says so itself**, one row later, when explaining why the +5 V open item stayed over there. So `spi-link` claims to source three nets that do not cross its own boundary |
| **N2** — `bus +5V` has two mutually exclusive sources | Read all three tables and the drawing | **Confirmed.** `power-entry.md:27` exports "bus `+5V` **after `FB4`/`C4`**" to `module/digital-and-supervision`, and its drawing at `:74` shows `+5V ├──[FB4]──[C4 47µF]──── 74AHCT125 only`. Both receiving tables — `digital-and-supervision.md:28` and `spi-link.md:43` — say the rail comes straight from the "Eurorack bus header", naming no bead, no capacitor and no peer circuit. A transcription gets **two nets both called bus +5 V**, one filtered and one not, and no DRC can say which is real. The BOM sides with `power-entry`: `FB-IN` is qty 4 and one of the four is the +5 V branch |

The second one is not only a naming problem. Whether that rail has 47 µF on
it is what decides how long the buffer stays powered after `AVDD` collapses —
the sequencing hazard A4 and C3 filed independently.

## B1 / B2 — four tracked figures are owned by the generated file

| Claim | Check | Verdict |
|---|---|---|
| Four `figures.yaml` entries name `hardware/bom.csv` as `owner` | Enumerated every entry's `owner` | **Confirmed: `key-pullup-qty`, `panel-toggle-hole`, `ferrite-bias-impedance`, `ref5050-grade`** |

Rule 1 says the owner **states** the figure and everyone else cites it. These
four point a maintainer at the one file in the repository where a statement
is deleted without a word on the next `merge-bom.py`. It is the trap
`CLAUDE.md` §4 names, aimed by the register itself — and it is **mine**,
created the moment the restructure made that file generated and not
propagated into `config/figures.yaml`.

`check_owners` passes on all four, because `merge-bom.py` copies the
fragments' notes through, so the value really is present in the generated
output. The check proves the text is there. It cannot ask whether the file
it is in is one a human should edit.

## C1 — the audit of this round's own fixes, and the two findings against me

Every wave this project has run has found the previous round's fixes partial.
This one found mine partial in the worst available way: **a fix asserted in a
commit message, in a docstring, and in `STATUS.md`, that does not land.**

### C1-1 — `check_owners`'s tightening is a no-op for the case its own docstring names

| Claim | Check | Verdict |
|---|---|---|
| `check_owners` builds its tokens from **digits only**, so "the most distinctive token" for `spi-series-r` is still `100` — the very token the docstring calls the counter-example | Read `tools/check-staleness.py:522-523`; then **reproduced it** in a `git archive HEAD` copy | **Confirmed by reproduction.** `re.findall(r"\d+\.?\d*", value)` discards `R-SPI-SER` before the sort, leaving `100` as the only token ≥3 characters, so "the longest" is trivially it. I repointed `spi-series-r`'s `owner` to `docs/decisions/0009-enclosure-construction.md` — an ADR that derives no SPI resistor — and the checker reported **`PASS`, exit 0**, because that file contains the string `100` at `:521`, inside "10 kΩ, 100 Ω and 10 nF per switch position", a key-switch network on a different board |

The docstring's closing line is *"A check whose own docstring names a case it
does not catch is worse than no check."* It then does not catch it.

It is not one figure. Enumerating the single token the check actually tests
for each of the 23 checkable entries:

| Figure | Token actually tested | What that token also spells |
|---|---|---|
| `spi-series-r` | `100` | Cat5 line impedance, "not 100 %", a key-network resistor |
| `loadswitch-gate-cap` | `197` | **`OPA2197`** — B1 found this independently |
| `cref-out-node` | `5050` | **`REF5050`** — the part number inside its own value string |
| `pitch-compensation` | `2.2` | 2.2 kΩ, 2.2 mF, the 2.2 k pull-up |
| `diode-split-rationale` | `392` | the pre-split total current A4 says flows through neither diode |

So a quarter of the settled register passes `check_owners` on a part number
or on an unrelated component value. **Three owner repointings this session
were made on this check's evidence**, and `STATUS.md` credits the tightening
with finding `loop-budget`'s real defect — which it did, but by luck of that
figure's token, not by the mechanism claimed.

### C1-3 — the path map does not cover the tree, and says it does

| Claim | Check | Verdict |
|---|---|---|
| `repo-maintenance.md` §7 says "**every tracked file has a row**, including the ones that did not move" | Compared `git ls-files` against the map's `old` column | **Confirmed false.** 397 tracked files, 287 rows, **143 files with no row** — 121 of them excluding this wave's own reports. The breakdown is the diagnosis: **95 are under `hardware/`** and 22 under `datasheets/` |

The map was written during Phase A and never updated through Phase B, which
*created* those 95 files. Together with the 22 dangling `unmoved` datasheet
rows recorded above, the whole of §7 is now wrong in both directions: it
omits the files the restructure made, and it asserts paths the restructure
deleted.

**This is the same defect as the one in the corpus, in the document written
to resolve it.** `CLAUDE.md` §6 tells a reader that historical paths "are not
to be corrected — resolve them through `repo-maintenance.md` §7", so the rule
that protects the historical record points at a table that cannot honour it.

### The other C1 findings, not yet checked by hand

C1-2 (the `sim/README.md` fix that half-landed), C1-4 (`key-scan-current`
says three restatements, there are five in four files), C1-5/6/7 (three stale
counts, including `pcb-pipeline.md:58`'s "the six pages" against 23 circuit
pages — debt that `STATUS.md` predicted and nobody closed), C1-8/9.

C1 also re-ran the largest conservation proof at HEAD rather than at the
split commit — `carrier.md`, 8709 words into 16 files — and found four gaps,
all four legitimate. **No later commit dropped text**, which is the one claim
the merge most depends on and the one I could not have checked myself
without re-running it cold.

## A5 — the level shifter's own supply is out of spec at the guaranteed corner

Three banked documents, none of whose numbers appear anywhere in the corpus.

| Claim | Check | Verdict |
|---|---|---|
| The 5 V node feeding the carrier's 74AHCT125 falls below the part's minimum VCC at the worst case | Read all three banked datasheets directly | **Confirmed at the guaranteed corner.** `datasheets/discrete-and-power/R-78E5.0-1.0.pdf` p.2: "Output Accuracy **±3.0 % typ. / ±5.0 % max.**" `datasheets/discrete-and-power/SS14.pdf` p.2: maximum instantaneous forward voltage at I_F = 1.0 A, **V_F = 0.50 V**. `datasheets/logic/SN74AHCT125.pdf` p.3, recommended operating conditions: **V_CC 4.5 V to 5.5 V**. The drawing at `power-entry-instrument.md:42-43` puts the buffer behind `R-78E5.0 A` and `D-USBOR`, so `5.00 × 0.95 − 0.50 = **4.25 V**` `[calc]` — **0.25 V under the minimum** |

Two honest qualifications, because a confident wrong finding is worse than an
uncertain right one:

- The SS14's 0.50 V is specified **at 1.0 A**. The real load is a fraction of
  that, so the true drop is smaller — but the datasheet publishes no maximum
  at a lower current, so 0.50 V is the only *guaranteed* number available.
- At typical the node sits near 4.8 V and everything works. The finding is
  that **nothing in the corpus states the worst case at all**, and this is
  the part whose TTL thresholds are ADR 0014's entire level-shift argument —
  thresholds that are only specified inside 4.5–5.5 V.

`led-strip-drive.md` derives its noise margin "at 5 V". The power page puts
the same node at ~4.7 V. Neither number is the guaranteed one.

## B2 — the TVS package correction landed on two of its four locations

| Claim | Check | Verdict |
|---|---|---|
| The SP0504BAHT pin-count correction named four locations; two were fixed | Grepped all four | **Confirmed.** `U-TVS-SPI` reads **SOT-23-5** in its fragment, in the generated master and at `carrier.md:292`. `U-TVS-CHAIN` still reads **SOT-23-6** in its fragment (`key-chain-loom/bom.csv:4`), in the master at `:49`, and at `carrier.md:285` |

B2's own caveat is correct and worth keeping: `U-TVS-CHAIN`'s `part` field is
generic ("4-channel TVS array"), so SOT-23-6 is not wrong in the abstract —
some four-channel arrays are six-pin. What makes it a defect is that
`carrier.md:285` justifies the part **by pointing at `U-TVS-SPI`**, which is
the five-pin one. The row is right by accident and wrong by its own reasoning.

**This is the thesis of every wave this project has run, on a two-row fix.**

## C6 / A5 — the umbilical's conductor gauge is nowhere, and three derivations assume it

| Claim | Check | Verdict |
|---|---|---|
| `CABLE-UMB` specifies no gauge while three derivations compute from 24 AWG | Read the BOM row and grepped for the assumption | **Confirmed.** The row buys a `"Cat5e STP patch lead, **STRANDED**, ~2m"` — no AWG anywhere in it. Three documents derive from 24 AWG: `breath-sense-link.md:100` (0.168 Ω of return resistance), `0003:315` (the whole signal-drop table), `0005:91` ("Over 2 m of 24 AWG, round trip ~0.34 Ω") |

What makes this more than an omission: the row's own note explains at length
*why* it is stranded — "solid core work-hardens and fractures under constant
flexing, which is this cable's whole life". Stranded patch leads are commonly
26 or 28 AWG, i.e. **1.6× to 2.6× the assumed resistance**. So the deliberate,
well-argued choice is exactly the one that invalidates the gauge three other
pages depend on, and nobody connected the two. A5 reached the same place from
the power side and put 26 AWG at **+59 % drop**.

## C6 / A10 — a settled figure, contradicted twice, by documents that cite each other

| Claim | Check | Verdict |
|---|---|---|
| `plate-thickness` is **settled at 1.20 mm** while `config/key-layout.yaml` calls it unset and `cluster-boards.md` calls it open | Read all three | **Confirmed.** `config/key-layout.yaml:33` reads `plate_thickness: null`. `hardware/cluster/cluster-boards.md:167` reads "**Plate thickness is still open and blocks M4/M5**" — and cites `[repo] key-layout.yaml, 0002, bom.csv` as its authority |

The citation chain is **intact**. The page cites the config file, the config
file says `null`, and the two agree with each other perfectly. They just both
contradict the register entry that says the question is settled. A reader who
checks the source gets the wrong answer confirmed.

**And no possible `forbidden` pattern catches it.** The register protects
against a superseded *value*; `null` and "still open" are the absence of one.
That is C6's generalised point and it is correct: **the register can protect a
wrong number and cannot protect a missing one.** It is also the cheapest
missing check in the repository after the one `STATUS.md` already names — both
are of the form "assert that what is written now resolves", which is the
principle the restructure's own three new checks were built on.

## C2 — the sixth fail-open, reproduced

C2's brief was to find a sixth instance of the class without being allowed to
see the first five. It found one, and it is in the check the whole
restructure's conservation proof rests on.

### The head of a moved passage can be deleted for free

| Claim | Check | Verdict |
|---|---|---|
| `check-conservation.py` detects text lost off the **tail** and is blind to text lost off the **head** | Ran the tool three times against `pitch-stage.md`, dropping nothing / the first 6 words / the last 6 words | **Confirmed, reproduced exactly.** Intact: `REAL GAPS: 0, rc=0`. **First six words deleted** — which are `# Pitch stage — schematic **Status:**`, the page's entire H1 and its status label — `seams: 1, REAL GAPS: 0, **rc=0**`. **Last six words deleted**: `TAIL: … rc=1` |

The asymmetry is structural. A shingle walk starting at `i=0` has exactly one
shingle containing word 0, so losing the first *k* words breaks *k* shingles,
and `seams = [l for l in lost if l[1] < N]` files any *k* ≤ 7 as a seam. The
code at `:59-61` compares the final N words explicitly **because** the same
argument was noticed at the end — and the comment above it reasons "at the
very end only k shingles exist to break … Verified", without the symmetric
sentence ever being written.

**Why this one matters more than the other twelve.** Deleting words off the
front of a passage is not a hypothetical edit here — it is *what a Phase B
split does*. An agent moves a section to a new page and rewrites its heading.
So the single check built to prove the seven splits conserved content is blind
to the most likely way a split loses it. Every "0 REAL GAPS" in `STATUS.md`
is a weaker claim than I stated it as.

C2 found two more in the same file: a passage the source states **twice** can
be halved for free, because `have` is a set; and reordering is invisible by
construction.

### And the fourth-generation instance, again

| Claim | Check | Verdict |
|---|---|---|
| `check_bom_generated()` returns on the `merge-manifests` result before it ever looks at `merge-bom`'s | Read `tools/check-staleness.py:199-215` | **Confirmed.** `r` (merge-bom) is computed at `:200`; `:209` returns on `m`'s non-zero exit and `r` is never examined. A manifest problem **masks a hand-edited `hardware/bom.csv` completely.** The filter at `:210-211` keeps only lines containing `PROBLEM:` or `does not match`, which discards every `REFUSING TO WRITE:` message `merge-manifests.py` has — replacing a precise, purpose-written refusal with "it probably crashed", a diagnosis that is simply false |

The comment at `:216-226` is the stdout-plus-stderr fix for exactly this
failure. It was applied to the `r` branch and not to the `m` branch **six
lines above it**, in the same function, in the same commit. Its own text
reads: *"That is the FOURTH instance of the fail-open class in this
repository, and it was inside the check written to close the third."*

This is the fifth, inside the fourth.

### The rest of C2's list, not individually reproduced by me

Thirteen further fail-opens, every one of which C2 reproduced in a throwaway
tree: the REFUTATION exemption silenced by the bare word `was` (**23 of 59
current suppressions ride on it**); `check_owners`' token being an unanchored
digit substring (`14.863 mm` satisfies `4.86`); `check_checks` asserting a
substring of `main()`'s source, so `if False and link_problems:` passes;
`check_sections` keyed on basename across 15 `notes.md`; `check_links` seeing
inline `](*.md)` only, so broken links to `bom.csv`, `figures.yaml` and a
`.dxf` all pass; `check_verified_against` accepting a SHA from a different
part's row; a duplicate `id` evicting a whole circuit; **emptying every
`forbidden` list producing a PASS line byte-identical to a healthy run**; and
`merge-bom.py` silently skipping a fragment named in `ORDER` but absent, then
regenerating a smaller master with everything green.

C2 also recorded what it could **not** fool, which is the more useful half:
`merge-bom.py`'s five other guards, all of `merge-manifests.py`'s own guards,
everything `verify-datasheets.py` checks, and `rewrite-paths.py --invert` —
the strong proof that Phase A changed no content. That one held.

## C5 — the newcomer slice, and the finding that decides the merge

### F2 — the documented procedure produces the project's named failure, green

C5 stood in for someone who has never seen this repository. It followed the
written rules. I re-ran it myself in a throwaway copy.

| Claim | Check | Verdict |
|---|---|---|
| Changing a resistor by the documented procedure leaves the corpus inconsistent and every tool reports success | Edited the fragment, regenerated the master, ran the checker — the three documented steps, in order | **Confirmed, reproduced exactly.** Changed `R-SPI-SER` from `100R 1%` to `220R 1%` in `hardware/interfaces/spi-link/bom.csv`. `merge-bom.py`: *"wrote 138 rows from 24 fragments \| **0 problems**"*. `check-staleness.py`: *"**PASS no live stale values**"*, **exit 0**. Meanwhile `config/figures.yaml` still reads `value: "100 ohm, R-SPI-SER, qty 3"` and the owner page still states 100 Ω **six times** |

And 220 Ω is not an arbitrary number. It is **the value that figure's
derivation exists to reject** — `spi-series-r`'s own `forbidden` list contains
`R-MOSI-SER at 220`.

**Why it escapes.** Nothing in the toolchain relates a BOM row to the figure
that governs it. `check_owners` compares the register against the owner page,
and after this edit those two still agree perfectly — both still say 100. The
BOM is the third party to that agreement and no check reads it as one.

This is the whole project's stated purpose, failing along the path a new
contributor is explicitly told to walk, with `0 problems` and `PASS` printed
at them. It is worse than any individual stale value found in this wave,
because a stale value is one defect and this is a *generator* of them.

C5 adds the compounding detail, which I verified separately above: three
tracked figures name the **generated** `hardware/bom.csv` as `owner:`, so for
those the procedure's first step sends the reader to edit a file that
silently discards the edit.

### F1 — the restructure's central map is unreachable

| Claim | Check | Verdict |
|---|---|---|
| `hardware/README.md` has zero inbound links from anywhere in the corpus | Grepped every markdown link in the tree outside `docs/review/**` | **Confirmed. Zero.** The root `README.md`'s only outbound links are to `docs/decisions/0011-licensing.md`, `docs/decisions/` and `docs/reference/latency-budget.md`. Its "Repository layout" section is a fenced code block, so nothing in it is a link |

The page that explains the `<board>/<circuit>/` scheme — the thing this
restructure *is* — cannot be reached by following links from the front door.
The tree is navigable by `grep` and by knowing where to look, which is the
condition the restructure was meant to end. **This one is squarely mine.**

### F15 — a forbidden pattern that can never fire

| Claim | Check | Verdict |
|---|---|---|
| `spi-series-r`'s pattern `"220 Ω with\n~200 pF"` contains a real newline and cannot match the line-joined stream | Read the entry | **Confirmed.** The list is `['R-MOSI-SER at 220', 'R-MOSI-SER` at 220', 'R-SCLK-SER', 'R-CS-SER', '220 Ω with\n~200 pF']` |

It is exactly what `CLAUDE.md` §2's "add one pattern per spelling you find"
produces when the spelling you find is hard-wrapped across two lines, and no
document warns about it. A pattern that cannot fire is indistinguishable in
every report from one that fires and finds nothing.

## B3 — the last slice, and a two-agent convergence

### B3-01 / A1 — `-9.6V`, escaping by one character, in two files

A1 (breath chain) and B3 (datasheets) found this independently, from
opposite directions.

| Claim | Check | Verdict |
|---|---|---|
| `U-DIFFRX`'s row carries the superseded `-9.6 V` in a spelling no pattern matches | Extracted the literal from both files | **Confirmed.** Both `hardware/bom.csv:103` and `hardware/unplaced.csv:15` read *"Output is 0V at rest to **`-9.6V`** at full (Vout = `-2.185*`(V_BRE…"* — **no space**. `inamp-full-scale`'s four patterns are `-9.6 V`, `−9.6 V`, `-10.05 V`, `−10.05 V`, **every one of them with a space** |

The row is wrong twice over: the same sentence computes from the **raw** gain
`2.185`, which gives −10.05 V — also a forbidden value, also spelled without
a space, also invisible. So the row contradicts the register *and itself*,
and the checker reports `PASS`.

And it is in **two files at once**, because `unplaced.csv` is a `merge-bom.py`
fragment and `bom.csv` is generated from it. One defect, two copies, one edit
site — which is the arrangement working correctly, on a defect nothing can see.

### B3-02 — the owner document refutes itself four lines later

| Claim | Check | Verdict |
|---|---|---|
| `0003-breath-sensing-path.md` — the **owner** of `sensor-full-scale` — states the figure correctly and then contradicts it on the same screen | Read `:561` and `:565` | **Confirmed.** `:561` reads "full scale, **0.265–4.86 V**, for the CV output". `:565` reads "The sensor **reaches 4.7 V** while the ADC runs on 3.3 V". Four lines apart |

None of the 27 patterns matches `reaches 4.7 V`. The list holds `4.7 V
output`, `full scale = 4.7 V`, `4.7 V × 0.6` — three spellings of the same
fact, and not this one.

B3 also notes the number matches **nothing in the banked document**: the
sensor's own cover page reads "0.2 to 4.8 V". So 4.7 V is neither the current
corpus value nor the datasheet's.

With the tight-en-dash instance in ADR 0005 verified earlier, that is **the
owner document and the power ADR both carrying the same retired figure, in
two different unmatched spellings, at the same time.**

### B3's clean results, recorded so they are not re-derived

The half of B3's slice that came back sound is worth as much as the findings:
**every vector-CAD dimension confirmed** — Gateron 1.20 mm on both citations
including the hatched plate section, the cutout genuinely `14.00 +0.05/−0.02`,
the NKK toggle exact on all five dimensions, the Laird bias digitisation
reproducing to within 3 Ω on all five traces, and both Eurorack panel
artefacts confirming `panel-height-budget` exactly. **No absolute maximum is
violated** under any stated condition including power-up. And **no place in
the corpus cites a surrogate datasheet as the fitted part's spec** — the
surrogate discipline holds everywhere.

B3 also supplies the extraction route this file got wrong earlier: `pip
install pymupdf` does both text and rendering, and for a number that lives
only in a curve it extracted the **content-stream geometry** and calibrated
against the gridlines — noting that its own first eyeball pass on the Laird
curves was wrong by up to 60 % and the vector extraction corrected it.
