jeffmhopkins/Woody/docs/review/2026-09-22-goal-verification/G12-corpus-edges.md

# G12 — Corpus edges: `firmware/`, `ROADMAP.md`, `README.md`, `docs/reference/`, `config/`, commit log, harness

**Slice:** G12, cold. **Measured against:** `a4b80b1` (the wave's named freeze).
**Method:** every file in `firmware/`, `config/`, `docs/reference/`, plus
`README.md` and `ROADMAP.md`, read in full; every structural and numeric claim
in them executed against the tree; a milestone-reference census over the whole
corpus; `git log` sampled for checkable claims; `.claude/settings.json` tested
behaviourally.

**Cold compliance:** I opened nothing under `docs/review/`, `docs/log/` or
`docs/research/`. Two tests needed history as *data* and were done by script
that printed only path tokens and counts, never prose: the path-map resolution
test (G12-10) and the review-wave directory count (G12-12). I did not read any
report.

**PINNING — read this before trusting any figure below.** The working tree was
being mutated by another slice during this wave (G12-26, and the coordinator's
mid-wave correction confirms it: corpus files *and* `tools/check-staleness.py`
were edited in place and later reverted, all uncommitted, so `git log` shows
none of it). **Every quotation, line number and `[test]` result in this report
has been re-verified against pinned content**, either a `git archive a4b80b1`
export or a fresh `git clone` checked out at `25cc740`.

`[test]` at the close of this slice: `git status --short --untracked-files=no`
in `/home/user/Woody` → **empty**; `diff` of `README.md`,
`tools/check-staleness.py` and `.claude/settings.json` against the pinned clone
→ **identical**. The tree had been fully reverted by then, so the pinned and
live readings agree. `README.md` in particular — mutated during the wave with an
appended broken link — is **byte-identical to `a4b80b1:README.md`**, so G12-12,
G12-13 and G12-14 stand on pinned content, not on what I happened to see.

**Baseline, taken from a pristine export of the frozen revision:**

```
[test] git archive a4b80b1 | tar -x -C <tmp> && cd <tmp>
       python3 tools/check-staleness.py
       -> PASS no live stale values | corpus 123 files, 23 circuits,
          37 figures / 217 patterns | 5 unresolved (tracked)
          | 211 restated-not-cited (advisory)
       python3 tools/merge-bom.py --check
       -> bom.csv: checked 140 rows from 26 fragments | 0 problems
       python3 tools/verify-datasheets.py
       -> datasheets: 78 verified, 23 recorded as blocked or not-fetched, 0 problems
```

All three tools pass at the freeze. Every finding below is invisible to all
three.

---

## Ranked findings

### Tier 1 — acting on these changes a build decision

---

**G12-1. `firmware/README.md:94` — "The body is bonded." It is not, and ADR 0009
says so in a paragraph that cites this file by name.**

`[repo] firmware/README.md:92-111` opens the recovery section with:

> The body is bonded. Everything here exists because a failed flash cannot be
> answered by opening the instrument.

and closes it with:

> A corrupted *bootloader* therefore ends the instrument — narrow, behind two
> mitigations, accepted.

`[repo] docs/decisions/0009-enclosure-construction.md:363-368` is the
refutation, and it is explicit that the sentence it is correcting is this one:

> The body opens on six fasteners, the dev boards are socketed, and a corrupted
> *bootloader* means taking the lid off and swapping or re-flashing a board on
> the bench. **This paragraph used to end "ends the instrument", which was true
> of a bonded body and is not true of this one.**

`[repo] docs/decisions/0009-enclosure-construction.md:653` settles the joint as
**"RTV as a gasket bead, not an adhesive… No — six fasteners"**, and
`ROADMAP.md:78` (M8) narrates the same change. ADR 0009's own version of this
paragraph, four lines above the refutation, links to `firmware/README.md` as
its authority for the MIDI opt-in — so the two files were open in the same
edit, the ADR's copy was corrected, and the firmware copy was not.

**Cost:** the whole recovery ladder is justified by an impossibility that no
longer holds. A reader either over-invests in recovery it no longer needs, or —
worse — checks the premise, finds the body opens, and relaxes the ladder that
`ROADMAP.md:78` (M8) still requires exercising. This is the exact shape
`CLAUDE.md` lists as the fourth recorded fix pattern: *a fix that did not reach
the pages citing it*.

---

**G12-2. The retired "bonded body" premise is live in ~25 places. One fact,
many files — and `docs/reference/pcb-pipeline.md` already records the
refutation and did not propagate it.**

`[test]` scripted census of `bond|cannot be reopened|cannot be opened|bonds
shut` over the §6 corpus, classifying each hit by whether refutation wording
sits within ±2 lines, and excluding the unrelated *electrical* sense
(`MECH-GNDBOND`, plate-to-`PWR_GND`) and adhesive-construction uses. **89 lines
matched; 25 are live arguments resting on the retired premise.**

`[repo] docs/reference/pcb-pipeline.md:192-197` is the proof that this was
known:

> **The CMRR row's stated reason was refuted and the ranking survives on a
> different one.** It read *"unretrofittable inside a bonded body"*. ADR 0009
> retired the bonded body — it comes apart on six fasteners…

That is one site, fixed correctly, with the reasoning re-derived. The other
twenty-five were not touched. In mine and the shared files:

| Site | Text | Why it matters |
|---|---|---|
| `[repo] firmware/README.md:94` | "The body is bonded" | G12-1 |
| `[repo] ROADMAP.md:207` | "sealed inside a **bonded body** at M6" | Contradicts `ROADMAP.md:78`, the same file's own M8 row |
| `[repo] ROADMAP.md:218` | "inside a body that **cannot be opened**" | Justifies the stuck-switch diagnostic |
| `[repo] config/key-layout.yaml:150-151` | "the body **bonds shut**, so it could never have become a switch anyway" | Justifies not cutting plate holes for the 3 free bits |
| `[repo] docs/decisions/0001-…:160, 191, 244, 337` | four separate arguments | 244 explicitly: "they **cannot be retrofitted** into a bonded body" |
| `[repo] docs/decisions/0003-…:248` | "most likely part to fail, in a body that cannot be reopened" | Sensor siting |
| `[repo] docs/decisions/0004-…:546` | "we find out before anything is bonded" | Gate rationale |
| `[repo] docs/decisions/0005-…:239` | "a bonded body that cannot be reopened to change the decision" | The reason `SW-PWR-INST` is deleted |
| `[repo] docs/decisions/0007-…:199` | "In a body that cannot be opened, two pins is a cheap price" | IMU pin budget |
| `[repo] docs/decisions/0013-…:294` | "Its own USB is inside a bonded body and reaches nothing" | Closes the display-flashing question |
| `[repo] docs/decisions/0014-…:53, 82-83, 497` | 82-83 is the sharpest: "In a **bonded** laminated body that cannot be opened casually, that matters more than it would in **a serviceable build**" | The WS2815 backup-data-line argument, now explicitly contrasted against the thing the body has become |

Plus, in `hardware/**` (other slices' territory, listed so it is not lost):
`carrier/carrier.md:286, 339, 384`; `cluster/cluster-boards.md:94`;
`cluster/key-marker-and-bits/key-marker-and-bits.md:68, 117, 133`;
`interfaces/breath-sense-link/breath-sense-link.md:14, 91, 181`;
`interfaces/key-chain-loom/key-chain-loom.md:146`;
`module/breath-receive-stage/breath-receive-stage.md:28`;
`module/breath-receive-stage/sim/README.md:22`.

**The distinction that decides each one** is drawn by
`[repo] docs/decisions/0009-…:493-497`: the body is "no longer *impossible*
later — but doing them means taking the lid off, disturbing the loom and
re-laying a gasket. That is a real cost". So sites arguing **cost** survive;
sites arguing **impossibility** ("cannot", "never", "ends the instrument",
"unretrofittable") are false. Most of the twenty-five are the second kind.

No forbidden pattern can ever catch this — the stale token is a word, not a
value. `CLAUDE.md` §5 is the rule that covers it.

---

**G12-3. `firmware/README.md:23-24` describes the pre-ADR-0013 architecture, and
the same file contradicts it fifteen lines later.**

`[repo] firmware/README.md:23-24`, inside a bullet list introduced at line 20 as
**"not negotiable"**:

> **Display renders on the other core, on its own SPI host.** A display refresh
> must never block the output loop.

`[repo] firmware/README.md:39-40`, same list:

> **WiFi and the display are on the other MCU.** They cannot preempt the output
> loop.

These are two different machines. "The other core" is the single-ESP32
architecture; ADR 0013 moved the display to a **separate MCU** with its own
image (`[repo] firmware/README.md:5-8` describes exactly that). "On its own SPI
host" is a statement about the real-time board's peripherals that no longer has
a referent — the display board owns its own panel bus.

The same residue is in `[repo] docs/reference/latency-budget.md:222-226`, where
rule 3 says "Separate SPI host, **separate core**" and rule 4, immediately
below, says "The WiFi stack and display are on a **different MCU entirely**
(ADR 0013)."

**Cost:** an implementer reads the "not negotiable" list and reserves an SPI
host and a core on the real-time board for a display that is not there. The
freed core is the one thing the 4 kHz loop would actually like to have.

---

**G12-4. `config/figures.yaml:471` — a disputed, load-bearing figure is assigned
to a milestone that does not do the work.**

`[repo] config/figures.yaml:465-471`:

```
  - id: breath-working-point
    quantity: Breath pressure at a hard blow
    status: disputed
    decided_by: "M1, with a player and a manometer. Sets the panel gain range
                 AND the ADC headroom."
```

`[repo] ROADMAP.md:71` — M1 in full — is **"Switch characterisation"**: plate
cutout, coupon fit, retention, contact bounce, hysteresis gap, spring weight. No
breath, no player, no manometer, no pressure.

The milestone that does this work is **E2**. `[repo] ROADMAP.md:42`: "**a human
plays it for 20 minutes** through a real mouthpiece, tube and trap"; and
`[repo] ROADMAP.md:193` books "Cold-start warm-up sweep | E2 | Run the sensor
from cold through 20 minutes of playing."

`breath-working-point` is cited by five circuits
(`[repo] hardware/interfaces/breath-sense-link/circuit.yaml:14`,
`hardware/module/breath-output-stage/circuit.yaml:14`,
`hardware/module/breath-response-shaper/circuit.yaml:12`,
`hardware/carrier/breath-adc/circuit.yaml:13`, plus the owning ADR) and it sets
the panel gain range and the ADC headroom. **A decider pointing at a milestone
that will not produce the measurement is an open question with nothing behind
it** — M1 can be signed off complete with this figure still disputed, and
nothing notices.

`[repo] docs/reference/repo-maintenance.md:251-253` states the rule this
violates: "A `disputed` entry must carry `decided_by` naming **what decides
it**". It names something, but not something that decides it.

---

**G12-5. `ROADMAP.md:71` (M1) tells a builder the bounce figure is unpublished.
The register, this same file, and two reference pages say it is published.**

`[repo] ROADMAP.md:71`:

> **bounce and the actuation/reset hysteresis gap scoped** on fast press, slow
> press, fast release, slow release and a worn switch — **neither is published**

Against it:

- `[repo] config/figures.yaml:648-651` — `ks33-contact-bounce`, **`status:
  settled`**, value `"5 ms max at 16 in/sec actuation"`.
- `[repo] ROADMAP.md:118-125`, fifty lines below the row, in the same file:
  "**Partly refuted 2026-09-21** … Gateron *does* publish a bounce figure —
  **5 ms max at 16 in/sec**". It then says correctly that the *hysteresis gap*
  is still unpublished. So "neither" should be "one of the two".
- `[repo] docs/reference/latency-budget.md:148`: "**No longer an unknown, only
  an unmeasured maximum** … this row used to frame it as unpublished."
- `[repo] docs/reference/ks33-geometry.md:206` — the owner, stating it.

This is `CLAUDE.md`'s named shape twice over: the fix landed in the prose
section and not in the table row a builder reads, and the corrected file
contains both versions. Note `[repo] firmware/README.md:26-34` handles the same
figure correctly — it cites `ks33-contact-bounce` by name and says the number is
"deliberately not restated here". The ROADMAP row is the outlier.

---

### Tier 2 — wrong information about how the repository works

---

**G12-6. `docs/reference/repo-maintenance.md:27` states the hook behaviour the
project has already corrected; line 278-280 of the same file states it
correctly.**

`[repo] docs/reference/repo-maintenance.md:27` — the opening sentence of §2,
the section about the checker:

> Run by a `PreToolUse` hook **before every `git commit`**, so forgetting it is
> visible rather than silent.

`[repo] docs/reference/repo-maintenance.md:278-280`, in §6:

> though note `CLAUDE.md` §2: it runs before *every* `Bash` call rather than
> before `git commit`, and it never blocks, it only tells you.

**Verified independently and behaviourally, not from `CLAUDE.md`:**

`[test]` every `Bash` call I made in this slice — `ls`, `cat`, `find`, `python3`,
`grep` — returned a `PreToolUse` `additionalContext` line beginning `staleness
check:`. None was a `git commit`. `[repo] .claude/settings.json` shows why: the
entry's `"matcher"` is `"Bash"`, and the `"if": "Bash(git commit *)"` sits
**inside the hook object alongside `command`/`timeout`/`statusMessage`**, not in
the matcher position, so nothing consumes it. The emitted JSON is
`{systemMessage, hookSpecificOutput:{hookEventName, additionalContext}}` — **no
`permissionDecision` field**, so a FAIL cannot block anything. Both halves of
`CLAUDE.md` §2's claim reproduce.

**Cost:** §2 is the section a reader opens to learn what the checker does. It
tells them a FAIL will be caught at commit time. It will not be. The correction
is 250 lines away under a different heading.

---

**G12-7. `docs/reference/repo-maintenance.md:204` — both numbers in the
`unplaced.csv` sentence are stale, inside the blockquote that exists to narrate
this exact failure.**

`[repo] docs/reference/repo-maintenance.md:204-208`:

> **`hardware/unplaced.csv` holds the 50 rows of 138 that no schematic page
> names.** … Two of its clusters name circuits this corpus has no page for — six
> identical jack-protection networks drawn three times, and nineteen decoupling
> capacitors with no home.

`[test]` `csv.reader` over both files at the freeze:

| Claim | Stated | Actual |
|---|---|---|
| `unplaced.csv` rows | **50** | **32** |
| `bom.csv` rows | **138** | **140** |
| "six identical jack-protection networks" | present | **absent** from `unplaced.csv` |
| "nineteen decoupling capacitors with no home" | present | **absent**; the largest unplaced row is `CAP1-n`, qty **21**, which is **keycaps** (`MT165-MX`), not capacitors |

`[repo] docs/reference/repo-maintenance.md:210-213`, nine lines below, is the
blockquote's own closing line:

> *This section described `bom.csv` as the file you edit for several hours after
> it stopped being one. Found by a cold reviewer. It is the project's named
> failure mode, in the document that exists to record exactly this trap.*

The paragraph corrected one instance of the failure and carries four more.

---

**G12-8. `docs/reference/pcb-pipeline.md:152-176` — a four-number table, all
four stale, and one emphatic conclusion that is now false.**

`[repo] docs/reference/pcb-pipeline.md:152-157`:

| | Rows stated | Rows actual | Units stated | Units actual |
|---|---|---|---|---|
| `hardware/bom.csv` master | 138 | **140** | 388 | — |
| 23 per-circuit fragments | 104 | **108** | 313 | — |
| `hardware/unplaced.csv` | 34 | **32** | 75 | **67** |

`[test] python3 -c` over `hardware/bom.csv`, `hardware/unplaced.csv` and
`glob('hardware/**/bom.csv')`; `[test] python3 tools/merge-bom.py --check` →
`checked 140 rows from 26 fragments`.

More serious is `[repo] docs/reference/pcb-pipeline.md:158-162` and `:174`:

> Of those 34, five are module-board netlist parts and would be missing from
> `module.net`: **`J-CV` ×6** (the CV jacks — the module's whole output
> connector set), `U-TVS-MODULE`, `D-CLAMP-BREATH` ×2, `R-BREATH-SUM` ×2 and
> `R-BREATH-OFF` ×2. **Thirteen units.**
> …
> **The CV jacks are not** [placed]**, and neither are the four rows beside
> them.**

`[test]` grep for those refdes across fragments:

- `J-CV` is at `[repo] hardware/module/bom.csv:5` — **placed.**
- `D-CLAMP-BREATH` is at `[repo] hardware/module/breath-receive-stage/bom.csv:7`
  — **placed.**
- Only `U-TVS-MODULE` (1), `R-BREATH-SUM` (2) and `R-BREATH-OFF` (2) remain in
  `unplaced.csv`. **Three refdes, five units, not five and thirteen.**

**Cost:** this is the section that tells you what the generated KiCad netlist
will be missing. It currently tells a reader the module will emit with no CV
jacks — its entire output connector set. Someone acting on that goes looking for
a bug that was fixed.

Note that `[repo] docs/reference/pcb-pipeline.md:170-176` is itself a
"*this warning used to say ~50 rows / 105 units*" correction — and
`repo-maintenance.md:204` (G12-7) still says the ~50. The two pages disagree
about the same count, in opposite directions, and both are wrong.

---

**G12-9. `docs/reference/repo-maintenance.md:191` — "24 per-circuit `bom.csv`
fragments"; `merge-bom.py` reads 26.**

`[test] python3 tools/merge-bom.py --check` → `checked 140 rows from 26
fragments`. `[test] find hardware -name bom.csv` → 25 fragments (22 circuit-level
plus three board-level aggregates at `hardware/{carrier,cluster,module}/bom.csv`),
and `[repo] tools/merge-bom.py:85,97-98` adds `hardware/unplaced.csv` as a
26th. `[repo] docs/reference/pcb-pipeline.md:154` independently says "23
per-circuit fragments", which is the `circuit.yaml` count
(`[test] find hardware -name circuit.yaml` → 23), not the fragment count. Three
documents, three different numbers, one authority (`merge-bom.py`) that prints
the right one on every run.

---

**G12-10. `docs/reference/repo-maintenance.md:339-348` — "Both assertions hold
as of this writing." One does not, for precisely the reason the same paragraph
gives.**

`[repo] docs/reference/repo-maintenance.md:339-348` publishes a four-line check
and asserts it passes:

```
tracked = set(git ls-files)
placed  = {r.new for r in rows if r.kind != "deleted"}
assert not (tracked - placed)      # no tracked file without a row
assert not (placed - tracked)      # no row pointing at nothing
```

`[test]` run verbatim against `docs/reference/path-map-2026-09-21.csv` and
`git ls-files` at HEAD:

- `placed - tracked` = **0** ✅ (the second assertion holds)
- `tracked - placed` = **35** ❌ — 33 under `docs/review/2026-09-22-fix-audit*`
  and `…-goal-verification/`, plus **`tools/audit-notes.py` and
  `tools/extract-findings.py`**

The paragraph three lines above predicted it: *"run it whenever files are added,
because **a new file is an orphan the moment it is committed**."* It was written,
the check was published, and the check was not run again. `CLAUDE.md`'s fourth
recorded fix pattern — *a fix whose own explanation restates the wrong value* —
in its purest form.

**What is verified good** (`[test]`, same script): the **old side is an exact
bijection onto `81c081d`** — 287 rows, 287 tracked files at that commit, zero in
either difference. That claim at `[repo] …:319-322` is true.

---

**G12-11. `docs/reference/repo-maintenance.md:323` — "405 tracked files, plus 4
`deleted` and 1 duplicate destination".**

`[test]` `collections.Counter` over the map's `kind` column: 410 rows total ✅;
`deleted` = 4 ✅; non-deleted rows = **406**, mapping to **406 unique** `new`
paths — **zero duplicate destinations**. So the breakdown should read "406
tracked files plus 4 deleted". The arithmetic still sums to 410, which is why
nothing caught it: the total was checked and the parts were not.

---

**G12-12. `README.md:117` — "`docs/review/` holds nine waves", in the sentence
that exists to explain why counts are not restated.**

`[repo] README.md:115-121`:

> `datasheets/` is the largest directory in the repository; `docs/review/` holds
> **nine** waves. … The counts that used to sit in this sentence — "77 banked
> documents", "seven waves" — were true when written and wrong within the week,
> **which is the whole reason this repository cites rather than restates**.

`[test] ls -d docs/review/*/ | wc -l` → **12** at HEAD, **11** at the frozen
`a4b80b1`. Nine is wrong either way.

`[repo] CLAUDE.md` § *Review waves* names this exact sentence as a recurring
defect: *"It said 'three' for months while the directory held nine, was
corrected to 'nine' on 2026-09-21, and was wrong again within a day — the third
recorded instance of this repository's named failure."* **This is the fourth.**
The sentence removed two of its three restated counts and kept the one that was
about to move; the retained count is the one being used as the illustration of
why counts must not be retained.

**Sibling claim, verified true:** "`datasheets/` is the largest directory" —
`[test] du -sh` → `datasheets` 58M vs `docs` 9.2M, `hardware` 888K. True by
size. (By *file* count `docs` has 231 to `datasheets`' 88, so the reading is
size, not files. Not a defect; worth a word if the sentence is ever rewritten.)

---

**G12-13. `README.md:111` — the repository layout does not mention
`config/figures.yaml`. Neither does any other word of `README.md` or
`ROADMAP.md`.**

`[repo] README.md:111`:

```
config/           Key layout and routing, as data
```

`[test] ls config/` → `figures.yaml` (72 KB, 37 tracked figures) and
`key-layout.yaml`. `[test] grep -c "figures.yaml" README.md ROADMAP.md
firmware/README.md` → **0, 0, 0**. `[test] grep -in "figures\|CLAUDE.md\|
check-staleness\|register" README.md` → **no matches at all**.

Two problems in one line:

1. **"routing" names a file that does not exist.** The routing matrix lives in
   NVS, not in `config/` — `[repo] firmware/README.md:147-150`: "Routing matrix
   — four mod channels… Both live in NVS and are editable from the display and
   over USB."
2. **`figures.yaml` is invisible to a new reader.** It is the mechanism
   `CLAUDE.md` rule 1 is built on, and `README.md:123-134` ("Where to start
   reading") sends a newcomer to five documents, none of which is the register.

`[repo] README.md:136-140` records the identical defect being fixed once
already — `hardware/README.md` had "**zero inbound links from anywhere in the
corpus**". The register now has the same status in the file a new reader opens
first.

---

**G12-14. `README.md:98` — `docs/reference/` is described as holding "fingering
notes". It does not.**

`[test] ls docs/reference/` → `ks33-geometry.md`, `latency-budget.md`,
`path-map-2026-09-21.csv`, `pcb-pipeline.md`, `repo-maintenance.md`.
`[test] grep -rl "fingering" docs/reference/` → **no files**. The directory's two
largest inhabitants — the PCB pipeline and the maintenance/path-map reference —
are not described by "Latency budgets, fingering notes, specs" at all.

---

**G12-15. Tracked figures are restated outside their owners in six places, and
`check-staleness.py` is structurally incapable of seeing it.**

`[test]` scripted: for each `settled` figure, take its distinctive numeric
tokens (≥4 chars) and find every corpus file other than the declared `owner`
that writes them out. Filtering substring noise by hand:

| Figure | Owner | Restated at |
|---|---|---|
| `mod-reference` `3.3333 V` | `hardware/module/mod-channels/mod-channels.md` | `[repo] docs/decisions/0006-…:15, 21, 105` (table cell, prose, and the governing equation) and **`[repo] firmware/README.md:56`** |
| `key-scan-current` | `hardware/cluster/key-switch-network/…` | `[repo] docs/decisions/0001-…:230` — "**1.43 mA** per closed key; 18 closed = **25.8 mA**" |
| `key-release-time` `119.9 us` | same | `[repo] docs/decisions/0001-…:227` |
| `key-press-time` `5.92 us` | same | `[repo] docs/decisions/0001-…:228` |
| `ks33-contact-bounce` | `docs/reference/ks33-geometry.md` | `[repo] docs/reference/latency-budget.md:126` and `:148`, and `[repo] ROADMAP.md:121` |
| `panel-height-budget` `115.5` | `docs/decisions/0004-…` | `[repo] hardware/module/panel/panel.md:58` |

(Some `docs/decisions/0006` hits at `:92` and `:117` are legitimate — they quote
the refuted `2.5 V` alongside. `:15`, `:21` and `:105` are plain restatements.)

**Why nothing catches it.** `[repo] tools/check-staleness.py:835-876`,
`check_restated`, builds a `known` set from every register `value` and
`forbidden` entry and then **skips any number in it**:

```python
for n, u in set(NUM_UNIT.findall(text)):
    if n in known or float(n) == 0:
        continue
```

Its docstring scopes it deliberately — "A number restated across three or more
files, **with no register entry**". So the advisory covers the *pre*-defect
state for untracked values (211 of them at the freeze), and the *actual rule 1
violation* — a **tracked** figure written out away from its owner — is the one
case excluded by construction. `check_owners` (`:880`) proves the owner states
the value; nothing proves that nobody else does.

**Cost:** `mod-reference` is the figure whose `escape_note`
(`[repo] config/figures.yaml:364-377`) records it going stale *inside its own
owner document* once already. It is now written out in four more files, two of
which (`ADR 0006:105`, `firmware/README.md:56`) are the ones a firmware author
reads before writing channel 7.

---
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
