jeffmhopkins/Woody/docs/review/2026-09-22-goal-verification/G2-cross-references.md

# G2 — Cross-references: does the cited thing say what the citing text implies?

**Slice:** G2, cold. I did not open anything under `docs/review/` — not this
wave's README, not any prior wave. Nothing in this report is informed by
another reviewer.

**Revision measured against:** `a4b80b1`. `git diff a4b80b1 HEAD --stat` is one
file, this wave's own `docs/review/…/README.md`, which I did not read.

**Tree instability, and how I handled it.** Partway through this slice the
working tree changed under me: `hardware/module/pitch-stage/circuit.yaml` and
`hardware/module/power-entry/circuit.yaml` each gained an appended comment
(`# G10: this row previously said -9.6 V…`, `# This field previously said ~275
instrument mA…`), and the `PreToolUse` staleness hook flipped
`PASS → FAIL (1 stale) → FAIL (2 stale) → PASS` across read-only calls of mine.
The coordinator has since confirmed this was an injection-testing slice working
in the same tree, and that `tools/check-staleness.py` was itself patched at one
point.

**So every finding below was re-derived against a pinned checkout**
(`git clone /home/user/Woody /tmp/g2-check && git checkout a4b80b1`), and every
line number and quotation was re-read from that pinned tree. At the moment of
the final verification run `git status --short` in `/home/user/Woody` showed no
modified tracked files (only untracked `docs/review/…` files belonging to other
slices, which I did not open). **I quote no tool output from
`tools/check-staleness.py` as evidence for any finding** — every check below is
one I wrote and ran myself, in the pinned tree.

**Nothing here rests on an untracked artefact, and I have checked that
specifically.** `git ls-files .staleness .staleness-report.txt` is empty, so
`.staleness/report.txt`, `.staleness-report.txt` and the `staleness check:`
banner the hook prints before each Bash call are all untracked snapshots of
whatever the tree held when the hook last ran. I read `.staleness/report.txt`
exactly once, to work out *why* the hook had started failing — which is how I
noticed the tree was moving — and **no finding in this report cites it, or the
banner, or any other untracked file.** Every `[test]` claim is a script of mine
over tracked files in `/tmp/g2-check` at `a4b80b1`. **I therefore have nothing
to withdraw.** For completeness: `diff -rq` over `hardware/`,
`docs/decisions/`, `docs/reference/`, `config/`, `firmware/` plus `cmp` on
`README.md`, `ROADMAP.md` and `datasheets/MANIFEST.csv`, live against the pin,
reports **no differences** — so the working tree I originally read from and the
pin are byte-identical for everything I cite.

---
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
