jeffmhopkins/Woody/docs/review/2026-09-22-goal-verification/G3-staleness-independent.md

# G3 — Staleness, decided independently of the checker

**Slice:** G3, cold. **Brief:** decide for myself whether the design corpus is
self-consistent, without using `tools/check-staleness.py`'s verdict as
evidence.

**Revision measured:** the corpus at `a4b80b1`. I verified this is also the
corpus at `HEAD` (`25cc740`): `[test] git diff --stat a4b80b1 HEAD` → one file
changed, `docs/review/2026-09-22-goal-verification/README.md`, +81 lines. No
corpus file differs, so every finding below reproduces at either revision.
I did not modify `tools/`.
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
