jeffmhopkins/Woody/hardware/carrier/carrier.kicad_sch

## KiCad design hardware/carrier/carrier.kicad_sch (2026-09-30)

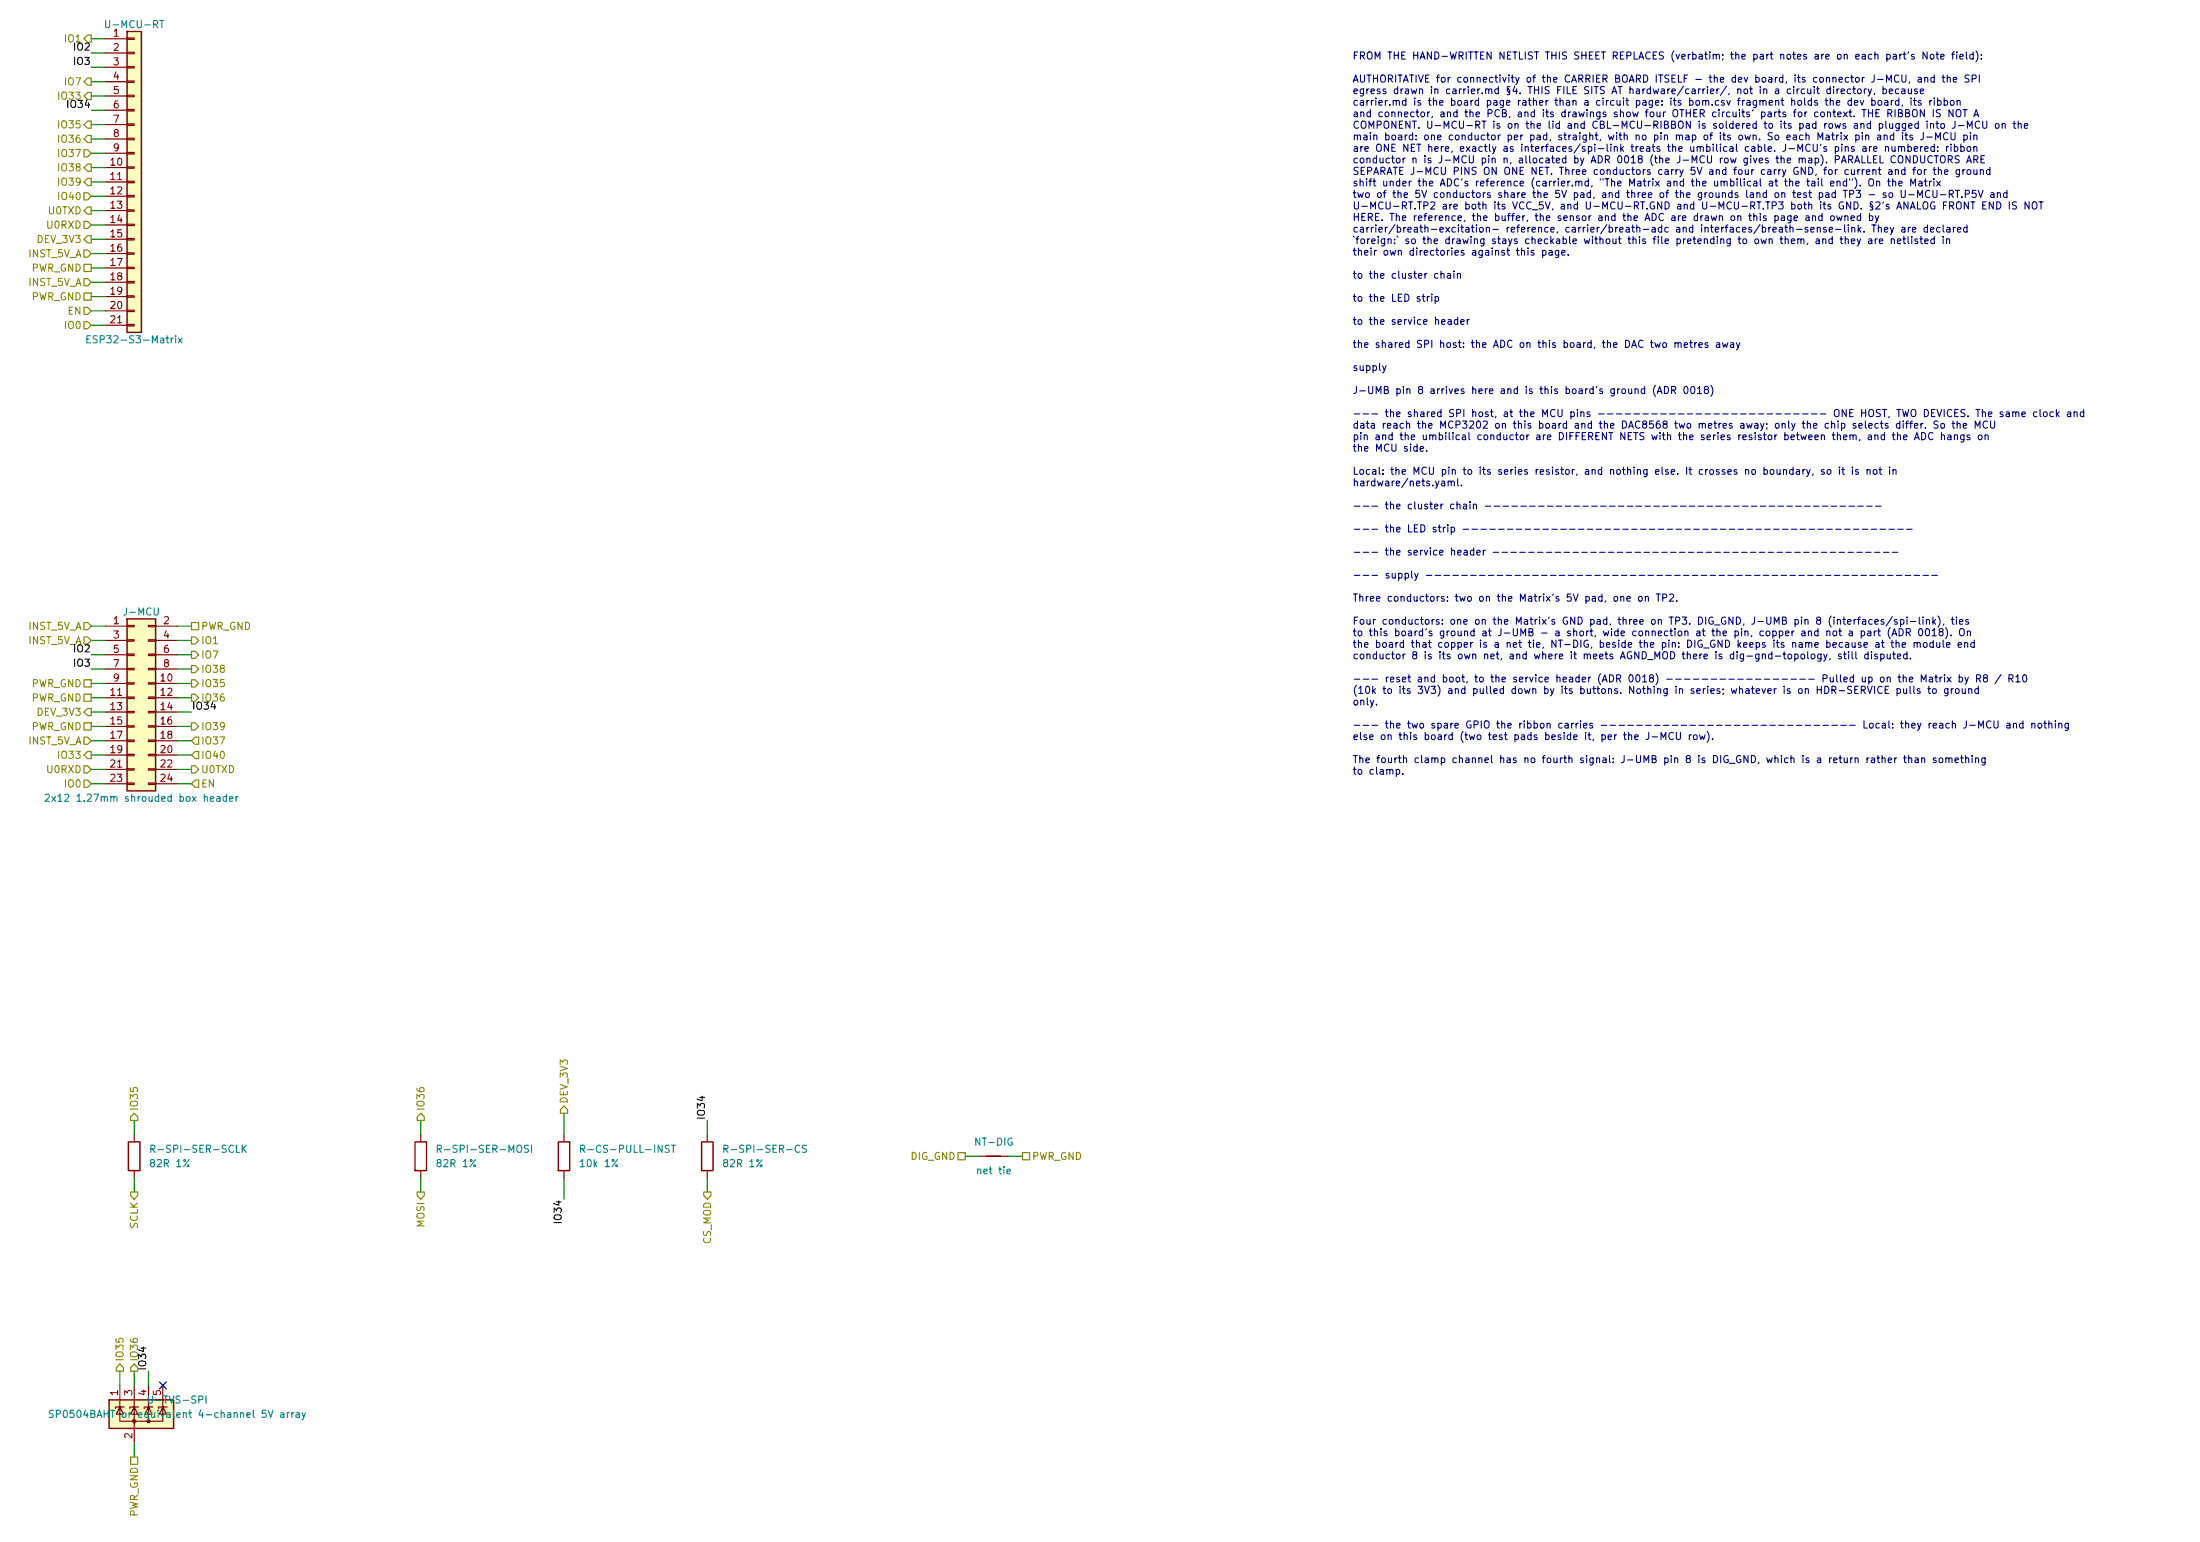
[picture p187: schematic carrier.kicad_sch]

Parts:
J-MCU: 2x12 1.27mm shrouded box header; PinHeader_2x12_P1.27mm_Horizontal; MPN X1270WR-2x12A-9TV01; LCSC C5147255
NT-DIG: net tie; NetTie-2_SMD_Pad2.0mm
R-CS-PULL-INST: 10k 1%; R_0805_2012Metric; MPN 0805W8F1002T5E; LCSC C17414
R-SPI-SER-CS: 82R 1%; R_1206_3216Metric; MPN 1206W4F820JT5E; LCSC C17980
R-SPI-SER-MOSI: 82R 1%; R_1206_3216Metric; MPN 1206W4F820JT5E; LCSC C17980
R-SPI-SER-SCLK: 82R 1%; R_1206_3216Metric; MPN 1206W4F820JT5E; LCSC C17980
U-MCU-RT: ESP32-S3-Matrix
U-TVS-SPI: SP0504BAHT or equivalent 4-channel 5V array; SOT-23-5; MPN SP0504BAHTG; LCSC C10675

Connections:
CS_MOD: R-SPI-SER-CS.2
DEV_3V3: J-MCU.13, R-CS-PULL-INST.1, U-MCU-RT.15
DIG_GND: NT-DIG.1
EN: J-MCU.24, U-MCU-RT.20
INST_5V_A: J-MCU.1, J-MCU.3, J-MCU.17, U-MCU-RT.16, U-MCU-RT.18
IO0: J-MCU.23, U-MCU-RT.21
IO1: J-MCU.4, U-MCU-RT.1
IO2: J-MCU.5, U-MCU-RT.2
IO3: J-MCU.7, U-MCU-RT.3
IO7: J-MCU.6, U-MCU-RT.4
IO33: J-MCU.19, U-MCU-RT.5
IO34: J-MCU.14, R-CS-PULL-INST.2, R-SPI-SER-CS.1, U-MCU-RT.6, U-TVS-SPI.4 (K)
IO35: J-MCU.10, R-SPI-SER-SCLK.1, U-MCU-RT.7, U-TVS-SPI.1 (K)
IO36: J-MCU.12, R-SPI-SER-MOSI.1, U-MCU-RT.8, U-TVS-SPI.3 (K)
IO37: J-MCU.18, U-MCU-RT.9
IO38: J-MCU.8, U-MCU-RT.10
IO39: J-MCU.16, U-MCU-RT.11
IO40: J-MCU.20, U-MCU-RT.12
MOSI: R-SPI-SER-MOSI.2
PWR_GND: J-MCU.2, J-MCU.9, J-MCU.11, J-MCU.15, NT-DIG.2, U-MCU-RT.17, U-MCU-RT.19, U-TVS-SPI.2 (A)
SCLK: R-SPI-SER-SCLK.2
U0RXD: J-MCU.21, U-MCU-RT.14
U0TXD: J-MCU.22, U-MCU-RT.13

Notes on the sheet:
FROM THE HAND-WRITTEN NETLIST THIS SHEET REPLACES (verbatim; the part notes are on each part's Note field): AUTHORITATIVE for connectivity of the CARRIER BOARD ITSELF - the dev board, its connector J-MCU, and the SPI egress drawn in carrier.md §4. THIS FILE SITS AT hardware/carrier/, not in a circu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
