jeffmhopkins/Woody/hardware/carrier/breath-adc/breath-adc.kicad_sch

## KiCad design hardware/carrier/breath-adc/breath-adc.kicad_sch (2026-09-30)

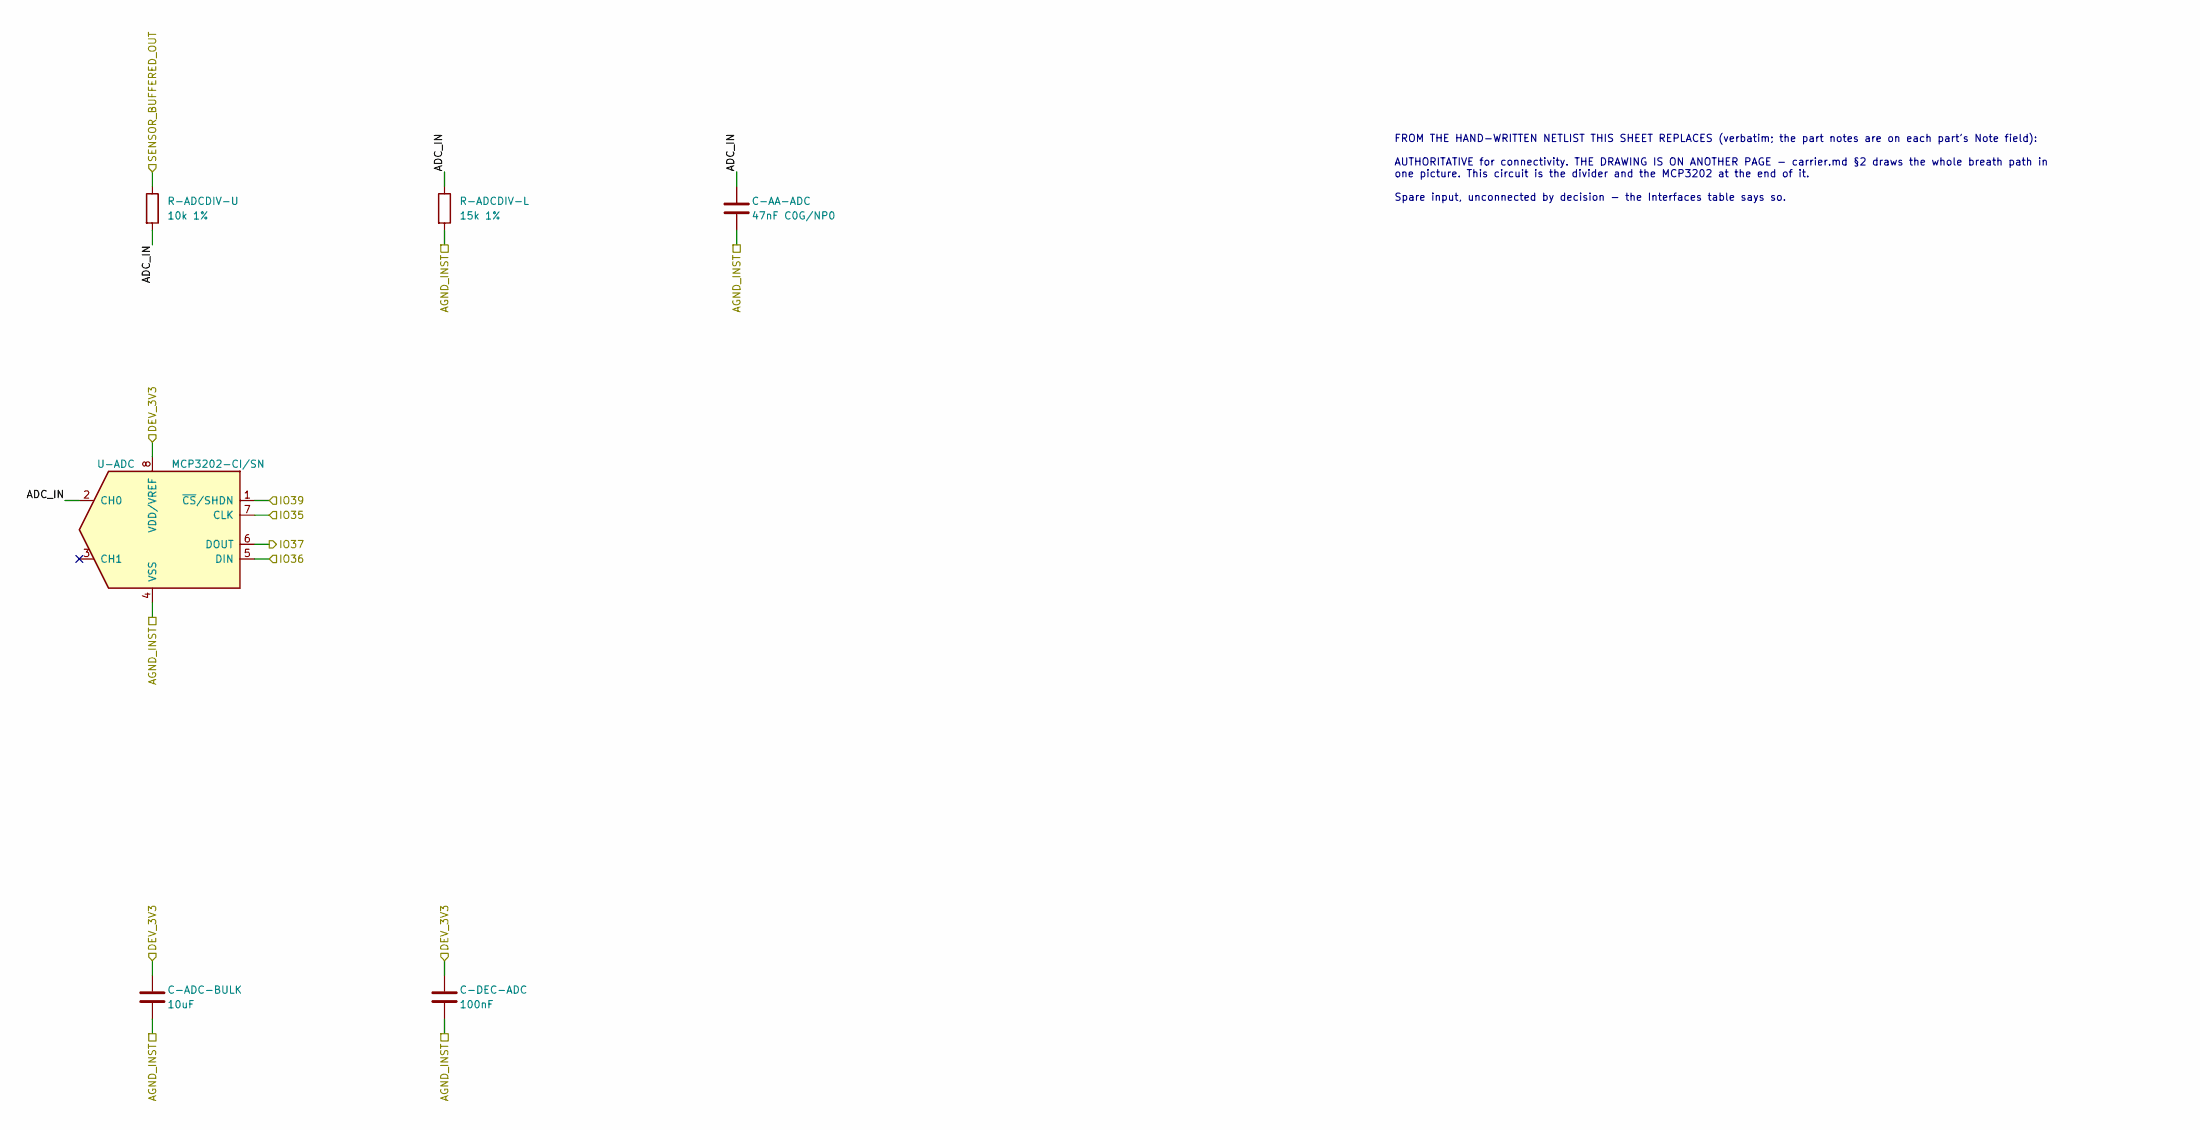
[picture p188: schematic breath-adc.kicad_sch]

Parts:
C-AA-ADC: 47nF C0G/NP0; C_0805_2012Metric; MPN C0805C473J3GACTU; LCSC C22402129
C-ADC-BULK: 10uF; C_1206_3216Metric; MPN CL31B106KBHNNNE; LCSC C89632
C-DEC-ADC: 100nF; C_0805_2012Metric; MPN CC0805KRX7R9BB104; LCSC C49678
R-ADCDIV-L: 15k 1%; R_0805_2012Metric; MPN RT0805FRE0715KL; LCSC C869203
R-ADCDIV-U: 10k 1%; R_0805_2012Metric; MPN RT0805FRE0710KL; LCSC C869153
U-ADC: MCP3202-CI/SN; SOIC-8_3.9x4.9mm_P1.27mm; MPN MCP3202-CI/SN; LCSC C56997

Connections:
ADC_IN: C-AA-ADC.1, R-ADCDIV-L.1, R-ADCDIV-U.2, U-ADC.2 (CH0)
AGND_INST: C-AA-ADC.2, C-ADC-BULK.2, C-DEC-ADC.2, R-ADCDIV-L.2, U-ADC.4 (VSS)
DEV_3V3: C-ADC-BULK.1, C-DEC-ADC.1, U-ADC.8 (VDD/VREF)
IO35: U-ADC.7 (CLK)
IO36: U-ADC.5 (DIN)
IO37: U-ADC.6 (DOUT)
IO39: U-ADC.1 (~CS/SHDN)
SENSOR_BUFFERED_OUT: R-ADCDIV-U.1

Notes on the sheet:
FROM THE HAND-WRITTEN NETLIST THIS SHEET REPLACES (verbatim; the part notes are on each part's Note field): AUTHORITATIVE for connectivity. THE DRAWING IS ON ANOTHER PAGE - carrier.md §2 draws the whole breath path in one picture. This circuit is the divider and the MCP3202 at the end of it. Spare 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
