jeffmhopkins/Woody/hardware/carrier/breath-excitation-reference/breath-excitation-reference.kicad_sch

## KiCad design hardware/carrier/breath-excitation-reference/breath-excitation-reference.kicad_sch (2026-09-30)

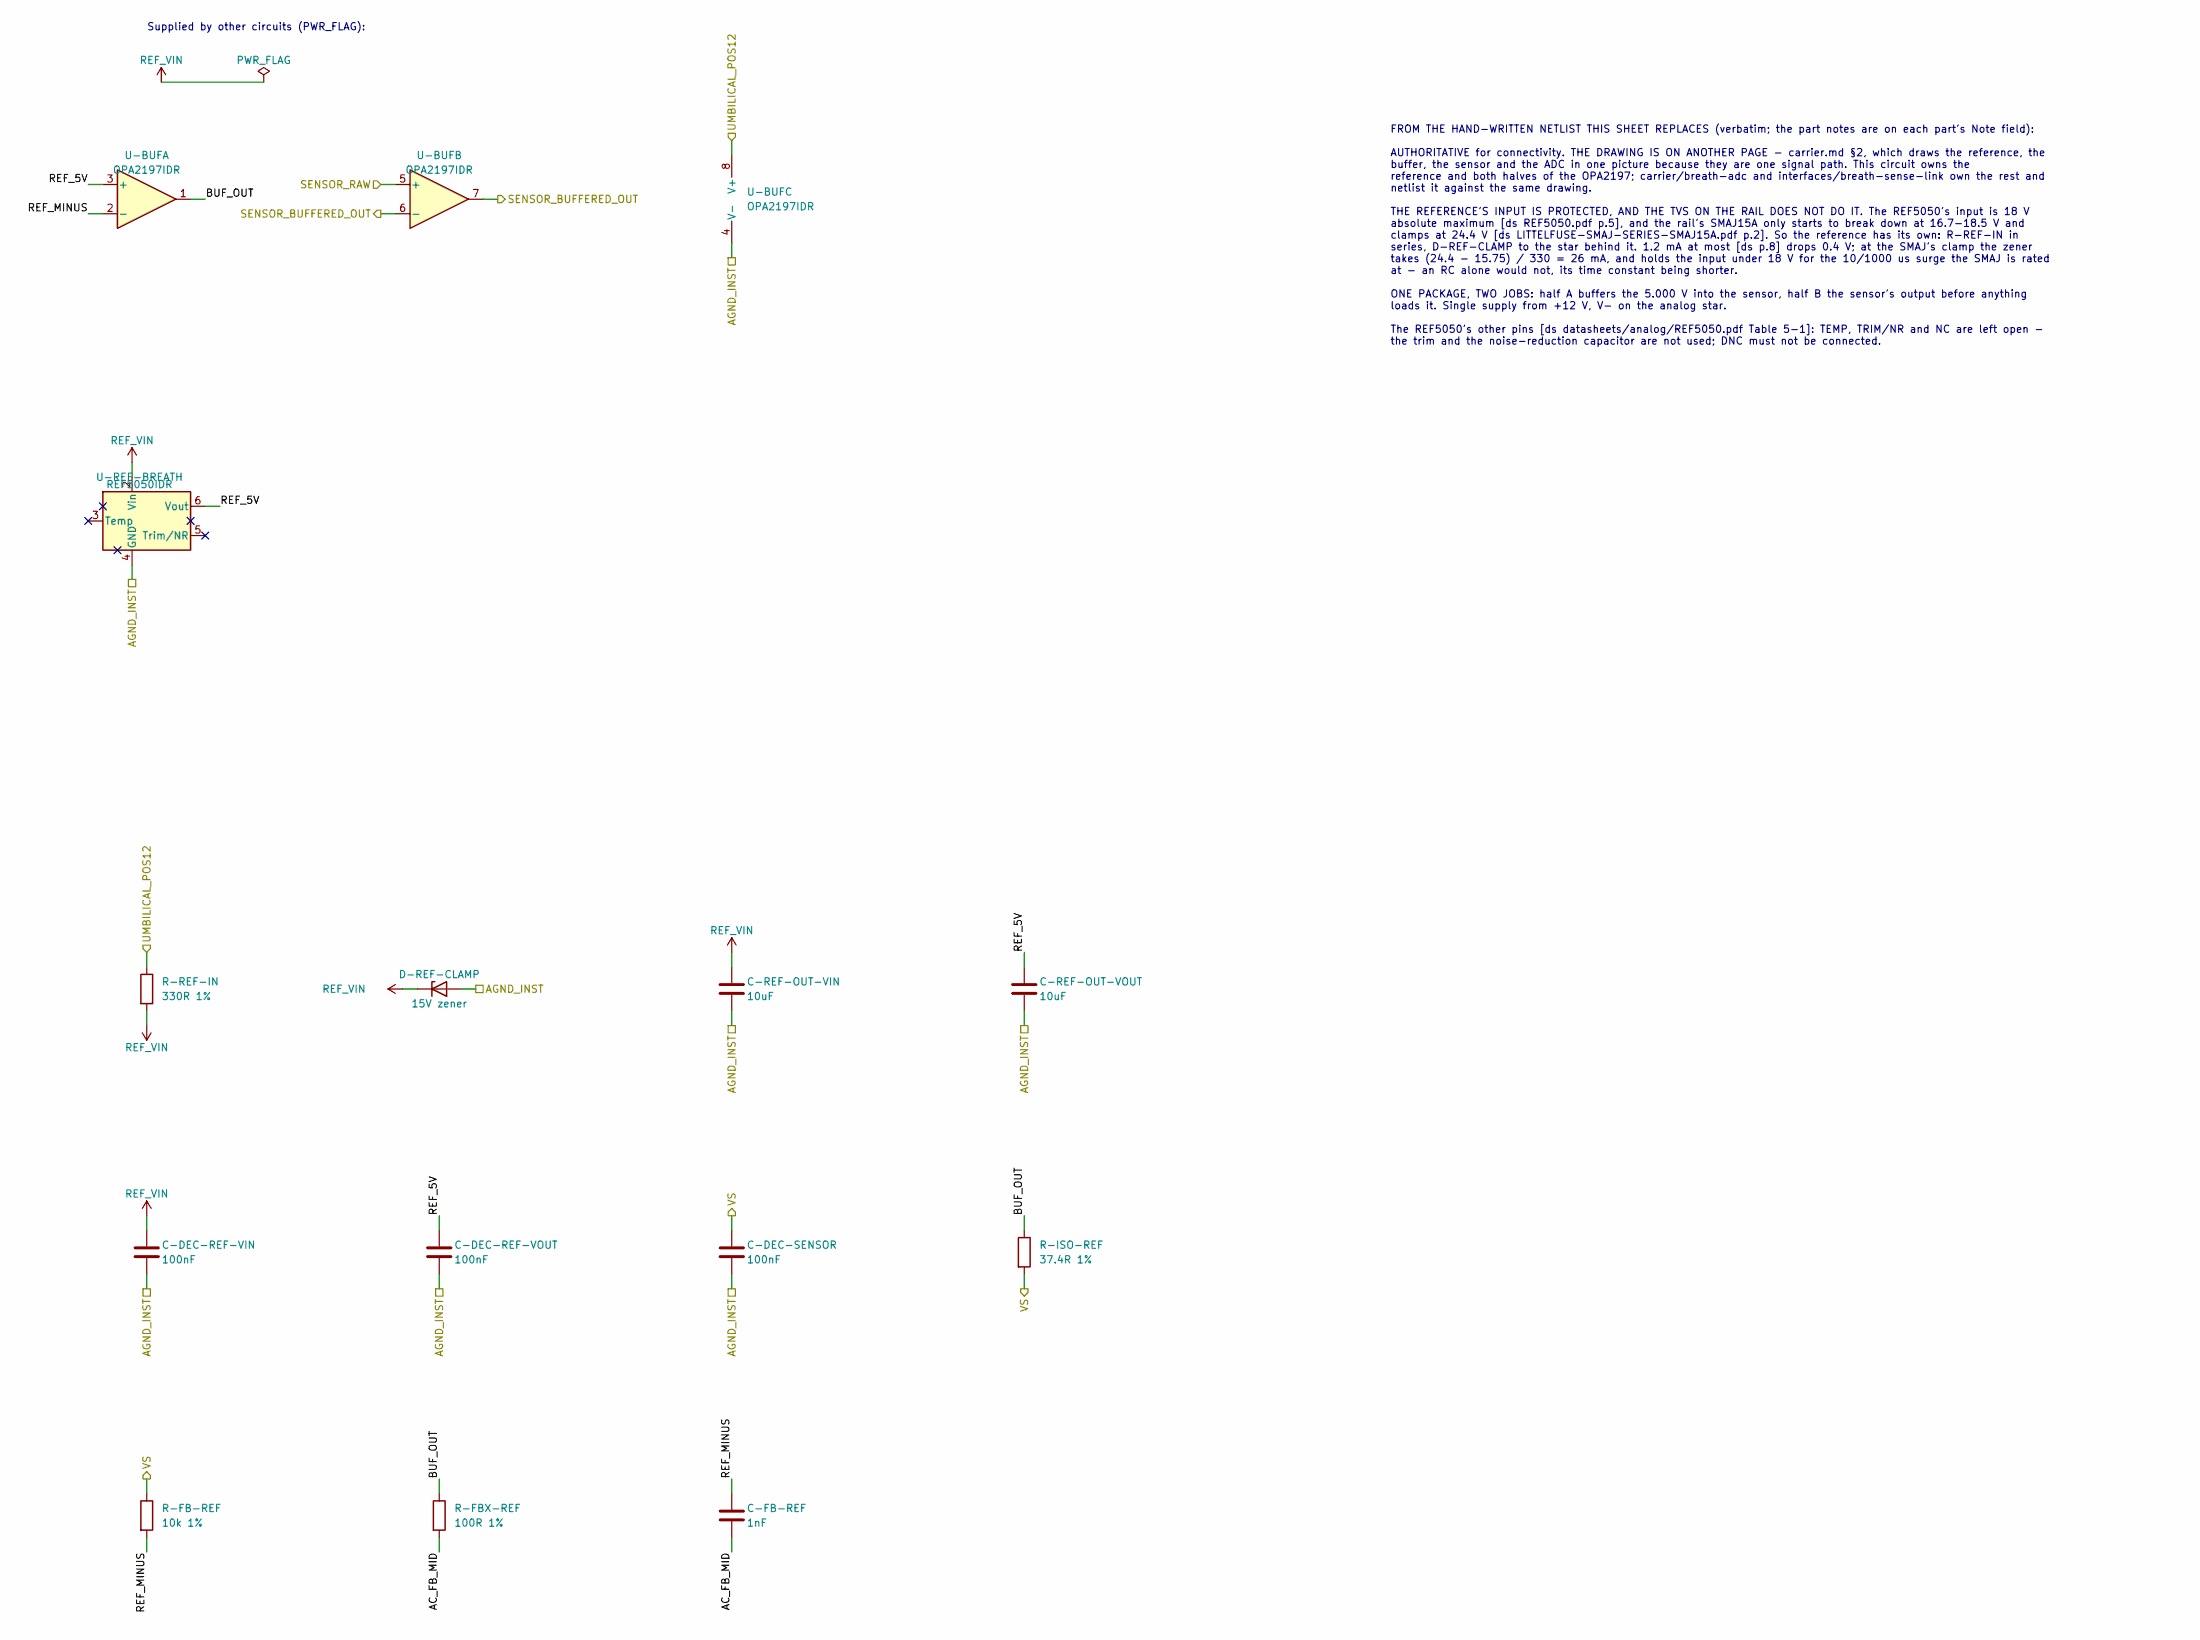
[picture p189: schematic breath-excitation-reference.kicad_sch]

Parts:
C-DEC-REF-VIN: 100nF; C_0805_2012Metric; MPN CC0805KRX7R9BB104; LCSC C49678
C-DEC-REF-VOUT: 100nF; C_0805_2012Metric; MPN CC0805KRX7R9BB104; LCSC C49678
C-DEC-SENSOR: 100nF; C_0805_2012Metric; MPN CC0805KRX7R9BB104; LCSC C49678
C-FB-REF: 1nF; C_0805_2012Metric; MPN CC0805JRNPO9BN102; LCSC C62774
C-REF-OUT-VIN: 10uF; C_1206_3216Metric; MPN CL31B106KBHNNNE; LCSC C89632
C-REF-OUT-VOUT: 10uF; C_1206_3216Metric; MPN CL31B106KBHNNNE; LCSC C89632
D-REF-CLAMP: 15V zener; D_SOD-123; MPN MMSZ5245BT1G; LCSC C129730
R-FB-REF: 10k 1%; R_0805_2012Metric; MPN 0805W8F1002T5E; LCSC C17414
R-FBX-REF: 100R 1%; R_0805_2012Metric; MPN 0805W8F1000T5E; LCSC C17408
R-ISO-REF: 37.4R 1%; R_0805_2012Metric; MPN CR0805-FX-37R4ELF; LCSC C204458
R-REF-IN: 330R 1%; R_0805_2012Metric; MPN 0805W8F3300T5E; LCSC C17630
U-BUF: OPA2197IDR; SOIC-8_3.9x4.9mm_P1.27mm; MPN OPA2197IDR; LCSC C139363
U-REF-BREATH: REF5050IDR; SOIC-8_3.9x4.9mm_P1.27mm; MPN REF5050IDR; LCSC C24696

Connections:
AC_FB_MID: C-FB-REF.2, R-FBX-REF.2
AGND_INST: C-DEC-REF-VIN.2, C-DEC-REF-VOUT.2, C-DEC-SENSOR.2, C-REF-OUT-VIN.2, C-REF-OUT-VOUT.2, D-REF-CLAMP.2 (A), U-BUF.4 (V-), U-REF-BREATH.4 (GND)
BUF_OUT: R-FBX-REF.1, R-ISO-REF.1, U-BUF.1
REF_5V: C-DEC-REF-VOUT.1, C-REF-OUT-VOUT.1, U-BUF.3 (+), U-REF-BREATH.6 (Vout)
REF_MINUS: C-FB-REF.1, R-FB-REF.2, U-BUF.2 (-)
REF_VIN: C-DEC-REF-VIN.1, C-REF-OUT-VIN.1, D-REF-CLAMP.1 (K), R-REF-IN.2, U-REF-BREATH.2 (Vin)
SENSOR_BUFFERED_OUT: U-BUF.6 (-), U-BUF.7
SENSOR_RAW: U-BUF.5 (+)
UMBILICAL_POS12: R-REF-IN.1, U-BUF.8 (V+)
VS: C-DEC-SENSOR.1, R-FB-REF.1, R-ISO-REF.2

Notes on the sheet:
Supplied by other circuits (PWR_FLAG):
FROM THE HAND-WRITTEN NETLIST THIS SHEET REPLACES (verbatim; the part notes are on each part's Note field): AUTHORITATIVE for connectivity. THE DRAWING IS ON ANOTHER PAGE - carrier.md §2, which draws the reference, the buffer, the sensor and the ADC in one picture because they are one signal path. 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
