jeffmhopkins/Woody/hardware/carrier/led-strip-drive/led-strip-drive.kicad_sch

## KiCad design hardware/carrier/led-strip-drive/led-strip-drive.kicad_sch (2026-09-30)

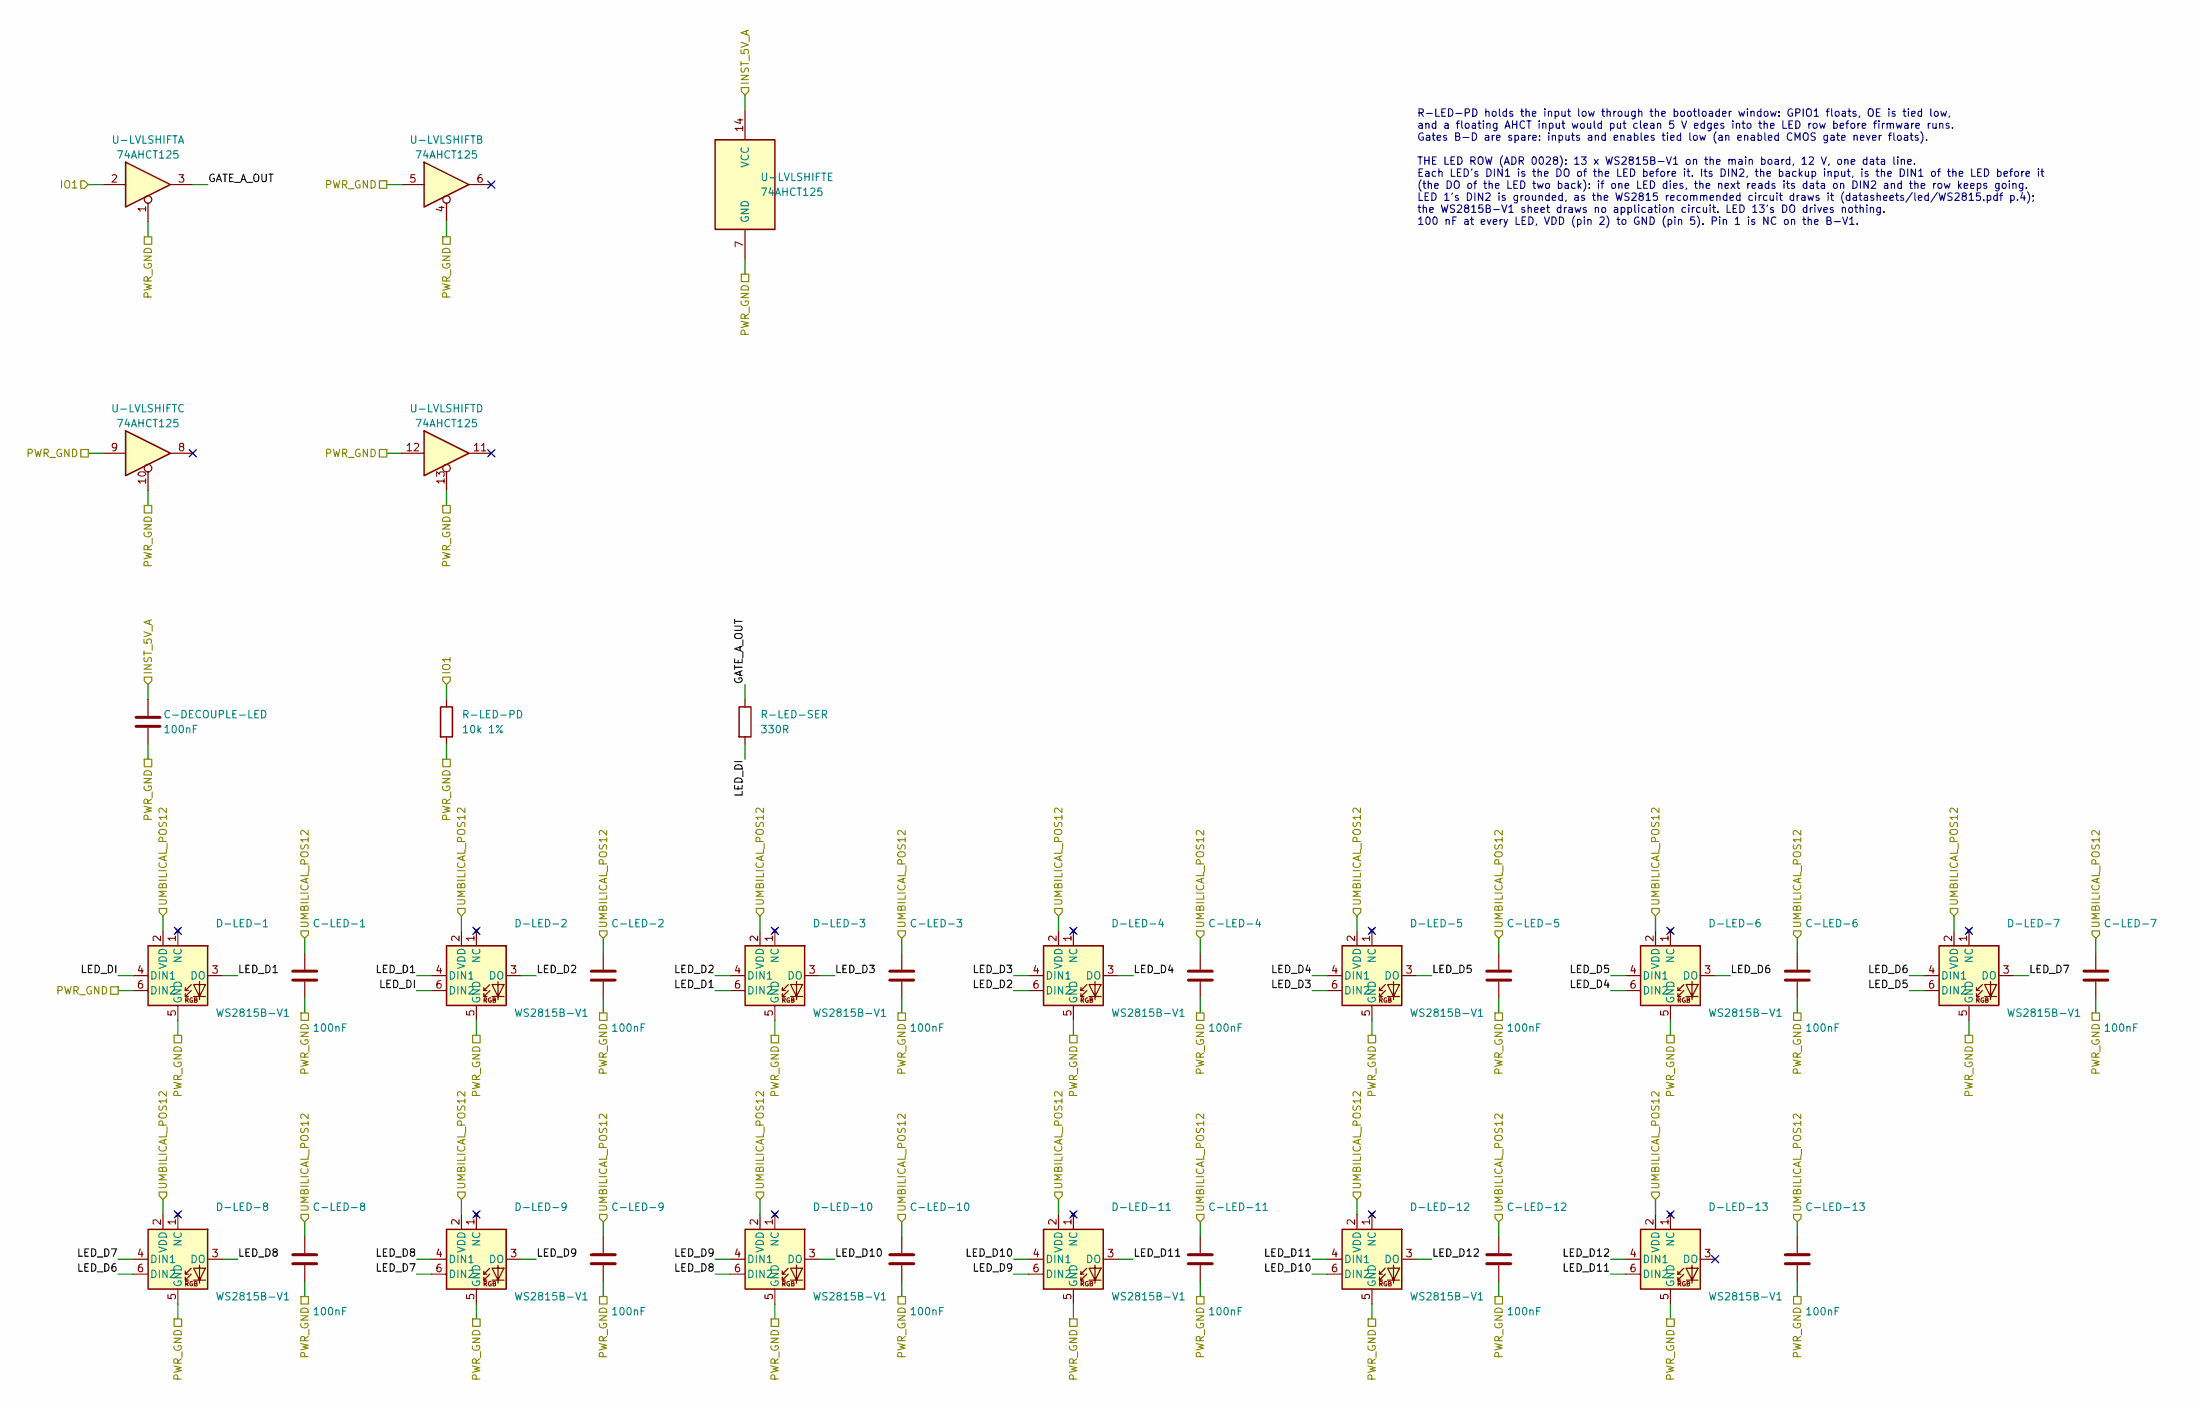
[picture p190: schematic led-strip-drive.kicad_sch]

Parts:
C-DECOUPLE-LED: 100nF; C_0805_2012Metric; MPN CC0805KRX7R9BB104; LCSC C49678
C-LED-1, C-LED-2, C-LED-3, C-LED-4, C-LED-5, C-LED-6, C-LED-7, C-LED-8, C-LED-9, C-LED-10, C-LED-11, C-LED-12, C-LED-13: 100nF; C_0805_2012Metric; MPN CC0805KRX7R9BB104; LCSC C49678
D-LED-1, D-LED-2, D-LED-3, D-LED-4, D-LED-5, D-LED-6, D-LED-7, D-LED-8, D-LED-9, D-LED-10, D-LED-11, D-LED-12, D-LED-13: WS2815B-V1; LED_WS2815B-V1_PLCC6_5.4x5.0mm_P1.6mm; MPN WS2815B-V1; LCSC C5446699
R-LED-PD: 10k 1%; R_0805_2012Metric; MPN 0805W8F1002T5E; LCSC C17414
R-LED-SER: 330R; R_0805_2012Metric; MPN 0805W8F3300T5E; LCSC C17630
U-LVLSHIFT: 74AHCT125; SOIC-14_3.9x8.7mm_P1.27mm; MPN SN74AHCT125DR; LCSC C155176

Connections:
GATE_A_OUT: R-LED-SER.1, U-LVLSHIFT.3
INST_5V_A: C-DECOUPLE-LED.1, U-LVLSHIFT.14 (VCC)
IO1: R-LED-PD.1, U-LVLSHIFT.2
LED_D1: D-LED-1.3 (DO), D-LED-2.4 (DIN1), D-LED-3.6 (DIN2)
LED_D2: D-LED-2.3 (DO), D-LED-3.4 (DIN1), D-LED-4.6 (DIN2)
LED_D3: D-LED-3.3 (DO), D-LED-4.4 (DIN1), D-LED-5.6 (DIN2)
LED_D4: D-LED-4.3 (DO), D-LED-5.4 (DIN1), D-LED-6.6 (DIN2)
LED_D5: D-LED-5.3 (DO), D-LED-6.4 (DIN1), D-LED-7.6 (DIN2)
LED_D6: D-LED-6.3 (DO), D-LED-7.4 (DIN1), D-LED-8.6 (DIN2)
LED_D7: D-LED-7.3 (DO), D-LED-8.4 (DIN1), D-LED-9.6 (DIN2)
LED_D8: D-LED-8.3 (DO), D-LED-9.4 (DIN1), D-LED-10.6 (DIN2)
LED_D9: D-LED-9.3 (DO), D-LED-10.4 (DIN1), D-LED-11.6 (DIN2)
LED_D10: D-LED-10.3 (DO), D-LED-11.4 (DIN1), D-LED-12.6 (DIN2)
LED_D11: D-LED-11.3 (DO), D-LED-12.4 (DIN1), D-LED-13.6 (DIN2)
LED_D12: D-LED-12.3 (DO), D-LED-13.4 (DIN1)
LED_DI: D-LED-1.4 (DIN1), D-LED-2.6 (DIN2), R-LED-SER.2
PWR_GND: C-DECOUPLE-LED.2, C-LED-1.2, C-LED-2.2, C-LED-3.2, C-LED-4.2, C-LED-5.2, C-LED-6.2, C-LED-7.2, C-LED-8.2, C-LED-9.2, C-LED-10.2, C-LED-11.2, C-LED-12.2, C-LED-13.2, D-LED-1.5 (GND), D-LED-1.6 (DIN2), D-LED-2.5 (GND), D-LED-3.5 (GND), D-LED-4.5 (GND), D-LED-5.5 (GND), D-LED-6.5 (GND), D-LED-7.5 (GND), D-LED-8.5 (GND), D-LED-9.5 (GND), D-LED-10.5 (GND), D-LED-11.5 (GND), D-LED-12.5 (GND), D-LED-13.5 (GND), R-LED-PD.2, U-LVLSHIFT.1, U-LVLSHIFT.4, U-LVLSHIFT.5, U-LVLSHIFT.7 (GND), U-LVLSHIFT.9, U-LVLSHIFT.10, U-LVLSHIFT.12, U-LVLSHIFT.13
UMBILICAL_POS12: C-LED-1.1, C-LED-2.1, C-LED-3.1, C-LED-4.1, C-LED-5.1, C-LED-6.1, C-LED-7.1, C-LED-8.1, C-LED-9.1, C-LED-10.1, C-LED-11.1, C-LED-12.1, C-LED-13.1, D-LED-1.2 (VDD), D-LED-2.2 (VDD), D-LED-3.2 (VDD), D-LED-4.2 (VDD), D-LED-5.2 (VDD), D-LED-6.2 (VDD), D-LED-7.2 (VDD), D-LED-8.2 (VDD), D-LED-9.2 (VDD), D-LED-10.2 (VDD), D-LED-11.2 (VDD), D-LED-12.2 (VDD), D-LED-13.2 (VDD)

Notes on the sheet:
R-LED-PD holds the input low through the bootloader window: GPIO1 floats, OE is tied low, and a floating AHCT input would put clean 5 V edges into the LED row before firmware runs. Gates B-D are spare: inputs and enables tied low (an enabled CMOS gate never floats). THE LED ROW (ADR 0028): 13 x WS2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
