jeffmhopkins/Woody/hardware/carrier/power-entry-instrument/power-entry-instrument.kicad_sch

## KiCad design hardware/carrier/power-entry-instrument/power-entry-instrument.kicad_sch (2026-09-30)

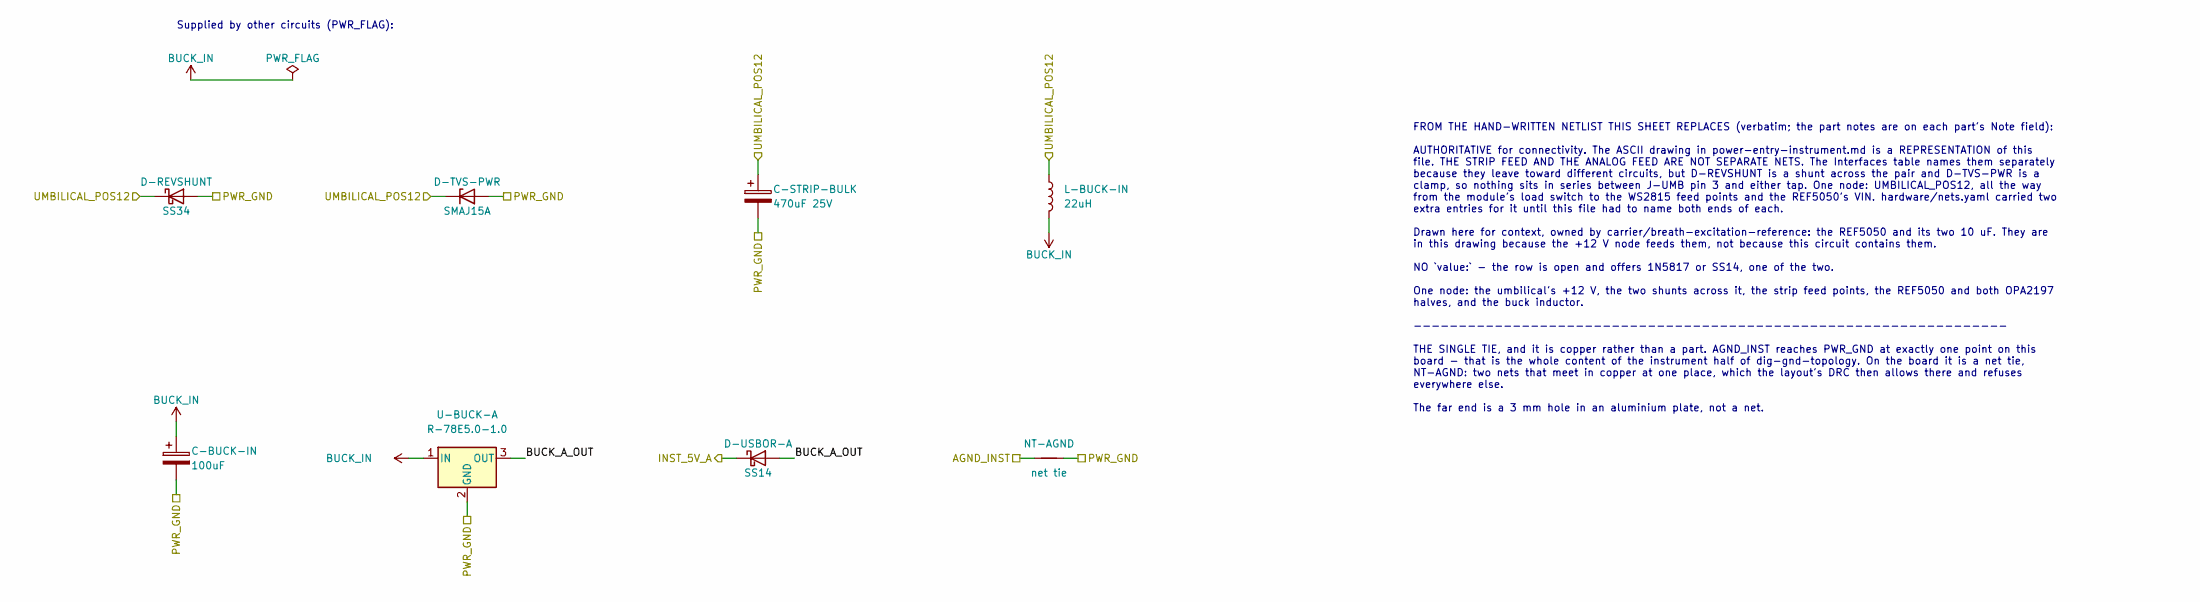
[picture p191: schematic power-entry-instrument.kicad_sch]

Parts:
C-BUCK-IN: 100uF; CP_Elec_6.3x5.8; MPN UCM1E101MCL1GS; LCSC C729678
C-STRIP-BULK: 470uF 25V; CP_Elec_10x10; MPN UCW1E471MNL1GS; LCSC C340751
D-REVSHUNT: SS34; D_SMC; MPN SS34-E3/57T; LCSC C13354
D-TVS-PWR: SMAJ15A; D_SMA; MPN SMAJ15A; LCSC C148216
D-USBOR-A: SS14; D_SMA; MPN SS14-E3/61T; LCSC C47460
L-BUCK-IN: 22uH; L_Sunlord_SWPA6028S; MPN SWPA6028S220MT; LCSC C51349
NT-AGND: net tie; NetTie-2_SMD_Pad0.5mm
U-BUCK-A: R-78E5.0-1.0; Converter_DCDC_RECOM_R-78E-0.5_THT; MPN R-78E5.0-1.0; LCSC C3033024

Connections:
AGND_INST: NT-AGND.1
BUCK_A_OUT: D-USBOR-A.2 (A), U-BUCK-A.3 (OUT)
BUCK_IN: C-BUCK-IN.1, L-BUCK-IN.2, U-BUCK-A.1 (IN)
INST_5V_A: D-USBOR-A.1 (K)
PWR_GND: C-BUCK-IN.2, C-STRIP-BULK.2, D-REVSHUNT.2 (A), D-TVS-PWR.2 (A), NT-AGND.2, U-BUCK-A.2 (GND)
UMBILICAL_POS12: C-STRIP-BULK.1, D-REVSHUNT.1 (K), D-TVS-PWR.1 (K), L-BUCK-IN.1

Notes on the sheet:
Supplied by other circuits (PWR_FLAG):
FROM THE HAND-WRITTEN NETLIST THIS SHEET REPLACES (verbatim; the part notes are on each part's Note field): AUTHORITATIVE for connectivity. The ASCII drawing in power-entry-instrument.md is a REPRESENTATION of this file. THE STRIP FEED AND THE ANALOG FEED ARE NOT SEPARATE NETS. The Interfaces table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
