jeffmhopkins/Woody/hardware/cluster/key-register/key-register.kicad_sch

## KiCad design hardware/cluster/key-register/key-register.kicad_sch (2026-09-30)

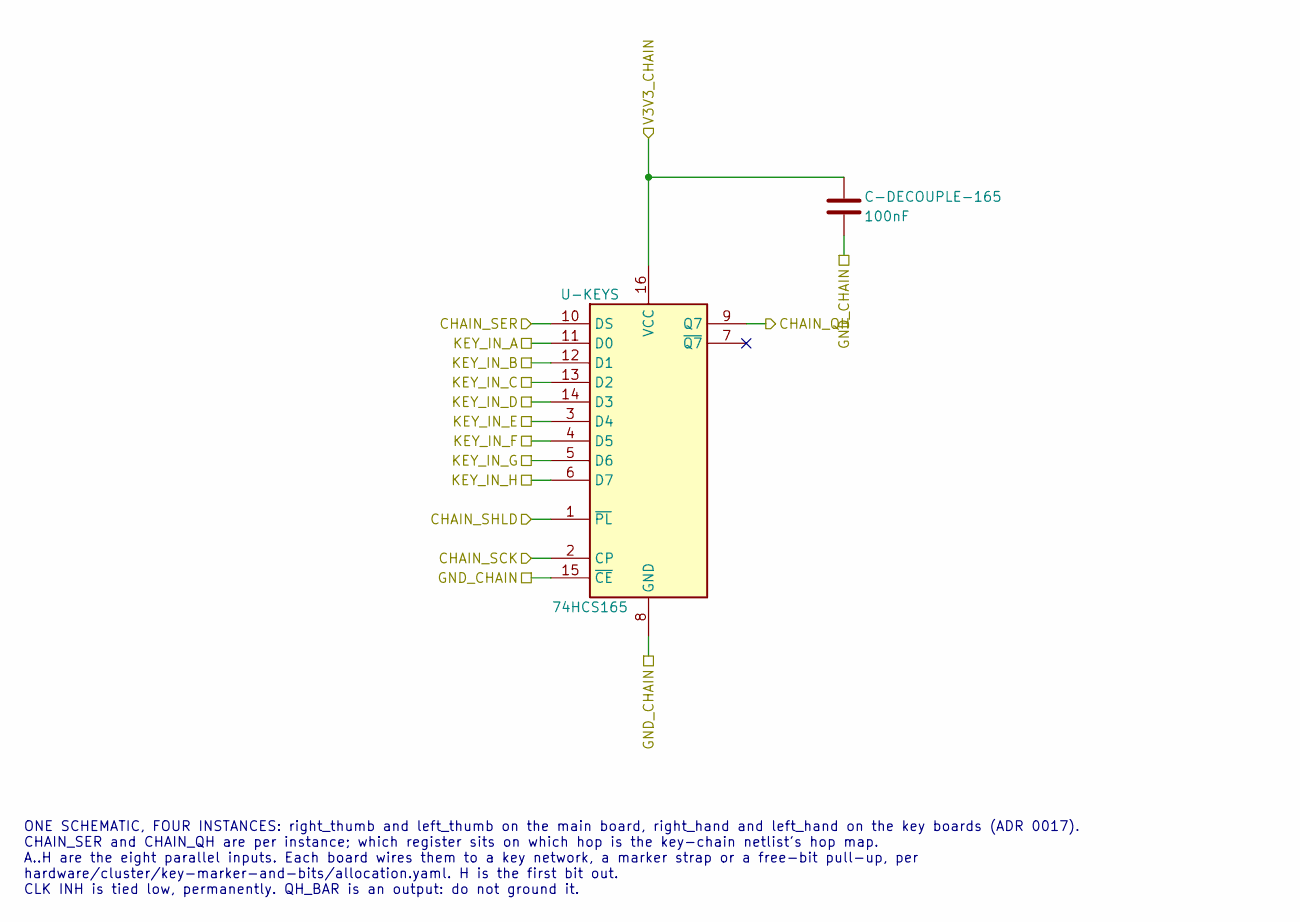
[picture p192: schematic key-register.kicad_sch]

Parts:
C-DECOUPLE-165: 100nF; C_0805_2012Metric; MPN CC0805KRX7R9BB104; LCSC C49678
U-KEYS: 74HCS165; SOIC-16_3.9x9.9mm_P1.27mm; MPN SN74HCS165DR; LCSC C2864745

Connections:
CHAIN_QH: U-KEYS.9 (Q7)
CHAIN_SCK: U-KEYS.2 (CP)
CHAIN_SER: U-KEYS.10 (DS)
CHAIN_SHLD: U-KEYS.1 (~PL)
GND_CHAIN: C-DECOUPLE-165.2, U-KEYS.8 (GND), U-KEYS.15 (~CE)
KEY_IN_A: U-KEYS.11 (D0)
KEY_IN_B: U-KEYS.12 (D1)
KEY_IN_C: U-KEYS.13 (D2)
KEY_IN_D: U-KEYS.14 (D3)
KEY_IN_E: U-KEYS.3 (D4)
KEY_IN_F: U-KEYS.4 (D5)
KEY_IN_G: U-KEYS.5 (D6)
KEY_IN_H: U-KEYS.6 (D7)
V3V3_CHAIN: C-DECOUPLE-165.1, U-KEYS.16 (VCC)

Notes on the sheet:
ONE SCHEMATIC, FOUR INSTANCES: right_thumb and left_thumb on the main board, right_hand and left_hand on the key boards (ADR 0017). CHAIN_SER and CHAIN_QH are per instance; which register sits on which hop is the key-chain netlist's hop map. A..H are the eight parallel inputs. Each board wires them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
