jeffmhopkins/Woody/hardware/cluster/key-switch-network/key-switch-network.kicad_sch

## KiCad design hardware/cluster/key-switch-network/key-switch-network.kicad_sch (2026-09-30)

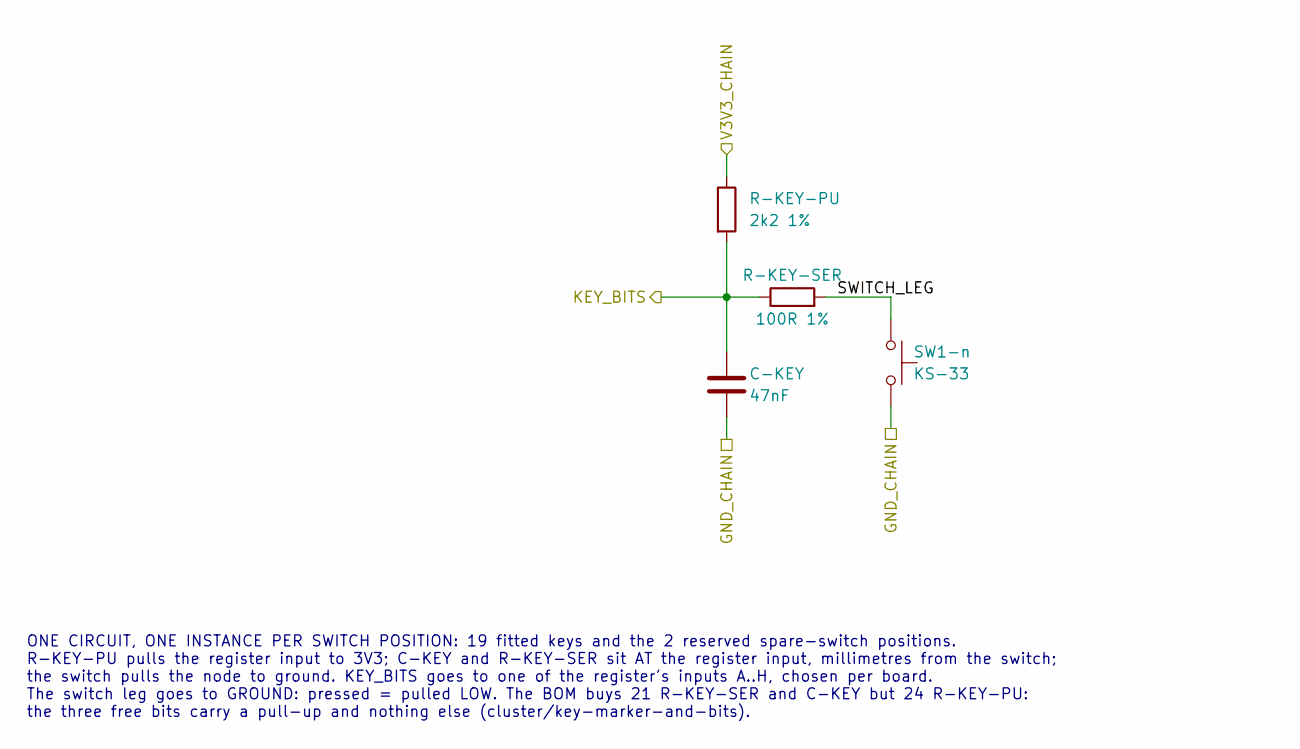
[picture p193: schematic key-switch-network.kicad_sch]

Parts:
C-KEY: 47nF; C_0805_2012Metric; MPN CL21B473KBCNNNC; LCSC C53134
R-KEY-PU: 2k2 1%; R_0805_2012Metric; MPN 0805W8F2201T5E; LCSC C17520
R-KEY-SER: 100R 1%; R_0805_2012Metric; MPN 0805W8F1000T5E; LCSC C17408
SW1-n: KS-33; SW_Gateron_KS33_1u; MPN KS-33H10B050NN-Y24

Connections:
GND_CHAIN: C-KEY.2, SW1-n.2
KEY_BITS: C-KEY.1, R-KEY-PU.2, R-KEY-SER.1
SWITCH_LEG: R-KEY-SER.2, SW1-n.1
V3V3_CHAIN: R-KEY-PU.1

Notes on the sheet:
ONE CIRCUIT, ONE INSTANCE PER SWITCH POSITION: 19 fitted keys and the 2 reserved spare-switch positions. R-KEY-PU pulls the register input to 3V3; C-KEY and R-KEY-SER sit AT the register input, millimetres from the switch; the switch pulls the node to ground. KEY_BITS goes to one of the register's 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
