jeffmhopkins/Woody/hardware/interfaces/breath-sense-link/breath-sense-link.kicad_sch

## KiCad design hardware/interfaces/breath-sense-link/breath-sense-link.kicad_sch (2026-09-30)

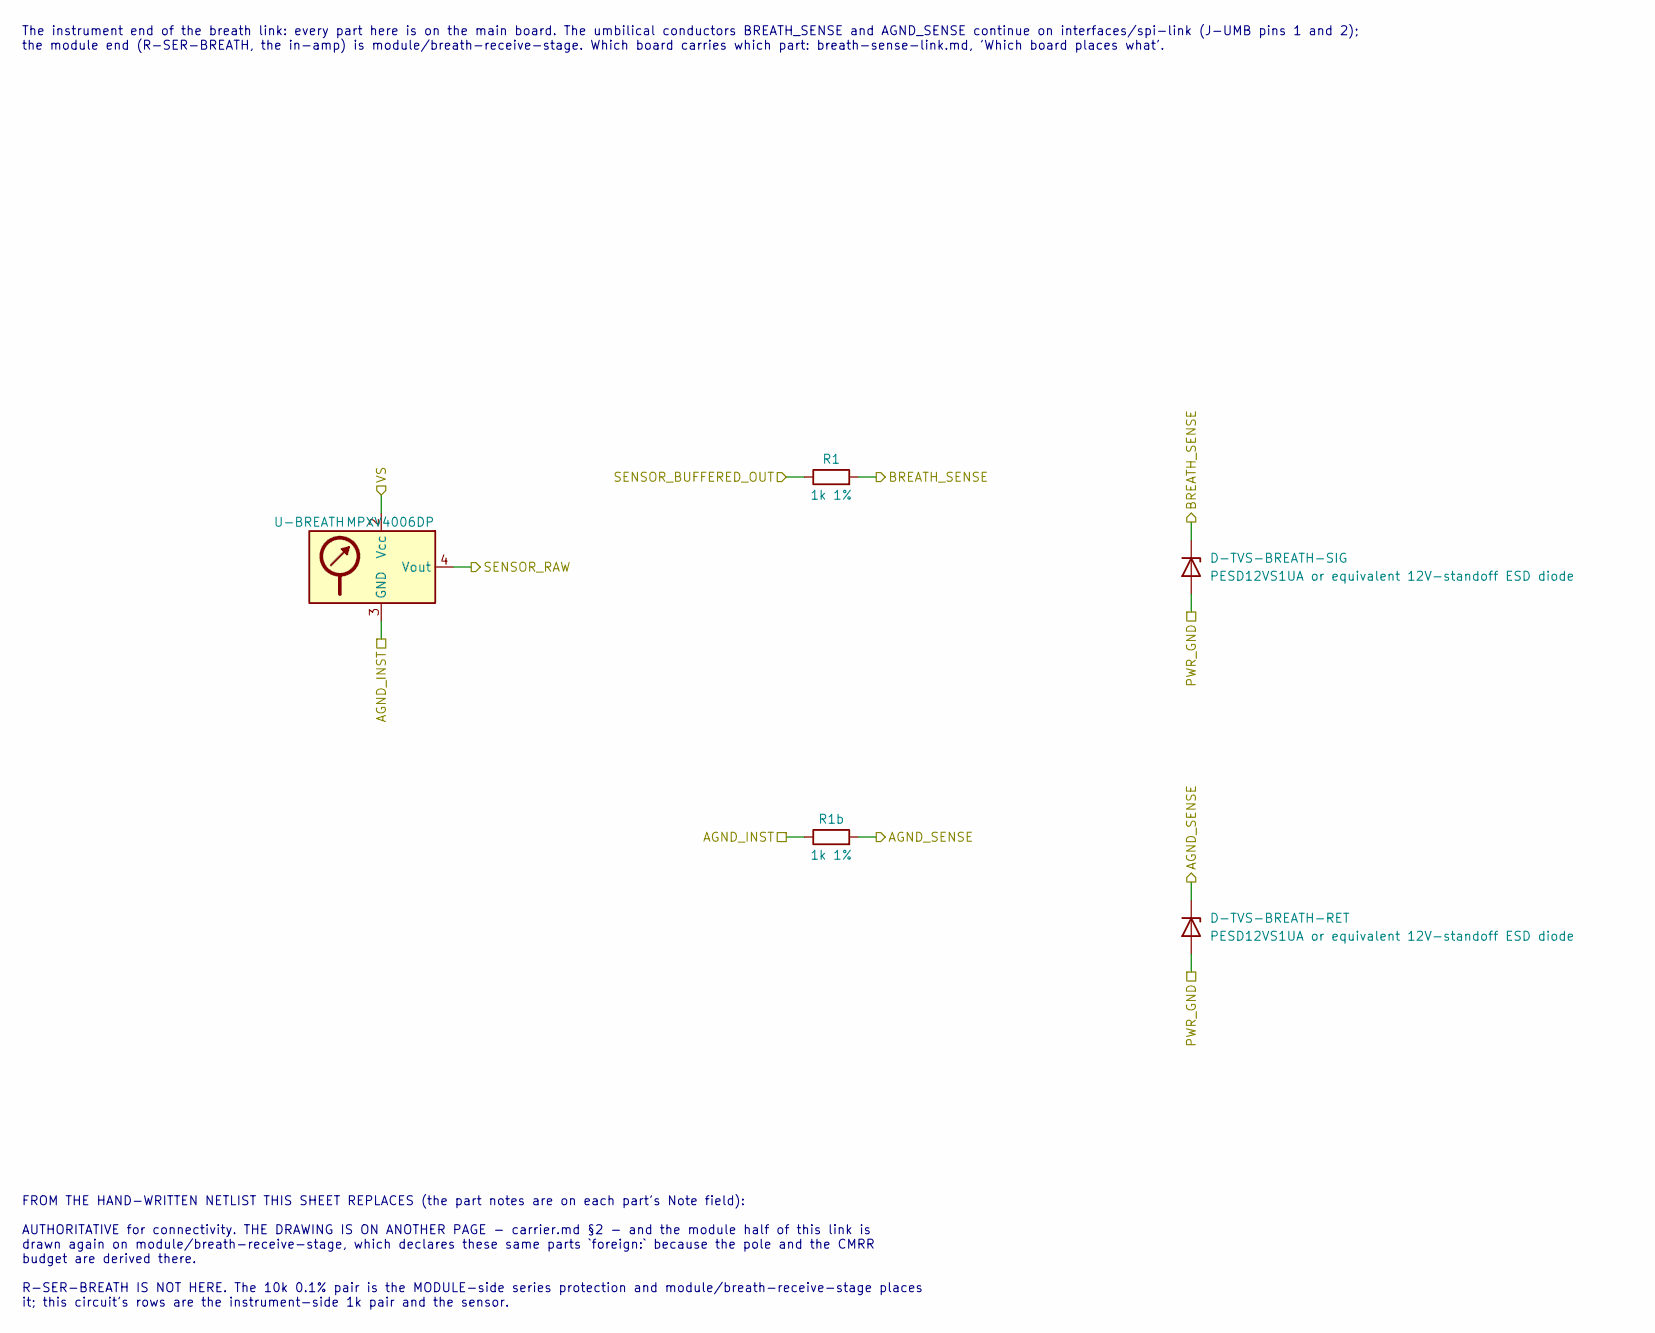
[picture p194: schematic breath-sense-link.kicad_sch]

Parts:
D-TVS-BREATH-RET: PESD12VS1UA or equivalent 12V-standoff ESD diode; D_SOD-323; MPN PESD12VS1UA,115; LCSC C131084
D-TVS-BREATH-SIG: PESD12VS1UA or equivalent 12V-standoff ESD diode; D_SOD-323; MPN PESD12VS1UA,115; LCSC C131084
R1, R1b: 1k 1%; R_1206_3216Metric; MPN 1206W4F1001T5E; LCSC C4410
U-BREATH: MPXV4006DP; NXP_Case1351-01_SOP-8_P2.54mm; MPN MPXV4006DP; LCSC C5190605

Connections:
AGND_INST: R1b.1, U-BREATH.3 (GND)
AGND_SENSE: D-TVS-BREATH-RET.1 (K), R1b.2
BREATH_SENSE: D-TVS-BREATH-SIG.1 (K), R1.2
PWR_GND: D-TVS-BREATH-RET.2 (A), D-TVS-BREATH-SIG.2 (A)
SENSOR_BUFFERED_OUT: R1.1
SENSOR_RAW: U-BREATH.4 (Vout)
VS: U-BREATH.2 (Vcc)

Notes on the sheet:
The instrument end of the breath link: every part here is on the main board. The umbilical conductors BREATH_SENSE and AGND_SENSE continue on interfaces/spi-link (J-UMB pins 1 and 2); the module end (R-SER-BREATH, the in-amp) is module/breath-receive-stage. Which board carries which part: breath-se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
FROM THE HAND-WRITTEN NETLIST THIS SHEET REPLACES (the part notes are on each part's Note field): AUTHORITATIVE for connectivity. THE DRAWING IS ON ANOTHER PAGE - carrier.md §2 - and the module half of this link is drawn again on module/breath-receive-stage, which declares these same parts `foreign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
