jeffmhopkins/Woody/hardware/interfaces/key-chain-loom/key-chain-loom.kicad_sch

## KiCad design hardware/interfaces/key-chain-loom/key-chain-loom.kicad_sch (2026-09-30)

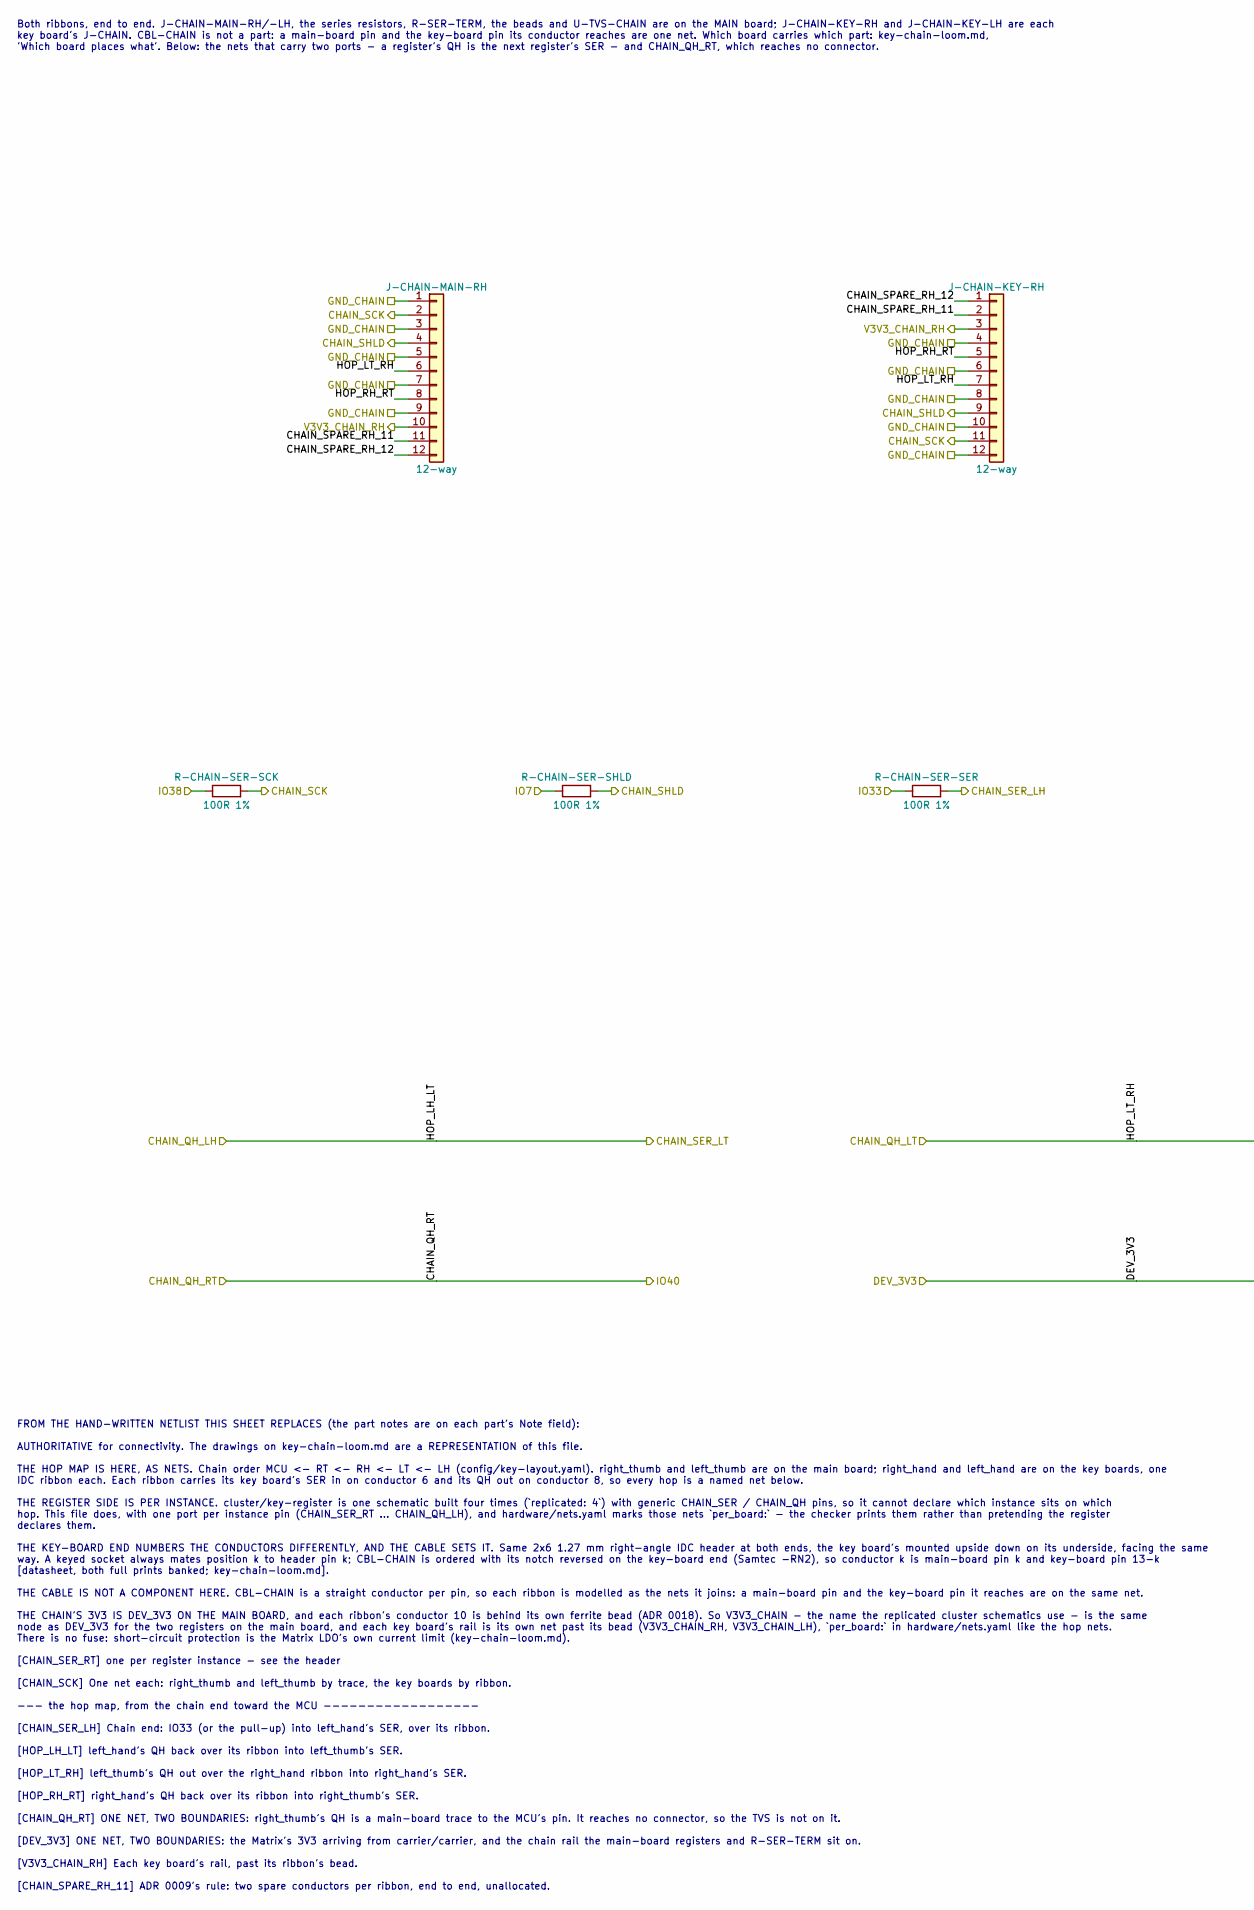
[picture p195: schematic key-chain-loom.kicad_sch, part in row 1, column 1]

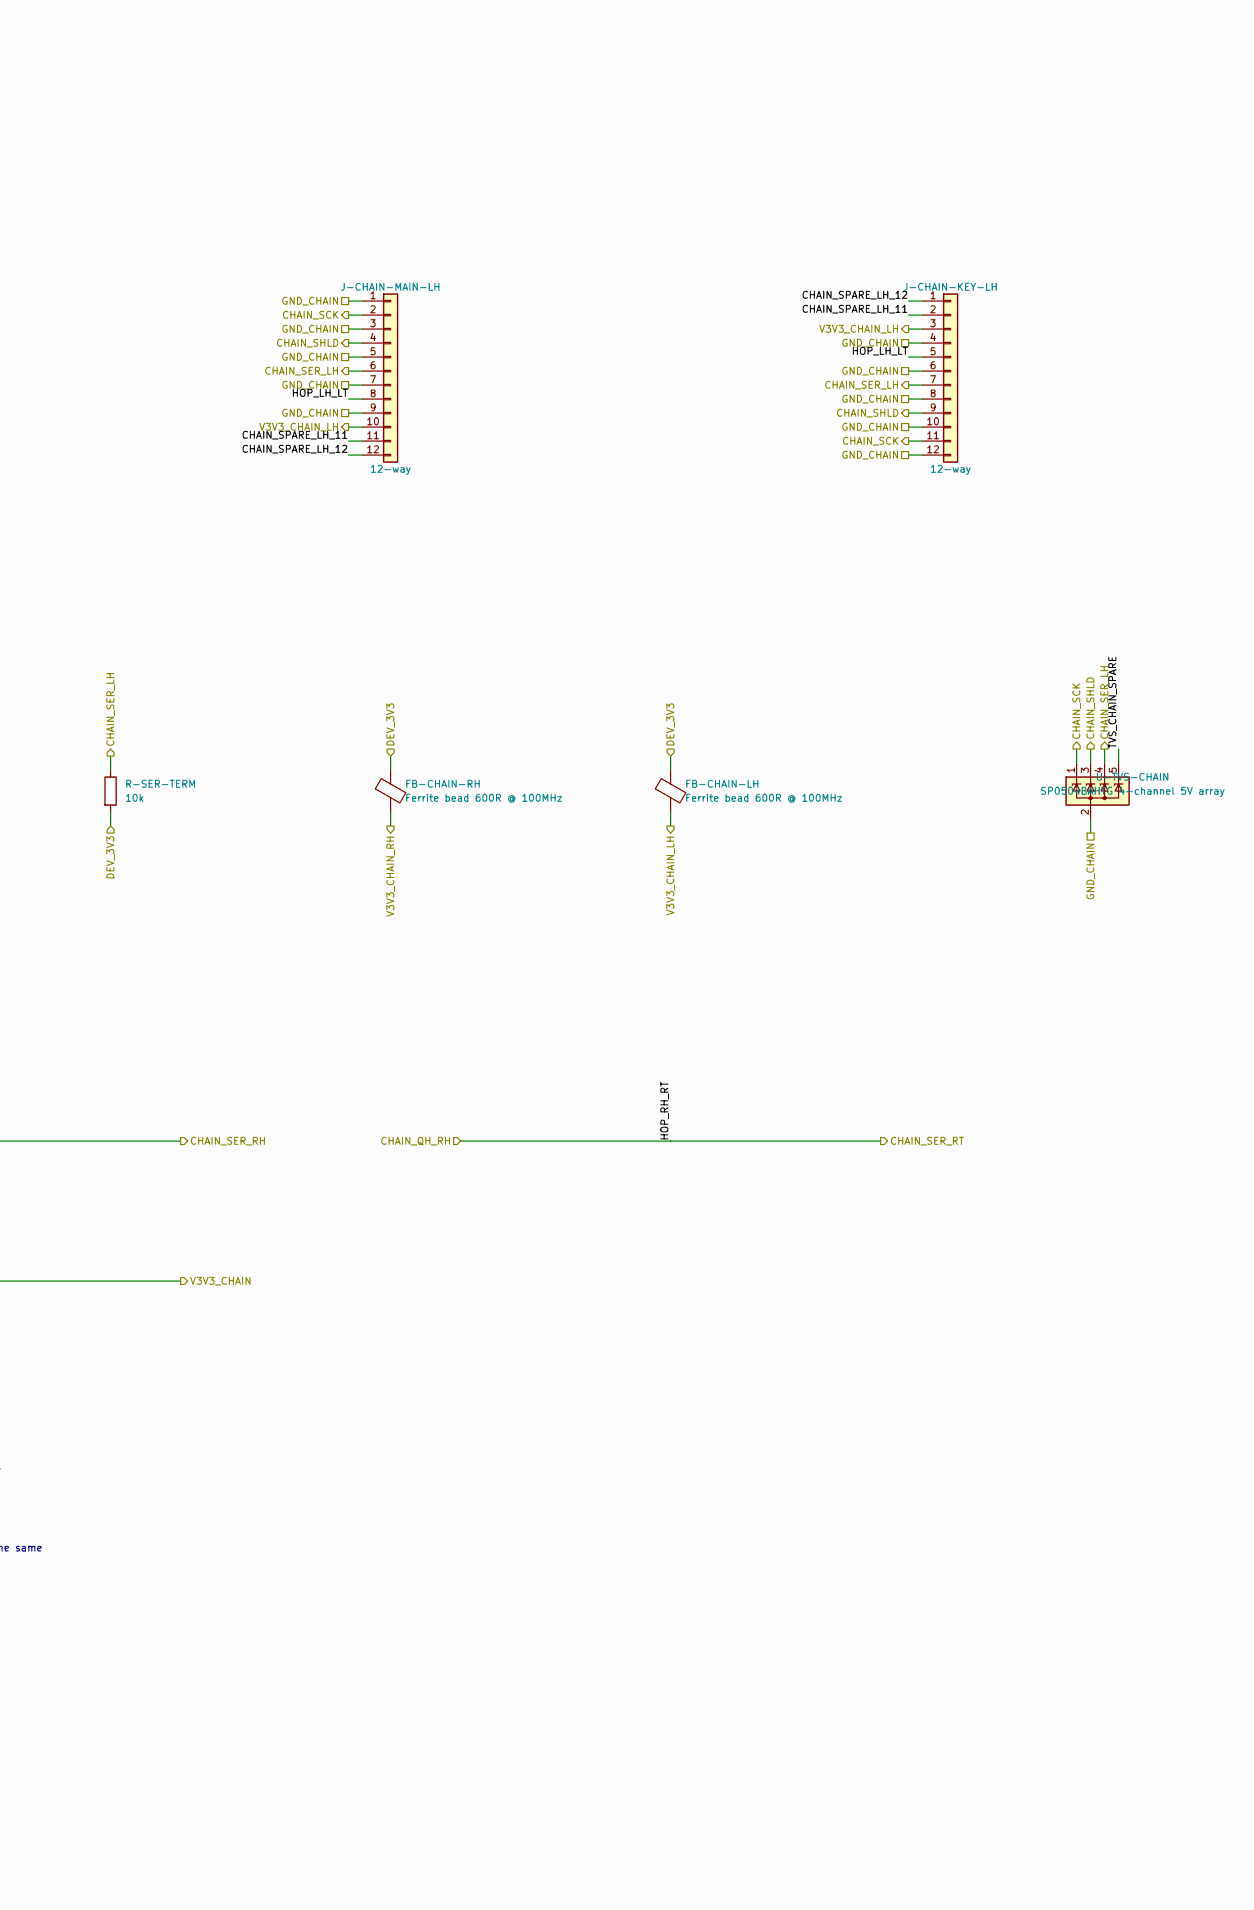
[picture p196: schematic key-chain-loom.kicad_sch, part in row 1, column 2]

Parts:
FB-CHAIN-LH: Ferrite bead 600R @ 100MHz; L_0805_2012Metric; MPN BLM21SP601SN1D; LCSC C3716677
FB-CHAIN-RH: Ferrite bead 600R @ 100MHz; L_0805_2012Metric; MPN BLM21SP601SN1D; LCSC C3716677
J-CHAIN-KEY-LH: 12-way; IDC-Header_2x06_P1.27mm_Samtec_SHF_Horizontal; MPN SHF-106-01-L-D-RA
J-CHAIN-KEY-RH: 12-way; IDC-Header_2x06_P1.27mm_Samtec_SHF_Horizontal; MPN SHF-106-01-L-D-RA
J-CHAIN-MAIN-LH: 12-way; IDC-Header_2x06_P1.27mm_Samtec_SHF_Horizontal; MPN SHF-106-01-L-D-RA
J-CHAIN-MAIN-RH: 12-way; IDC-Header_2x06_P1.27mm_Samtec_SHF_Horizontal; MPN SHF-106-01-L-D-RA
R-CHAIN-SER-SCK: 100R 1%; R_1206_3216Metric; MPN 1206W4F1000T5E; LCSC C17901
R-CHAIN-SER-SER: 100R 1%; R_1206_3216Metric; MPN 1206W4F1000T5E; LCSC C17901
R-CHAIN-SER-SHLD: 100R 1%; R_1206_3216Metric; MPN 1206W4F1000T5E; LCSC C17901
R-SER-TERM: 10k; R_0805_2012Metric; MPN 0805W8F1002T5E; LCSC C17414
U-TVS-CHAIN: SP0504BAHTG 4-channel 5V array; SOT-23-5; MPN SP0504BAHTG; LCSC C10675

Connections:
CHAIN_QH_LH: J-CHAIN-KEY-LH.5, J-CHAIN-MAIN-LH.8
CHAIN_QH_LT: J-CHAIN-KEY-RH.7, J-CHAIN-MAIN-RH.6
CHAIN_QH_RH: J-CHAIN-KEY-RH.5, J-CHAIN-MAIN-RH.8
CHAIN_SCK: J-CHAIN-KEY-LH.11, J-CHAIN-KEY-RH.11, J-CHAIN-MAIN-LH.2, J-CHAIN-MAIN-RH.2, R-CHAIN-SER-SCK.2, U-TVS-CHAIN.1 (K)
CHAIN_SER_LH: J-CHAIN-KEY-LH.7, J-CHAIN-MAIN-LH.6, R-CHAIN-SER-SER.2, R-SER-TERM.1, U-TVS-CHAIN.4 (K)
CHAIN_SHLD: J-CHAIN-KEY-LH.9, J-CHAIN-KEY-RH.9, J-CHAIN-MAIN-LH.4, J-CHAIN-MAIN-RH.4, R-CHAIN-SER-SHLD.2, U-TVS-CHAIN.3 (K)
CHAIN_SPARE_LH_11: J-CHAIN-KEY-LH.2, J-CHAIN-MAIN-LH.11
CHAIN_SPARE_LH_12: J-CHAIN-KEY-LH.1, J-CHAIN-MAIN-LH.12
CHAIN_SPARE_RH_11: J-CHAIN-KEY-RH.2, J-CHAIN-MAIN-RH.11
CHAIN_SPARE_RH_12: J-CHAIN-KEY-RH.1, J-CHAIN-MAIN-RH.12
DEV_3V3: FB-CHAIN-LH.1, FB-CHAIN-RH.1, R-SER-TERM.2
GND_CHAIN: J-CHAIN-KEY-LH.4, J-CHAIN-KEY-LH.6, J-CHAIN-KEY-LH.8, J-CHAIN-KEY-LH.10, J-CHAIN-KEY-LH.12, J-CHAIN-KEY-RH.4, J-CHAIN-KEY-RH.6, J-CHAIN-KEY-RH.8, J-CHAIN-KEY-RH.10, J-CHAIN-KEY-RH.12, J-CHAIN-MAIN-LH.1, J-CHAIN-MAIN-LH.3, J-CHAIN-MAIN-LH.5, J-CHAIN-MAIN-LH.7, J-CHAIN-MAIN-LH.9, J-CHAIN-MAIN-RH.1, J-CHAIN-MAIN-RH.3, J-CHAIN-MAIN-RH.5, J-CHAIN-MAIN-RH.7, J-CHAIN-MAIN-RH.9, U-TVS-CHAIN.2 (A)
IO7: R-CHAIN-SER-SHLD.1
IO33: R-CHAIN-SER-SER.1
IO38: R-CHAIN-SER-SCK.1
TVS_CHAIN_SPARE: U-TVS-CHAIN.5 (K)
V3V3_CHAIN_LH: FB-CHAIN-LH.2, J-CHAIN-KEY-LH.3, J-CHAIN-MAIN-LH.10
V3V3_CHAIN_RH: FB-CHAIN-RH.2, J-CHAIN-KEY-RH.3, J-CHAIN-MAIN-RH.10

Notes on the sheet:
Both ribbons, end to end. J-CHAIN-MAIN-RH/-LH, the series resistors, R-SER-TERM, the beads and U-TVS-CHAIN are on the MAIN board; J-CHAIN-KEY-RH and J-CHAIN-KEY-LH are each key board's J-CHAIN. CBL-CHAIN is not a part: a main-board pin and the key-board pin its conductor reaches are one net. Which 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
FROM THE HAND-WRITTEN NETLIST THIS SHEET REPLACES (the part notes are on each part's Note field): AUTHORITATIVE for connectivity. The drawings on key-chain-loom.md are a REPRESENTATION of this file. THE HOP MAP IS HERE, AS NETS. Chain order MCU <- RT <- RH <- LT <- LH (config/key-layout.yaml). righ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
