jeffmhopkins/Woody/hardware/interfaces/spi-link/spi-link.kicad_sch

## KiCad design hardware/interfaces/spi-link/spi-link.kicad_sch (2026-09-30)

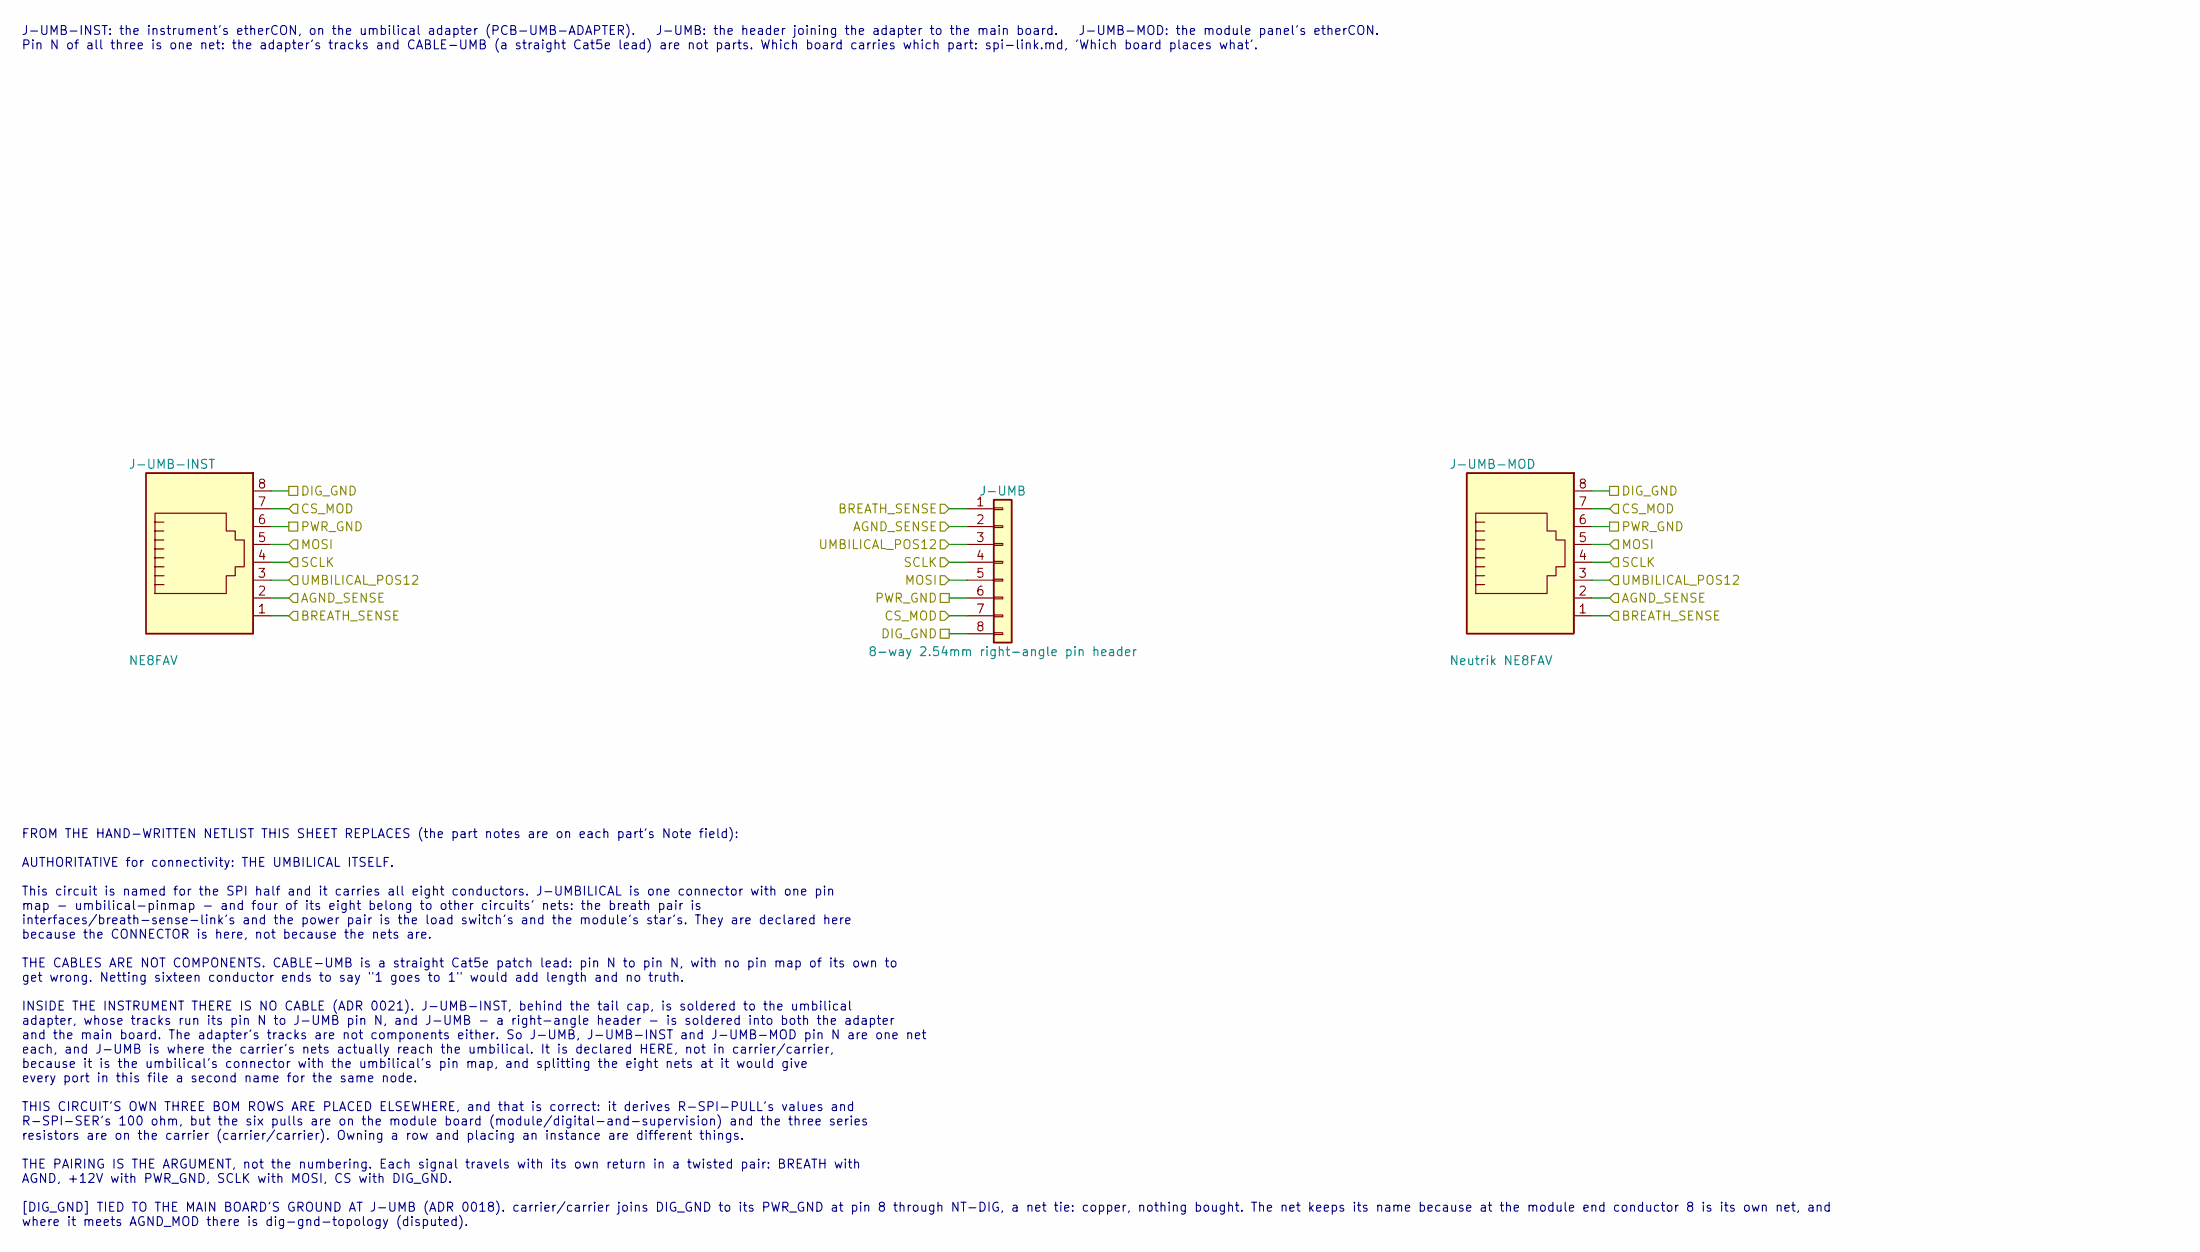
[picture p197: schematic spi-link.kicad_sch]

Parts:
J-UMB: 8-way 2.54mm right-angle pin header; PinHeader_1x08_P2.54mm_Horizontal; MPN HX PZ2.54-1x8P WZ; LCSC C32713267
J-UMB-INST: NE8FAV; Neutrik_NE8FAV_etherCON_Vertical; MPN NE8FAV
J-UMB-MOD: Neutrik NE8FAV; Neutrik_NE8FAV_etherCON_Vertical; MPN NE8FAV

Connections:
AGND_SENSE: J-UMB.2, J-UMB-INST.2, J-UMB-MOD.2
BREATH_SENSE: J-UMB.1, J-UMB-INST.1, J-UMB-MOD.1
CS_MOD: J-UMB.7, J-UMB-INST.7, J-UMB-MOD.7
DIG_GND: J-UMB.8, J-UMB-INST.8, J-UMB-MOD.8
MOSI: J-UMB.5, J-UMB-INST.5, J-UMB-MOD.5
PWR_GND: J-UMB.6, J-UMB-INST.6, J-UMB-MOD.6
SCLK: J-UMB.4, J-UMB-INST.4, J-UMB-MOD.4
UMBILICAL_POS12: J-UMB.3, J-UMB-INST.3, J-UMB-MOD.3

Notes on the sheet:
J-UMB-INST: the instrument's etherCON, on the umbilical adapter (PCB-UMB-ADAPTER). J-UMB: the header joining the adapter to the main board. J-UMB-MOD: the module panel's etherCON. Pin N of all three is one net: the adapter's tracks and CABLE-UMB (a straight Cat5e lead) are not parts. Which board ca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
FROM THE HAND-WRITTEN NETLIST THIS SHEET REPLACES (the part notes are on each part's Note field): AUTHORITATIVE for connectivity: THE UMBILICAL ITSELF. This circuit is named for the SPI half and it carries all eight conductors. J-UMBILICAL is one connector with one pin map - umbilical-pinmap - and 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
