jeffmhopkins/Woody/hardware/module/breath-output-stage/breath-output-stage.jack.kicad_sch

## KiCad design hardware/module/breath-output-stage/breath-output-stage.jack.kicad_sch (2026-09-30)

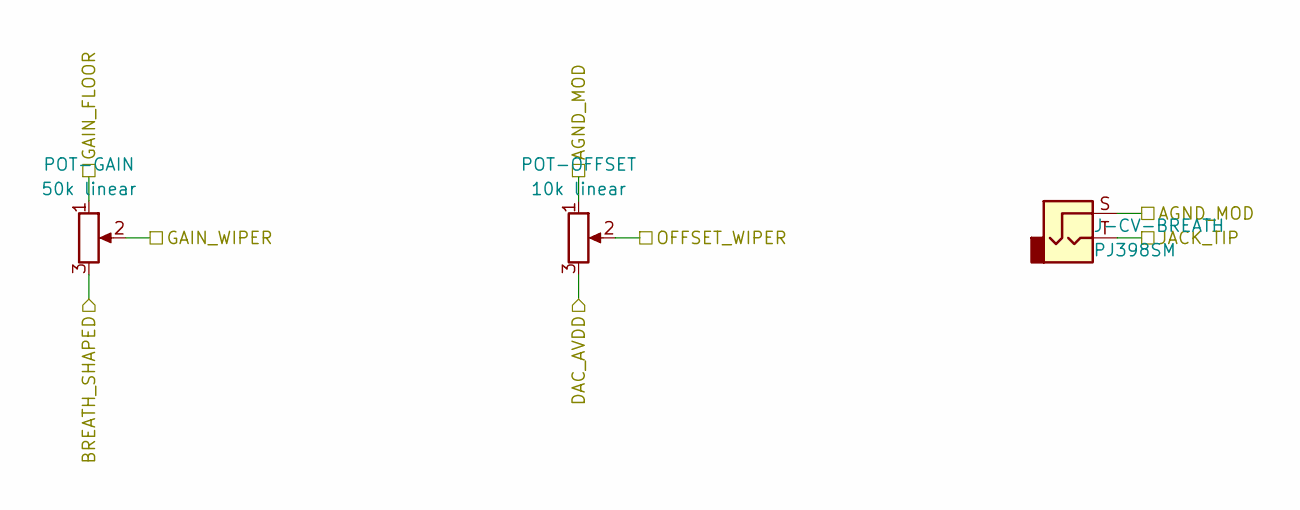
[picture p198: schematic breath-output-stage.jack.kicad_sch]

Parts:
J-CV-BREATH: PJ398SM; Jack_3.5mm_QingPu_WQP-PJ398SM_Vertical_CircularHoles; MPN PJ398SM
POT-GAIN: 50k linear; Potentiometer_SongHuei_R0904N_Single_Vertical; MPN R0904N-B50K L-25 KC
POT-OFFSET: 10k linear; Potentiometer_SongHuei_R0904N_Single_Vertical; MPN R0904N-B10K L-25 KC

Connections:
AGND_MOD: J-CV-BREATH.S, POT-OFFSET.1
BREATH_SHAPED: POT-GAIN.3
DAC_AVDD: POT-OFFSET.3
GAIN_FLOOR: POT-GAIN.1
GAIN_WIPER: POT-GAIN.2
JACK_TIP: J-CV-BREATH.T
OFFSET_WIPER: POT-OFFSET.2
