jeffmhopkins/Woody/hardware/module/breath-output-stage/breath-output-stage.main.kicad_sch

## KiCad design hardware/module/breath-output-stage/breath-output-stage.main.kicad_sch (2026-09-30)

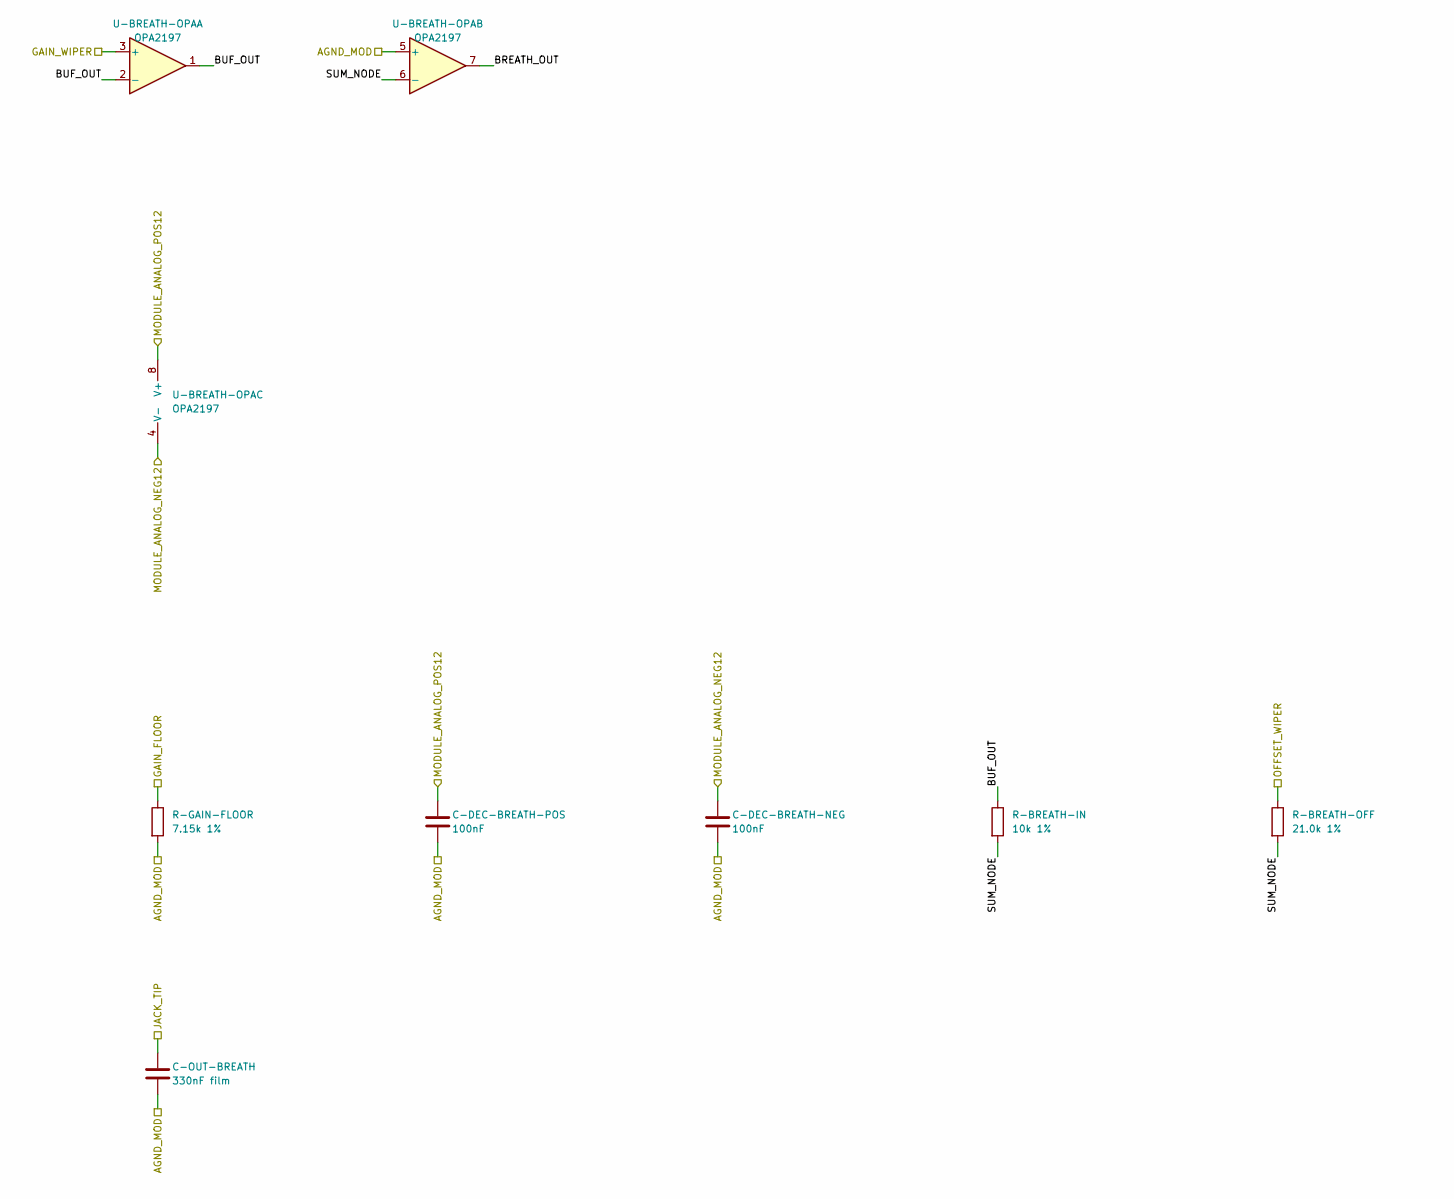
[picture p199: schematic breath-output-stage.main.kicad_sch, part in row 1, column 1]

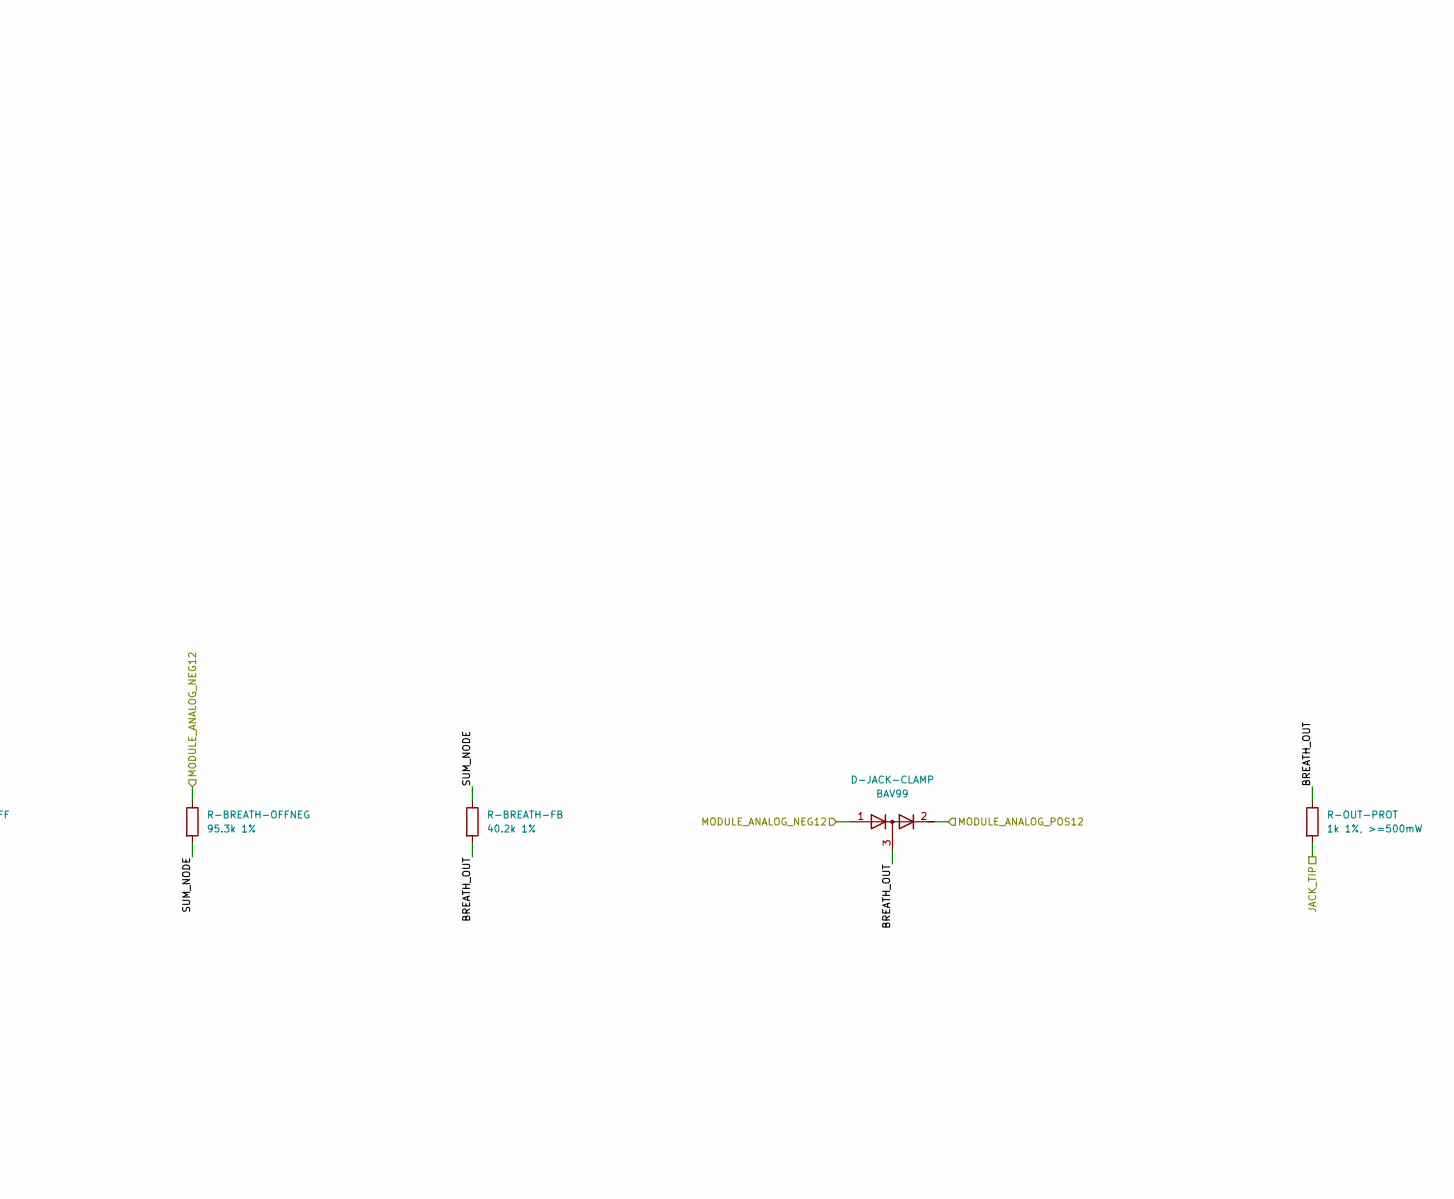
[picture p200: schematic breath-output-stage.main.kicad_sch, part in row 1, column 2]

Parts:
C-DEC-BREATH-NEG: 100nF; C_0805_2012Metric; MPN CC0805KRX7R9BB104; LCSC C49678
C-DEC-BREATH-POS: 100nF; C_0805_2012Metric; MPN CC0805KRX7R9BB104; LCSC C49678
C-OUT-BREATH: 330nF film; C_1206_3216Metric; MPN 50MU334MA23216; LCSC C3774076
D-JACK-CLAMP: BAV99; SOT-23; MPN BAV99,215; LCSC C2500
R-BREATH-FB: 40.2k 1%; R_0805_2012Metric; MPN 0805W8F4022T5E; LCSC C17678
R-BREATH-IN: 10k 1%; R_0805_2012Metric; MPN 0805W8F1002T5E; LCSC C17414
R-BREATH-OFF: 21.0k 1%; R_0805_2012Metric; MPN 0805W8F2102T5E; LCSC C17550
R-BREATH-OFFNEG: 95.3k 1%; R_0805_2012Metric; MPN 0805W8F9532T5E; LCSC C17873
R-GAIN-FLOOR: 7.15k 1%; R_0805_2012Metric; MPN 0805W8F7151T5E; LCSC C17806
R-OUT-PROT: 1k 1%, >=500mW; R_1206_3216Metric; MPN ERJ-P08F1001V; LCSC C4261071
U-BREATH-OPA: OPA2197; SOIC-8_3.9x4.9mm_P1.27mm; MPN OPA2197IDR; LCSC C139363

Connections:
AGND_MOD: C-DEC-BREATH-NEG.2, C-DEC-BREATH-POS.2, C-OUT-BREATH.2, R-GAIN-FLOOR.2, U-BREATH-OPA.5 (+)
BREATH_OUT: D-JACK-CLAMP.3 (common), R-BREATH-FB.2, R-OUT-PROT.1, U-BREATH-OPA.7
BUF_OUT: R-BREATH-IN.1, U-BREATH-OPA.1, U-BREATH-OPA.2 (-)
GAIN_FLOOR: R-GAIN-FLOOR.1
GAIN_WIPER: U-BREATH-OPA.3 (+)
JACK_TIP: C-OUT-BREATH.1, R-OUT-PROT.2
MODULE_ANALOG_NEG12: C-DEC-BREATH-NEG.1, D-JACK-CLAMP.1 (A), R-BREATH-OFFNEG.1, U-BREATH-OPA.4 (V-)
MODULE_ANALOG_POS12: C-DEC-BREATH-POS.1, D-JACK-CLAMP.2 (K), U-BREATH-OPA.8 (V+)
OFFSET_WIPER: R-BREATH-OFF.1
SUM_NODE: R-BREATH-FB.1, R-BREATH-IN.2, R-BREATH-OFF.2, R-BREATH-OFFNEG.2, U-BREATH-OPA.6 (-)
