jeffmhopkins/Woody/hardware/module/breath-receive-stage/breath-receive-stage.kicad_sch

## KiCad design hardware/module/breath-receive-stage/breath-receive-stage.kicad_sch (2026-09-30)

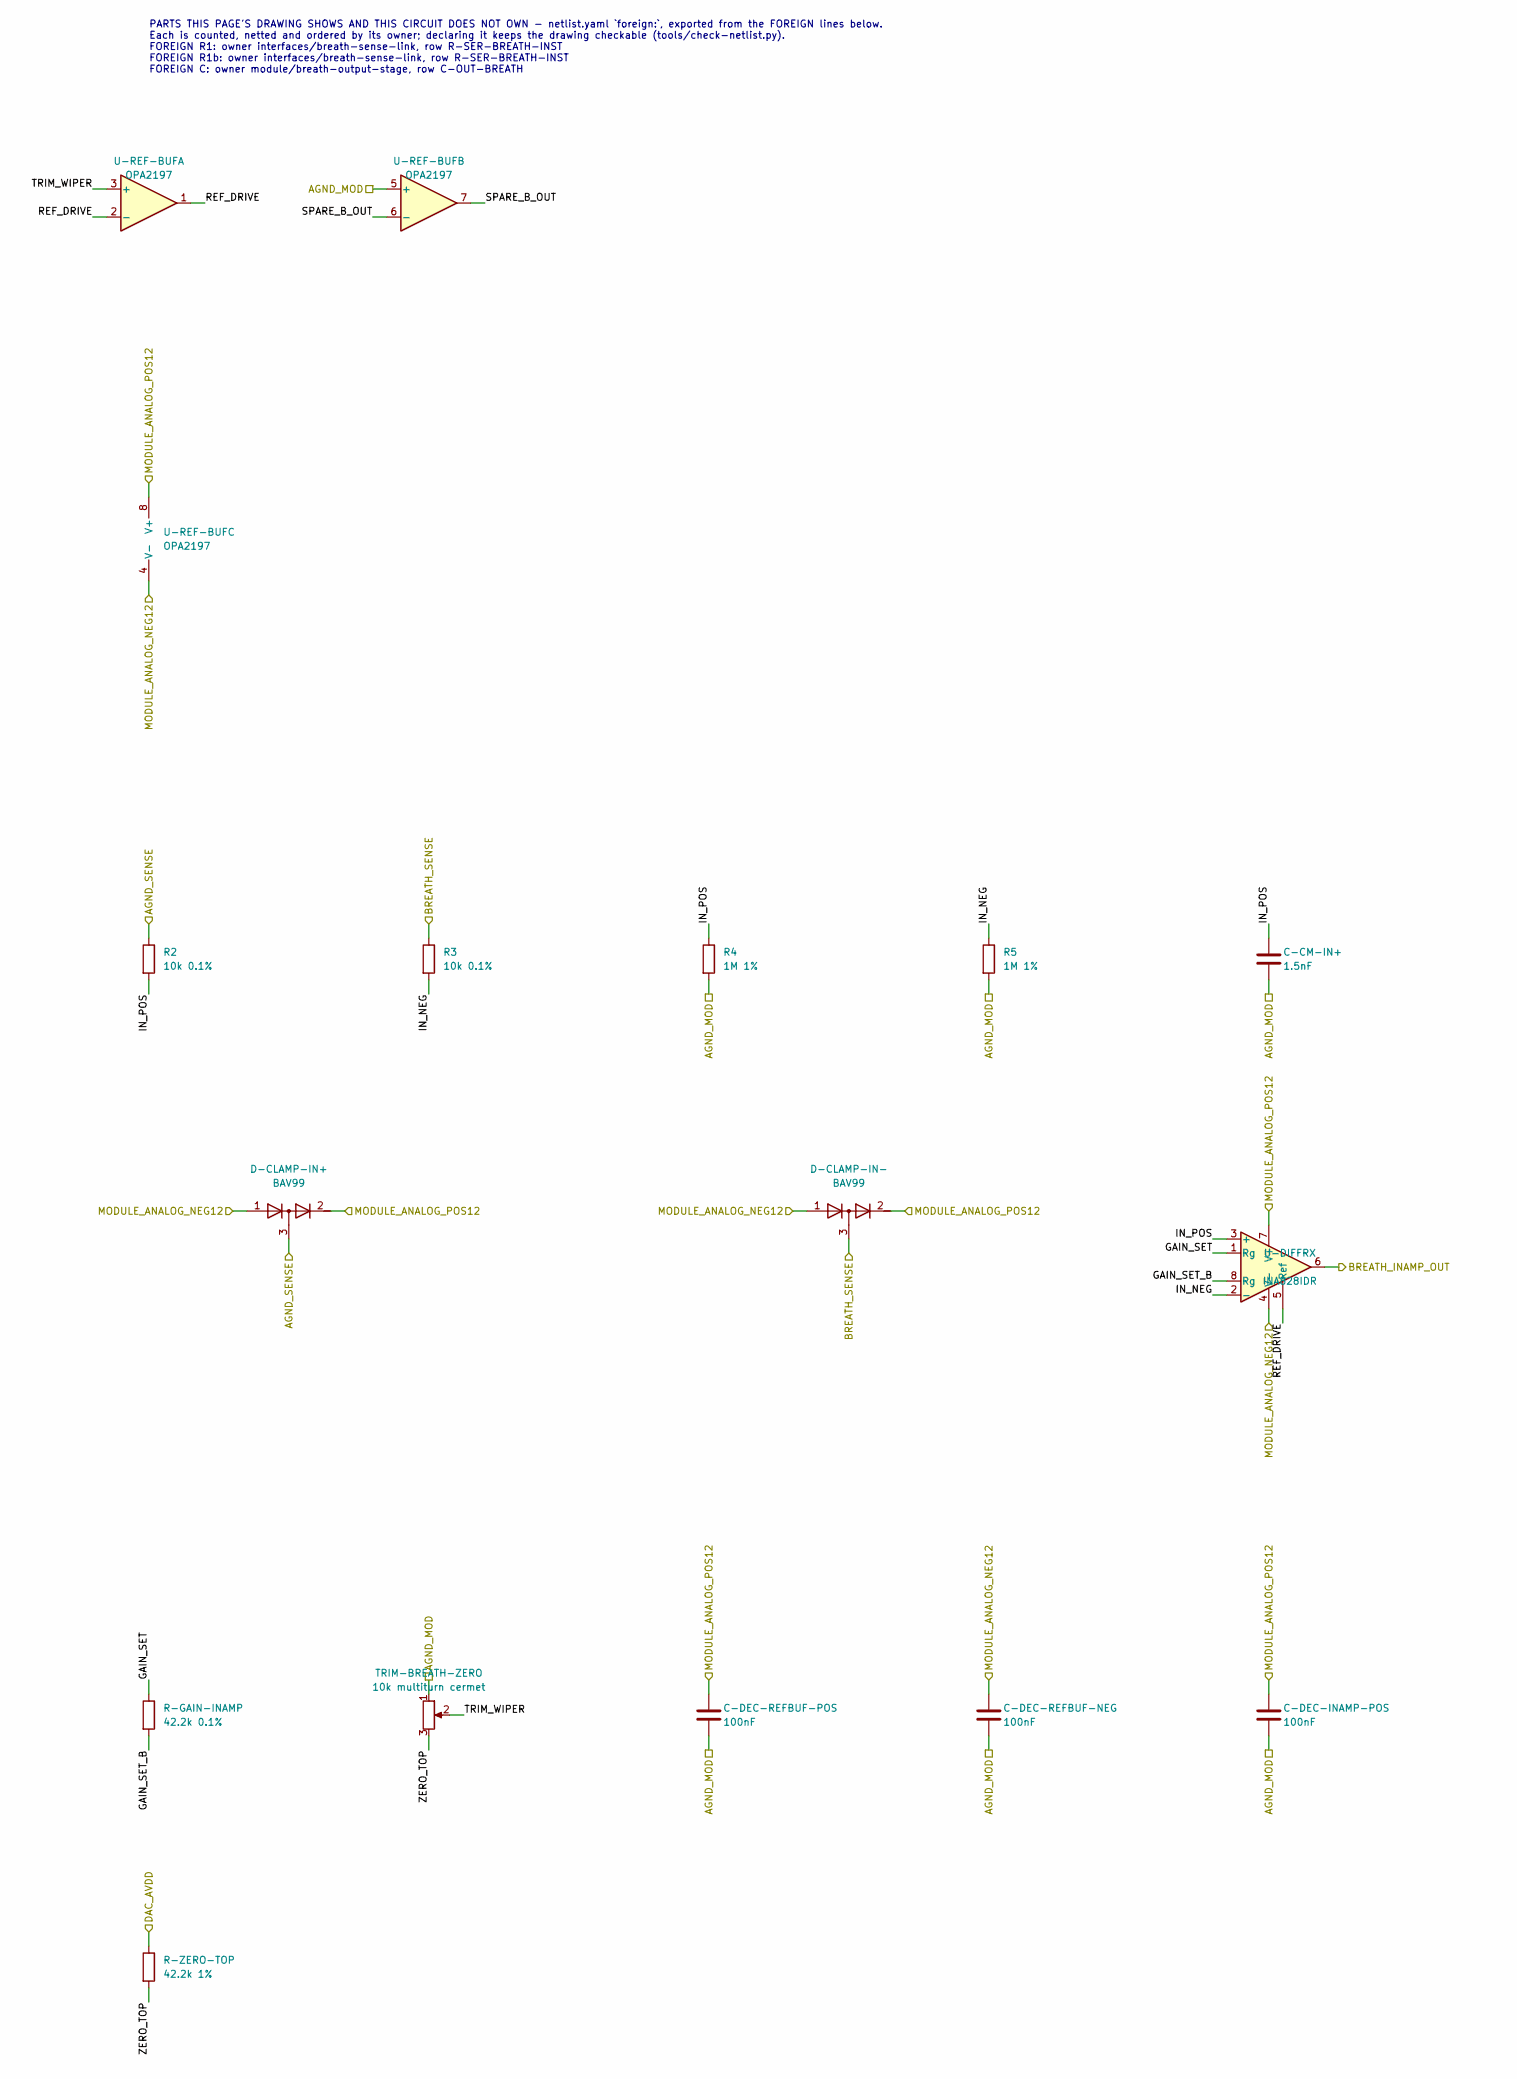
[picture p201: schematic breath-receive-stage.kicad_sch, part in row 1, column 1]

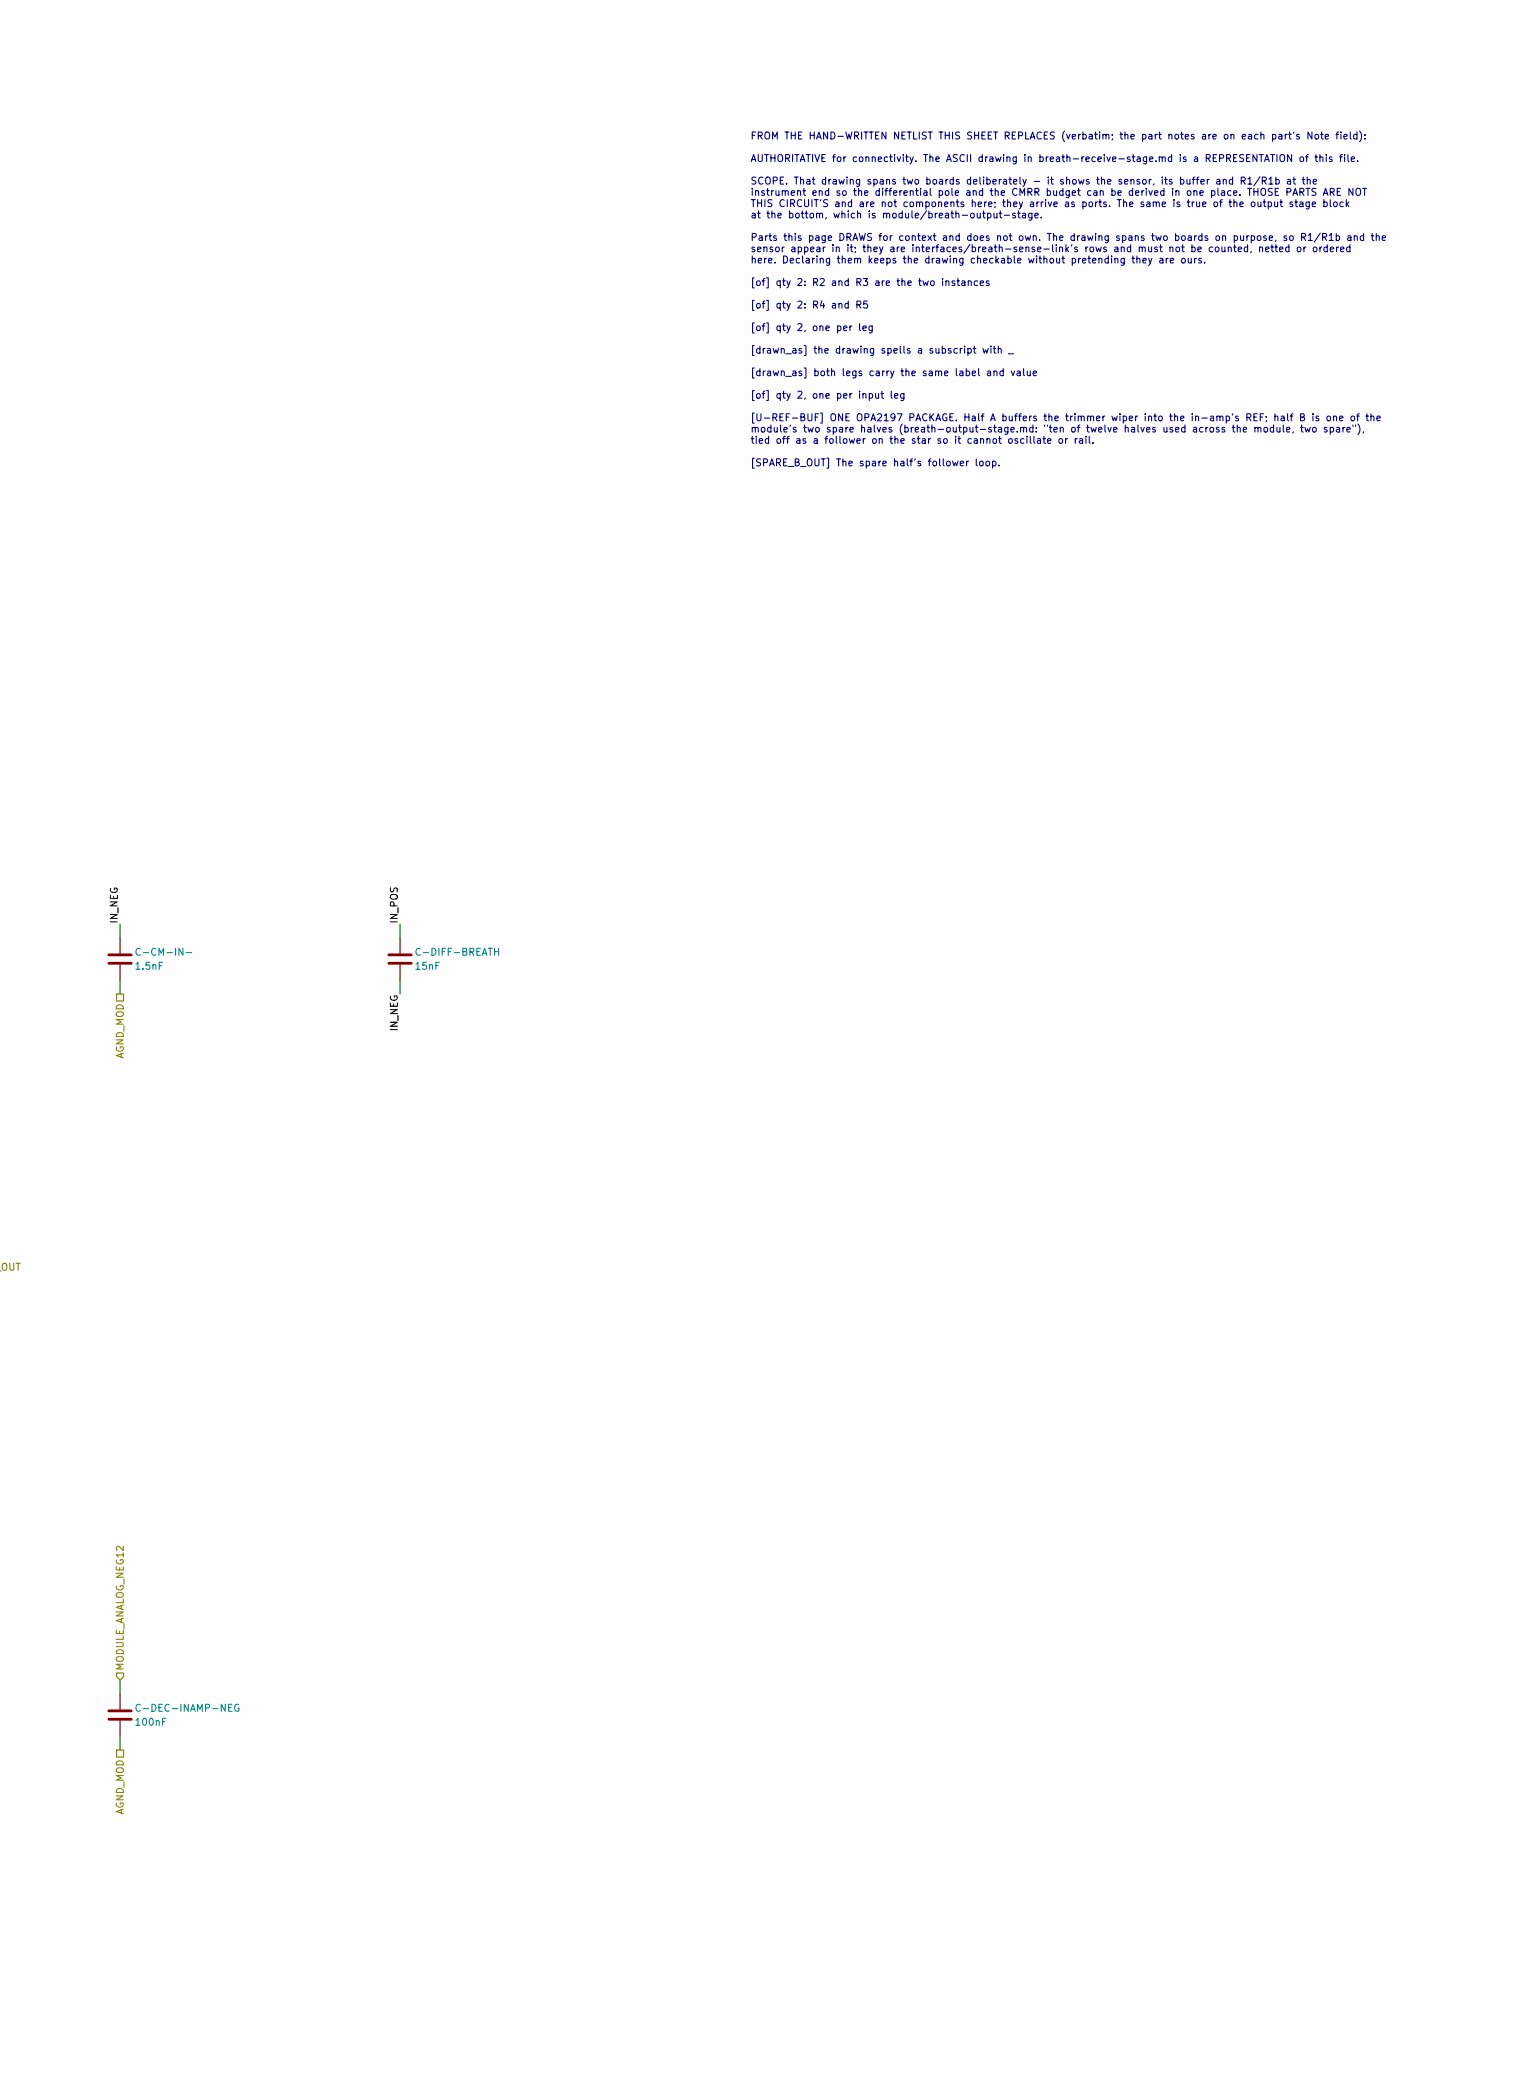
[picture p202: schematic breath-receive-stage.kicad_sch, part in row 1, column 2]

Parts:
C-CM-IN+: 1.5nF; C_0805_2012Metric; MPN CC0805FRNPO9BN152; LCSC C541572
C-CM-IN-: 1.5nF; C_0805_2012Metric; MPN CC0805FRNPO9BN152; LCSC C541572
C-DEC-INAMP-NEG: 100nF; C_0805_2012Metric; MPN CC0805KRX7R9BB104; LCSC C49678
C-DEC-INAMP-POS: 100nF; C_0805_2012Metric; MPN CC0805KRX7R9BB104; LCSC C49678
C-DEC-REFBUF-NEG: 100nF; C_0805_2012Metric; MPN CC0805KRX7R9BB104; LCSC C49678
C-DEC-REFBUF-POS: 100nF; C_0805_2012Metric; MPN CC0805KRX7R9BB104; LCSC C49678
C-DIFF-BREATH: 15nF; C_0805_2012Metric; MPN C2012C0G1H153JT000N; LCSC C445728
D-CLAMP-IN+: BAV99; SOT-23; MPN BAV99,215; LCSC C2500
D-CLAMP-IN-: BAV99; SOT-23; MPN BAV99,215; LCSC C2500
R2, R3: 10k 0.1%; R_0805_2012Metric; MPN RT0805BRD0710KL; LCSC C110775
R4, R5: 1M 1%; R_0805_2012Metric; MPN 0805W8F1004T5E; LCSC C17514
R-GAIN-INAMP: 42.2k 0.1%; R_0805_2012Metric; MPN RT0805BRD0742K2L; LCSC C706241
R-ZERO-TOP: 42.2k 1%; R_0805_2012Metric; MPN 0805W8F4222T5E; LCSC C17686
TRIM-BREATH-ZERO: 10k multiturn cermet; Potentiometer_Bourns_3296W_Vertical; MPN 3296W-1-103LF; LCSC C34846
U-DIFFRX: INA828IDR; SOIC-8_3.9x4.9mm_P1.27mm; MPN INA828IDR; LCSC C544342
U-REF-BUF: OPA2197; SOIC-8_3.9x4.9mm_P1.27mm; MPN OPA2197IDR; LCSC C139363

Connections:
AGND_MOD: C-CM-IN+.2, C-CM-IN-.2, C-DEC-INAMP-NEG.2, C-DEC-INAMP-POS.2, C-DEC-REFBUF-NEG.2, C-DEC-REFBUF-POS.2, R4.2, R5.2, TRIM-BREATH-ZERO.1, U-REF-BUF.5 (+)
AGND_SENSE: D-CLAMP-IN+.3 (common), R2.1
BREATH_INAMP_OUT: U-DIFFRX.6
BREATH_SENSE: D-CLAMP-IN-.3 (common), R3.1
DAC_AVDD: R-ZERO-TOP.1
GAIN_SET: R-GAIN-INAMP.1, U-DIFFRX.1 (Rg)
GAIN_SET_B: R-GAIN-INAMP.2, U-DIFFRX.8 (Rg)
IN_NEG: C-CM-IN-.1, C-DIFF-BREATH.2, R3.2, R5.1, U-DIFFRX.2 (-)
IN_POS: C-CM-IN+.1, C-DIFF-BREATH.1, R2.2, R4.1, U-DIFFRX.3 (+)
MODULE_ANALOG_NEG12: C-DEC-INAMP-NEG.1, C-DEC-REFBUF-NEG.1, D-CLAMP-IN+.1 (A), D-CLAMP-IN-.1 (A), U-DIFFRX.4 (V-), U-REF-BUF.4 (V-)
MODULE_ANALOG_POS12: C-DEC-INAMP-POS.1, C-DEC-REFBUF-POS.1, D-CLAMP-IN+.2 (K), D-CLAMP-IN-.2 (K), U-DIFFRX.7 (V+), U-REF-BUF.8 (V+)
REF_DRIVE: U-DIFFRX.5 (Ref), U-REF-BUF.1, U-REF-BUF.2 (-)
SPARE_B_OUT: U-REF-BUF.6 (-), U-REF-BUF.7
TRIM_WIPER: TRIM-BREATH-ZERO.2, U-REF-BUF.3 (+)
ZERO_TOP: R-ZERO-TOP.2, TRIM-BREATH-ZERO.3

Notes on the sheet:
FROM THE HAND-WRITTEN NETLIST THIS SHEET REPLACES (verbatim; the part notes are on each part's Note field): AUTHORITATIVE for connectivity. The ASCII drawing in breath-receive-stage.md is a REPRESENTATION of this file. SCOPE. That drawing spans two boards deliberately - it shows the sensor, its buf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
PARTS THIS PAGE'S DRAWING SHOWS AND THIS CIRCUIT DOES NOT OWN - netlist.yaml `foreign:`, exported from the FOREIGN lines below. Each is counted, netted and ordered by its owner; declaring it keeps the drawing checkable (tools/check-netlist.py). FOREIGN R1: owner interfaces/breath-sense-link, row R-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
