jeffmhopkins/Woody/hardware/module/breath-response-shaper/breath-response-shaper.main.kicad_sch

## KiCad design hardware/module/breath-response-shaper/breath-response-shaper.main.kicad_sch (2026-09-30)

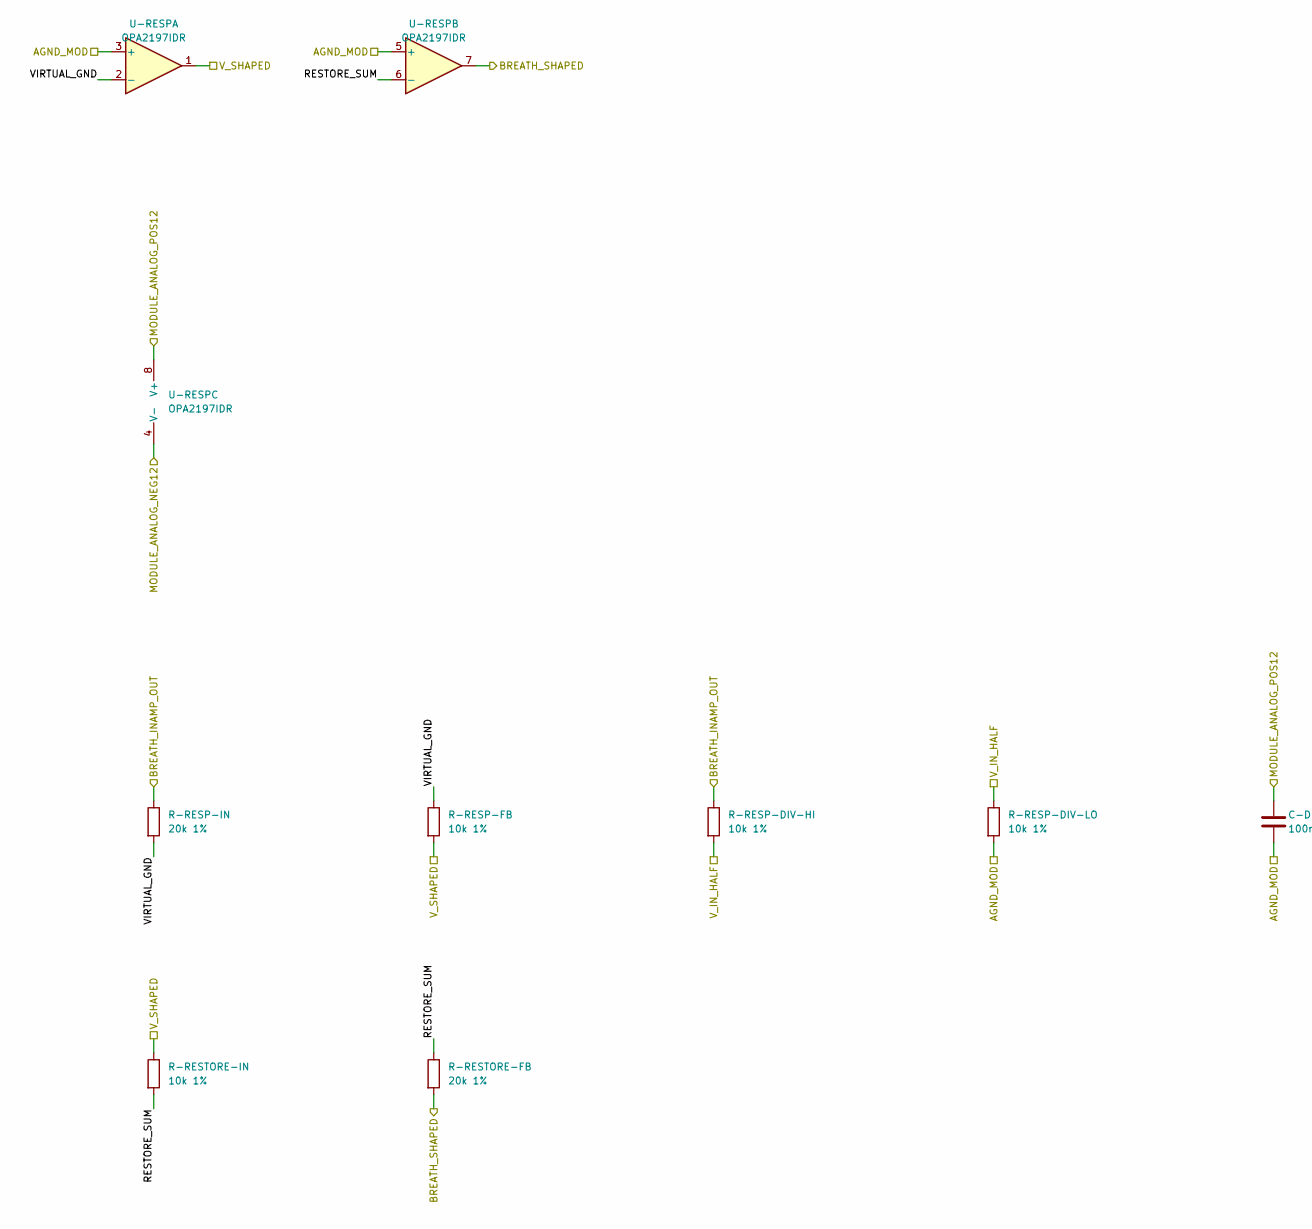
[picture p203: schematic breath-response-shaper.main.kicad_sch, part in row 1, column 1]

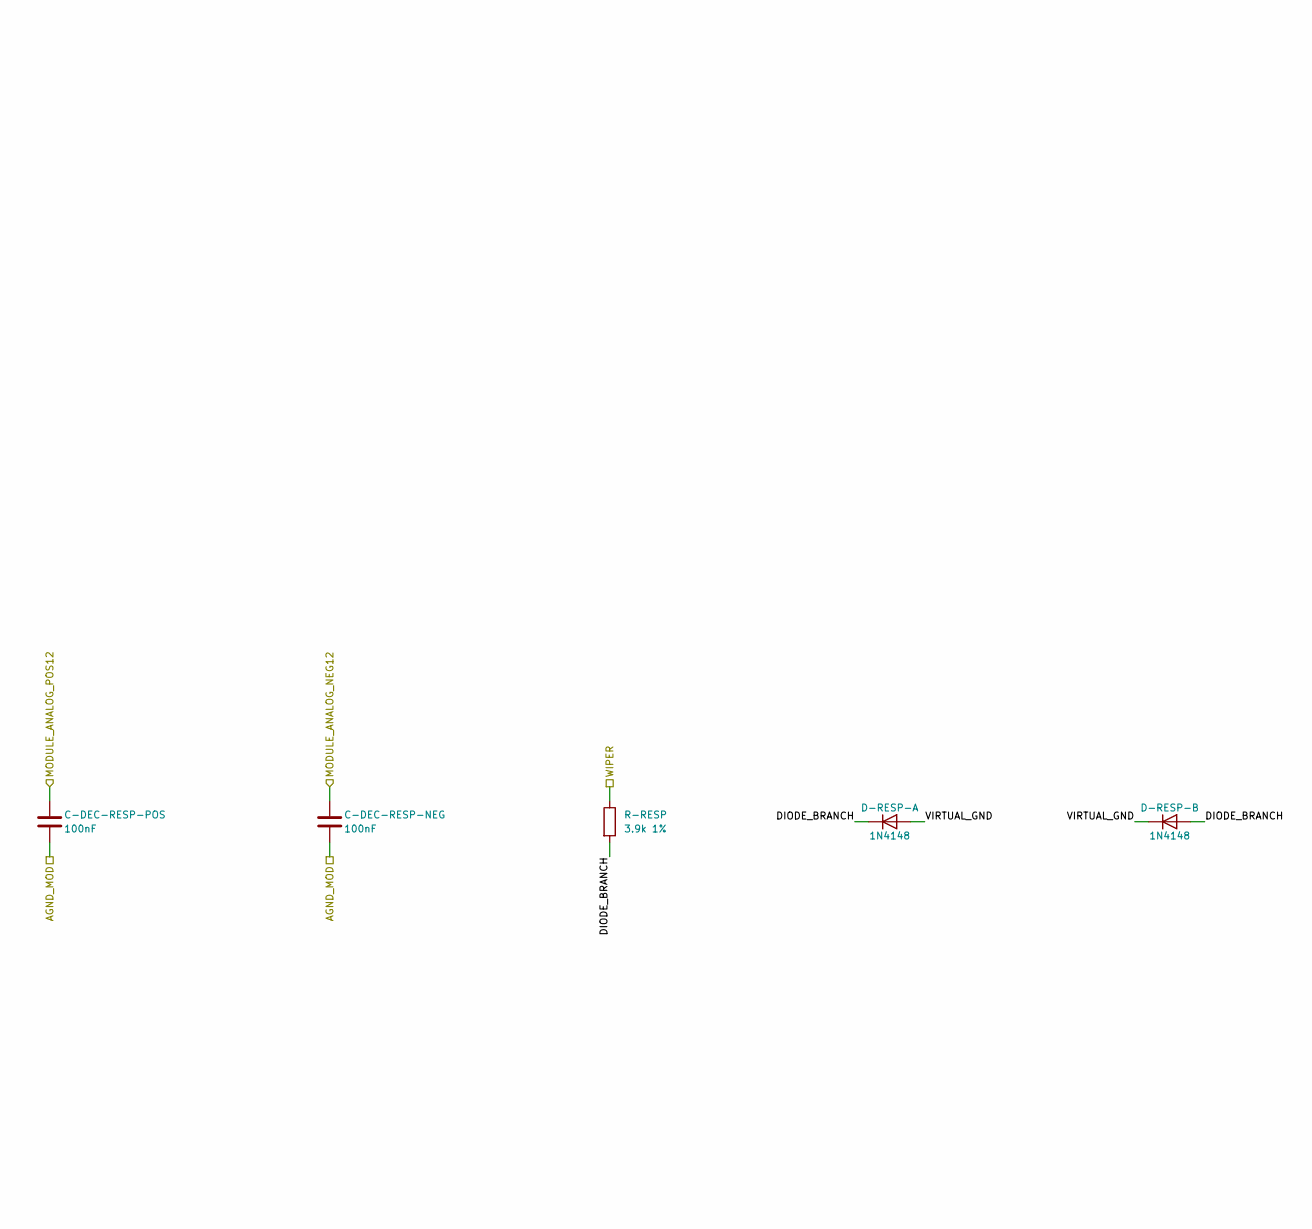
[picture p204: schematic breath-response-shaper.main.kicad_sch, part in row 1, column 2]

Parts:
C-DEC-RESP-NEG: 100nF; C_0805_2012Metric; MPN CC0805KRX7R9BB104; LCSC C49678
C-DEC-RESP-POS: 100nF; C_0805_2012Metric; MPN CC0805KRX7R9BB104; LCSC C49678
D-RESP-A: 1N4148; D_SOD-123; MPN 1N4148W-E3-08; LCSC C241939
D-RESP-B: 1N4148; D_SOD-123; MPN 1N4148W-E3-08; LCSC C241939
R-RESP: 3.9k 1%; R_0805_2012Metric; MPN 0805W8F3901T5E; LCSC C17614
R-RESP-DIV-HI: 10k 1%; R_0805_2012Metric; MPN 0805W8F1002T5E; LCSC C17414
R-RESP-DIV-LO: 10k 1%; R_0805_2012Metric; MPN 0805W8F1002T5E; LCSC C17414
R-RESP-FB: 10k 1%; R_0805_2012Metric; MPN 0805W8F1002T5E; LCSC C17414
R-RESP-IN: 20k 1%; R_0805_2012Metric; MPN 0805W8F2002T5E; LCSC C4328
R-RESTORE-FB: 20k 1%; R_0805_2012Metric; MPN 0805W8F2002T5E; LCSC C4328
R-RESTORE-IN: 10k 1%; R_0805_2012Metric; MPN 0805W8F1002T5E; LCSC C17414
U-RESP: OPA2197IDR; SOIC-8_3.9x4.9mm_P1.27mm; MPN OPA2197IDR; LCSC C139363

Connections:
AGND_MOD: C-DEC-RESP-NEG.2, C-DEC-RESP-POS.2, R-RESP-DIV-LO.2, U-RESP.3 (+), U-RESP.5 (+)
BREATH_INAMP_OUT: R-RESP-DIV-HI.1, R-RESP-IN.1
BREATH_SHAPED: R-RESTORE-FB.2, U-RESP.7
DIODE_BRANCH: D-RESP-A.1 (K), D-RESP-B.2 (A), R-RESP.2
MODULE_ANALOG_NEG12: C-DEC-RESP-NEG.1, U-RESP.4 (V-)
MODULE_ANALOG_POS12: C-DEC-RESP-POS.1, U-RESP.8 (V+)
RESTORE_SUM: R-RESTORE-FB.1, R-RESTORE-IN.2, U-RESP.6 (-)
VIRTUAL_GND: D-RESP-A.2 (A), D-RESP-B.1 (K), R-RESP-FB.1, R-RESP-IN.2, U-RESP.2 (-)
V_IN_HALF: R-RESP-DIV-HI.2, R-RESP-DIV-LO.1
V_SHAPED: R-RESP-FB.2, R-RESTORE-IN.1, U-RESP.1
WIPER: R-RESP.1
