jeffmhopkins/Woody/hardware/module/dac8568/dac8568.kicad_sch

## KiCad design hardware/module/dac8568/dac8568.kicad_sch (2026-09-30)

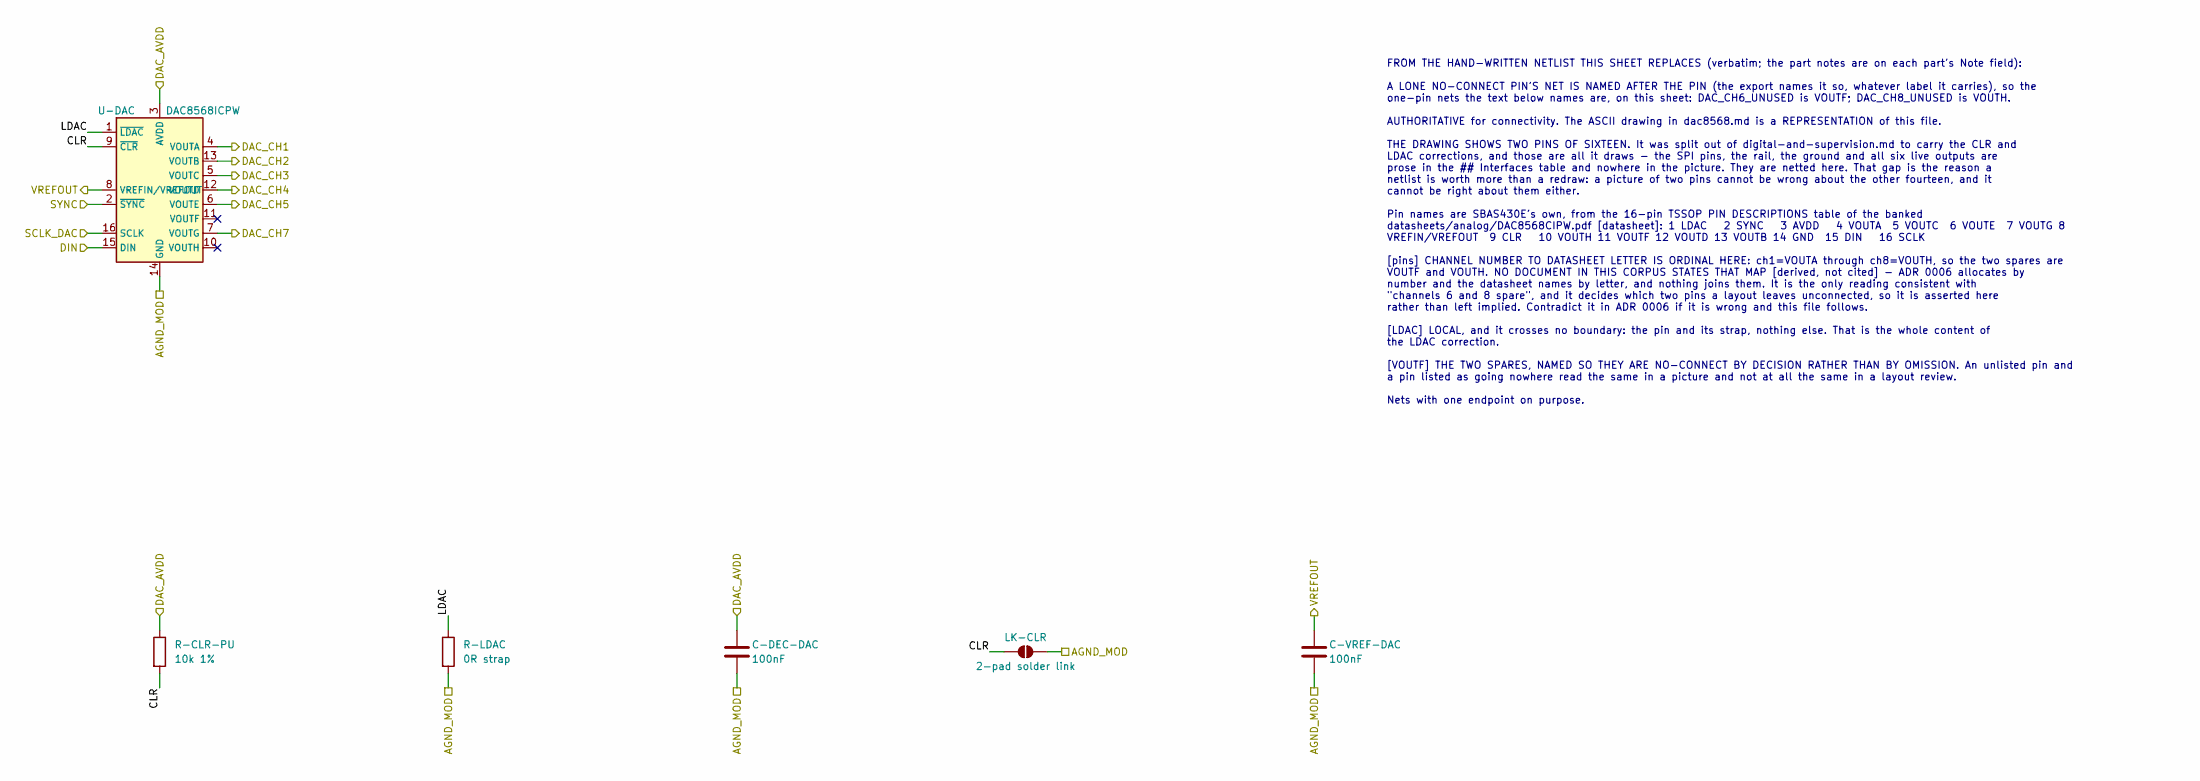
[picture p205: schematic dac8568.kicad_sch]

Parts:
C-DEC-DAC: 100nF; C_0805_2012Metric; MPN CC0805KRX7R9BB104; LCSC C49678
C-VREF-DAC: 100nF; C_0805_2012Metric; MPN CC0805KRX7R9BB104; LCSC C49678
LK-CLR: 2-pad solder link; SolderJumper-2_P1.3mm_Open_RoundedPad1.0x1.5mm
R-CLR-PU: 10k 1%; R_0805_2012Metric; MPN 0805W8F1002T5E; LCSC C17414
R-LDAC: 0R strap; R_0805_2012Metric; MPN 0805W8F0000T5E; LCSC C17477
U-DAC: DAC8568ICPW; TSSOP-16_4.4x5mm_P0.65mm; MPN DAC8568ICPWR; LCSC C524819

Connections:
AGND_MOD: C-DEC-DAC.2, C-VREF-DAC.2, LK-CLR.2 (B), R-LDAC.2, U-DAC.14 (GND)
CLR: LK-CLR.1 (A), R-CLR-PU.2, U-DAC.9 (~CLR)
DAC_AVDD: C-DEC-DAC.1, R-CLR-PU.1, U-DAC.3 (AVDD)
DAC_CH1: U-DAC.4 (VOUTA)
DAC_CH2: U-DAC.13 (VOUTB)
DAC_CH3: U-DAC.5 (VOUTC)
DAC_CH4: U-DAC.12 (VOUTD)
DAC_CH5: U-DAC.6 (VOUTE)
DAC_CH7: U-DAC.7 (VOUTG)
DIN: U-DAC.15 (DIN)
LDAC: R-LDAC.1, U-DAC.1 (~LDAC)
SCLK_DAC: U-DAC.16 (SCLK)
SYNC: U-DAC.2 (~SYNC)
VREFOUT: C-VREF-DAC.1, U-DAC.8 (VREFIN/VREFOUT)

Notes on the sheet:
FROM THE HAND-WRITTEN NETLIST THIS SHEET REPLACES (verbatim; the part notes are on each part's Note field): A LONE NO-CONNECT PIN'S NET IS NAMED AFTER THE PIN (the export names it so, whatever label it carries), so the one-pin nets the text below names are, on this sheet: DAC_CH6_UNUSED is VOUTF; D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
