jeffmhopkins/Woody/hardware/module/digital-and-supervision/digital-and-supervision.kicad_sch

## KiCad design hardware/module/digital-and-supervision/digital-and-supervision.kicad_sch (2026-09-30)

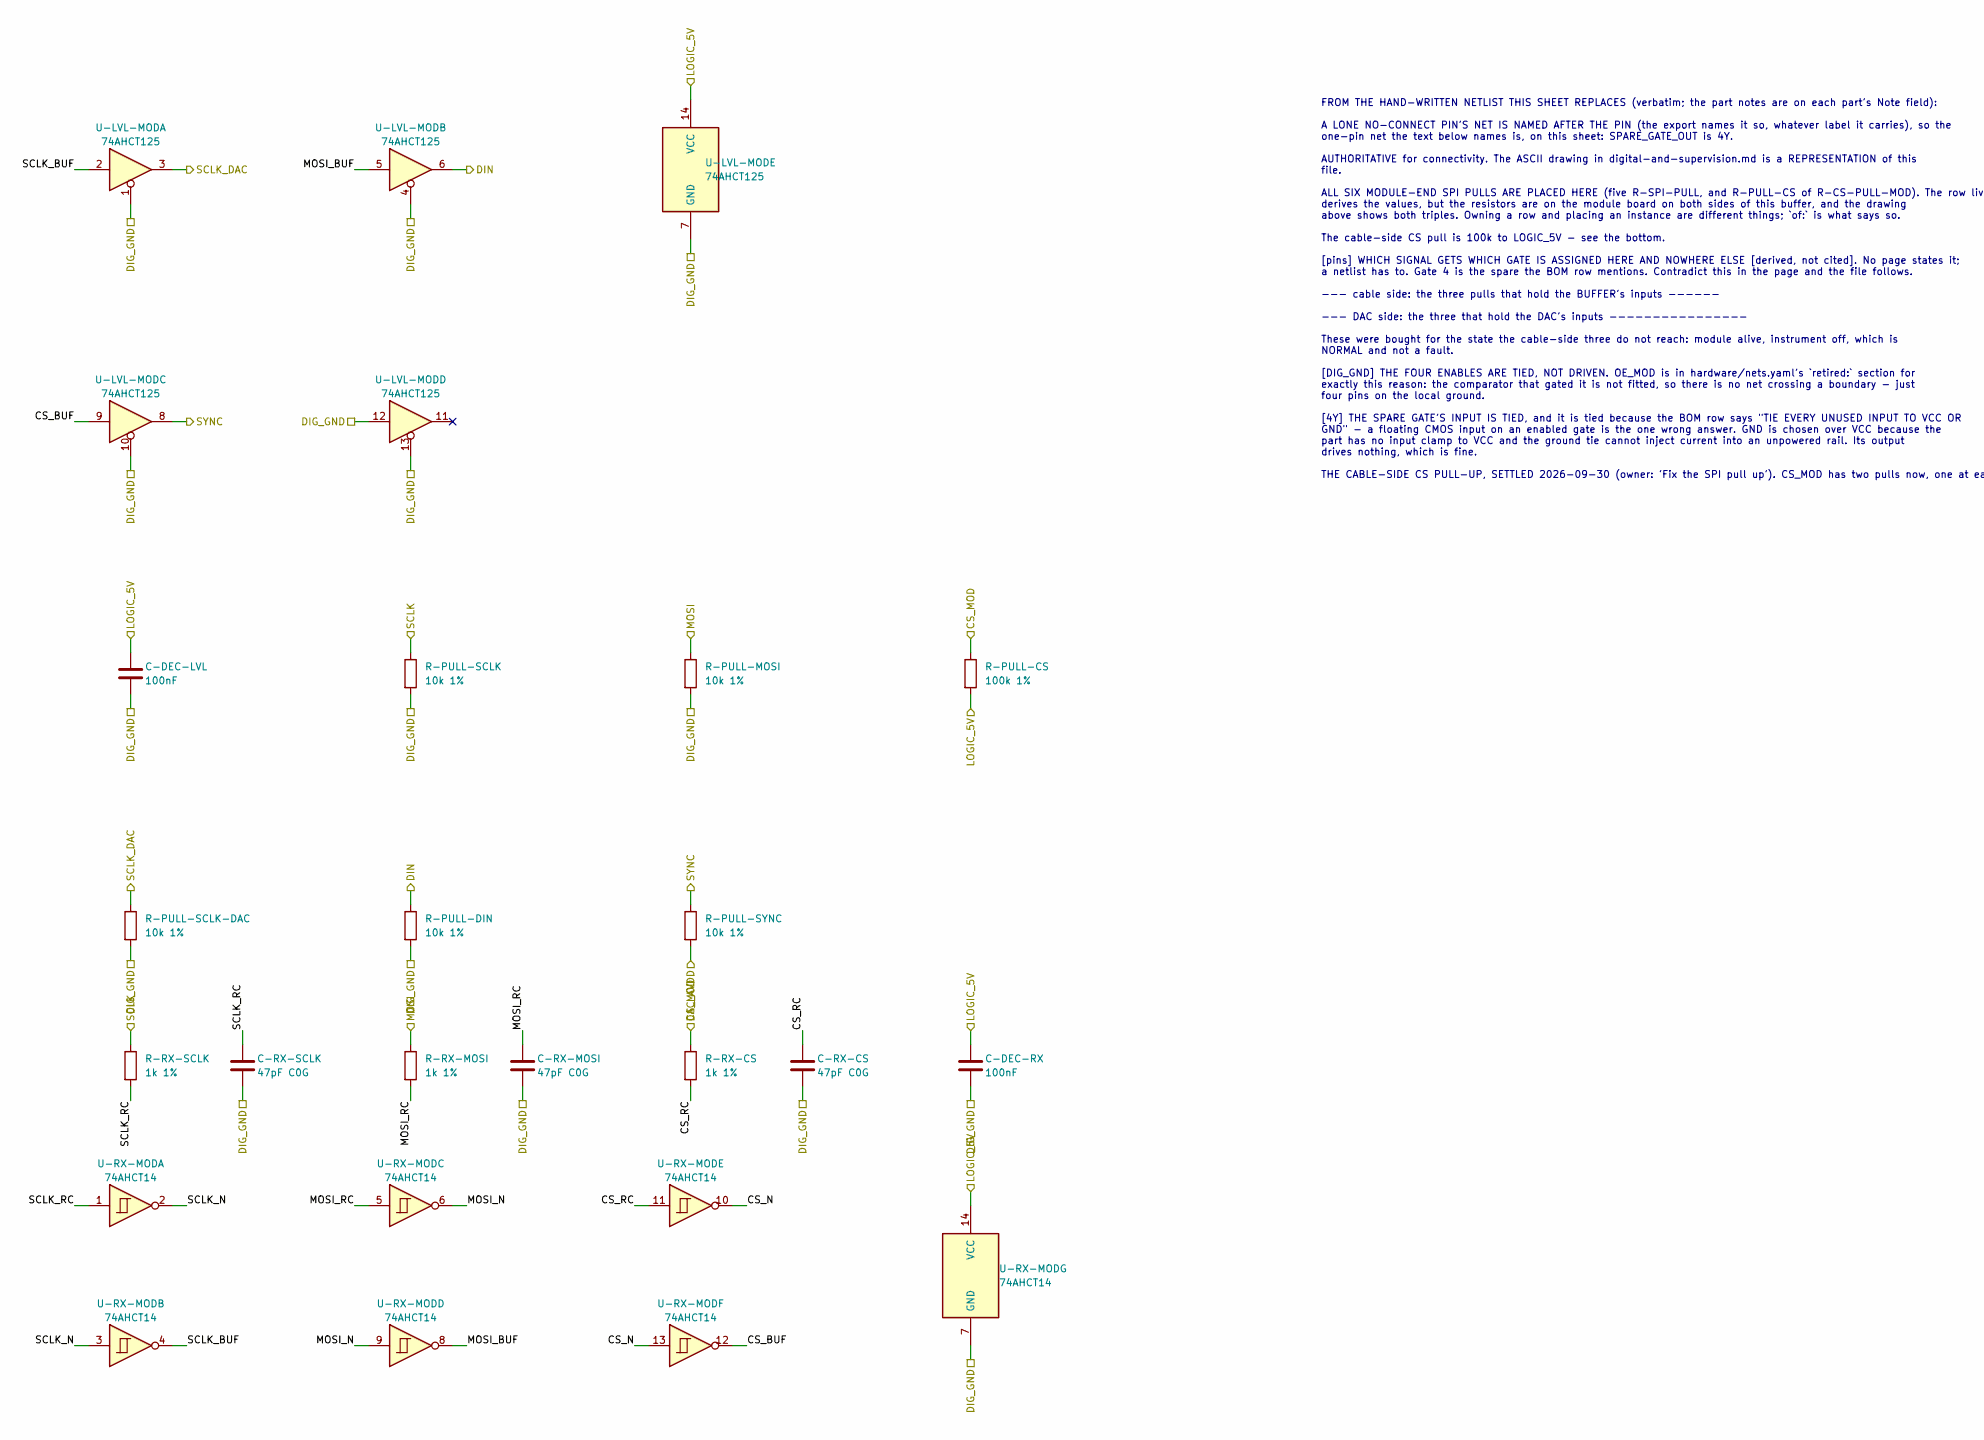
[picture p206: schematic digital-and-supervision.kicad_sch, part in row 1, column 1]

Parts:
C-DEC-LVL: 100nF; C_0805_2012Metric; MPN CC0805KRX7R9BB104; LCSC C49678
C-DEC-RX: 100nF; C_0805_2012Metric; MPN CC0805KRX7R9BB104; LCSC C49678
C-RX-CS: 47pF C0G; C_0805_2012Metric; MPN CL21C470JBANNNC; LCSC C14857
C-RX-MOSI: 47pF C0G; C_0805_2012Metric; MPN CL21C470JBANNNC; LCSC C14857
C-RX-SCLK: 47pF C0G; C_0805_2012Metric; MPN CL21C470JBANNNC; LCSC C14857
R-PULL-CS: 100k 1%; R_0805_2012Metric; MPN 0805W8F1003T5E; LCSC C149504
R-PULL-DIN: 10k 1%; R_0805_2012Metric; MPN 0805W8F1002T5E; LCSC C17414
R-PULL-MOSI: 10k 1%; R_0805_2012Metric; MPN 0805W8F1002T5E; LCSC C17414
R-PULL-SCLK: 10k 1%; R_0805_2012Metric; MPN 0805W8F1002T5E; LCSC C17414
R-PULL-SCLK-DAC: 10k 1%; R_0805_2012Metric; MPN 0805W8F1002T5E; LCSC C17414
R-PULL-SYNC: 10k 1%; R_0805_2012Metric; MPN 0805W8F1002T5E; LCSC C17414
R-RX-CS: 1k 1%; R_0805_2012Metric; MPN 0805W8F1001T5E; LCSC C17513
R-RX-MOSI: 1k 1%; R_0805_2012Metric; MPN 0805W8F1001T5E; LCSC C17513
R-RX-SCLK: 1k 1%; R_0805_2012Metric; MPN 0805W8F1001T5E; LCSC C17513
U-LVL-MOD: 74AHCT125; SOIC-14_3.9x8.7mm_P1.27mm; MPN SN74AHCT125DR; LCSC C155176
U-RX-MOD: 74AHCT14; SOIC-14_3.9x8.7mm_P1.27mm; MPN SN74AHCT14DR; LCSC C141316

Connections:
CS_BUF: U-LVL-MOD.9, U-RX-MOD.12
CS_MOD: R-PULL-CS.1, R-RX-CS.1
CS_N: U-RX-MOD.10, U-RX-MOD.13
CS_RC: C-RX-CS.1, R-RX-CS.2, U-RX-MOD.11
DAC_AVDD: R-PULL-SYNC.2
DIG_GND: C-DEC-LVL.2, C-DEC-RX.2, C-RX-CS.2, C-RX-MOSI.2, C-RX-SCLK.2, R-PULL-DIN.2, R-PULL-MOSI.2, R-PULL-SCLK.2, R-PULL-SCLK-DAC.2, U-LVL-MOD.1, U-LVL-MOD.4, U-LVL-MOD.7 (GND), U-LVL-MOD.10, U-LVL-MOD.12, U-LVL-MOD.13, U-RX-MOD.7 (GND)
DIN: R-PULL-DIN.1, U-LVL-MOD.6
LOGIC_5V: C-DEC-LVL.1, C-DEC-RX.1, R-PULL-CS.2, U-LVL-MOD.14 (VCC), U-RX-MOD.14 (VCC)
MOSI: R-PULL-MOSI.1, R-RX-MOSI.1
MOSI_BUF: U-LVL-MOD.5, U-RX-MOD.8
MOSI_N: U-RX-MOD.6, U-RX-MOD.9
MOSI_RC: C-RX-MOSI.1, R-RX-MOSI.2, U-RX-MOD.5
SCLK: R-PULL-SCLK.1, R-RX-SCLK.1
SCLK_BUF: U-LVL-MOD.2, U-RX-MOD.4
SCLK_DAC: R-PULL-SCLK-DAC.1, U-LVL-MOD.3
SCLK_N: U-RX-MOD.2, U-RX-MOD.3
SCLK_RC: C-RX-SCLK.1, R-RX-SCLK.2, U-RX-MOD.1
SYNC: R-PULL-SYNC.1, U-LVL-MOD.8

Notes on the sheet:
FROM THE HAND-WRITTEN NETLIST THIS SHEET REPLACES (verbatim; the part notes are on each part's Note field): A LONE NO-CONNECT PIN'S NET IS NAMED AFTER THE PIN (the export names it so, whatever label it carries), so the one-pin net the text below names is, on this sheet: SPARE_GATE_OUT is 4Y. AUTHOR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
