jeffmhopkins/Woody/hardware/module/mod-channels/mod-channels.jack.kicad_sch

## KiCad design hardware/module/mod-channels/mod-channels.jack.kicad_sch (2026-09-30)

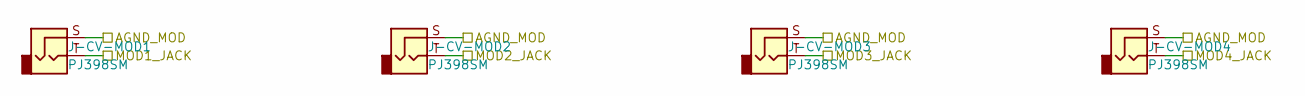
[picture p207: schematic mod-channels.jack.kicad_sch]

Parts:
J-CV-MOD1, J-CV-MOD2, J-CV-MOD3, J-CV-MOD4: PJ398SM; Jack_3.5mm_QingPu_WQP-PJ398SM_Vertical_CircularHoles; MPN PJ398SM

Connections:
AGND_MOD: J-CV-MOD1.S, J-CV-MOD2.S, J-CV-MOD3.S, J-CV-MOD4.S
MOD1_JACK: J-CV-MOD1.T
MOD2_JACK: J-CV-MOD2.T
MOD3_JACK: J-CV-MOD3.T
MOD4_JACK: J-CV-MOD4.T
