jeffmhopkins/Woody/hardware/module/mod-channels/mod-channels.main.kicad_sch

## KiCad design hardware/module/mod-channels/mod-channels.main.kicad_sch (2026-09-30)

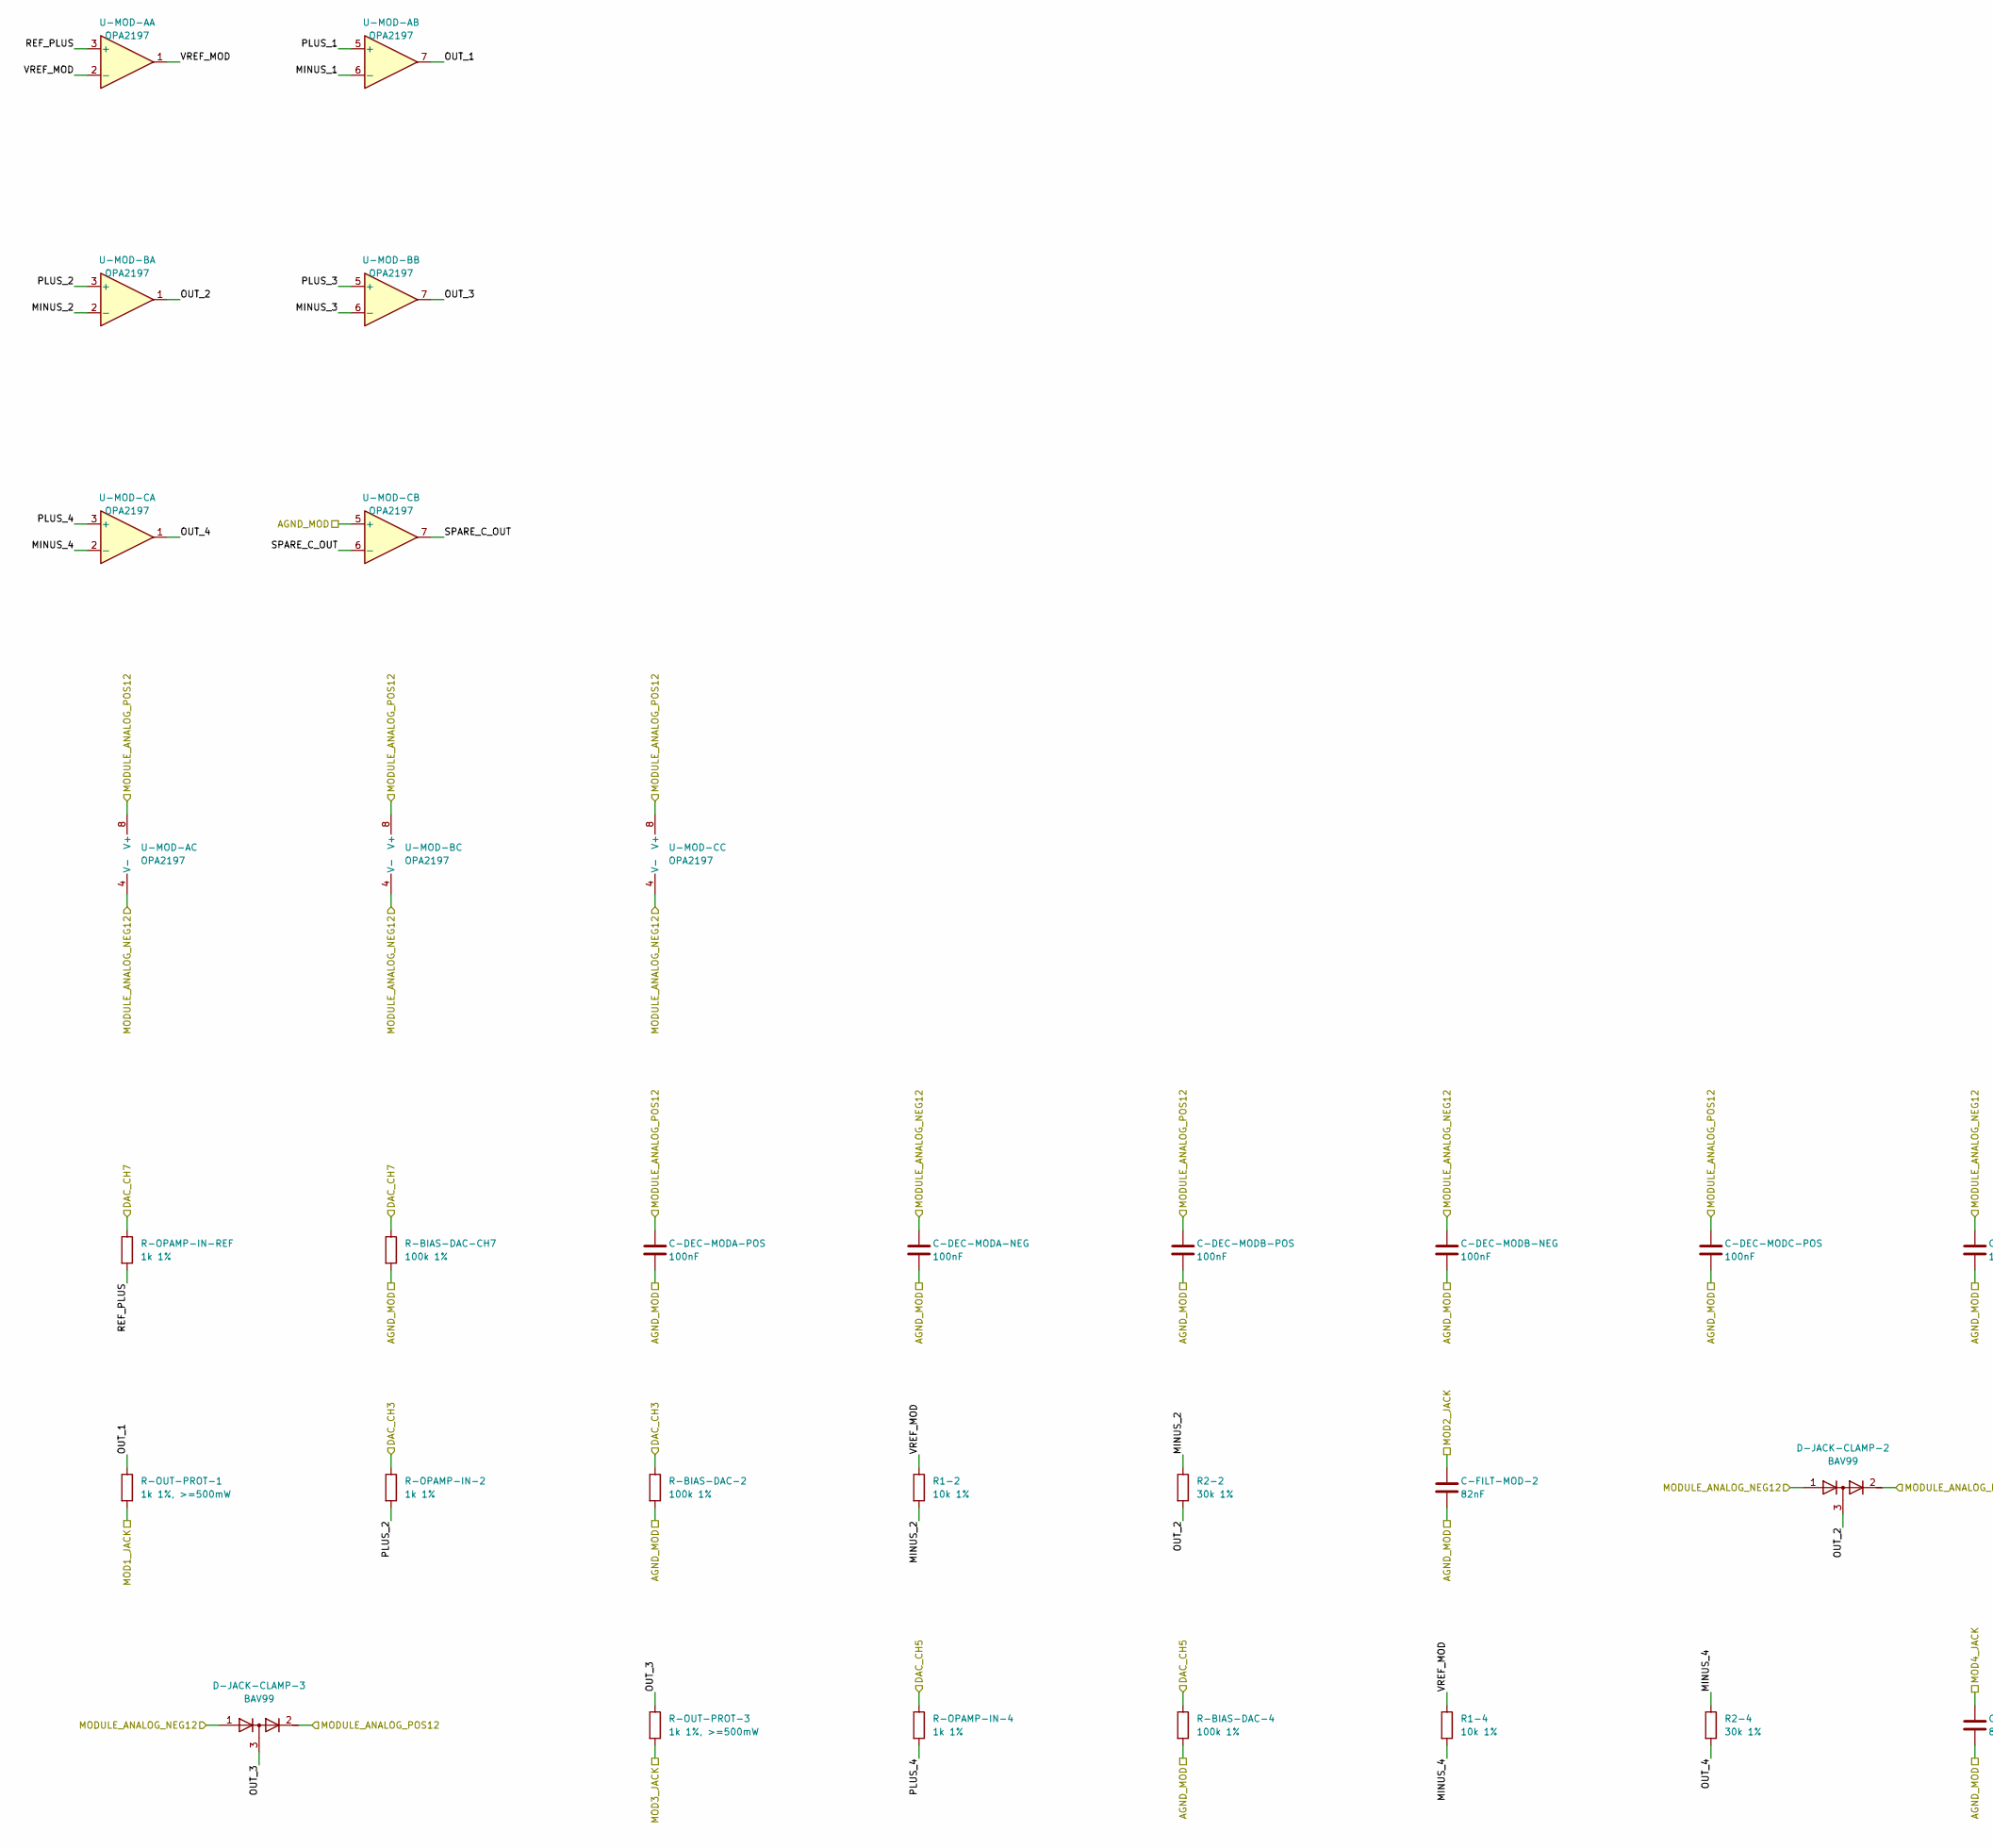
[picture p208: schematic mod-channels.main.kicad_sch, part in row 1, column 1]

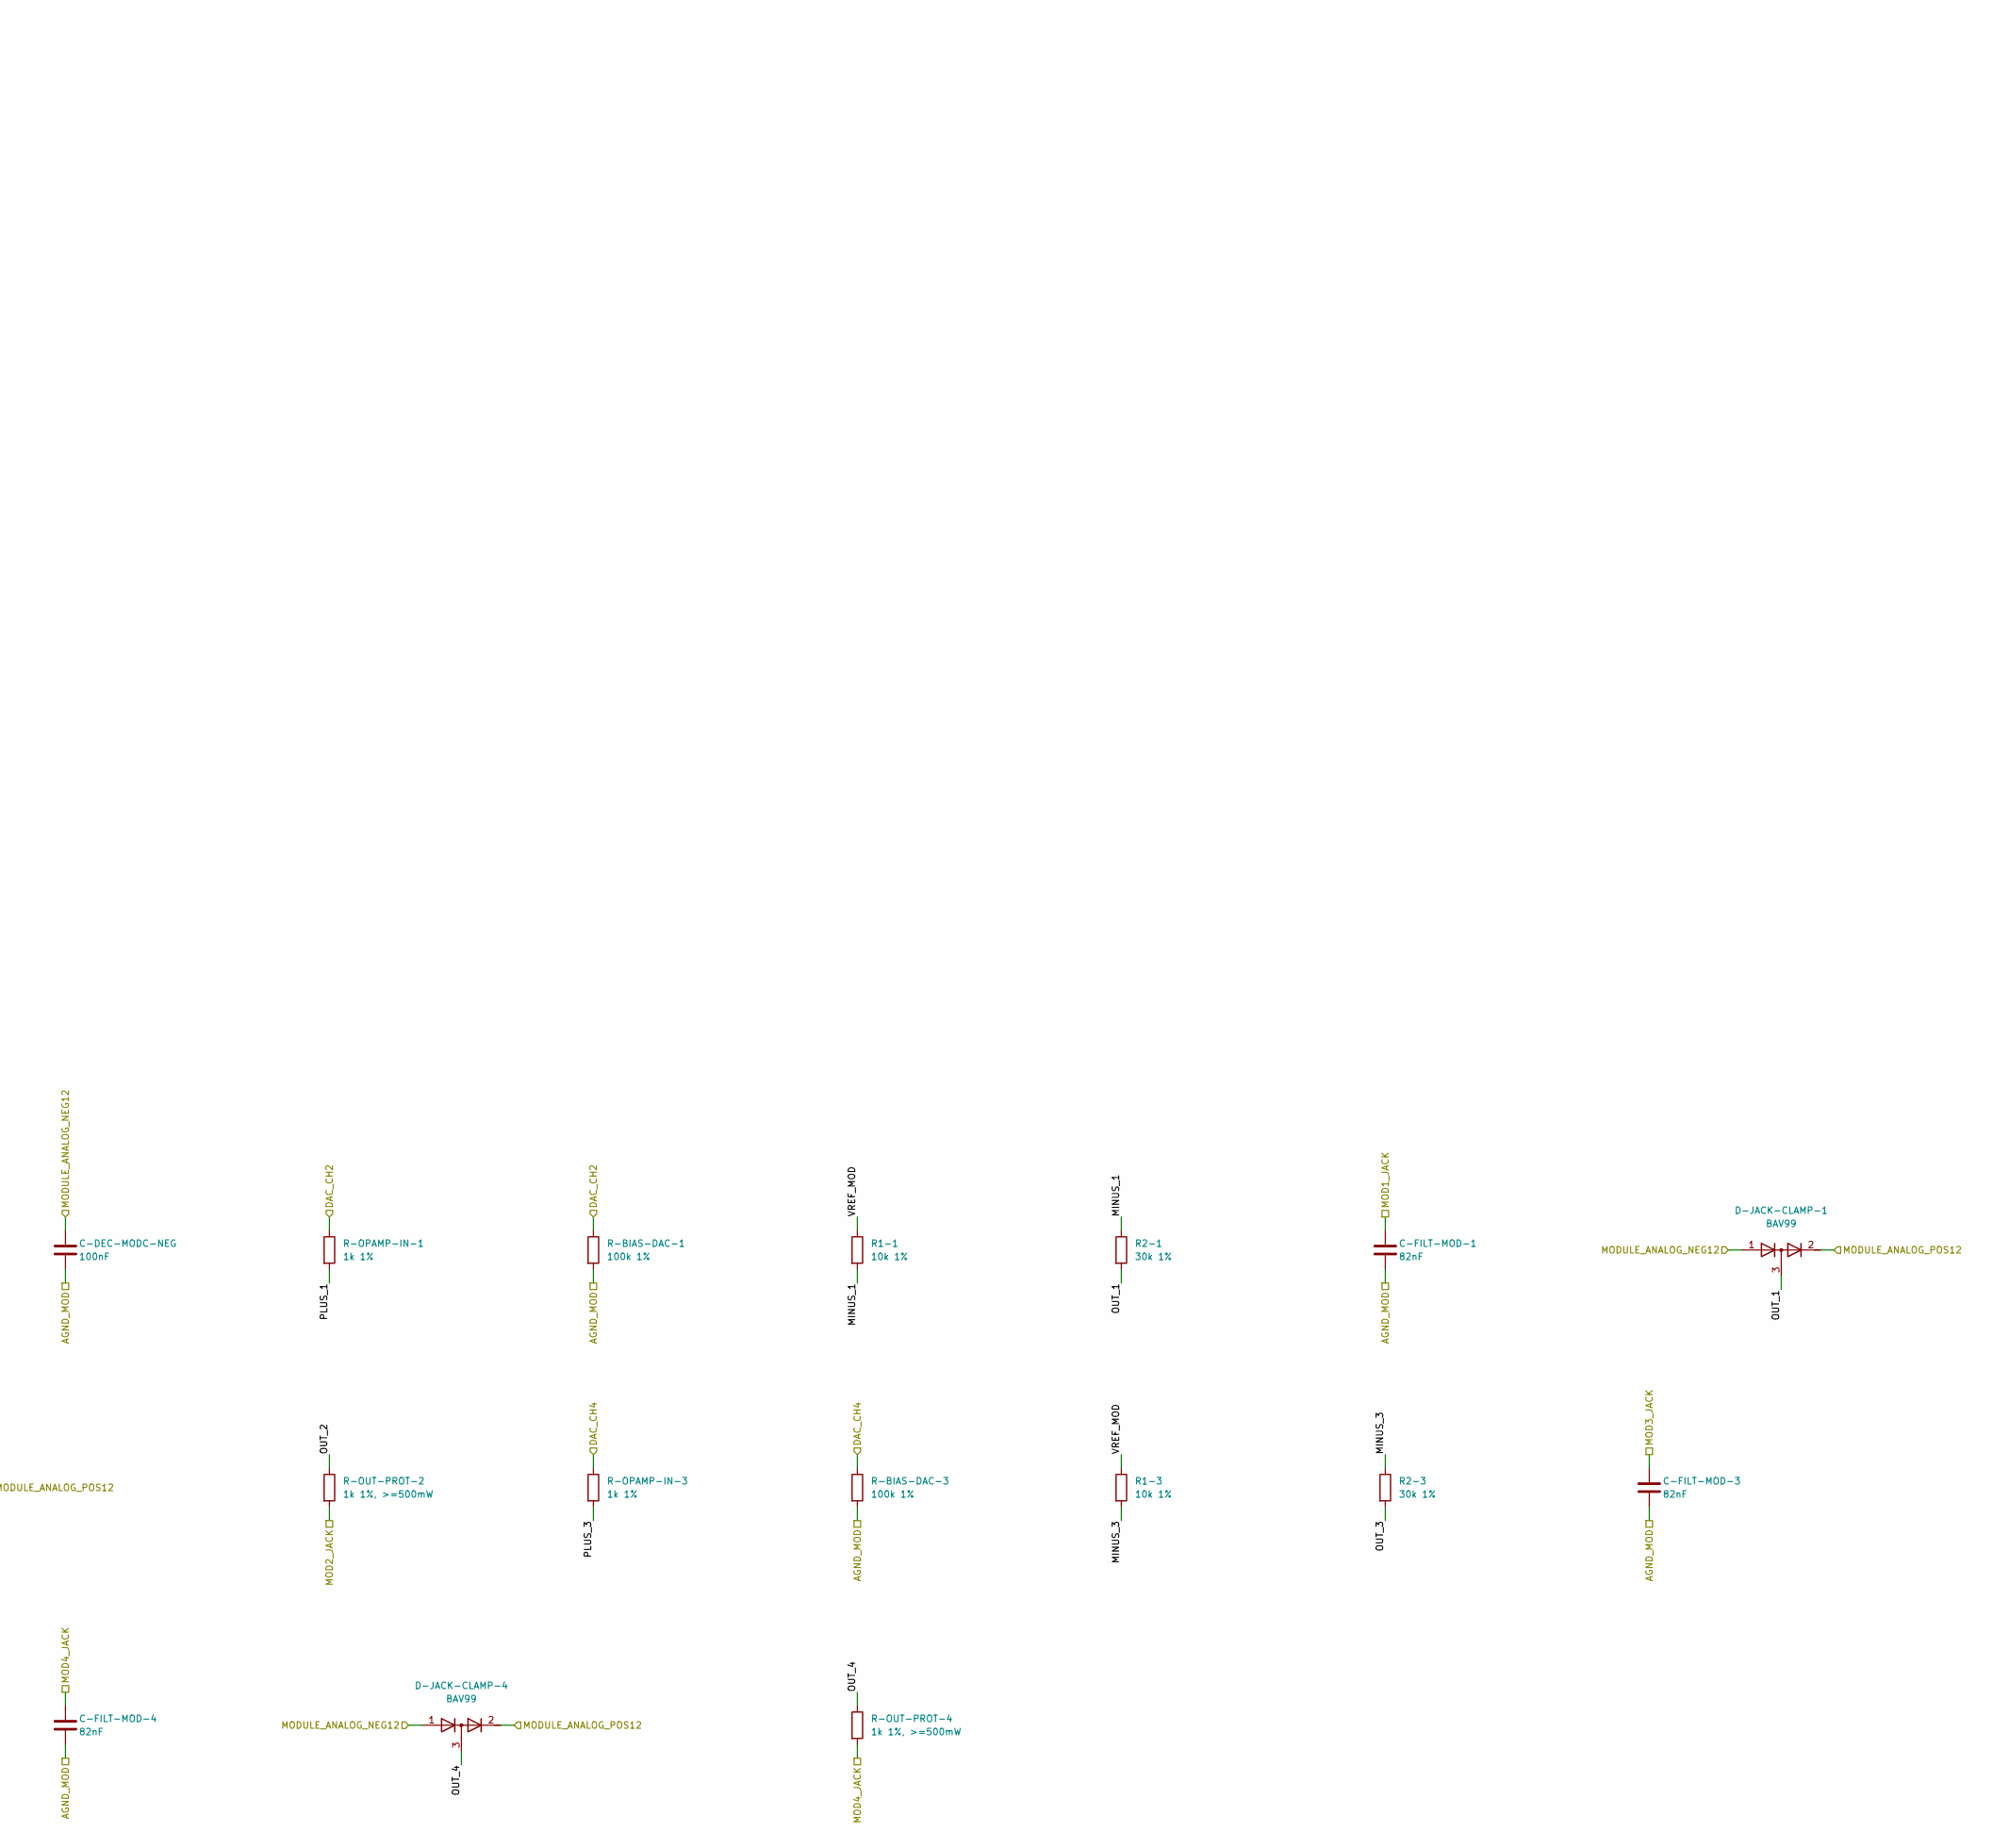
[picture p209: schematic mod-channels.main.kicad_sch, part in row 1, column 2]

Parts:
C-DEC-MODA-NEG: 100nF; C_0805_2012Metric; MPN CC0805KRX7R9BB104; LCSC C49678
C-DEC-MODA-POS: 100nF; C_0805_2012Metric; MPN CC0805KRX7R9BB104; LCSC C49678
C-DEC-MODB-NEG: 100nF; C_0805_2012Metric; MPN CC0805KRX7R9BB104; LCSC C49678
C-DEC-MODB-POS: 100nF; C_0805_2012Metric; MPN CC0805KRX7R9BB104; LCSC C49678
C-DEC-MODC-NEG: 100nF; C_0805_2012Metric; MPN CC0805KRX7R9BB104; LCSC C49678
C-DEC-MODC-POS: 100nF; C_0805_2012Metric; MPN CC0805KRX7R9BB104; LCSC C49678
C-FILT-MOD-1, C-FILT-MOD-2, C-FILT-MOD-3, C-FILT-MOD-4: 82nF; C_1206_3216Metric; MPN GRM31C5C1H823JA01L; LCSC C97947
D-JACK-CLAMP-1, D-JACK-CLAMP-2, D-JACK-CLAMP-3, D-JACK-CLAMP-4: BAV99; SOT-23; MPN BAV99,215; LCSC C2500
R1-1, R1-2, R1-3, R1-4: 10k 1%; R_0805_2012Metric; MPN RT0805BRD0710KL; LCSC C110775
R2-1, R2-2, R2-3, R2-4: 30k 1%; R_0805_2012Metric; MPN RT0805BRD0730KL; LCSC C728649
R-BIAS-DAC-1, R-BIAS-DAC-2, R-BIAS-DAC-3, R-BIAS-DAC-4: 100k 1%; R_0805_2012Metric; MPN 0805W8F1003T5E; LCSC C149504
R-BIAS-DAC-CH7: 100k 1%; R_0805_2012Metric; MPN 0805W8F1003T5E; LCSC C149504
R-OPAMP-IN-1, R-OPAMP-IN-2, R-OPAMP-IN-3, R-OPAMP-IN-4: 1k 1%; R_0805_2012Metric; MPN 0805W8F1001T5E; LCSC C17513
R-OPAMP-IN-REF: 1k 1%; R_0805_2012Metric; MPN 0805W8F1001T5E; LCSC C17513
R-OUT-PROT-1, R-OUT-PROT-2, R-OUT-PROT-3, R-OUT-PROT-4: 1k 1%, >=500mW; R_1206_3216Metric; MPN ERJ-P08F1001V; LCSC C4261071
U-MOD-A: OPA2197; SOIC-8_3.9x4.9mm_P1.27mm; MPN OPA2197IDR; LCSC C139363
U-MOD-B: OPA2197; SOIC-8_3.9x4.9mm_P1.27mm; MPN OPA2197IDR; LCSC C139363
U-MOD-C: OPA2197; SOIC-8_3.9x4.9mm_P1.27mm; MPN OPA2197IDR; LCSC C139363

Connections:
AGND_MOD: C-DEC-MODA-NEG.2, C-DEC-MODA-POS.2, C-DEC-MODB-NEG.2, C-DEC-MODB-POS.2, C-DEC-MODC-NEG.2, C-DEC-MODC-POS.2, C-FILT-MOD-1.2, C-FILT-MOD-2.2, C-FILT-MOD-3.2, C-FILT-MOD-4.2, R-BIAS-DAC-1.2, R-BIAS-DAC-2.2, R-BIAS-DAC-3.2, R-BIAS-DAC-4.2, R-BIAS-DAC-CH7.2, U-MOD-C.5 (+)
DAC_CH2: R-BIAS-DAC-1.1, R-OPAMP-IN-1.1
DAC_CH3: R-BIAS-DAC-2.1, R-OPAMP-IN-2.1
DAC_CH4: R-BIAS-DAC-3.1, R-OPAMP-IN-3.1
DAC_CH5: R-BIAS-DAC-4.1, R-OPAMP-IN-4.1
DAC_CH7: R-BIAS-DAC-CH7.1, R-OPAMP-IN-REF.1
MINUS_1: R1-1.2, R2-1.1, U-MOD-A.6 (-)
MINUS_2: R1-2.2, R2-2.1, U-MOD-B.2 (-)
MINUS_3: R1-3.2, R2-3.1, U-MOD-B.6 (-)
MINUS_4: R1-4.2, R2-4.1, U-MOD-C.2 (-)
MOD1_JACK: C-FILT-MOD-1.1, R-OUT-PROT-1.2
MOD2_JACK: C-FILT-MOD-2.1, R-OUT-PROT-2.2
MOD3_JACK: C-FILT-MOD-3.1, R-OUT-PROT-3.2
MOD4_JACK: C-FILT-MOD-4.1, R-OUT-PROT-4.2
MODULE_ANALOG_NEG12: C-DEC-MODA-NEG.1, C-DEC-MODB-NEG.1, C-DEC-MODC-NEG.1, D-JACK-CLAMP-1.1 (A), D-JACK-CLAMP-2.1 (A), D-JACK-CLAMP-3.1 (A), D-JACK-CLAMP-4.1 (A), U-MOD-A.4 (V-), U-MOD-B.4 (V-), U-MOD-C.4 (V-)
MODULE_ANALOG_POS12: C-DEC-MODA-POS.1, C-DEC-MODB-POS.1, C-DEC-MODC-POS.1, D-JACK-CLAMP-1.2 (K), D-JACK-CLAMP-2.2 (K), D-JACK-CLAMP-3.2 (K), D-JACK-CLAMP-4.2 (K), U-MOD-A.8 (V+), U-MOD-B.8 (V+), U-MOD-C.8 (V+)
OUT_1: D-JACK-CLAMP-1.3 (common), R2-1.2, R-OUT-PROT-1.1, U-MOD-A.7
OUT_2: D-JACK-CLAMP-2.3 (common), R2-2.2, R-OUT-PROT-2.1, U-MOD-B.1
OUT_3: D-JACK-CLAMP-3.3 (common), R2-3.2, R-OUT-PROT-3.1, U-MOD-B.7
OUT_4: D-JACK-CLAMP-4.3 (common), R2-4.2, R-OUT-PROT-4.1, U-MOD-C.1
PLUS_1: R-OPAMP-IN-1.2, U-MOD-A.5 (+)
PLUS_2: R-OPAMP-IN-2.2, U-MOD-B.3 (+)
PLUS_3: R-OPAMP-IN-3.2, U-MOD-B.5 (+)
PLUS_4: R-OPAMP-IN-4.2, U-MOD-C.3 (+)
REF_PLUS: R-OPAMP-IN-REF.2, U-MOD-A.3 (+)
SPARE_C_OUT: U-MOD-C.6 (-), U-MOD-C.7
VREF_MOD: R1-1.1, R1-2.1, R1-3.1, R1-4.1, U-MOD-A.1, U-MOD-A.2 (-)
