jeffmhopkins/Woody/hardware/module/panel-led/panel-led.kicad_sch

## KiCad design hardware/module/panel-led/panel-led.kicad_sch (2026-09-30)

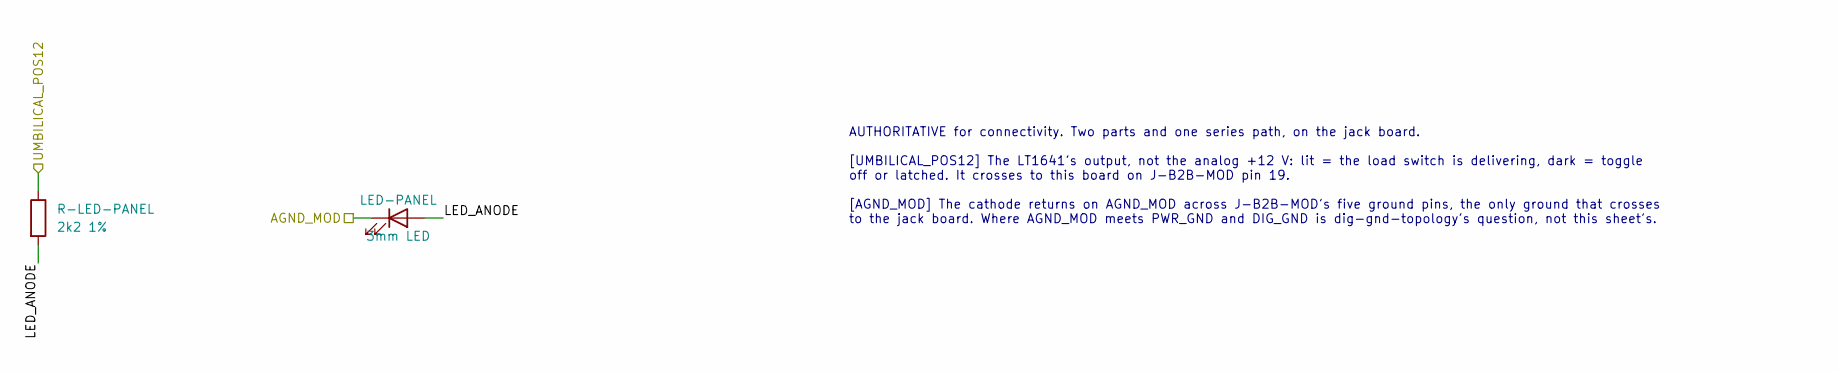
[picture p210: schematic panel-led.kicad_sch]

Parts:
LED-PANEL: 3mm LED; LED_D3.0mm; MPN LTL-4231N; LCSC C125082
R-LED-PANEL: 2k2 1%; R_0805_2012Metric; MPN 0805W8F2201T5E; LCSC C17520

Connections:
AGND_MOD: LED-PANEL.1 (K)
LED_ANODE: LED-PANEL.2 (A), R-LED-PANEL.2
UMBILICAL_POS12: R-LED-PANEL.1

Notes on the sheet:
AUTHORITATIVE for connectivity. Two parts and one series path, on the jack board. [UMBILICAL_POS12] The LT1641's output, not the analog +12 V: lit = the load switch is delivering, dark = toggle off or latched. It crosses to this board on J-B2B-MOD pin 19. [AGND_MOD] The cathode returns on AGND_MOD 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
