jeffmhopkins/Woody/hardware/module/pitch-stage/pitch-stage.main.kicad_sch

## KiCad design hardware/module/pitch-stage/pitch-stage.main.kicad_sch (2026-09-30)

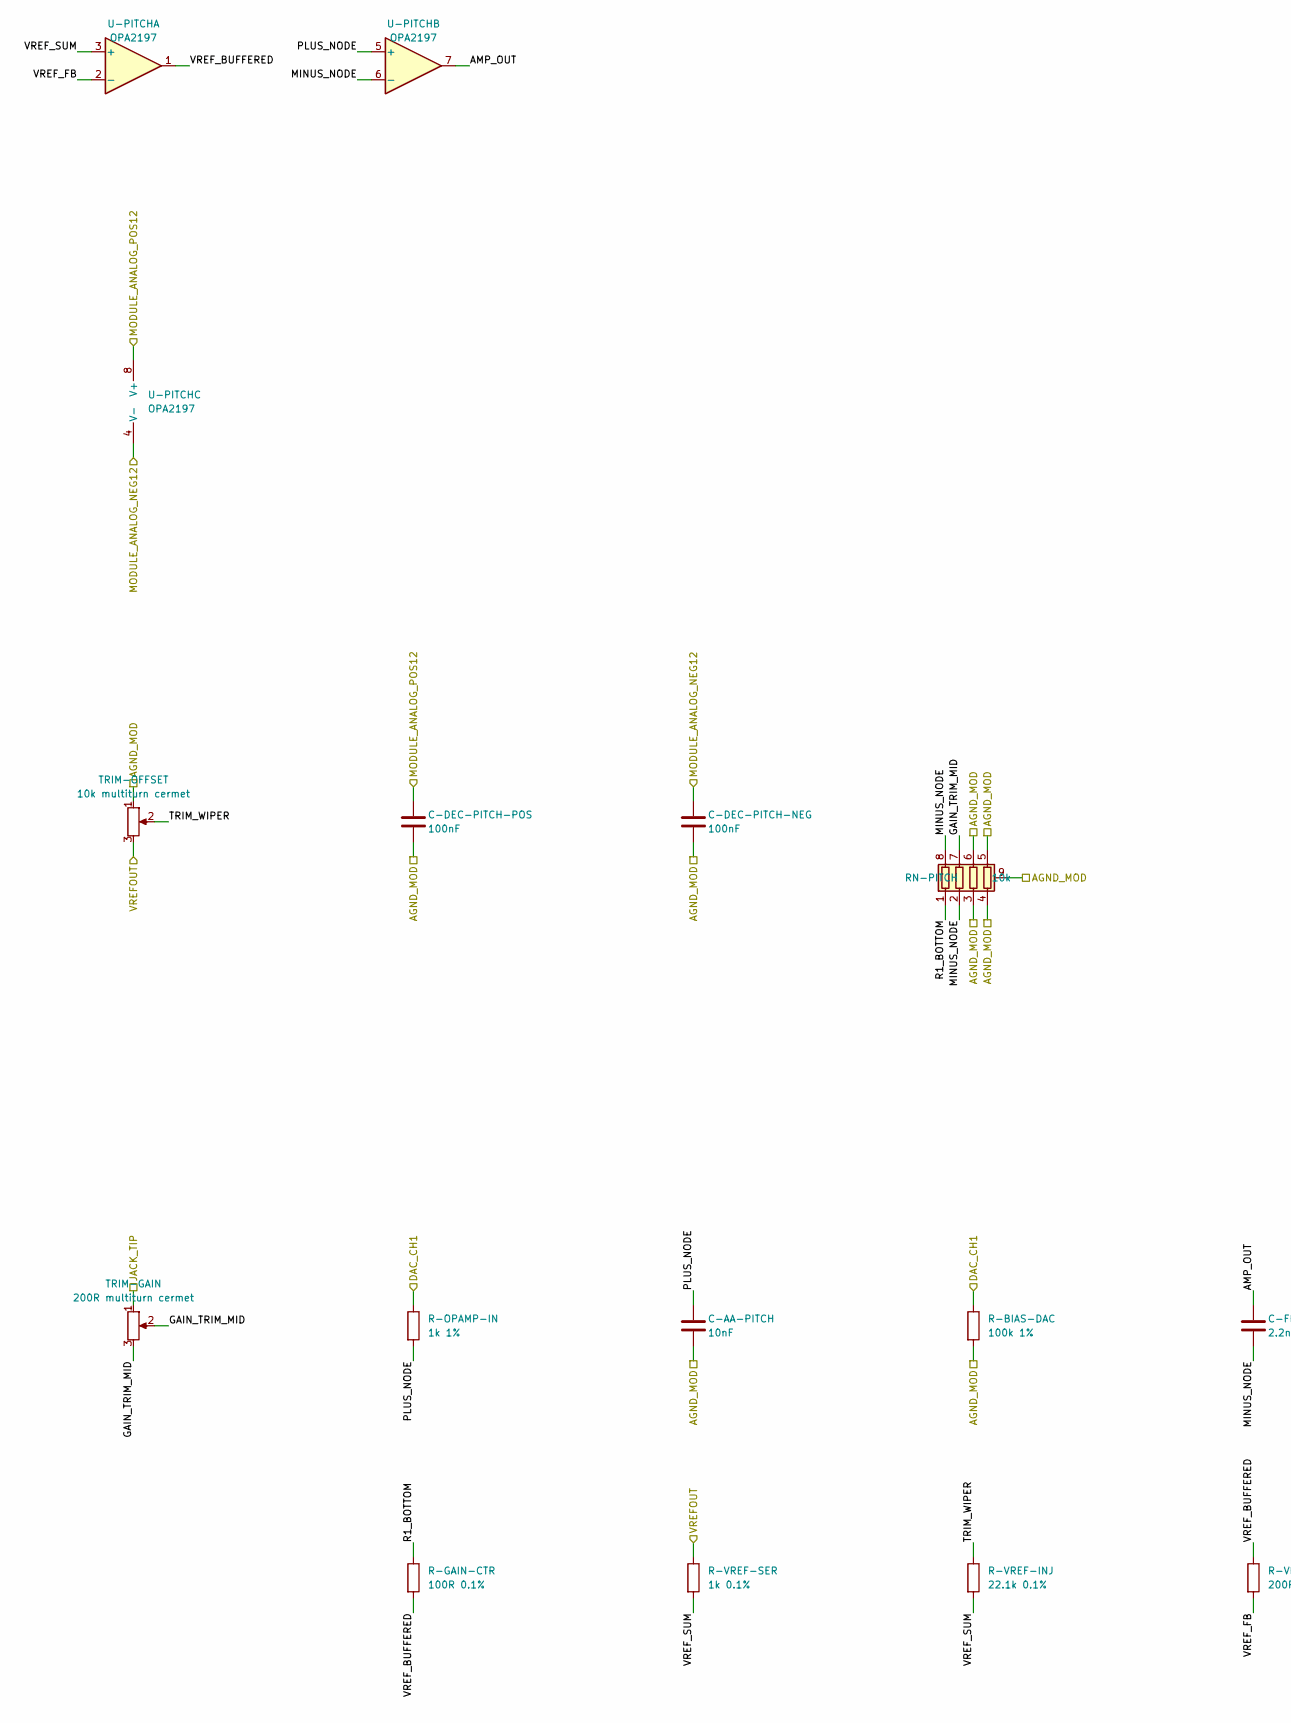
[picture p211: schematic pitch-stage.main.kicad_sch, part in row 1, column 1]

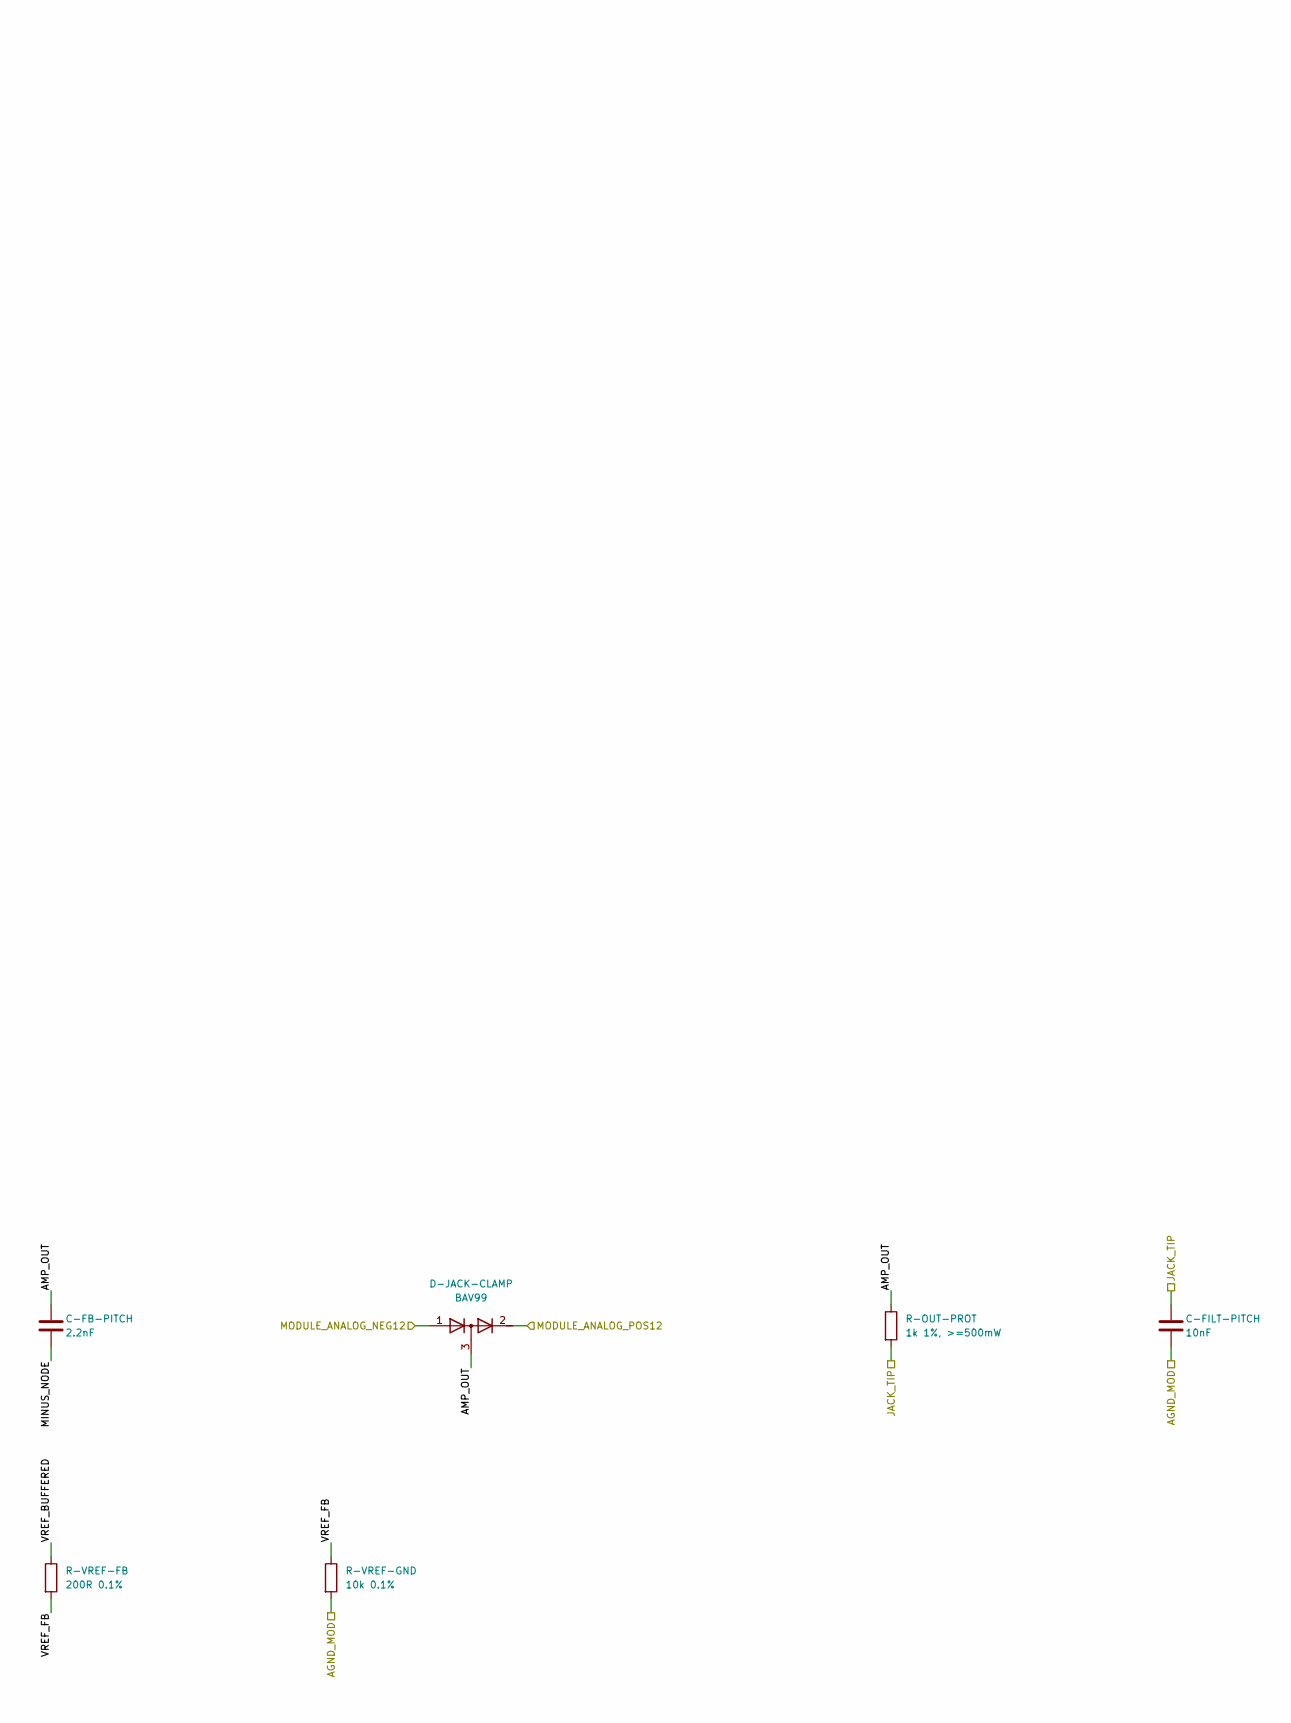
[picture p212: schematic pitch-stage.main.kicad_sch, part in row 1, column 2]

Parts:
C-AA-PITCH: 10nF; C_0805_2012Metric; MPN CL21C103JBFNNNE; LCSC C27071
C-DEC-PITCH-NEG: 100nF; C_0805_2012Metric; MPN CC0805KRX7R9BB104; LCSC C49678
C-DEC-PITCH-POS: 100nF; C_0805_2012Metric; MPN CC0805KRX7R9BB104; LCSC C49678
C-FB-PITCH: 2.2nF; C_0805_2012Metric; MPN CL21C222JBFNNNE; LCSC C28260
C-FILT-PITCH: 10nF; C_0805_2012Metric; MPN CL21C103JBFNNNE; LCSC C27071
D-JACK-CLAMP: BAV99; SOT-23; MPN BAV99,215; LCSC C2500
R-BIAS-DAC: 100k 1%; R_0805_2012Metric; MPN 0805W8F1003T5E; LCSC C149504
R-GAIN-CTR: 100R 0.1%; R_0805_2012Metric; MPN RT0805BRD07100RL; LCSC C110773
R-OPAMP-IN: 1k 1%; R_0805_2012Metric; MPN 0805W8F1001T5E; LCSC C17513
R-OUT-PROT: 1k 1%, >=500mW; R_1206_3216Metric; MPN ERJ-P08F1001V; LCSC C4261071
R-VREF-FB: 200R 0.1%; R_0805_2012Metric; MPN RT0805BRD07200RL; LCSC C865287
R-VREF-GND: 10k 0.1%; R_0805_2012Metric; MPN RT0805BRD0710KL; LCSC C110775
R-VREF-INJ: 22.1k 0.1%; R_0805_2012Metric; MPN RT0805BRD0722K1L; LCSC C865310
R-VREF-SER: 1k 0.1%; R_0805_2012Metric; MPN RT0805BRD071KL; LCSC C110774
RN-PITCH: 10k; MSOP-8-1EP_3x3mm_P0.65mm_EP1.68x1.88mm; MPN LT5400BIMS8E-1#PBF; LCSC C42416907
TRIM-GAIN: 200R multiturn cermet; Potentiometer_Bourns_3296W_Vertical; MPN 3296W-1-201LF; LCSC C83685
TRIM-OFFSET: 10k multiturn cermet; Potentiometer_Bourns_3296W_Vertical; MPN 3296W-1-103LF; LCSC C34846
U-PITCH: OPA2197; SOIC-8_3.9x4.9mm_P1.27mm; MPN OPA2197IDR; LCSC C139363

Connections:
AGND_MOD: C-AA-PITCH.2, C-DEC-PITCH-NEG.2, C-DEC-PITCH-POS.2, C-FILT-PITCH.2, R-BIAS-DAC.2, R-VREF-GND.2, RN-PITCH.3 (R3.1), RN-PITCH.4 (R4.1), RN-PITCH.5 (R4.2), RN-PITCH.6 (R3.2), RN-PITCH.9 (EP), TRIM-OFFSET.1
AMP_OUT: C-FB-PITCH.1, D-JACK-CLAMP.3 (common), R-OUT-PROT.1, U-PITCH.7
DAC_CH1: R-BIAS-DAC.1, R-OPAMP-IN.1
GAIN_TRIM_MID: RN-PITCH.7 (R2.2), TRIM-GAIN.2, TRIM-GAIN.3
JACK_TIP: C-FILT-PITCH.1, R-OUT-PROT.2, TRIM-GAIN.1
MINUS_NODE: C-FB-PITCH.2, RN-PITCH.2 (R2.1), RN-PITCH.8 (R1.2), U-PITCH.6 (-)
MODULE_ANALOG_NEG12: C-DEC-PITCH-NEG.1, D-JACK-CLAMP.1 (A), U-PITCH.4 (V-)
MODULE_ANALOG_POS12: C-DEC-PITCH-POS.1, D-JACK-CLAMP.2 (K), U-PITCH.8 (V+)
PLUS_NODE: C-AA-PITCH.1, R-OPAMP-IN.2, U-PITCH.5 (+)
R1_BOTTOM: R-GAIN-CTR.1, RN-PITCH.1 (R1.1)
TRIM_WIPER: R-VREF-INJ.1, TRIM-OFFSET.2
VREFOUT: R-VREF-SER.1, TRIM-OFFSET.3
VREF_BUFFERED: R-GAIN-CTR.2, R-VREF-FB.1, U-PITCH.1
VREF_FB: R-VREF-FB.2, R-VREF-GND.1, U-PITCH.2 (-)
VREF_SUM: R-VREF-INJ.2, R-VREF-SER.2, U-PITCH.3 (+)
