jeffmhopkins/Woody/hardware/module/power-entry/power-entry.kicad_sch

## KiCad design hardware/module/power-entry/power-entry.kicad_sch (2026-09-30)

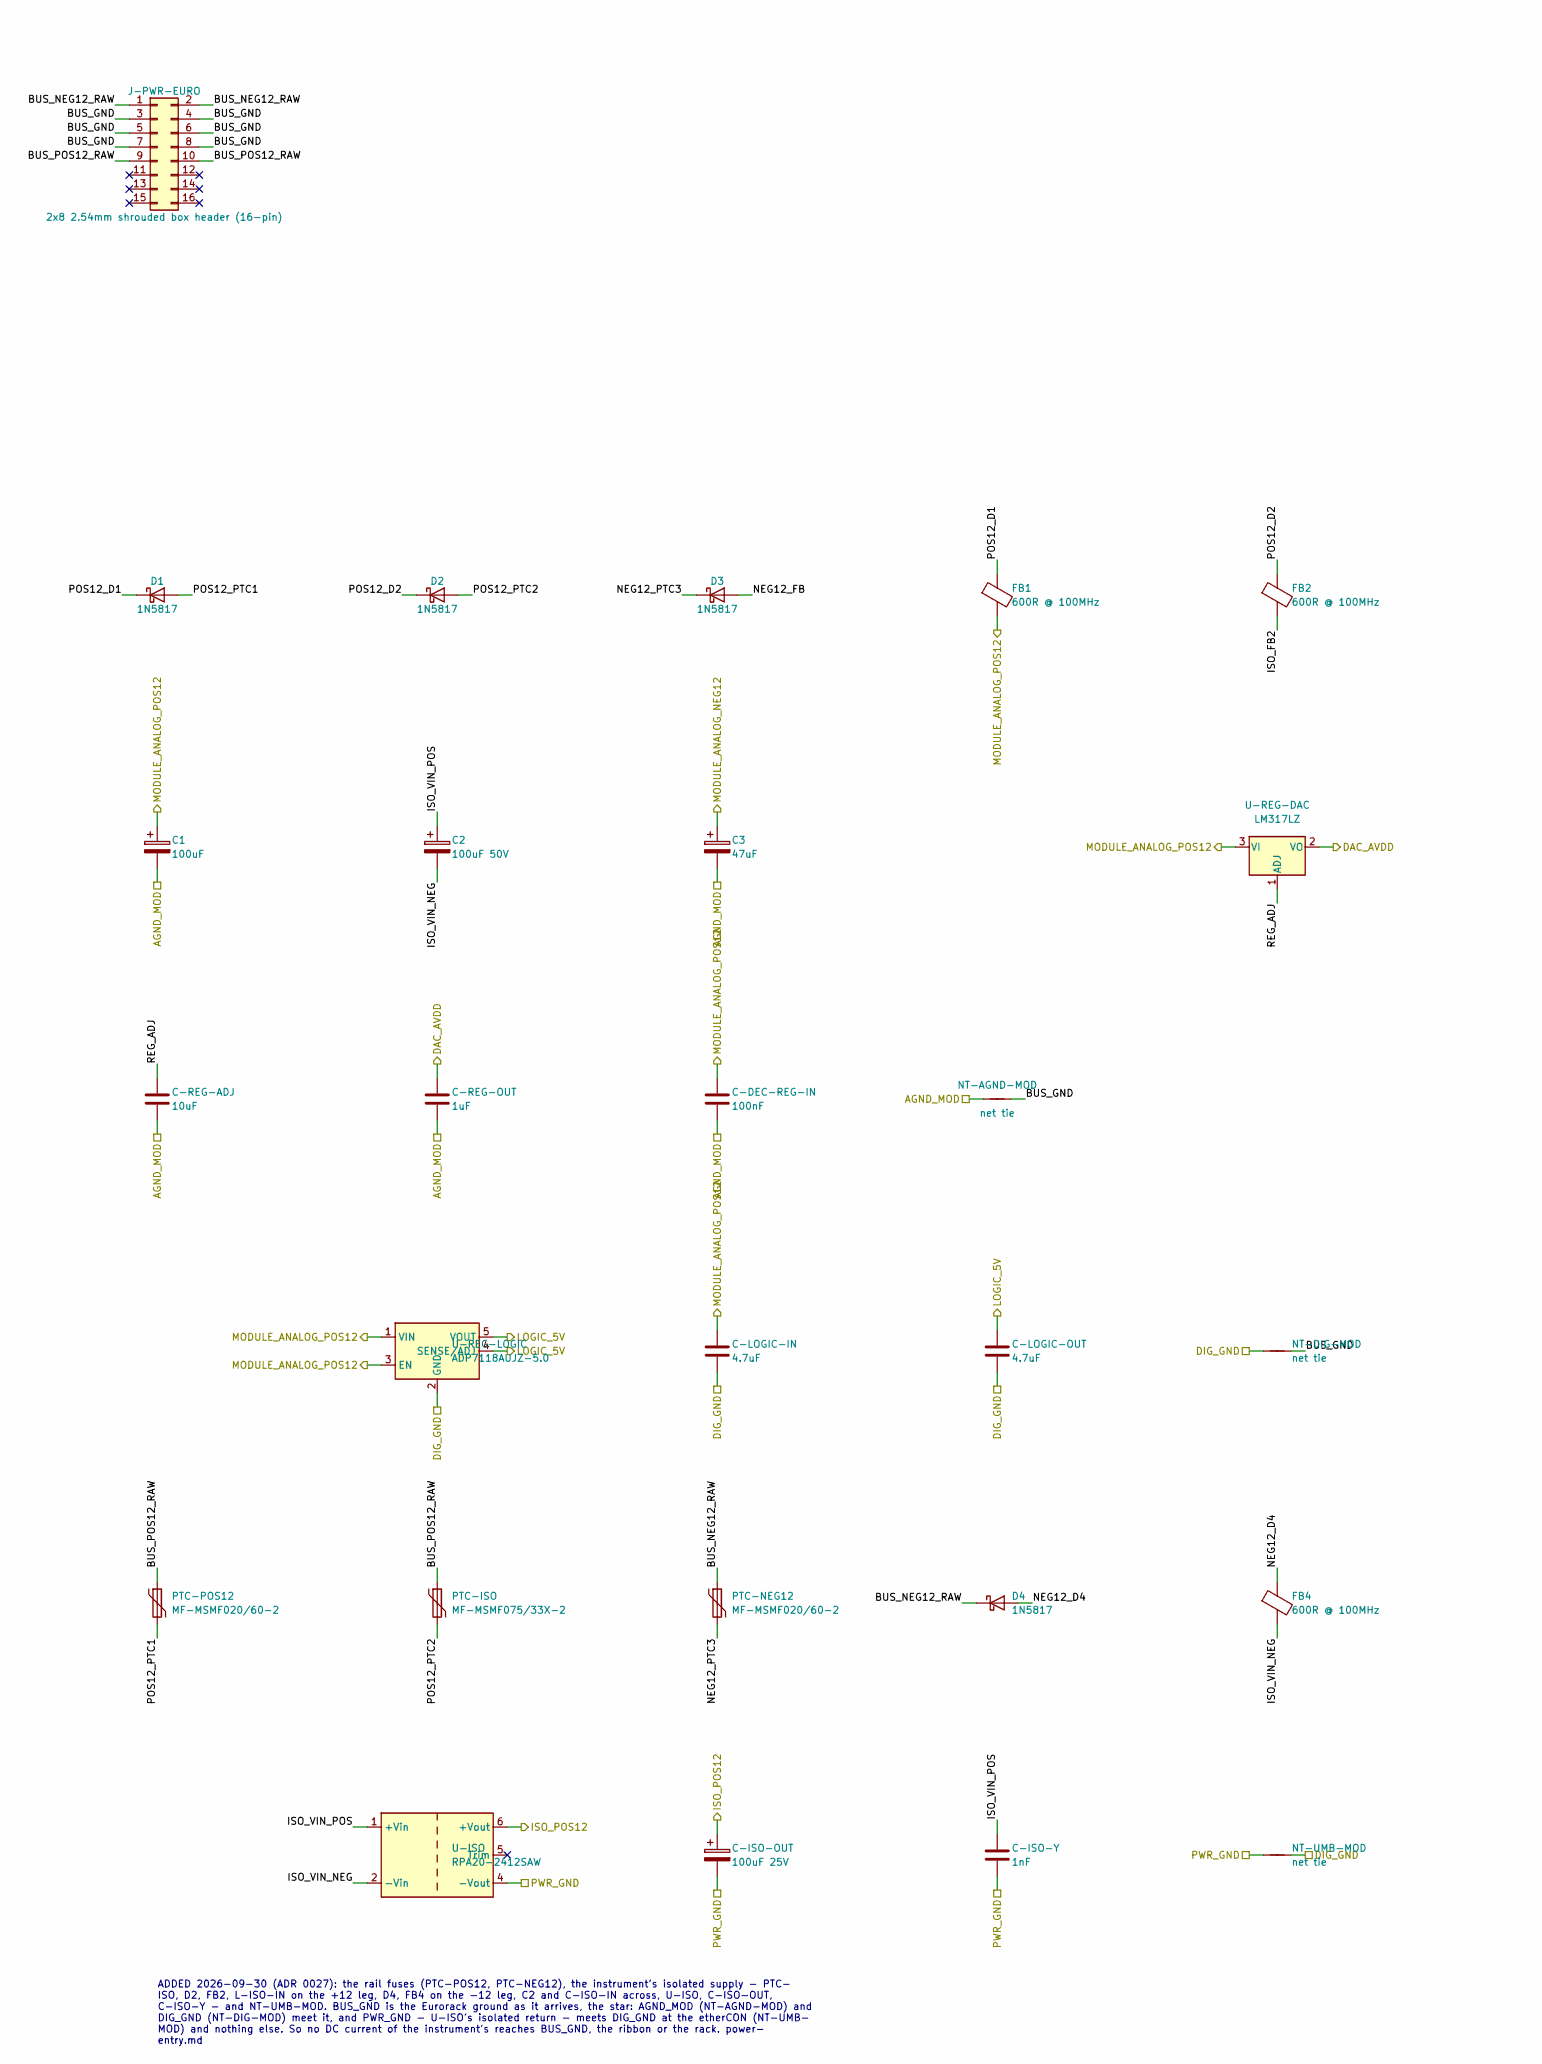
[picture p213: schematic power-entry.kicad_sch, part in row 1, column 1]

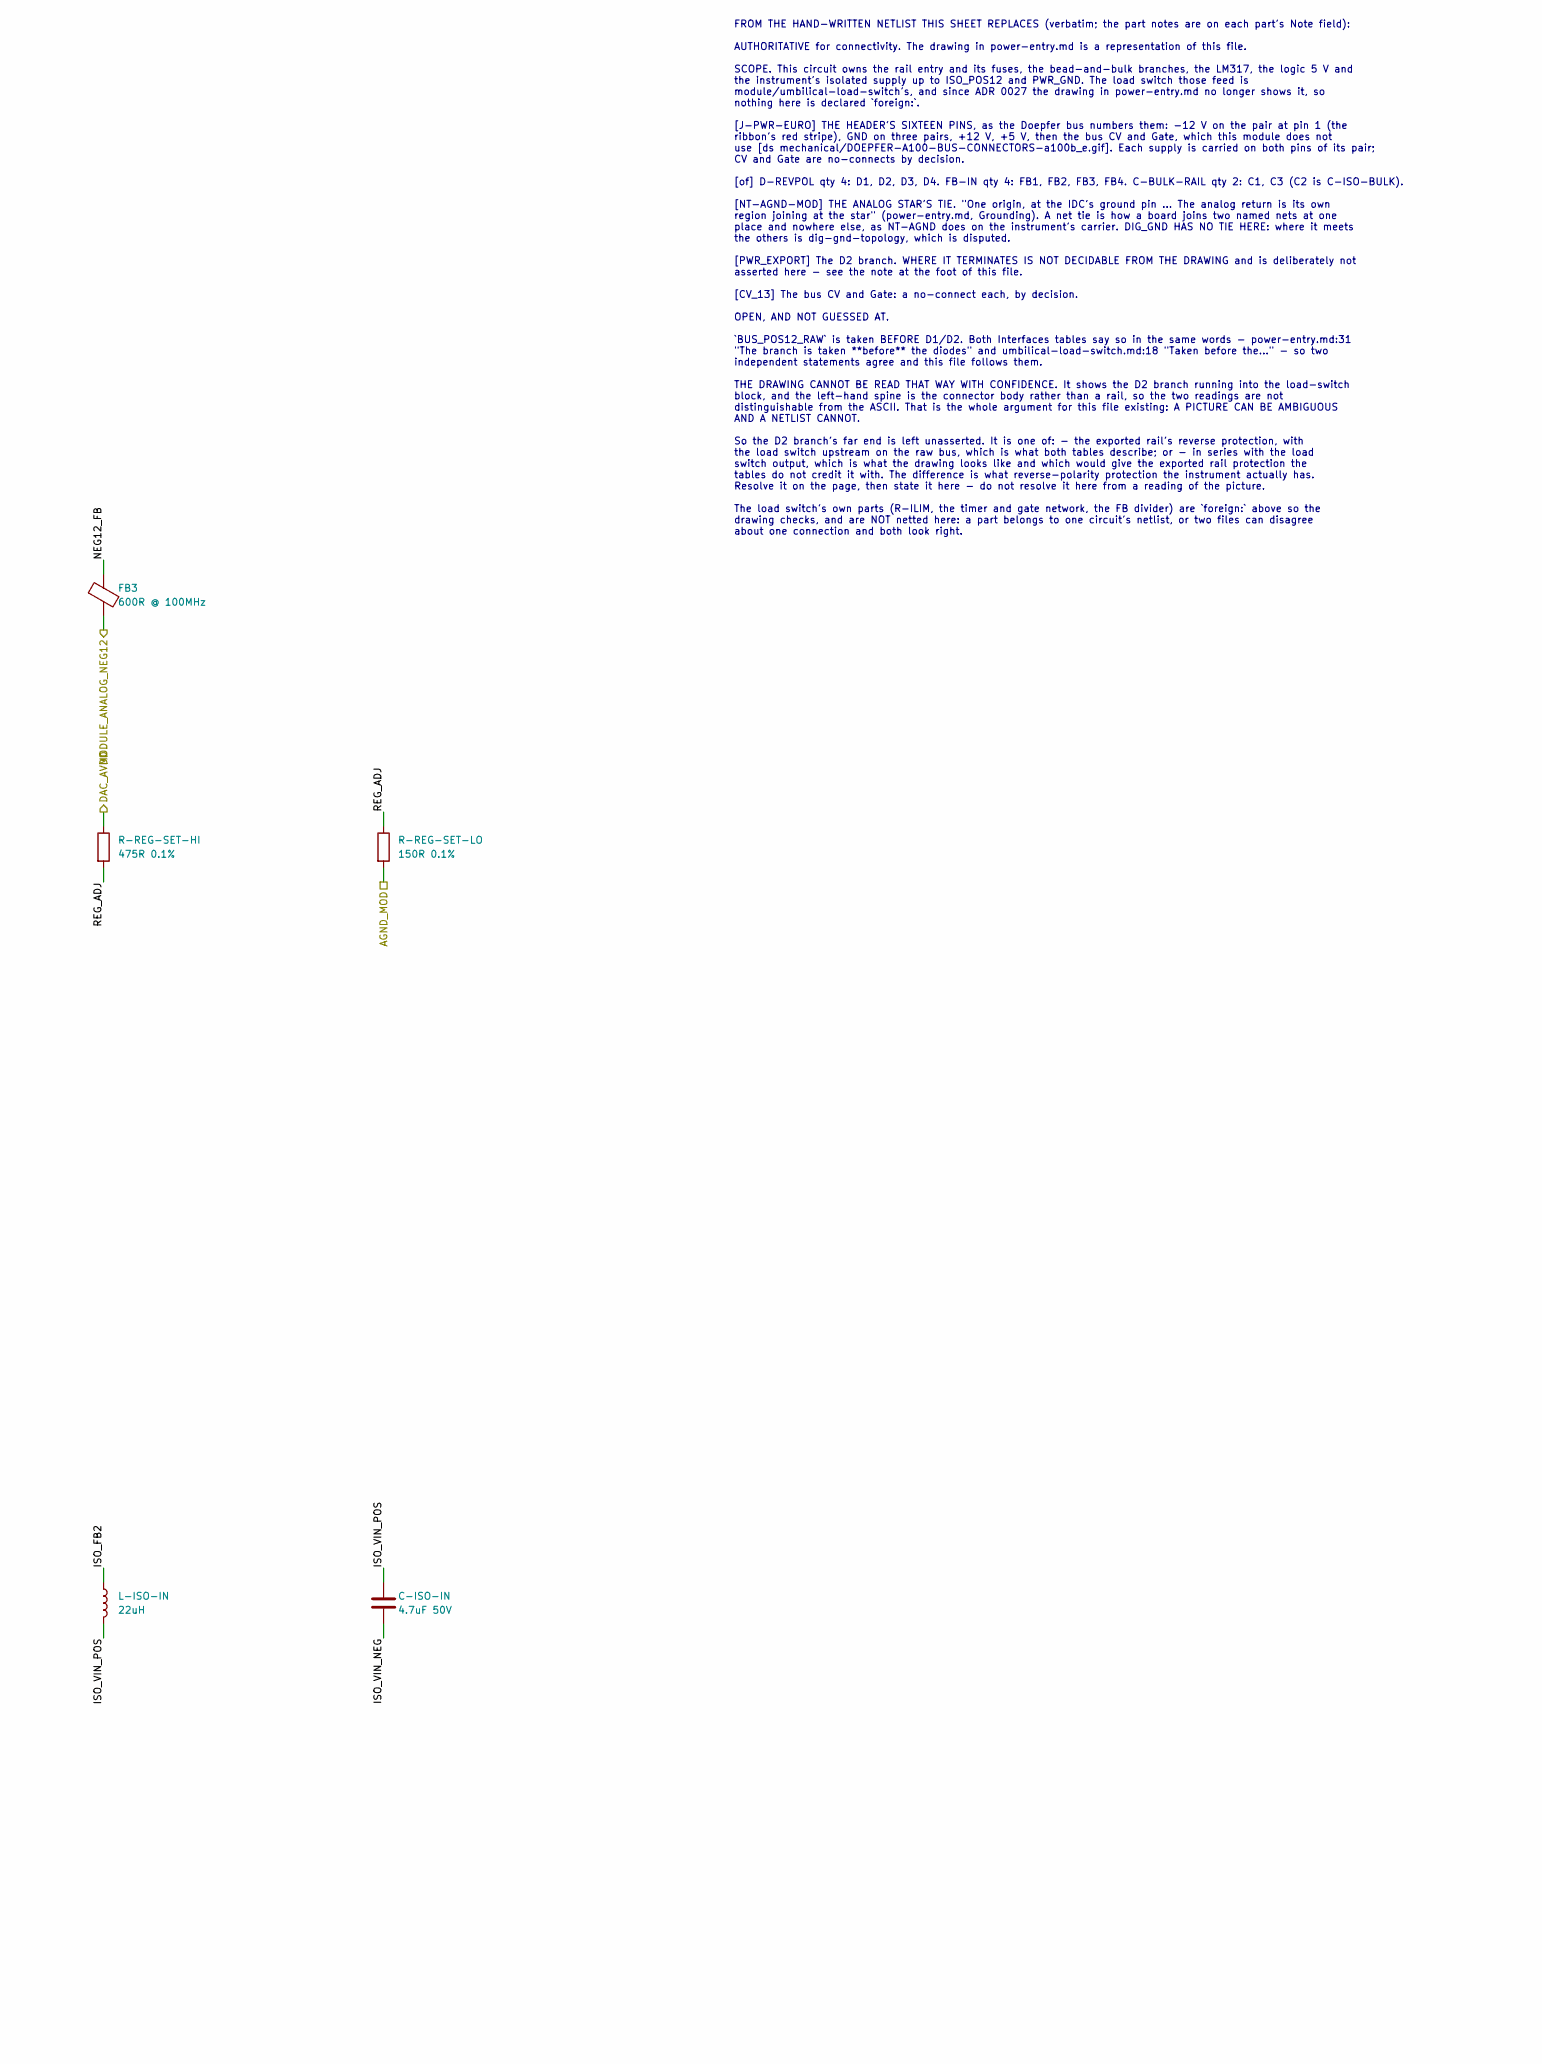
[picture p214: schematic power-entry.kicad_sch, part in row 1, column 2]

Parts:
C1: 100uF; CP_Radial_D6.3mm_P2.50mm; MPN NXA25V100M6.3*11 2.5TP; LCSC C165558
C2: 100uF 50V; CP_Elec_6.3x7.7; MPN UCM1H101MCL1GS
C3: 47uF; CP_Radial_D5.0mm_P2.00mm; MPN NXB25V47M5*11 2.5TP; LCSC C371230
C-DEC-REG-IN: 100nF; C_0805_2012Metric; MPN CC0805KRX7R9BB104; LCSC C49678
C-ISO-IN: 4.7uF 50V; C_1206_3216Metric; MPN CC1206KKX7R9BB475; LCSC C132170
C-ISO-OUT: 100uF 25V; CP_Elec_6.3x5.8; MPN UCM1E101MCL1GS; LCSC C729678
C-ISO-Y: 1nF; C_0805_2012Metric; MPN CC0805JRNPO9BN102; LCSC C62774
C-LOGIC-IN: 4.7uF; C_1206_3216Metric; MPN CC1206KKX7R9BB475; LCSC C132170
C-LOGIC-OUT: 4.7uF; C_1206_3216Metric; MPN CC1206KKX7R9BB475; LCSC C132170
C-REG-ADJ: 10uF; C_0805_2012Metric; MPN CL21A106KAYNNNE; LCSC C15850
C-REG-OUT: 1uF; C_0805_2012Metric; MPN CL21B105KBFNNNE; LCSC C28323
D1, D2, D3, D4: 1N5817; D_DO-41_SOD81_P10.16mm_Horizontal; MPN 1N5817-T; LCSC C507852
FB1, FB2, FB3, FB4: 600R @ 100MHz; L_1206_3216Metric; MPN MI1206K601R-10; LCSC C2441375
J-PWR-EURO: 2x8 2.54mm shrouded box header (16-pin); IDC-Header_2x08_P2.54mm_Vertical; MPN BH254V-16P; LCSC C492443
L-ISO-IN: 22uH; L_Sunlord_SWPA6028S; MPN SWPA6028S220MT; LCSC C51349
NT-AGND-MOD: net tie; NetTie-2_SMD_Pad0.5mm
NT-DIG-MOD: net tie; NetTie-2_SMD_Pad0.5mm
NT-UMB-MOD: net tie; NetTie-2_SMD_Pad0.5mm
PTC-ISO: MF-MSMF075/33X-2; Fuse_1812_4532Metric; MPN MF-MSMF075/33X-2; LCSC C3760814
PTC-NEG12: MF-MSMF020/60-2; Fuse_1812_4532Metric; MPN MF-MSMF020/60-2; LCSC C719178
PTC-POS12: MF-MSMF020/60-2; Fuse_1812_4532Metric; MPN MF-MSMF020/60-2; LCSC C719178
R-REG-SET-HI: 475R 0.1%; R_0805_2012Metric; MPN TC0525B4750T5G; LCSC C50670161
R-REG-SET-LO: 150R 0.1%; R_0805_2012Metric; MPN RT0805BRD07150RL; LCSC C513734
U-ISO: RPA20-2412SAW; Converter_DCDC_RECOM_RPA20-RP20-xxxxSAW_THT; MPN RPA20-2412SAW
U-REG-DAC: LM317LZ; TO-92_Inline; MPN LM317LZ; LCSC C5267874
U-REG-LOGIC: ADP7118AUJZ-5.0; TSOT-23-5; MPN ADP7118AUJZ-5.0-R7; LCSC C141943

Connections:
AGND_MOD: C1.2, C3.2, C-DEC-REG-IN.2, C-REG-ADJ.2, C-REG-OUT.2, NT-AGND-MOD.1, R-REG-SET-LO.2
BUS_GND: J-PWR-EURO.3, J-PWR-EURO.4, J-PWR-EURO.5, J-PWR-EURO.6, J-PWR-EURO.7, J-PWR-EURO.8, NT-AGND-MOD.2, NT-DIG-MOD.2
BUS_NEG12_RAW: D4.1 (K), J-PWR-EURO.1, J-PWR-EURO.2, PTC-NEG12.1
BUS_POS12_RAW: J-PWR-EURO.9, J-PWR-EURO.10, PTC-ISO.1, PTC-POS12.1
DAC_AVDD: C-REG-OUT.1, R-REG-SET-HI.1, U-REG-DAC.2 (VO)
DIG_GND: C-LOGIC-IN.2, C-LOGIC-OUT.2, NT-DIG-MOD.1, NT-UMB-MOD.2, U-REG-LOGIC.2 (GND)
ISO_FB2: FB2.2, L-ISO-IN.1
ISO_POS12: C-ISO-OUT.1, U-ISO.6 (+Vout)
ISO_VIN_NEG: C2.2, C-ISO-IN.2, FB4.2, U-ISO.2 (-Vin)
ISO_VIN_POS: C2.1, C-ISO-IN.1, C-ISO-Y.1, L-ISO-IN.2, U-ISO.1 (+Vin)
LOGIC_5V: C-LOGIC-OUT.1, U-REG-LOGIC.4 (SENSE/ADJ), U-REG-LOGIC.5 (VOUT)
MODULE_ANALOG_NEG12: C3.1, FB3.2
MODULE_ANALOG_POS12: C1.1, C-DEC-REG-IN.1, C-LOGIC-IN.1, FB1.2, U-REG-DAC.3 (VI), U-REG-LOGIC.1 (VIN), U-REG-LOGIC.3 (EN)
NEG12_D4: D4.2 (A), FB4.1
NEG12_FB: D3.2 (A), FB3.1
NEG12_PTC3: D3.1 (K), PTC-NEG12.2
POS12_D1: D1.1 (K), FB1.1
POS12_D2: D2.1 (K), FB2.1
POS12_PTC1: D1.2 (A), PTC-POS12.2
POS12_PTC2: D2.2 (A), PTC-ISO.2
PWR_GND: C-ISO-OUT.2, C-ISO-Y.2, NT-UMB-MOD.1, U-ISO.4 (-Vout)
REG_ADJ: C-REG-ADJ.1, R-REG-SET-HI.2, R-REG-SET-LO.1, U-REG-DAC.1 (ADJ)

Notes on the sheet:
FROM THE HAND-WRITTEN NETLIST THIS SHEET REPLACES (verbatim; the part notes are on each part's Note field): AUTHORITATIVE for connectivity. The drawing in power-entry.md is a representation of this file. SCOPE. This circuit owns the rail entry and its fuses, the bead-and-bulk branches, the LM317, t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
ADDED 2026-09-30 (ADR 0027): the rail fuses (PTC-POS12, PTC-NEG12), the instrument's isolated supply - PTC- ISO, D2, FB2, L-ISO-IN on the +12 leg, D4, FB4 on the -12 leg, C2 and C-ISO-IN across, U-ISO, C-ISO-OUT, C-ISO-Y - and NT-UMB-MOD. BUS_GND is the Eurorack ground as it arrives, the star: AGND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
