jeffmhopkins/Woody/hardware/module/umbilical-load-switch/umbilical-load-switch.kicad_sch

## KiCad design hardware/module/umbilical-load-switch/umbilical-load-switch.kicad_sch (2026-09-30)

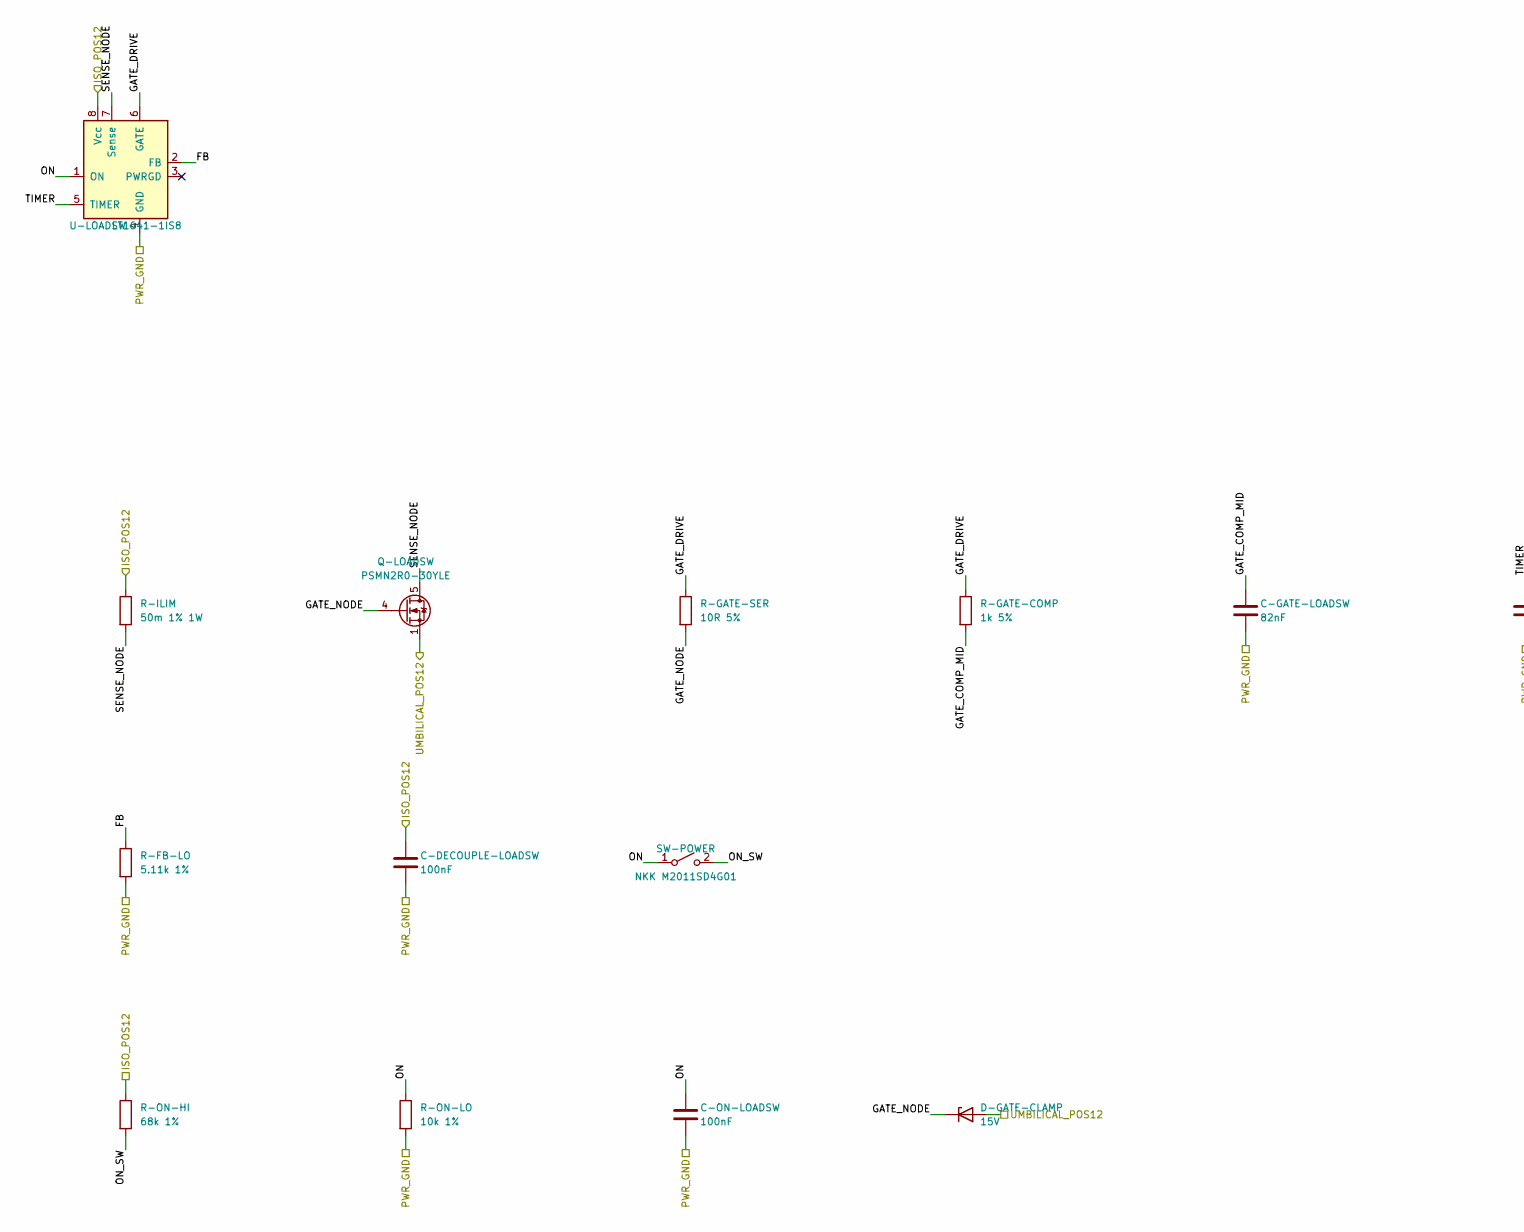
[picture p215: schematic umbilical-load-switch.kicad_sch, part in row 1, column 1]

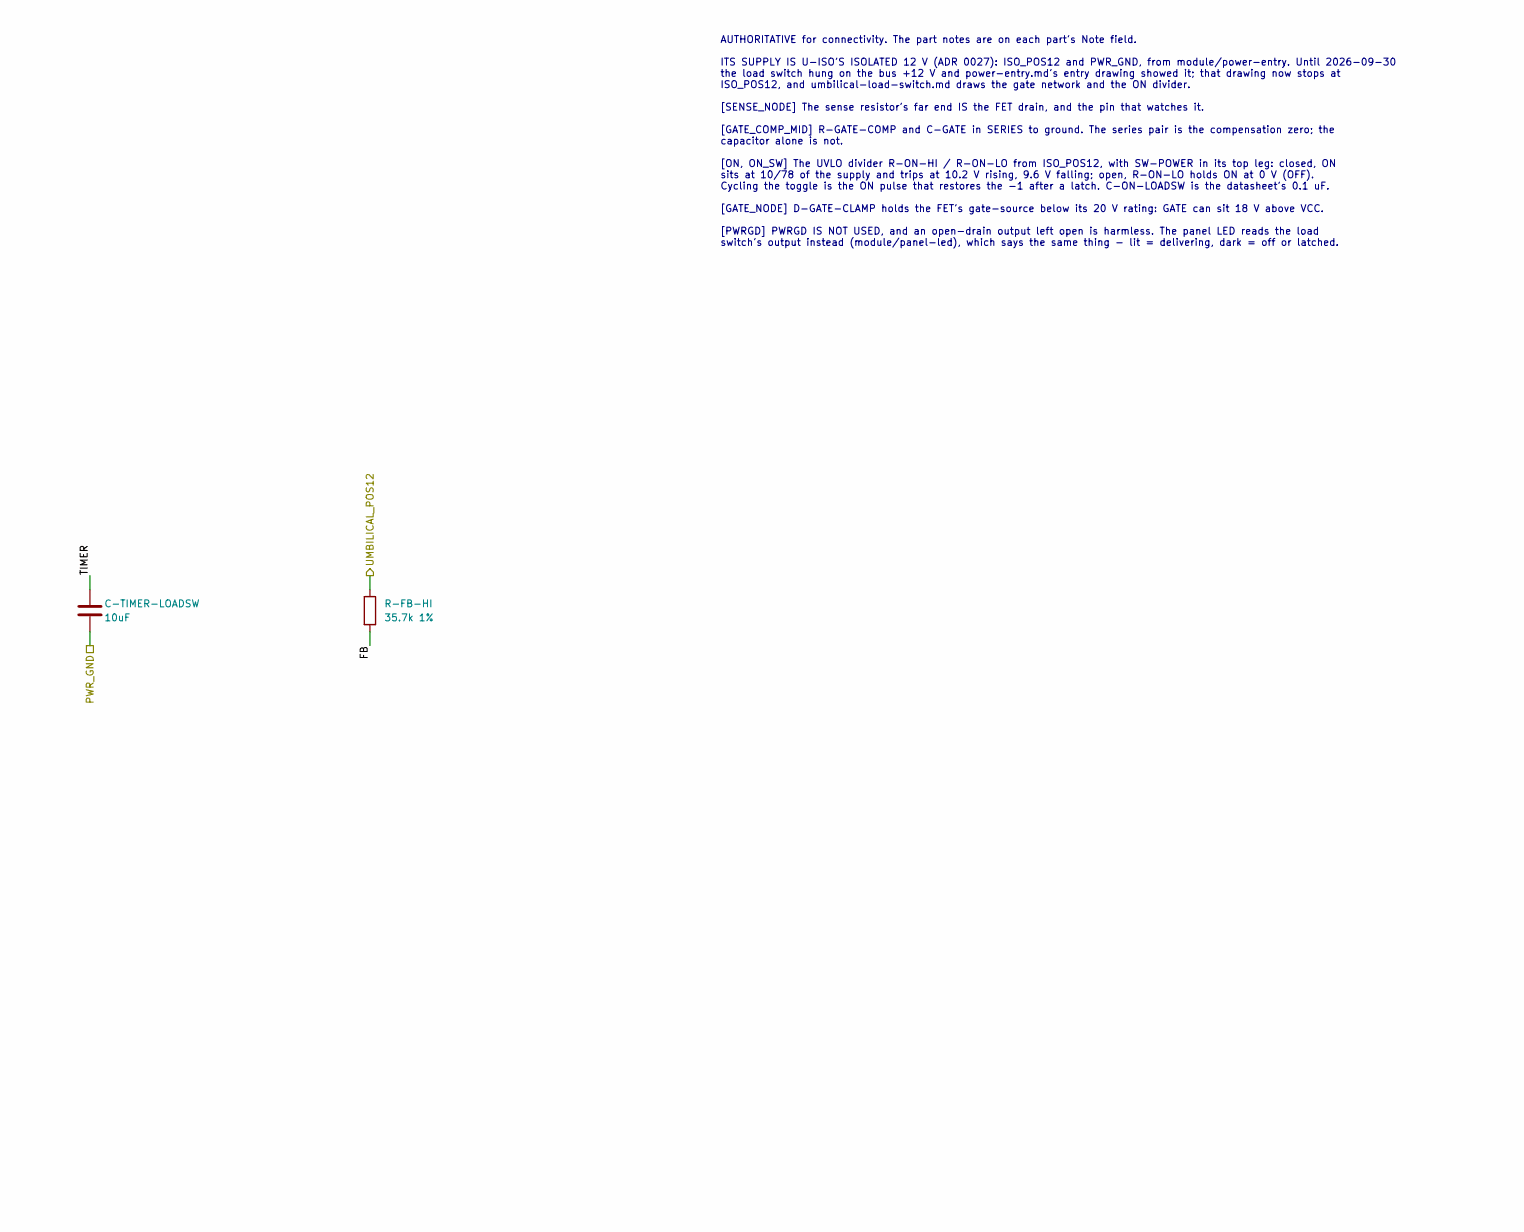
[picture p216: schematic umbilical-load-switch.kicad_sch, part in row 1, column 2]

Parts:
C-DECOUPLE-LOADSW: 100nF; C_0805_2012Metric; MPN CC0805KRX7R9BB104; LCSC C49678
C-GATE-LOADSW: 82nF; C_1206_3216Metric; MPN GRM31C5C1H823JA01L; LCSC C97947
C-ON-LOADSW: 100nF; C_0805_2012Metric; MPN CC0805KRX7R9BB104; LCSC C49678
C-TIMER-LOADSW: 10uF; C_1210_3225Metric; MPN GRM32DR71E106KA12L; LCSC C77100
D-GATE-CLAMP: 15V; D_SOD-123; MPN MMSZ5245BT1G; LCSC C129730
Q-LOADSW: PSMN2R0-30YLE; LFPAK56; MPN PSMN2R0-30YLE,115; LCSC C553247
R-FB-HI: 35.7k 1%; R_0805_2012Metric; MPN PTFR0805B35K7P9; LCSC C2849191
R-FB-LO: 5.11k 1%; R_0805_2012Metric; MPN RT0805BRD075K11L; LCSC C865574
R-GATE-COMP: 1k 5%; R_0805_2012Metric; MPN 0805W8F1001T5E; LCSC C17513
R-GATE-SER: 10R 5%; R_0805_2012Metric; MPN 0805W8F100JT5E; LCSC C17415
R-ILIM: 50m 1% 1W; R_1206_3216Metric; MPN LR1206-21R050F4; LCSC C154645
R-ON-HI: 68k 1%; R_0805_2012Metric; MPN 0805W8F6802T5E; LCSC C17801
R-ON-LO: 10k 1%; R_0805_2012Metric; MPN 0805W8F1002T5E; LCSC C17414
SW-POWER: NKK M2011SD4G01; SolderWire-0.25sqmm_1x02_P4.2mm_D0.65mm_OD1.7mm; MPN M2011SD4G01
U-LOADSW: LT1641-1IS8; SOIC-8_3.9x4.9mm_P1.27mm; MPN LT1641-1IS8#PBF; LCSC C664552

Connections:
FB: R-FB-HI.2, R-FB-LO.1, U-LOADSW.2 (FB)
GATE_COMP_MID: C-GATE-LOADSW.1, R-GATE-COMP.2
GATE_DRIVE: R-GATE-COMP.1, R-GATE-SER.1, U-LOADSW.6 (GATE)
GATE_NODE: D-GATE-CLAMP.1 (K), Q-LOADSW.4 (G), R-GATE-SER.2
ISO_POS12: C-DECOUPLE-LOADSW.1, R-ILIM.1, R-ON-HI.1, U-LOADSW.8 (Vcc)
ON: C-ON-LOADSW.1, R-ON-LO.1, SW-POWER.1 (A), U-LOADSW.1 (ON)
ON_SW: R-ON-HI.2, SW-POWER.2 (B)
PWR_GND: C-DECOUPLE-LOADSW.2, C-GATE-LOADSW.2, C-ON-LOADSW.2, C-TIMER-LOADSW.2, R-FB-LO.2, R-ON-LO.2, U-LOADSW.4 (GND)
SENSE_NODE: Q-LOADSW.5 (D), R-ILIM.2, U-LOADSW.7 (Sense)
TIMER: C-TIMER-LOADSW.1, U-LOADSW.5 (TIMER)
UMBILICAL_POS12: D-GATE-CLAMP.2 (A), Q-LOADSW.1 (S), Q-LOADSW.2 (S), Q-LOADSW.3 (S), R-FB-HI.1

Notes on the sheet:
AUTHORITATIVE for connectivity. The part notes are on each part's Note field. ITS SUPPLY IS U-ISO'S ISOLATED 12 V (ADR 0027): ISO_POS12 and PWR_GND, from module/power-entry. Until 2026-09-30 the load switch hung on the bus +12 V and power-entry.md's entry drawing showed it; that drawing now stops a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
