jeffmhopkins/Woody/tools/sim.py

#!/usr/bin/env python3
"""SPICE simulations of the circuits, built from their own netlists (ngspice).

    python3 tools/sim.py run [<sim dir> ...]   # run every sim/sims.yaml (or those named); write results.yaml
    python3 tools/sim.py check                 # (no ngspice) every results.yaml matches its inputs and passed
    python3 tools/sim.py show <sim dir>        # print a results.yaml as a table

A circuit's `sim/` directory holds `sims.yaml` - what is simulated, what each run
must show, and why - and the deck templates it names. **No part value is written
in a sim.** Each deck's `{{R-KEY-PU}}` is read from the circuit's netlist.yaml
(exported from its KiCad sheet), so a value changed on the sheet reaches the
simulation, and `check` fails until the sims are re-run on it. Model parameters
that are not part values (a threshold ratio, an input capacitance) live in
`params:`, each with its source; figures are cited as `fig['key-release-time']`
from config/figures.yaml, never restated - in an assertion, or as a param's value,
`value: {fig: umbilical-current}` (its leading number in SI, hashed as an input).

CORNERS, NOT A GUESS. Every parameter in `vary:` has a relative range about its
nominal. Each sim runs at the nominal and at every combination of the range ends
(2^n corners), and each measure is reported at the nominal, its minimum and its
maximum, with the corner that gave each. For these circuits - RC networks and
thresholds, monotonic in every parameter - the corners bound the result; a
Monte Carlo would only fill in the middle.

WHAT A RESULT IS WORTH. A SPICE run proves the arithmetic and the wiring against
the models it was given, no more. Where a model is behavioural (a Schmitt input
as its thresholds, a switch as two resistances) sims.yaml says so, and the
thresholds are the datasheet's, not a model's. `results.yaml` is GENERATED: it
records the ngspice version, a hash of every input, every measure and every
assertion's outcome; `check` recomputes the hashes, so a changed value, deck,
figure or this tool marks the results stale.

A board's sims.yaml may also `generate: board` a deck from its board-netlist.yaml:
every part on the board by its BOM row (`parts:` says what each row is in SPICE),
the nets the rest of the chain drives (`drive:`), so a wiring or value mistake on
the board shows up in the simulation of the board itself.

VENDOR MODELS. `models:` names SPICE libraries banked in datasheets/ (each with its
MANIFEST row and SHA-256); each is `.include`d by path, verbatim and unfilled, and its
hash is an input. TI's PSpice macromodels need `spiceinit: [set ngbehavior=psa]`,
which is written to the run's .spiceinit - inside .control is too late. A part with no
runnable vendor model is behavioural, built from its banked datasheet, and sims.yaml
says which figure each parameter comes from. `values: netlist:` may be a list, for a
sim that spans circuits; every component is also addressable by its own reference
({{R2}}, {{C-CM-IN+}}), so two parts of one row can sit at opposite tolerance ends.

SWEEPS. A sim's `sweep: {param: [v1, v2, ...]}` runs it once per value (and per
combination, for several), each as its own sim named `name[param=v]`, with its own
corners and asserts: a stability sim sweeps the page's load-capacitance range this way.

MEASURES ON WAVEFORMS (`post:`, over files the deck writes with `wrdata <name>.dat`):
  phase_margin(w['tdb'], w['tph'])  the loop's phase margin in degrees, the least at
      any 0 dB crossing of |T|; `tdb` is 20log|T| and `tph` its phase in degrees, of
      T = -V(return)/V(injected). THE STATED BREAK, one of two, and the deck says
      which. (a) The loop is opened at a high-impedance node - an op-amp input - by a
      1 GH inductor that carries the DC
      operating point, and the AC test signal enters through a 1 GF capacitor, so the
      feedback network stays loaded by the input it drives and nothing else. With a
      vendor macromodel the deck needs `.options rshunt=1e10` (10 Gohm per node) for
      the solver to find that operating point: without it TI's OPA2197 model found none
      at some corners, and ngspice's fallback "transient op" reported a false one (VS at
      0.55 V), which is why a run that needed it is refused. (b) VOLTAGE INJECTION, a
      series AC source between the feedback node and the op-amp input, where (a) finds
      no operating point: the deck must show the network's impedance at that node is far
      below the input's at every frequency that matters. It agreed with (a) within 0.5
      degree on the reference buffer as netlisted, and failed there on the bare
      follower, where 10 kohm of feedback against the model's input capacitance broke
      its assumption above 1 MHz (|T| climbed back to +33 dB at 100 MHz, 2026-09-30).
  crossover(w['tdb'])        the frequency of the first 0 dB crossing of |T|
  overshoot(w['v'], t0, t1)  percent, of a step at t0: the largest excursion past the
      final value (the mean of the last 5 % before t1) over the step's size
  rebound(w['v'], t0, t1)    percent, of a load step on a regulated node: the swing
      back through the final value after the first excursion, over that excursion
  settling(w['v'], t0, t1, band)  seconds from t0 until v stays within +-band of final
  at(w['x'], x0)             a waveform's value at x0, interpolated (a CMRR in dB at
      50 Hz, say)
  peak(w['v'], t0, t1) / trough(...)  the largest / smallest value in a window
  argpeak(w['v'], t0, t1)    where in the window the largest value is (an impedance
      peak's frequency)
  cross(w['v'], level, t0)   the first time after t0 that v crosses level (either way)
A SIMULATED PHASE MARGIN IS A SCREEN WITH A +-10 DEGREE BAR, not a spec: a vendor
macromodel runs optimistic against its own tabulated figures. Assert against it so.
"""
import glob
import hashlib
import itertools
import math
import os
import re
import subprocess
import sys
import tempfile

import yaml

ROOT = os.path.dirname(os.path.dirname(os.path.abspath(__file__)))
FIGURES = os.path.join(ROOT, "config", "figures.yaml")
SI = {"f": 1e-15, "p": 1e-12, "n": 1e-9, "u": 1e-6, "µ": 1e-6, "m": 1e-3, "": 1.0,
      "k": 1e3, "K": 1e3, "M": 1e6, "meg": 1e6, "G": 1e9}


# ------------------------------------------------------------------ values

def part_value(text):
    """A part's value as a number: '2k2 1%' -> 2200, '47nF' -> 47e-9, '100R 1%' -> 100,
    '10uF DNP' -> 10e-6. The tolerance ('1%') is separate: part_tol()."""
    t = text.strip().split()[0]
    m = re.fullmatch(r"(\d+)([pnuµmkKMGR])(\d+)", t)          # 2k2, 4R7
    if m:
        mult = 1.0 if m.group(2) == "R" else SI[m.group(2)]
        return float(f"{m.group(1)}.{m.group(3)}") * mult
    m = re.fullmatch(r"(\d+(?:\.\d+)?)(meg|[pnuµmkKMG])?(F|R|Ω|ohm|H)?", t)
    if not m:
        raise ValueError(f"cannot read a value from {text!r}")
    return float(m.group(1)) * SI[m.group(2) or ""]


def part_tol(text):
    m = re.search(r"(\d+(?:\.\d+)?)\s*%", text)
    return float(m.group(1)) / 100 if m else None


def figure_value(text):
    """A register figure's leading number in SI: '138.7 us' -> 1.387e-4, '1.43 mA per...' -> 1.43e-3."""
    m = re.match(r"\s*(-?\d+(?:\.\d+)?)\s*(meg|[pnuµmkMG])?\s*(s|us|µs|ms|ns|A|mA|uA|V|mV|Hz|kHz|MHz|ohm|Ω|F)?", text)
    if not m:
        raise ValueError(f"no number in {text!r}")
    v = float(m.group(1))
    unit = m.group(3) or ""
    pre = m.group(2) or ""
    if unit in ("us", "µs", "ms", "ns", "mA", "uA", "mV", "kHz", "MHz"):
        pre, unit = unit[0].replace("µ", "u"), unit[1:]
    return v * SI[pre]


def figures():
    f = yaml.safe_load(open(FIGURES))
    items = f["figures"] if isinstance(f, dict) and "figures" in f else f
    return {it["id"]: it for it in items}


def inc_path(simdir, inc):
    """An include beside the sims.yaml, or a banked model by its repo path (datasheets/...)."""
    here = os.path.join(simdir, inc)
    return here if os.path.exists(here) else os.path.join(ROOT, inc)


def spice_num(v):
    return f"{v:.6g}"


# ------------------------------------------------------------------ the sims

def sha(path):
    return hashlib.sha256(open(path, "rb").read()).hexdigest()[:16]


def load(simdir):
    """A sims.yaml. `params_from:` names other sims.yaml files whose params: and derived:
    this one takes (its own override them), so a model parameter - a threshold ratio, an
    input capacitance - is stated once, where the circuit it belongs to is simulated."""
    spec = yaml.safe_load(open(os.path.join(simdir, "sims.yaml")))
    spec["_dir"] = simdir
    params, derived = {}, {}
    for src in spec.get("params_from", []):
        other = yaml.safe_load(open(os.path.join(ROOT, src)))
        params.update(other.get("params") or {})
        derived.update(other.get("derived") or {})
    params.update(spec.get("params") or {})
    derived.update(spec.get("derived") or {})
    spec["params"], spec["derived"] = params, derived
    return spec


def bom_value(row):
    """A row's Value from hardware/bom.csv (generated from the fragments): for parts on
    another board, which this circuit's netlist does not carry (R-CHAIN-SER)."""
    import csv
    for r in csv.reader(open(os.path.join(ROOT, "hardware", "bom.csv"), newline="")):
        if r and r[0] == row:
            return r[2]
    raise SystemExit(f"sim: `values: bom:` names {row!r}, which hardware/bom.csv has no row for")


def drc_value(rule):
    """A number the body CAD prints in mechanical/drc.echo, by its rule's name: the
    first number after the name (a derived length, say), so it is cited, not restated."""
    for line in open(os.path.join(ROOT, "mechanical", "drc.echo")):
        if f'"{rule}"' in line:
            m = re.search(re.escape(f'"{rule}"') + r",\s*\[?\s*(-?[\d.]+(?:e[-+]?\d+)?)", line)
            if m:
                return float(m.group(1))
    raise SystemExit(f"sim: mechanical/drc.echo has no numeric rule {rule!r}")


def param_value(p):
    v = p["value"]
    if isinstance(v, dict) and "drc" in v:
        return drc_value(v["drc"]) * float(v.get("scale", 1))
    if isinstance(v, dict) and "fig" in v:
        # a register figure, cited by id: its leading number in SI (hashed as an input)
        figs = figures()
        if v["fig"] not in figs:
            raise SystemExit(f"sim: a param cites figure {v['fig']!r}, which is not in config/figures.yaml")
        return figure_value(str(figs[v["fig"]]["value"])) * float(v.get("scale", 1))
    try:
        return float(v)
    except (TypeError, ValueError):
        return part_value(str(v))


def netlists(spec):
    n = spec["values"]["netlist"]
    return [n] if isinstance(n, str) else list(n)


def netlist_parts(spec):
    """{row: {'value': number, 'tol': fraction or None, 'text': ...}} from the circuit's netlist.yaml
    (a circuit's components are keyed by row) or a board's (keyed by reference, with `of:`).
    Several netlists merge: rows are unique across the corpus. Every component is also
    keyed by its own reference where that differs from its row, so a deck can put two
    parts of one row at opposite ends of their tolerance ({{R2}}, {{R3}})."""
    out, docs = {}, []
    for path in netlists(spec):
        doc = yaml.safe_load(open(os.path.join(ROOT, path)))
        docs.append(doc)
        for ref, c in doc["components"].items():
            row = c.get("of", ref)
            if "value" not in c:
                continue                      # a row with no value yet (R-ILIM: "from E6")
            try:
                v = part_value(str(c["value"]))
            except ValueError:
                continue
            entry = {"value": v, "tol": part_tol(str(c["value"])), "text": str(c["value"])}
            out.setdefault(row, entry)
            if ref != row:
                out.setdefault(ref, dict(entry))
    for row in spec["values"].get("bom", []):
        text = bom_value(row)
        out[row] = {"value": part_value(text), "tol": part_tol(text), "text": text}
    # counts by row, for derived values: v['n:SW1-n']
    from collections import Counter
    doc = docs[0] if len(docs) == 1 else {"components": {f"{i}:{r}": c for i, d in enumerate(docs)
                                                         for r, c in d["components"].items()}}
    for row, k in Counter(c.get("of", r.split(":", 1)[-1]) for r, c in doc["components"].items()).items():
        out.setdefault(f"n:{row}", {"value": float(k), "tol": None, "text": str(k)})
    return out, doc


def inputs_of(spec):
    """Every file the results depend on, with its hash: this tool, sims.yaml, the decks, the
    netlist and anything generated from; and the value of every figure the sims cite."""
    d = spec["_dir"]
    files = [os.path.abspath(__file__), os.path.join(d, "sims.yaml")] + \
            [os.path.join(ROOT, n) for n in netlists(spec)]
    for s in spec["sims"]:
        if s.get("deck") and os.path.join(d, s["deck"]) not in files:
            files.append(os.path.join(d, s["deck"]))
    for inc in spec.get("include", []):
        files.append(inc_path(d, inc))
    for m in spec.get("models", []):
        files.append(os.path.join(ROOT, m))
    for src in spec.get("params_from", []):
        files.append(os.path.join(ROOT, src))
    h = {os.path.relpath(f, ROOT): sha(f) for f in files}
    figs = figures()
    text = "".join(open(f).read() for f in files if f.endswith(".yaml") and "sims" in os.path.basename(f))
    cited = sorted(set(re.findall(r"fig\['([^']+)'\]", text)))
    for row in spec["values"].get("bom", []):
        h[f"bom:{row}"] = bom_value(row)
    for name, p in (spec.get("params") or {}).items():
        if isinstance(p.get("value"), dict) and "drc" in p["value"]:
            h[f"drc:{p['value']['drc']}"] = str(drc_value(p["value"]["drc"]))
        if isinstance(p.get("value"), dict) and "fig" in p["value"]:
            cited.append(p["value"]["fig"])
    for fid in cited:
        if fid not in figs:
            raise SystemExit(f"sim: {os.path.relpath(d, ROOT)}/sims.yaml cites figure {fid!r}, which is not in config/figures.yaml")
        h[f"figure:{fid}"] = str(figs[fid]["value"])
    return h


def corners(spec, parts, only=None, tols=None):
    """[(name, {param: value})]: the nominal, then every combination of the range ends.
    `only`, a sim's own `vary:` list, limits the corners to the parameters that move it;
    `tols`, a sim's own `tol:` map, replaces a parameter's range for that sim alone (a
    what-if at a wider tolerance than the part is bought at)."""
    nominal, ranges = {}, {}
    for name, p in (spec.get("params") or {}).items():
        nominal[name] = param_value(p)
    vary = {k: dict(v) for k, v in (spec.get("vary") or {}).items()}
    for name, t in (tols or {}).items():
        vary.setdefault(name, {})["tol"] = t
    for name, v in vary.items():
        if only is not None and name not in only:
            continue
        if name in parts:
            base = parts[name]["value"]
        else:
            base = nominal[name]
        tol = v["tol"]
        if tol == "from-value":
            t = parts[name]["tol"]
            if t is None:
                raise SystemExit(f"sim: {name}'s value {parts[name]['text']!r} states no tolerance; give `tol:` a range")
            tol = [-t, t]
        ranges[name] = (base * (1 + tol[0]), base * (1 + tol[1]))
        nominal[name] = base
    for row, p in parts.items():
        nominal.setdefault(row, p["value"])
    out = [("nominal", dict(nominal))]
    names = sorted(ranges)
    for ends in (itertools.product((0, 1), repeat=len(names)) if names else ()):
        c = dict(nominal)
        label = []
        for n, e in zip(names, ends):
            c[n] = ranges[n][e]
            label.append(f"{n}{'-' if e == 0 else '+'}")
        out.append((" ".join(label), c))
    return out


def derive(spec, values):
    """`derived:` entries, in order: python expressions over the values so far (math allowed)."""
    v = dict(values)
    for name, expr in (spec.get("derived") or {}).items():
        v[name] = eval(expr, {"__builtins__": {}, "math": math, "min": min, "max": max, "round": round}, {"v": v})
    return v


def fill(template, values):
    def sub(m):
        k = m.group(1).strip()
        if k not in values:
            raise SystemExit(f"sim: the deck asks for {{{{{k}}}}}, which is no part row, param or derived value")
        return spice_num(values[k])
    return re.sub(r"\{\{([^}]+)\}\}", sub, template)


def spice_net(name, table):
    if name not in table:
        table[name] = "n" + re.sub(r"[^A-Za-z0-9_]", "_", name.lstrip("/")) if name not in ("GND", "0") else "0"
    return table[name]


def board_deck(spec, doc, body):
    """A deck for the whole board from its board-netlist.yaml: every part by its BOM row
    (`parts:` gives the SPICE line for each row, with {ref}, {value}, {sheet} and each pin's
    net as {pin}), the nets the rest of the chain drives (`drive:`), and `body` (the
    analysis and measures, from the sim's own deck). Nets are named n<name>; the ground
    net (`ground:`) is node 0. The sim's deck names a net as <net:/KEY_LH1>, and a
    `drive:` line its own net as <net>."""
    table = {spec["ground"]: "0"}
    pinnet = {}
    for net, pins in doc["nets"].items():
        for p in pins:
            pinnet[p] = spice_net(net, table)
    lines = [f"* {spec['title']} - generated by tools/sim.py from {spec['values']['netlist']}", "*"]
    for ref, c in sorted(doc["components"].items()):
        tmpl = spec["parts"].get(c["of"])
        if tmpl is None:
            raise SystemExit(f"sim: {ref} is a {c['of']}, which `parts:` does not say how to simulate "
                             f"(give it a SPICE line, or \"\" to leave it out and say why)")
        if not tmpl:
            lines.append(f"* {ref} ({c['of']}) not simulated: see sims.yaml")
            continue
        # {row} is the part's value as a corner varies it: {{R-KEY-PU}}, filled per run
        fields = {"ref": ref, "value": c["value"], "sheet": c.get("sheet", ""), "row": "{{" + c["of"] + "}}"}
        for p in c["pins"]:
            fields[str(p)] = pinnet.get(f"{ref}.{p}", f"nc_{ref}_{p}")
        try:
            fields["value"] = spice_num(part_value(str(c["value"])))
        except ValueError:
            pass
        def field(m):
            if m.group(1) not in fields:
                raise SystemExit(f"sim: `parts:` {c['of']}'s line asks for {{{m.group(1)}}}, which {ref} does not have "
                                 f"(its pins: {', '.join(map(str, c['pins']))})")
            return fields[m.group(1)]
        lines.append(re.sub(r"(?<!\{)\{([^{}]+)\}(?!\})", field, tmpl))
    for net, tmpl in (spec.get("drive") or {}).items():
        if net not in table:
            raise SystemExit(f"sim: `drive:` names net {net!r}, which the board does not have")
        lines.append(tmpl.replace("<net>", table[net]))
    lines.append("*")
    lines.append("* nets: " + ", ".join(f"{k}={v}" for k, v in sorted(table.items())))

    def net(m):
        if m.group(1) not in table:
            raise SystemExit(f"sim: the deck names net {m.group(1)!r}, which the board does not have")
        return table[m.group(1)]
    return "\n".join(lines) + "\n" + re.sub(r"<net:([^>]+)>", net, body)


def backswing(wave, level, rising, t_from, t_to):
    """How far a waveform swings BACK after it first crosses `level` (searched from
    `t_from`), until `t_to`: on a
    rising edge the most it falls below its own running maximum, on a falling edge the
    most it rises above its running minimum. A Schmitt input double-clocks only if an
    edge swings back through its hysteresis after crossing its threshold, wherever in
    the datasheet's spread that threshold sits - so this, against the hysteresis's
    minimum, is the test; a fixed pair of threshold extremes is not (they overlap)."""
    t, v = wave
    started, run, worst = False, None, 0.0
    for ti, vi in zip(t, v):
        if ti < t_from:
            continue
        if ti > t_to:
            break
        if not started:
            started = (vi >= level) if rising else (vi <= level)
            run = vi
            continue
        run = max(run, vi) if rising else min(run, vi)
        worst = max(worst, (run - vi) if rising else (vi - run))
    return worst if started else float("inf")


def _interp(x0, x1, y0, y1, y):
    return x0 if y1 == y0 else x0 + (x1 - x0) * (y - y0) / (y1 - y0)


def _unwrap(ph):
    out, off = [], 0.0
    for i, p in enumerate(ph):
        if i:
            d = p + off - out[-1]
            while d > 180:
                off -= 360
                d -= 360
            while d < -180:
                off += 360
                d += 360
        out.append(p + off)
    return out


def crossings(wave, level=0.0):
    """Every x at which a waveform crosses `level`, interpolated (log-x for an AC sweep)."""
    x, y = wave
    out = []
    for i in range(1, len(x)):
        if (y[i - 1] - level) * (y[i] - level) < 0 or (y[i] == level and y[i - 1] != level):
            if x[i - 1] > 0 and x[i] > 0 and x[i] / x[i - 1] > 1.0001:
                lx = _interp(math.log10(x[i - 1]), math.log10(x[i]), y[i - 1], y[i], level)
                out.append(10 ** lx)
            else:
                out.append(_interp(x[i - 1], x[i], y[i - 1], y[i], level))
    return out


def at(wave, x0):
    """A waveform's value at x0, interpolated linearly between its samples."""
    x, y = wave
    for i in range(1, len(x)):
        if x[i - 1] <= x0 <= x[i]:
            return _interp(y[i - 1], y[i], x[i - 1], x[i], x0) if x[i] != x[i - 1] else y[i]
    raise SystemExit(f"sim: at({x0:g}) is outside the waveform ({x[0]:g} to {x[-1]:g})")


def crossover(tdb):
    c = crossings(tdb, 0.0)
    if not c:
        return float("inf")          # never crosses: refused as a measure, which is right
    return c[0]


def phase_margin(tdb, tph):
    """The least phase margin at any 0 dB crossing of |T|: 180 + the (unwrapped) phase of
    T = -V(return)/V(injected), in degrees. At DC T's phase is 0 for negative feedback."""
    ph = _unwrap(tph[1])
    fs = crossings(tdb, 0.0)
    if not fs:
        return float("inf")
    return min(180.0 + at((tph[0], ph), f) for f in fs)


def _final(wave, t1):
    t, v = wave
    t0 = t1 - 0.05 * (t1 - t[0])
    pts = [vi for ti, vi in zip(t, v) if t0 <= ti <= t1]
    return sum(pts) / len(pts)


def overshoot(wave, t0, t1):
    """Percent overshoot of a step at t0: the largest excursion past the final value (the
    mean of the last 5 % before t1), over the step's size (final less the value at t0)."""
    t, v = wave
    v0 = at(wave, t0)
    vf = _final(wave, t1)
    step = vf - v0
    if step == 0:
        return float("inf")
    win = [vi for ti, vi in zip(t, v) if t0 <= ti <= t1]
    ex = (max(win) - vf) if step > 0 else (vf - min(win))
    return max(0.0, ex) / abs(step) * 100.0


def settling(wave, t0, t1, band):
    """Seconds from t0 until the waveform stays within +-band of its final value."""
    t, v = wave
    vf = _final(wave, t1)
    last = t0
    for ti, vi in zip(t, v):
        if t0 <= ti <= t1 and abs(vi - vf) > band:
            last = ti
    return last - t0


def rebound(wave, t0, t1):
    """Percent, of a disturbance at t0 on a REGULATED node (a load step, whose final value
    is its initial one, so overshoot() divides by nothing): the largest swing past the final
    value on the far side of the first excursion, after that excursion's extreme, over the
    first excursion. A well-damped loop recovers without crossing; one with little phase
    margin rings through."""
    t, v = wave
    vf = _final(wave, t1)
    win = [(ti, vi) for ti, vi in zip(t, v) if t0 <= ti <= t1]
    lo = min(win, key=lambda x: x[1])
    hi = max(win, key=lambda x: x[1])
    first = lo if abs(lo[1] - vf) >= abs(hi[1] - vf) else hi
    ex = abs(first[1] - vf)
    if ex == 0:
        return 0.0
    after = [vi for ti, vi in win if ti >= first[0]]
    back = (max(after) - vf) if first is lo else (vf - min(after))
    return max(0.0, back) / ex * 100.0


def peak(wave, t0, t1):
    return max(vi for ti, vi in zip(*wave) if t0 <= ti <= t1)


def argpeak(wave, t0, t1):
    """Where a waveform peaks in a window: the frequency of an impedance peak, say."""
    return max(((ti, vi) for ti, vi in zip(*wave) if t0 <= ti <= t1), key=lambda x: x[1])[0]


def trough(wave, t0, t1):
    return min(vi for ti, vi in zip(*wave) if t0 <= ti <= t1)


def cross(wave, level, t0=0.0):
    """The first time at or after t0 that a waveform crosses `level`; inf if it never does."""
    t, v = wave
    c = [x for x in crossings((t, v), level) if x >= t0]
    return c[0] if c else float("inf")


POST = {"backswing": backswing, "phase_margin": phase_margin, "crossover": crossover,
        "overshoot": overshoot, "rebound": rebound, "settling": settling, "at": at, "peak": peak, "argpeak": argpeak,
        "trough": trough, "cross": cross, "math": math, "abs": abs, "min": min, "max": max}
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
